AndyMWK/OpticalSensingSystem/cppcheck_report.txt

Firmware/mock/nucleof030r8/ir_sensor_mock/Core/Src/modules/fsm.c:120:23: style: Variable 'ctx.state' is reassigned a value before the old one has been used. [redundantAssignment]
            ctx.state = STATE_STREAMING;
                      ^
Firmware/mock/nucleof030r8/ir_sensor_mock/Core/Src/modules/fsm.c:114:27: note: ctx.state is assigned
                ctx.state = STATE_STREAMING;
                          ^
Firmware/mock/nucleof030r8/ir_sensor_mock/Core/Src/modules/fsm.c:120:23: note: ctx.state is overwritten
            ctx.state = STATE_STREAMING;
                      ^
Firmware/mock/nucleof030r8/ir_sensor_mock/Core/Src/modules/fsm.c:120:23: style: Variable 'ctx.state' is reassigned a value before the old one has been used. [redundantAssignment]
            ctx.state = STATE_STREAMING;
                      ^
Firmware/mock/nucleof030r8/ir_sensor_mock/Core/Src/modules/fsm.c:116:27: note: ctx.state is assigned
                ctx.state = STATE_IDLE;
                          ^
Firmware/mock/nucleof030r8/ir_sensor_mock/Core/Src/modules/fsm.c:120:23: note: ctx.state is overwritten
            ctx.state = STATE_STREAMING;
                      ^
Firmware/mock/nucleof030r8/ir_sensor_mock/Core/Src/system_stm32f0xx.c:191:0: information: Skipping configuration 'HSE_VALUE' since the value of 'HSE_VALUE' is unknown. Use -D if you want to check it. You can use -U to skip it explicitly. [ConfigurationNotChecked]
      SystemCoreClock = HSE_VALUE;
^
Firmware/mock/nucleof030r8/ir_sensor_mock/Core/Src/system_stm32f0xx.c:203:0: information: Skipping configuration 'HSE_VALUE' since the value of 'HSE_VALUE' is unknown. Use -D if you want to check it. You can use -U to skip it explicitly. [ConfigurationNotChecked]
        SystemCoreClock = (HSE_VALUE/predivfactor) * pllmull;
^
Firmware/mock/nucleof030r8/ir_sensor_mock/Core/Src/system_stm32f0xx.c:188:0: information: Skipping configuration 'HSI_VALUE' since the value of 'HSI_VALUE' is unknown. Use -D if you want to check it. You can use -U to skip it explicitly. [ConfigurationNotChecked]
      SystemCoreClock = HSI_VALUE;
^
Firmware/mock/nucleof030r8/ir_sensor_mock/Core/Src/system_stm32f0xx.c:221:0: information: Skipping configuration 'HSI_VALUE' since the value of 'HSI_VALUE' is unknown. Use -D if you want to check it. You can use -U to skip it explicitly. [ConfigurationNotChecked]
        SystemCoreClock = (HSI_VALUE >> 1) * pllmull;
^
Firmware/mock/nucleof030r8/ir_sensor_mock/Core/Src/system_stm32f0xx.c:228:0: information: Skipping configuration 'HSI_VALUE' since the value of 'HSI_VALUE' is unknown. Use -D if you want to check it. You can use -U to skip it explicitly. [ConfigurationNotChecked]
      SystemCoreClock = HSI_VALUE;
^
Firmware/mock/nucleof030r8/ir_sensor_mock/Drivers/CMSIS/Core_A/Source/irq_ctrl_gic.c:132:12: style: The scope of the variable 'val' can be reduced. [variableScope]
  uint32_t val;
           ^
Firmware/mock/nucleof030r8/ir_sensor_mock/Drivers/CMSIS/Core_A/Source/irq_ctrl_gic.c:133:11: style: The scope of the variable 'cfg' can be reduced. [variableScope]
  uint8_t cfg;
          ^
Firmware/mock/nucleof030r8/ir_sensor_mock/Drivers/CMSIS/Core_A/Source/irq_ctrl_gic.c:134:11: style: The scope of the variable 'secure' can be reduced. [variableScope]
  uint8_t secure;
          ^
Firmware/mock/nucleof030r8/ir_sensor_mock/Drivers/CMSIS/Core_A/Source/irq_ctrl_gic.c:135:11: style: The scope of the variable 'cpu' can be reduced. [variableScope]
  uint8_t cpu;
          ^
Firmware/mock/nucleof030r8/ir_sensor_mock/Drivers/CMSIS/Core_A/Source/irq_ctrl_gic.c:203:12: style: The scope of the variable 'val' can be reduced. [variableScope]
  uint32_t val;
           ^
Firmware/mock/nucleof030r8/ir_sensor_mock/Drivers/CMSIS/Core_A/Source/irq_ctrl_gic.c:233:12: style: The scope of the variable 'prio' can be reduced. [variableScope]
  uint32_t prio;
           ^
Firmware/mock/nucleof030r8/ir_sensor_mock/Drivers/CMSIS/DSP/DSP_Lib_TestSuite/Common/JTest/src/jtest_cycle.c:0:0: information: Too many #ifdef configurations - cppcheck only checks 12 of 18 configurations. Use --force to check all configurations. [toomanyconfigs]

^
Firmware/mock/nucleof030r8/ir_sensor_mock/Drivers/CMSIS/DSP/DSP_Lib_TestSuite/Common/JTest/src/jtest_dump_str_segments.c:12:26: style: Variable 'memmove_idx' is assigned a value that is never used. [unreadVariable]
    uint32_t memmove_idx = 0;
                         ^
Firmware/mock/nucleof030r8/ir_sensor_mock/Drivers/CMSIS/DSP/DSP_Lib_TestSuite/Common/JTest/src/jtest_fw.c:0:0: information: Too many #ifdef configurations - cppcheck only checks 12 of 18 configurations. Use --force to check all configurations. [toomanyconfigs]

^
Firmware/mock/nucleof030r8/ir_sensor_mock/Drivers/CMSIS/DSP/DSP_Lib_TestSuite/Common/platform/ARMCC/Retarget.c:24:21: style: struct member '__FILE::handle' is never used. [unusedStructMember]
struct __FILE { int handle; /* Add whatever you need here */ };
                    ^
Firmware/mock/nucleof030r8/ir_sensor_mock/Drivers/CMSIS/DSP/DSP_Lib_TestSuite/Common/platform/GCC/Retarget.c:70:11: style: Condition 'c==0x0D' is always false [knownConditionTrueFalse]
    if (c == 0x0D) break;
          ^
Firmware/mock/nucleof030r8/ir_sensor_mock/Drivers/CMSIS/DSP/DSP_Lib_TestSuite/Common/platform/GCC/Retarget.c:69:20: note: Assignment 'c=SER_GetChar()', assigned value is -1
    c = SER_GetChar();
                   ^
Firmware/mock/nucleof030r8/ir_sensor_mock/Drivers/CMSIS/DSP/DSP_Lib_TestSuite/Common/platform/GCC/Retarget.c:70:11: note: Condition 'c==0x0D' is always false
    if (c == 0x0D) break;
          ^
Firmware/mock/nucleof030r8/ir_sensor_mock/Drivers/CMSIS/DSP/DSP_Lib_TestSuite/Common/platform/GCC/Retarget.c:64:8: style: The scope of the variable 'c' can be reduced. [variableScope]
  char c;
       ^
Firmware/mock/nucleof030r8/ir_sensor_mock/Drivers/CMSIS/DSP/DSP_Lib_TestSuite/Common/platform/GCC/Retarget.c:97:21: error: Comparing pointers that point to different objects [comparePointers]
  if ((heap + incr) > (char *)&__HeapLimit)
                    ^
Firmware/mock/nucleof030r8/ir_sensor_mock/Drivers/CMSIS/DSP/DSP_Lib_TestSuite/Common/platform/GCC/Retarget.c:32:13: note: Variable declared here.
extern int  __HeapBase;
            ^
Firmware/mock/nucleof030r8/ir_sensor_mock/Drivers/CMSIS/DSP/DSP_Lib_TestSuite/Common/platform/GCC/Retarget.c:92:20: note: Address of variable taken here.
    heap = (char *)&__HeapBase;
                   ^
Firmware/mock/nucleof030r8/ir_sensor_mock/Drivers/CMSIS/DSP/DSP_Lib_TestSuite/Common/platform/GCC/Retarget.c:33:13: note: Variable declared here.
extern int  __HeapLimit;
            ^
Firmware/mock/nucleof030r8/ir_sensor_mock/Drivers/CMSIS/DSP/DSP_Lib_TestSuite/Common/platform/GCC/Retarget.c:97:31: note: Address of variable taken here.
  if ((heap + incr) > (char *)&__HeapLimit)
                              ^
Firmware/mock/nucleof030r8/ir_sensor_mock/Drivers/CMSIS/DSP/DSP_Lib_TestSuite/Common/platform/GCC/Retarget.c:97:21: note: Comparing pointers that point to different objects
  if ((heap + incr) > (char *)&__HeapLimit)
                    ^
Firmware/mock/nucleof030r8/ir_sensor_mock/Drivers/CMSIS/DSP/DSP_Lib_TestSuite/Common/platform/system_generic.c:0:0: information: Too many #ifdef configurations - cppcheck only checks 12 of 23 configurations. Use --force to check all configurations. [toomanyconfigs]

^
Firmware/mock/nucleof030r8/ir_sensor_mock/Drivers/CMSIS/DSP/DSP_Lib_TestSuite/Common/src/controller_tests/pid_tests.c:63:1: error: There is an unknown macro here somewhere. Configuration is required. If JTEST_COUNT_CYCLES is a macro then please configure it. [unknownMacro]
ARM_PID_TEST(f32,float32_t);
^
Firmware/mock/nucleof030r8/ir_sensor_mock/Drivers/CMSIS/DSP/DSP_Lib_TestSuite/Common/src/controller_tests/sin_cos_tests.c:88:10: error: There is an unknown macro here somewhere. Configuration is required. If ; is a macro then please configure it. [unknownMacro]
        );
         ^
Firmware/mock/nucleof030r8/ir_sensor_mock/Drivers/CMSIS/DSP/DSP_Lib_TestSuite/Common/src/filtering_tests/biquad_tests.c:135:59: error: There is an unknown macro here somewhere. Configuration is required. If ; is a macro then please configure it. [unknownMacro]
                     (void *) filtering_pState, postShift);
                                                          ^
Firmware/mock/nucleof030r8/ir_sensor_mock/Drivers/CMSIS/DSP/DSP_Lib_TestSuite/Common/src/filtering_tests/conv_tests.c:418:1: error: There is an unknown macro here somewhere. Configuration is required. If ; is a macro then please configure it. [unknownMacro]
CONV_DEFINE_TEST(conv          , f32, float32_t, CONV_TEST_TEMPLATE);
^
Firmware/mock/nucleof030r8/ir_sensor_mock/Drivers/CMSIS/DSP/DSP_Lib_TestSuite/Common/src/filtering_tests/correlate_tests.c:270:1: error: There is an unknown macro here somewhere. Configuration is required. If ; is a macro then please configure it. [unknownMacro]
CORRELATE_DEFINE_TEST(correlate          , f32, float32_t, CORRELATE_TEST_TEMPLATE);
^
Firmware/mock/nucleof030r8/ir_sensor_mock/Drivers/CMSIS/DSP/DSP_Lib_TestSuite/Common/src/filtering_tests/fir_tests.c:342:1: error: There is an unknown macro here somewhere. Configuration is required. If ; is a macro then please configure it. [unknownMacro]
FIR_DEFINE_TEST(f32,,float32_t);
^
Firmware/mock/nucleof030r8/ir_sensor_mock/Drivers/CMSIS/DSP/DSP_Lib_TestSuite/Common/src/filtering_tests/iir_tests.c:60:1: error: There is an unknown macro here somewhere. Configuration is required. If ; is a macro then please configure it. [unknownMacro]
IIR_DEFINE_TEST(f32, float32_t);
^
Firmware/mock/nucleof030r8/ir_sensor_mock/Drivers/CMSIS/DSP/DSP_Lib_TestSuite/Common/src/filtering_tests/lms_tests.c:195:1: error: There is an unknown macro here somewhere. Configuration is required. If ; is a macro then please configure it. [unknownMacro]
LMS_DEFINE_TEST(f32,,float32_t, mu_f32);
^
Firmware/mock/nucleof030r8/ir_sensor_mock/Drivers/CMSIS/DSP/DSP_Lib_TestSuite/Common/src/math_helper.c:62:16: portability: Casting from float * to signed int * is not portable due to different binary data representations on different platforms. [invalidPointerCast]
      test =   (int *)(&pRef[i]);
               ^
Firmware/mock/nucleof030r8/ir_sensor_mock/Drivers/CMSIS/DSP/DSP_Lib_TestSuite/Common/src/math_helper.c:71:16: portability: Casting from float * to signed int * is not portable due to different binary data representations on different platforms. [invalidPointerCast]
      test =   (int *)(&pTest[i]);
               ^
Firmware/mock/nucleof030r8/ir_sensor_mock/Drivers/CMSIS/DSP/DSP_Lib_TestSuite/Common/src/math_helper.c:83:14: portability: Casting from float * to signed int * is not portable due to different binary data representations on different platforms. [invalidPointerCast]
    test =   (int *)(&EnergyError);
             ^
Firmware/mock/nucleof030r8/ir_sensor_mock/Drivers/CMSIS/DSP/DSP_Lib_TestSuite/Common/src/math_helper.c:111:16: portability: Casting from double * to signed int * is not portable due to different binary data representations on different platforms. [invalidPointerCast]
      test =   (int *)(&pRef[i]);
               ^
Firmware/mock/nucleof030r8/ir_sensor_mock/Drivers/CMSIS/DSP/DSP_Lib_TestSuite/Common/src/math_helper.c:120:16: portability: Casting from double * to signed int * is not portable due to different binary data representations on different platforms. [invalidPointerCast]
      test =   (int *)(&pTest[i]);
               ^
Firmware/mock/nucleof030r8/ir_sensor_mock/Drivers/CMSIS/DSP/DSP_Lib_TestSuite/Common/src/math_helper.c:132:14: portability: Casting from double * to signed int * is not portable due to different binary data representations on different platforms. [invalidPointerCast]
    test =   (int *)(&EnergyError);
             ^
Firmware/mock/nucleof030r8/ir_sensor_mock/Drivers/CMSIS/DSP/DSP_Lib_TestSuite/Common/src/math_helper.c:204:11: style: The scope of the variable 'diff' can be reduced. [variableScope]
  int32_t diff, diffCrnt = 0;
          ^
Firmware/mock/nucleof030r8/ir_sensor_mock/Drivers/CMSIS/DSP/DSP_Lib_TestSuite/Common/src/math_helper.c:204:17: style: The scope of the variable 'diffCrnt' can be reduced. [variableScope]
  int32_t diff, diffCrnt = 0;
                ^
Firmware/mock/nucleof030r8/ir_sensor_mock/Drivers/CMSIS/DSP/DSP_Lib_TestSuite/Common/src/math_helper.c:232:11: style: The scope of the variable 'diff' can be reduced. [variableScope]
  int32_t diff, diffCrnt = 0;
          ^
Firmware/mock/nucleof030r8/ir_sensor_mock/Drivers/CMSIS/DSP/DSP_Lib_TestSuite/Common/src/math_helper.c:232:17: style: The scope of the variable 'diffCrnt' can be reduced. [variableScope]
  int32_t diff, diffCrnt = 0;
                ^
Firmware/mock/nucleof030r8/ir_sensor_mock/Drivers/CMSIS/DSP/DSP_Lib_TestSuite/Common/src/math_helper.c:204:26: style: Variable 'diffCrnt' is assigned a value that is never used. [unreadVariable]
  int32_t diff, diffCrnt = 0;
                         ^
Firmware/mock/nucleof030r8/ir_sensor_mock/Drivers/CMSIS/DSP/DSP_Lib_TestSuite/Common/src/math_helper.c:232:26: style: Variable 'diffCrnt' is assigned a value that is never used. [unreadVariable]
  int32_t diff, diffCrnt = 0;
                         ^
Firmware/mock/nucleof030r8/ir_sensor_mock/Drivers/CMSIS/DSP/DSP_Lib_TestSuite/Common/src/matrix_tests/mat_inverse_tests.c:17:40: error: There is an unknown macro here somewhere. Configuration is required. If ; is a macro then please configure it. [unknownMacro]
                 (int)mat_ptr->numCols);
                                       ^
Firmware/mock/nucleof030r8/ir_sensor_mock/Drivers/CMSIS/DSP/DSP_Lib_TestSuite/Common/src/matrix_tests/mat_scale_tests.c:57:79: error: There is an unknown macro here somewhere. Configuration is required. If ; is a macro then please configure it. [unknownMacro]
        MATRIX_TEST_CONFIG_SAMESIZE_OUTPUT(arm_matrix_instance_f32 *, mat_ptr);
                                                                              ^
Firmware/mock/nucleof030r8/ir_sensor_mock/Drivers/CMSIS/DSP/DSP_Lib_TestSuite/Common/src/transform_tests/cfft_family_tests.c:154:1: error: There is an unknown macro here somewhere. Configuration is required. If ; is a macro then please configure it. [unknownMacro]
CFFT_FAMILY_DEFINE_ALL_TESTS(forward, 0U);
^
Firmware/mock/nucleof030r8/ir_sensor_mock/Drivers/CMSIS/DSP/DSP_Lib_TestSuite/Common/src/transform_tests/cfft_tests.c:102:5: error: There is an unknown macro here somewhere. Configuration is required. If ; is a macro then please configure it. [unknownMacro]
    CFFT_TEST_BODY((uint8_t) 0, f32, float32_t);
    ^
Firmware/mock/nucleof030r8/ir_sensor_mock/Drivers/CMSIS/DSP/DSP_Lib_TestSuite/Common/src/transform_tests/dct4_tests.c:184:1: error: There is an unknown macro here somewhere. Configuration is required. If ; is a macro then please configure it. [unknownMacro]
DCT4_DEFINE_TEST(f32, float32_t);
^
Firmware/mock/nucleof030r8/ir_sensor_mock/Drivers/CMSIS/DSP/DSP_Lib_TestSuite/Common/src/transform_tests/rfft_fast_tests.c:64:1: error: There is an unknown macro here somewhere. Configuration is required. If ; is a macro then please configure it. [unknownMacro]
RFFT_FAST_DEFINE_TEST(forward, 0U);
^
Firmware/mock/nucleof030r8/ir_sensor_mock/Drivers/CMSIS/DSP/DSP_Lib_TestSuite/Common/src/transform_tests/rfft_tests.c:77:1: error: There is an unknown macro here somewhere. Configuration is required. If ; is a macro then please configure it. [unknownMacro]
RFFT_DEFINE_TEST(q31, forward, 0U, TYPE_FROM_ABBREV(q31), TYPE_FROM_ABBREV(q31));
^
Firmware/mock/nucleof030r8/ir_sensor_mock/Drivers/CMSIS/DSP/DSP_Lib_TestSuite/RefLibs/src/FilteringFunctions/biquad.c:17:13: style: The scope of the variable 'sample' can be reduced. [variableScope]
   uint32_t sample, stage = S->numStages;         /*  loop counters             */
            ^
Firmware/mock/nucleof030r8/ir_sensor_mock/Drivers/CMSIS/DSP/DSP_Lib_TestSuite/RefLibs/src/FilteringFunctions/biquad.c:87:14: style: The scope of the variable 'sample' can be reduced. [variableScope]
    uint32_t sample, stage = S->numStages;         /*  loop counters             */
             ^
Firmware/mock/nucleof030r8/ir_sensor_mock/Drivers/CMSIS/DSP/DSP_Lib_TestSuite/RefLibs/src/FilteringFunctions/biquad.c:166:13: style: The scope of the variable 'sample' can be reduced. [variableScope]
   uint32_t sample, stage = S->numStages;         /*  loop counters             */
            ^
Firmware/mock/nucleof030r8/ir_sensor_mock/Drivers/CMSIS/DSP/DSP_Lib_TestSuite/RefLibs/src/FilteringFunctions/biquad.c:235:12: style: The scope of the variable 'sample' can be reduced. [variableScope]
  uint32_t sample, stage = S->numStages;         /*  loop counters             */
           ^
Firmware/mock/nucleof030r8/ir_sensor_mock/Drivers/CMSIS/DSP/DSP_Lib_TestSuite/RefLibs/src/FilteringFunctions/biquad.c:319:12: style: The scope of the variable 'sample' can be reduced. [variableScope]
  uint32_t sample, stage = S->numStages;         /*  loop counters                      */
           ^
Firmware/mock/nucleof030r8/ir_sensor_mock/Drivers/CMSIS/DSP/DSP_Lib_TestSuite/RefLibs/src/FilteringFunctions/biquad.c:408:12: style: The scope of the variable 'sample' can be reduced. [variableScope]
  uint32_t sample, stage = S->numStages;         /*  loop counters                 */
           ^
Firmware/mock/nucleof030r8/ir_sensor_mock/Drivers/CMSIS/DSP/DSP_Lib_TestSuite/RefLibs/src/FilteringFunctions/biquad.c:502:12: style: The scope of the variable 'sample' can be reduced. [variableScope]
  uint32_t sample, stage = S->numStages;         /*  loop counters                     */
           ^
Firmware/mock/nucleof030r8/ir_sensor_mock/Drivers/CMSIS/DSP/DSP_Lib_TestSuite/RefLibs/src/FilteringFunctions/biquad.c:580:12: style: The scope of the variable 'sample' can be reduced. [variableScope]
  uint32_t sample, stage = (uint32_t) S->numStages;   /*  Stage loop counter                          */
           ^
Firmware/mock/nucleof030r8/ir_sensor_mock/Drivers/CMSIS/DSP/DSP_Lib_TestSuite/RefLibs/src/FilteringFunctions/biquad.c:655:12: style: The scope of the variable 'sample' can be reduced. [variableScope]
  uint32_t sample, stage = (uint32_t) S->numStages;   /*  Stage loop counter                          */
           ^
Firmware/mock/nucleof030r8/ir_sensor_mock/Drivers/CMSIS/DSP/DSP_Lib_TestSuite/RefLibs/src/FilteringFunctions/fir_interpolate.c:14:12: style: The scope of the variable 'i' can be reduced. [variableScope]
  uint32_t i, blkCnt;                            /* Loop counters */
           ^
Firmware/mock/nucleof030r8/ir_sensor_mock/Drivers/CMSIS/DSP/DSP_Lib_TestSuite/RefLibs/src/FilteringFunctions/fir_interpolate.c:109:12: style: The scope of the variable 'i' can be reduced. [variableScope]
  uint32_t i, blkCnt;                            /* Loop counters */
           ^
Firmware/mock/nucleof030r8/ir_sensor_mock/Drivers/CMSIS/DSP/DSP_Lib_TestSuite/RefLibs/src/FilteringFunctions/fir_lattice.c:11:14: style: The scope of the variable 'px' can be reduced. [variableScope]
  float32_t *px;                                 /* temporary state pointer */
             ^
Firmware/mock/nucleof030r8/ir_sensor_mock/Drivers/CMSIS/DSP/DSP_Lib_TestSuite/RefLibs/src/FilteringFunctions/fir_lattice.c:12:14: style: The scope of the variable 'pk' can be reduced. [variableScope]
  float32_t *pk;                                 /* temporary coefficient pointer */
             ^
Firmware/mock/nucleof030r8/ir_sensor_mock/Drivers/CMSIS/DSP/DSP_Lib_TestSuite/RefLibs/src/FilteringFunctions/fir_lattice.c:15:20: style: The scope of the variable 'stageCnt' can be reduced. [variableScope]
  uint32_t blkCnt, stageCnt;                     /* temporary variables for counts */
                   ^
Firmware/mock/nucleof030r8/ir_sensor_mock/Drivers/CMSIS/DSP/DSP_Lib_TestSuite/RefLibs/src/FilteringFunctions/fir_lattice.c:87:10: style: The scope of the variable 'px' can be reduced. [variableScope]
  q31_t *px;                                     /* temporary state pointer */
         ^
Firmware/mock/nucleof030r8/ir_sensor_mock/Drivers/CMSIS/DSP/DSP_Lib_TestSuite/RefLibs/src/FilteringFunctions/fir_lattice.c:88:10: style: The scope of the variable 'pk' can be reduced. [variableScope]
  q31_t *pk;                                     /* temporary coefficient pointer */
         ^
Firmware/mock/nucleof030r8/ir_sensor_mock/Drivers/CMSIS/DSP/DSP_Lib_TestSuite/RefLibs/src/FilteringFunctions/fir_lattice.c:91:20: style: The scope of the variable 'stageCnt' can be reduced. [variableScope]
  uint32_t blkCnt, stageCnt;                     /* temporary variables for counts */
                   ^
Firmware/mock/nucleof030r8/ir_sensor_mock/Drivers/CMSIS/DSP/DSP_Lib_TestSuite/RefLibs/src/FilteringFunctions/fir_lattice.c:164:10: style: The scope of the variable 'px' can be reduced. [variableScope]
  q15_t *px;                                     /* temporary state pointer */
         ^
Firmware/mock/nucleof030r8/ir_sensor_mock/Drivers/CMSIS/DSP/DSP_Lib_TestSuite/RefLibs/src/FilteringFunctions/fir_lattice.c:165:10: style: The scope of the variable 'pk' can be reduced. [variableScope]
  q15_t *pk;                                     /* temporary coefficient pointer */
         ^
Firmware/mock/nucleof030r8/ir_sensor_mock/Drivers/CMSIS/DSP/DSP_Lib_TestSuite/RefLibs/src/FilteringFunctions/fir_lattice.c:168:20: style: The scope of the variable 'stageCnt' can be reduced. [variableScope]
  uint32_t blkCnt, stageCnt;                     /* temporary variables for counts */
                   ^
Firmware/mock/nucleof030r8/ir_sensor_mock/Drivers/CMSIS/DSP/DSP_Lib_TestSuite/RefLibs/src/FilteringFunctions/fir_sparse.c:303:10: style: Variable 'tapCnt' is reassigned a value before the old one has been used. [redundantAssignment]
  tapCnt = (uint32_t) numTaps - 1U;
         ^
Firmware/mock/nucleof030r8/ir_sensor_mock/Drivers/CMSIS/DSP/DSP_Lib_TestSuite/RefLibs/src/FilteringFunctions/fir_sparse.c:267:10: note: tapCnt is assigned
  tapCnt = numTaps;
         ^
Firmware/mock/nucleof030r8/ir_sensor_mock/Drivers/CMSIS/DSP/DSP_Lib_TestSuite/RefLibs/src/FilteringFunctions/fir_sparse.c:303:10: note: tapCnt is overwritten
  tapCnt = (uint32_t) numTaps - 1U;
         ^
Firmware/mock/nucleof030r8/ir_sensor_mock/Drivers/CMSIS/DSP/DSP_Lib_TestSuite/RefLibs/src/FilteringFunctions/fir_sparse.c:426:10: style: Variable 'tapCnt' is reassigned a value before the old one has been used. [redundantAssignment]
  tapCnt = (uint32_t) numTaps - 1U;
         ^
Firmware/mock/nucleof030r8/ir_sensor_mock/Drivers/CMSIS/DSP/DSP_Lib_TestSuite/RefLibs/src/FilteringFunctions/fir_sparse.c:389:10: note: tapCnt is assigned
  tapCnt = numTaps;
         ^
Firmware/mock/nucleof030r8/ir_sensor_mock/Drivers/CMSIS/DSP/DSP_Lib_TestSuite/RefLibs/src/FilteringFunctions/fir_sparse.c:426:10: note: tapCnt is overwritten
  tapCnt = (uint32_t) numTaps - 1U;
         ^
Firmware/mock/nucleof030r8/ir_sensor_mock/Drivers/CMSIS/DSP/DSP_Lib_TestSuite/RefLibs/src/FilteringFunctions/iir_lattice.c:12:14: style: The scope of the variable 'px1' can be reduced. [variableScope]
  float32_t *px1, *px2, *pk, *pv;                /* temporary pointers for state and coef */
             ^
Firmware/mock/nucleof030r8/ir_sensor_mock/Drivers/CMSIS/DSP/DSP_Lib_TestSuite/RefLibs/src/FilteringFunctions/iir_lattice.c:12:20: style: The scope of the variable 'px2' can be reduced. [variableScope]
  float32_t *px1, *px2, *pk, *pv;                /* temporary pointers for state and coef */
                   ^
Firmware/mock/nucleof030r8/ir_sensor_mock/Drivers/CMSIS/DSP/DSP_Lib_TestSuite/RefLibs/src/FilteringFunctions/iir_lattice.c:12:26: style: The scope of the variable 'pk' can be reduced. [variableScope]
  float32_t *px1, *px2, *pk, *pv;                /* temporary pointers for state and coef */
                         ^
Firmware/mock/nucleof030r8/ir_sensor_mock/Drivers/CMSIS/DSP/DSP_Lib_TestSuite/RefLibs/src/FilteringFunctions/iir_lattice.c:12:31: style: The scope of the variable 'pv' can be reduced. [variableScope]
  float32_t *px1, *px2, *pk, *pv;                /* temporary pointers for state and coef */
                              ^
Firmware/mock/nucleof030r8/ir_sensor_mock/Drivers/CMSIS/DSP/DSP_Lib_TestSuite/RefLibs/src/FilteringFunctions/iir_lattice.c:98:10: style: The scope of the variable 'px1' can be reduced. [variableScope]
  q31_t *px1, *px2, *pk, *pv;                    /* Temporary pointers for state and coef */
         ^
Firmware/mock/nucleof030r8/ir_sensor_mock/Drivers/CMSIS/DSP/DSP_Lib_TestSuite/RefLibs/src/FilteringFunctions/iir_lattice.c:98:16: style: The scope of the variable 'px2' can be reduced. [variableScope]
  q31_t *px1, *px2, *pk, *pv;                    /* Temporary pointers for state and coef */
               ^
Firmware/mock/nucleof030r8/ir_sensor_mock/Drivers/CMSIS/DSP/DSP_Lib_TestSuite/RefLibs/src/FilteringFunctions/iir_lattice.c:98:22: style: The scope of the variable 'pk' can be reduced. [variableScope]
  q31_t *px1, *px2, *pk, *pv;                    /* Temporary pointers for state and coef */
                     ^
Firmware/mock/nucleof030r8/ir_sensor_mock/Drivers/CMSIS/DSP/DSP_Lib_TestSuite/RefLibs/src/FilteringFunctions/iir_lattice.c:98:27: style: The scope of the variable 'pv' can be reduced. [variableScope]
  q31_t *px1, *px2, *pk, *pv;                    /* Temporary pointers for state and coef */
                          ^
Firmware/mock/nucleof030r8/ir_sensor_mock/Drivers/CMSIS/DSP/DSP_Lib_TestSuite/RefLibs/src/FilteringFunctions/iir_lattice.c:190:20: style: The scope of the variable 'tapCnt' can be reduced. [variableScope]
  uint32_t blkCnt, tapCnt;                       /* Temporary variables for counts */
                   ^
Firmware/mock/nucleof030r8/ir_sensor_mock/Drivers/CMSIS/DSP/DSP_Lib_TestSuite/RefLibs/src/FilteringFunctions/iir_lattice.c:191:10: style: The scope of the variable 'px1' can be reduced. [variableScope]
  q15_t *px1, *px2, *pk, *pv;                    /* temporary pointers for state and coef */
         ^
Firmware/mock/nucleof030r8/ir_sensor_mock/Drivers/CMSIS/DSP/DSP_Lib_TestSuite/RefLibs/src/FilteringFunctions/iir_lattice.c:191:16: style: The scope of the variable 'px2' can be reduced. [variableScope]
  q15_t *px1, *px2, *pk, *pv;                    /* temporary pointers for state and coef */
               ^
Firmware/mock/nucleof030r8/ir_sensor_mock/Drivers/CMSIS/DSP/DSP_Lib_TestSuite/RefLibs/src/FilteringFunctions/iir_lattice.c:191:22: style: The scope of the variable 'pk' can be reduced. [variableScope]
  q15_t *px1, *px2, *pk, *pv;                    /* temporary pointers for state and coef */
                     ^
Firmware/mock/nucleof030r8/ir_sensor_mock/Drivers/CMSIS/DSP/DSP_Lib_TestSuite/RefLibs/src/FilteringFunctions/iir_lattice.c:191:27: style: The scope of the variable 'pv' can be reduced. [variableScope]
  q15_t *px1, *px2, *pk, *pv;                    /* temporary pointers for state and coef */
                          ^
Firmware/mock/nucleof030r8/ir_sensor_mock/Drivers/CMSIS/DSP/DSP_Lib_TestSuite/RefLibs/src/FilteringFunctions/iir_lattice.c:95:33: style: Variable 'gcurr' is assigned a value that is never used. [unreadVariable]
  q31_t fcurr, fnext = 0, gcurr = 0, gnext;      /* Temporary variables for lattice stages */
                                ^
Firmware/mock/nucleof030r8/ir_sensor_mock/Drivers/CMSIS/DSP/DSP_Lib_TestSuite/RefLibs/src/FilteringFunctions/iir_lattice.c:187:33: style: Variable 'gcurr' is assigned a value that is never used. [unreadVariable]
  q31_t fcurr, fnext = 0, gcurr = 0, gnext;      /* Temporary variables for lattice stages */
                                ^
Firmware/mock/nucleof030r8/ir_sensor_mock/Drivers/CMSIS/DSP/DSP_Lib_TestSuite/RefLibs/src/FilteringFunctions/lms.c:173:10: style: The scope of the variable 'px' can be reduced. [variableScope]
  q31_t *px;                                     /* Temporary pointer for state */
         ^
Firmware/mock/nucleof030r8/ir_sensor_mock/Drivers/CMSIS/DSP/DSP_Lib_TestSuite/RefLibs/src/FilteringFunctions/lms.c:174:10: style: The scope of the variable 'pb' can be reduced. [variableScope]
  q31_t *pb;                                     /* Temporary pointer for coefficient buffer */
         ^
Firmware/mock/nucleof030r8/ir_sensor_mock/Drivers/CMSIS/DSP/DSP_Lib_TestSuite/RefLibs/src/FilteringFunctions/lms.c:287:10: style: The scope of the variable 'px' can be reduced. [variableScope]
  q31_t *px, *pb;                                /* Temporary pointers for state and coefficient buffers */
         ^
Firmware/mock/nucleof030r8/ir_sensor_mock/Drivers/CMSIS/DSP/DSP_Lib_TestSuite/RefLibs/src/FilteringFunctions/lms.c:287:15: style: The scope of the variable 'pb' can be reduced. [variableScope]
  q31_t *px, *pb;                                /* Temporary pointers for state and coefficient buffers */
              ^
Firmware/mock/nucleof030r8/ir_sensor_mock/Drivers/CMSIS/DSP/DSP_Lib_TestSuite/RefLibs/src/FilteringFunctions/lms.c:433:10: style: The scope of the variable 'px' can be reduced. [variableScope]
  q15_t *px;                                     /* Temporary pointer for state */
         ^
Firmware/mock/nucleof030r8/ir_sensor_mock/Drivers/CMSIS/DSP/DSP_Lib_TestSuite/RefLibs/src/FilteringFunctions/lms.c:434:10: style: The scope of the variable 'pb' can be reduced. [variableScope]
  q15_t *pb;                                     /* Temporary pointer for coefficient buffer */
         ^
Firmware/mock/nucleof030r8/ir_sensor_mock/Drivers/CMSIS/DSP/DSP_Lib_TestSuite/RefLibs/src/FilteringFunctions/lms.c:18:15: style: Variable 'w' is assigned a value that is never used. [unreadVariable]
  float32_t w = 0.0f;                            /* weight factor */
              ^
Firmware/mock/nucleof030r8/ir_sensor_mock/Drivers/CMSIS/DSP/DSP_Lib_TestSuite/RefLibs/src/FilteringFunctions/lms.c:20:5: style: Variable 'e' is assigned a value that is never used. [unreadVariable]
  e = 0.0f;
    ^
Firmware/mock/nucleof030r8/ir_sensor_mock/Drivers/CMSIS/DSP/DSP_Lib_TestSuite/RefLibs/src/FilteringFunctions/lms.c:21:5: style: Variable 'd' is assigned a value that is never used. [unreadVariable]
  d = 0.0f;
    ^
Firmware/mock/nucleof030r8/ir_sensor_mock/Drivers/CMSIS/DSP/DSP_Lib_TestSuite/RefLibs/src/FilteringFunctions/lms.c:93:5: style: Variable 'e' is assigned a value that is never used. [unreadVariable]
  e = 0.0f;
    ^
Firmware/mock/nucleof030r8/ir_sensor_mock/Drivers/CMSIS/DSP/DSP_Lib_TestSuite/RefLibs/src/FilteringFunctions/lms.c:94:5: style: Variable 'd' is assigned a value that is never used. [unreadVariable]
  d = 0.0f;
    ^
Firmware/mock/nucleof030r8/ir_sensor_mock/Drivers/CMSIS/DSP/DSP_Lib_TestSuite/RefLibs/src/FilteringFunctions/lms.c:95:5: style: Variable 'w' is assigned a value that is never used. [unreadVariable]
  w = 0.0f;
    ^
Firmware/mock/nucleof030r8/ir_sensor_mock/Drivers/CMSIS/DSP/DSP_Lib_TestSuite/RefLibs/src/FilteringFunctions/lms.c:177:11: style: Variable 'e' is assigned a value that is never used. [unreadVariable]
  q31_t e = 0;                                   /* error of data sample */
          ^
Firmware/mock/nucleof030r8/ir_sensor_mock/Drivers/CMSIS/DSP/DSP_Lib_TestSuite/RefLibs/src/FilteringFunctions/lms.c:293:11: style: Variable 'e' is assigned a value that is never used. [unreadVariable]
  q31_t e = 0, d = 0;                            /* error, reference data sample */
          ^
Firmware/mock/nucleof030r8/ir_sensor_mock/Drivers/CMSIS/DSP/DSP_Lib_TestSuite/RefLibs/src/FilteringFunctions/lms.c:293:18: style: Variable 'd' is assigned a value that is never used. [unreadVariable]
  q31_t e = 0, d = 0;                            /* error, reference data sample */
                 ^
Firmware/mock/nucleof030r8/ir_sensor_mock/Drivers/CMSIS/DSP/DSP_Lib_TestSuite/RefLibs/src/FilteringFunctions/lms.c:294:11: style: Variable 'w' is assigned a value that is never used. [unreadVariable]
  q31_t w = 0, in;                               /* weight factor and state */
          ^
Firmware/mock/nucleof030r8/ir_sensor_mock/Drivers/CMSIS/DSP/DSP_Lib_TestSuite/RefLibs/src/FilteringFunctions/lms.c:437:11: style: Variable 'e' is assigned a value that is never used. [unreadVariable]
  q15_t e = 0;                                   /* error of data sample */
          ^
Firmware/mock/nucleof030r8/ir_sensor_mock/Drivers/CMSIS/DSP/DSP_Lib_TestSuite/RefLibs/src/FilteringFunctions/lms.c:555:11: style: Variable 'e' is assigned a value that is never used. [unreadVariable]
  q15_t e = 0, d = 0;                            /* error, reference data sample */
          ^
Firmware/mock/nucleof030r8/ir_sensor_mock/Drivers/CMSIS/DSP/DSP_Lib_TestSuite/RefLibs/src/FilteringFunctions/lms.c:555:18: style: Variable 'd' is assigned a value that is never used. [unreadVariable]
  q15_t e = 0, d = 0;                            /* error, reference data sample */
                 ^
Firmware/mock/nucleof030r8/ir_sensor_mock/Drivers/CMSIS/DSP/DSP_Lib_TestSuite/RefLibs/src/FilteringFunctions/lms.c:556:11: style: Variable 'w' is assigned a value that is never used. [unreadVariable]
  q15_t w = 0, in;                               /* weight factor and state */
          ^
Firmware/mock/nucleof030r8/ir_sensor_mock/Drivers/CMSIS/DSP/DSP_Lib_TestSuite/RefLibs/src/HelperFunctions/mat_helper.c:6:8: style: The scope of the variable 'i' can be reduced. [variableScope]
   int i, j, m, n, c;
       ^
Firmware/mock/nucleof030r8/ir_sensor_mock/Drivers/CMSIS/DSP/DSP_Lib_TestSuite/RefLibs/src/HelperFunctions/mat_helper.c:6:11: style: The scope of the variable 'j' can be reduced. [variableScope]
   int i, j, m, n, c;
          ^
Firmware/mock/nucleof030r8/ir_sensor_mock/Drivers/CMSIS/DSP/DSP_Lib_TestSuite/RefLibs/src/HelperFunctions/mat_helper.c:6:14: style: The scope of the variable 'm' can be reduced. [variableScope]
   int i, j, m, n, c;
             ^
Firmware/mock/nucleof030r8/ir_sensor_mock/Drivers/CMSIS/DSP/DSP_Lib_TestSuite/RefLibs/src/HelperFunctions/mat_helper.c:6:17: style: The scope of the variable 'n' can be reduced. [variableScope]
   int i, j, m, n, c;
                ^
Firmware/mock/nucleof030r8/ir_sensor_mock/Drivers/CMSIS/DSP/DSP_Lib_TestSuite/RefLibs/src/HelperFunctions/mat_helper.c:6:20: style: The scope of the variable 'c' can be reduced. [variableScope]
   int i, j, m, n, c;
                   ^
Firmware/mock/nucleof030r8/ir_sensor_mock/Drivers/CMSIS/DSP/DSP_Lib_TestSuite/RefLibs/src/HelperFunctions/mat_helper.c:103:8: style: The scope of the variable 'i' can be reduced. [variableScope]
   int i, j, m, n, c;
       ^
Firmware/mock/nucleof030r8/ir_sensor_mock/Drivers/CMSIS/DSP/DSP_Lib_TestSuite/RefLibs/src/HelperFunctions/mat_helper.c:103:11: style: The scope of the variable 'j' can be reduced. [variableScope]
   int i, j, m, n, c;
          ^
Firmware/mock/nucleof030r8/ir_sensor_mock/Drivers/CMSIS/DSP/DSP_Lib_TestSuite/RefLibs/src/HelperFunctions/mat_helper.c:103:14: style: The scope of the variable 'm' can be reduced. [variableScope]
   int i, j, m, n, c;
             ^
Firmware/mock/nucleof030r8/ir_sensor_mock/Drivers/CMSIS/DSP/DSP_Lib_TestSuite/RefLibs/src/HelperFunctions/mat_helper.c:103:17: style: The scope of the variable 'n' can be reduced. [variableScope]
   int i, j, m, n, c;
                ^
Firmware/mock/nucleof030r8/ir_sensor_mock/Drivers/CMSIS/DSP/DSP_Lib_TestSuite/RefLibs/src/HelperFunctions/mat_helper.c:103:20: style: The scope of the variable 'c' can be reduced. [variableScope]
   int i, j, m, n, c;
                   ^
Firmware/mock/nucleof030r8/ir_sensor_mock/Drivers/CMSIS/DSP/DSP_Lib_TestSuite/RefLibs/src/HelperFunctions/ref_helper.c:9:18: style: The scope of the variable 'negMin' can be reduced. [variableScope]
 int32_t posMax, negMin;
                 ^
Firmware/mock/nucleof030r8/ir_sensor_mock/Drivers/CMSIS/DSP/DSP_Lib_TestSuite/RefLibs/src/StatisticsFunctions/rms.c:40:11: portability: Casting from float * to signed int * is not portable due to different binary data representations on different platforms. [invalidPointerCast]
  if (((*((int *)(&help_float))) & 0x7FC00000) == 0x7FC00000) {
          ^
Firmware/mock/nucleof030r8/ir_sensor_mock/Drivers/CMSIS/DSP/DSP_Lib_TestSuite/RefLibs/src/TransformFunctions/bitreversal.c:13:11: style: The scope of the variable 'a' can be reduced. [variableScope]
 uint32_t a,b,i,tmp;
          ^
Firmware/mock/nucleof030r8/ir_sensor_mock/Drivers/CMSIS/DSP/DSP_Lib_TestSuite/RefLibs/src/TransformFunctions/bitreversal.c:13:13: style: The scope of the variable 'b' can be reduced. [variableScope]
 uint32_t a,b,i,tmp;
            ^
Firmware/mock/nucleof030r8/ir_sensor_mock/Drivers/CMSIS/DSP/DSP_Lib_TestSuite/RefLibs/src/TransformFunctions/bitreversal.c:13:17: style: The scope of the variable 'tmp' can be reduced. [variableScope]
 uint32_t a,b,i,tmp;
                ^
Firmware/mock/nucleof030r8/ir_sensor_mock/Drivers/CMSIS/DSP/DSP_Lib_TestSuite/RefLibs/src/TransformFunctions/cfft.c:10:21: style: The scope of the variable 'istep' can be reduced. [variableScope]
 int n, mmax, m, j, istep, i;
                    ^
Firmware/mock/nucleof030r8/ir_sensor_mock/Drivers/CMSIS/DSP/DSP_Lib_TestSuite/RefLibs/src/TransformFunctions/rfft.c:61:13: style: The scope of the variable 'j' can be reduced. [variableScope]
 uint32_t i,j;
            ^
Firmware/mock/nucleof030r8/ir_sensor_mock/Drivers/CMSIS/DSP/Examples/ARM/arm_convolution_example/arm_convolution_example_f32.c:223:10: style: Variable 'status' is reassigned a value before the old one has been used. [redundantAssignment]
  status = arm_cfft_radix4_init_f32(cfft_instance_ptr, 64, 1, 1);
         ^
Firmware/mock/nucleof030r8/ir_sensor_mock/Drivers/CMSIS/DSP/Examples/ARM/arm_convolution_example/arm_convolution_example_f32.c:212:10: note: status is assigned
  status = arm_cfft_radix4_init_f32(cfft_instance_ptr, 64, 0, 1);
         ^
Firmware/mock/nucleof030r8/ir_sensor_mock/Drivers/CMSIS/DSP/Examples/ARM/arm_convolution_example/arm_convolution_example_f32.c:223:10: note: status is overwritten
  status = arm_cfft_radix4_init_f32(cfft_instance_ptr, 64, 1, 1);
         ^
Firmware/mock/nucleof030r8/ir_sensor_mock/Drivers/CMSIS/DSP/Examples/ARM/arm_convolution_example/math_helper.c:73:13: portability: Casting from float * to signed int * is not portable due to different binary data representations on different platforms. [invalidPointerCast]
   test =   (int *)(&pRef[i]);
            ^
Firmware/mock/nucleof030r8/ir_sensor_mock/Drivers/CMSIS/DSP/Examples/ARM/arm_convolution_example/math_helper.c:82:13: portability: Casting from float * to signed int * is not portable due to different binary data representations on different platforms. [invalidPointerCast]
   test =   (int *)(&pTest[i]);
            ^
Firmware/mock/nucleof030r8/ir_sensor_mock/Drivers/CMSIS/DSP/Examples/ARM/arm_convolution_example/math_helper.c:94:11: portability: Casting from float * to signed int * is not portable due to different binary data representations on different platforms. [invalidPointerCast]
 test =   (int *)(&EnergyError);
          ^
Firmware/mock/nucleof030r8/ir_sensor_mock/Drivers/CMSIS/DSP/Examples/ARM/arm_convolution_example/math_helper.c:169:11: style: The scope of the variable 'diff' can be reduced. [variableScope]
  int32_t diff, diffCrnt = 0;
          ^
Firmware/mock/nucleof030r8/ir_sensor_mock/Drivers/CMSIS/DSP/Examples/ARM/arm_convolution_example/math_helper.c:169:17: style: The scope of the variable 'diffCrnt' can be reduced. [variableScope]
  int32_t diff, diffCrnt = 0;
                ^
Firmware/mock/nucleof030r8/ir_sensor_mock/Drivers/CMSIS/DSP/Examples/ARM/arm_convolution_example/math_helper.c:197:11: style: The scope of the variable 'diff' can be reduced. [variableScope]
  int32_t diff, diffCrnt = 0;
          ^
Firmware/mock/nucleof030r8/ir_sensor_mock/Drivers/CMSIS/DSP/Examples/ARM/arm_convolution_example/math_helper.c:197:17: style: The scope of the variable 'diffCrnt' can be reduced. [variableScope]
  int32_t diff, diffCrnt = 0;
                ^
Firmware/mock/nucleof030r8/ir_sensor_mock/Drivers/CMSIS/DSP/Examples/ARM/arm_convolution_example/math_helper.c:311:33: style:inconclusive: Function 'arm_calc_2pow' argument 1 names different: declaration 'guard_bits' definition 'numShifts'. [funcArgNamesDifferent]
uint32_t arm_calc_2pow(uint32_t numShifts)
                                ^
Firmware/mock/nucleof030r8/ir_sensor_mock/Drivers/CMSIS/DSP/Examples/ARM/arm_convolution_example/math_helper.h:61:33: note: Function 'arm_calc_2pow' argument 1 names different: declaration 'guard_bits' definition 'numShifts'.
uint32_t arm_calc_2pow(uint32_t guard_bits);
                                ^
Firmware/mock/nucleof030r8/ir_sensor_mock/Drivers/CMSIS/DSP/Examples/ARM/arm_convolution_example/math_helper.c:311:33: note: Function 'arm_calc_2pow' argument 1 names different: declaration 'guard_bits' definition 'numShifts'.
uint32_t arm_calc_2pow(uint32_t numShifts)
                                ^
Firmware/mock/nucleof030r8/ir_sensor_mock/Drivers/CMSIS/DSP/Examples/ARM/arm_convolution_example/math_helper.c:169:26: style: Variable 'diffCrnt' is assigned a value that is never used. [unreadVariable]
  int32_t diff, diffCrnt = 0;
                         ^
Firmware/mock/nucleof030r8/ir_sensor_mock/Drivers/CMSIS/DSP/Examples/ARM/arm_convolution_example/math_helper.c:197:26: style: Variable 'diffCrnt' is assigned a value that is never used. [unreadVariable]
  int32_t diff, diffCrnt = 0;
                         ^
Firmware/mock/nucleof030r8/ir_sensor_mock/Drivers/CMSIS/DSP/Examples/ARM/arm_fir_example/math_helper.c:73:13: portability: Casting from float * to signed int * is not portable due to different binary data representations on different platforms. [invalidPointerCast]
   test =   (int *)(&pRef[i]);
            ^
Firmware/mock/nucleof030r8/ir_sensor_mock/Drivers/CMSIS/DSP/Examples/ARM/arm_fir_example/math_helper.c:82:13: portability: Casting from float * to signed int * is not portable due to different binary data representations on different platforms. [invalidPointerCast]
   test =   (int *)(&pTest[i]);
            ^
Firmware/mock/nucleof030r8/ir_sensor_mock/Drivers/CMSIS/DSP/Examples/ARM/arm_fir_example/math_helper.c:94:11: portability: Casting from float * to signed int * is not portable due to different binary data representations on different platforms. [invalidPointerCast]
 test =   (int *)(&EnergyError);
          ^
Firmware/mock/nucleof030r8/ir_sensor_mock/Drivers/CMSIS/DSP/Examples/ARM/arm_fir_example/math_helper.c:169:11: style: The scope of the variable 'diff' can be reduced. [variableScope]
  int32_t diff, diffCrnt = 0;
          ^
Firmware/mock/nucleof030r8/ir_sensor_mock/Drivers/CMSIS/DSP/Examples/ARM/arm_fir_example/math_helper.c:169:17: style: The scope of the variable 'diffCrnt' can be reduced. [variableScope]
  int32_t diff, diffCrnt = 0;
                ^
Firmware/mock/nucleof030r8/ir_sensor_mock/Drivers/CMSIS/DSP/Examples/ARM/arm_fir_example/math_helper.c:197:11: style: The scope of the variable 'diff' can be reduced. [variableScope]
  int32_t diff, diffCrnt = 0;
          ^
Firmware/mock/nucleof030r8/ir_sensor_mock/Drivers/CMSIS/DSP/Examples/ARM/arm_fir_example/math_helper.c:197:17: style: The scope of the variable 'diffCrnt' can be reduced. [variableScope]
  int32_t diff, diffCrnt = 0;
                ^
Firmware/mock/nucleof030r8/ir_sensor_mock/Drivers/CMSIS/DSP/Examples/ARM/arm_fir_example/math_helper.c:311:33: style:inconclusive: Function 'arm_calc_2pow' argument 1 names different: declaration 'guard_bits' definition 'numShifts'. [funcArgNamesDifferent]
uint32_t arm_calc_2pow(uint32_t numShifts)
                                ^
Firmware/mock/nucleof030r8/ir_sensor_mock/Drivers/CMSIS/DSP/Examples/ARM/arm_fir_example/math_helper.h:61:33: note: Function 'arm_calc_2pow' argument 1 names different: declaration 'guard_bits' definition 'numShifts'.
uint32_t arm_calc_2pow(uint32_t guard_bits);
                                ^
Firmware/mock/nucleof030r8/ir_sensor_mock/Drivers/CMSIS/DSP/Examples/ARM/arm_fir_example/math_helper.c:311:33: note: Function 'arm_calc_2pow' argument 1 names different: declaration 'guard_bits' definition 'numShifts'.
uint32_t arm_calc_2pow(uint32_t numShifts)
                                ^
Firmware/mock/nucleof030r8/ir_sensor_mock/Drivers/CMSIS/DSP/Examples/ARM/arm_fir_example/math_helper.c:169:26: style: Variable 'diffCrnt' is assigned a value that is never used. [unreadVariable]
  int32_t diff, diffCrnt = 0;
                         ^
Firmware/mock/nucleof030r8/ir_sensor_mock/Drivers/CMSIS/DSP/Examples/ARM/arm_fir_example/math_helper.c:197:26: style: Variable 'diffCrnt' is assigned a value that is never used. [unreadVariable]
  int32_t diff, diffCrnt = 0;
                         ^
Firmware/mock/nucleof030r8/ir_sensor_mock/Drivers/CMSIS/DSP/Examples/ARM/arm_graphic_equalizer_example/math_helper.c:73:13: portability: Casting from float * to signed int * is not portable due to different binary data representations on different platforms. [invalidPointerCast]
   test =   (int *)(&pRef[i]);
            ^
Firmware/mock/nucleof030r8/ir_sensor_mock/Drivers/CMSIS/DSP/Examples/ARM/arm_graphic_equalizer_example/math_helper.c:82:13: portability: Casting from float * to signed int * is not portable due to different binary data representations on different platforms. [invalidPointerCast]
   test =   (int *)(&pTest[i]);
            ^
Firmware/mock/nucleof030r8/ir_sensor_mock/Drivers/CMSIS/DSP/Examples/ARM/arm_graphic_equalizer_example/math_helper.c:94:11: portability: Casting from float * to signed int * is not portable due to different binary data representations on different platforms. [invalidPointerCast]
 test =   (int *)(&EnergyError);
          ^
Firmware/mock/nucleof030r8/ir_sensor_mock/Drivers/CMSIS/DSP/Examples/ARM/arm_graphic_equalizer_example/math_helper.c:169:11: style: The scope of the variable 'diff' can be reduced. [variableScope]
  int32_t diff, diffCrnt = 0;
          ^
Firmware/mock/nucleof030r8/ir_sensor_mock/Drivers/CMSIS/DSP/Examples/ARM/arm_graphic_equalizer_example/math_helper.c:169:17: style: The scope of the variable 'diffCrnt' can be reduced. [variableScope]
  int32_t diff, diffCrnt = 0;
                ^
Firmware/mock/nucleof030r8/ir_sensor_mock/Drivers/CMSIS/DSP/Examples/ARM/arm_graphic_equalizer_example/math_helper.c:197:11: style: The scope of the variable 'diff' can be reduced. [variableScope]
  int32_t diff, diffCrnt = 0;
          ^
Firmware/mock/nucleof030r8/ir_sensor_mock/Drivers/CMSIS/DSP/Examples/ARM/arm_graphic_equalizer_example/math_helper.c:197:17: style: The scope of the variable 'diffCrnt' can be reduced. [variableScope]
  int32_t diff, diffCrnt = 0;
                ^
Firmware/mock/nucleof030r8/ir_sensor_mock/Drivers/CMSIS/DSP/Examples/ARM/arm_graphic_equalizer_example/math_helper.c:311:33: style:inconclusive: Function 'arm_calc_2pow' argument 1 names different: declaration 'guard_bits' definition 'numShifts'. [funcArgNamesDifferent]
uint32_t arm_calc_2pow(uint32_t numShifts)
                                ^
Firmware/mock/nucleof030r8/ir_sensor_mock/Drivers/CMSIS/DSP/Examples/ARM/arm_graphic_equalizer_example/math_helper.h:61:33: note: Function 'arm_calc_2pow' argument 1 names different: declaration 'guard_bits' definition 'numShifts'.
uint32_t arm_calc_2pow(uint32_t guard_bits);
                                ^
Firmware/mock/nucleof030r8/ir_sensor_mock/Drivers/CMSIS/DSP/Examples/ARM/arm_graphic_equalizer_example/math_helper.c:311:33: note: Function 'arm_calc_2pow' argument 1 names different: declaration 'guard_bits' definition 'numShifts'.
uint32_t arm_calc_2pow(uint32_t numShifts)
                                ^
Firmware/mock/nucleof030r8/ir_sensor_mock/Drivers/CMSIS/DSP/Examples/ARM/arm_graphic_equalizer_example/math_helper.c:169:26: style: Variable 'diffCrnt' is assigned a value that is never used. [unreadVariable]
  int32_t diff, diffCrnt = 0;
                         ^
Firmware/mock/nucleof030r8/ir_sensor_mock/Drivers/CMSIS/DSP/Examples/ARM/arm_graphic_equalizer_example/math_helper.c:197:26: style: Variable 'diffCrnt' is assigned a value that is never used. [unreadVariable]
  int32_t diff, diffCrnt = 0;
                         ^
Firmware/mock/nucleof030r8/ir_sensor_mock/Drivers/CMSIS/DSP/Examples/ARM/arm_linear_interp_example/math_helper.c:73:13: portability: Casting from float * to signed int * is not portable due to different binary data representations on different platforms. [invalidPointerCast]
   test =   (int *)(&pRef[i]);
            ^
Firmware/mock/nucleof030r8/ir_sensor_mock/Drivers/CMSIS/DSP/Examples/ARM/arm_linear_interp_example/math_helper.c:82:13: portability: Casting from float * to signed int * is not portable due to different binary data representations on different platforms. [invalidPointerCast]
   test =   (int *)(&pTest[i]);
            ^
Firmware/mock/nucleof030r8/ir_sensor_mock/Drivers/CMSIS/DSP/Examples/ARM/arm_linear_interp_example/math_helper.c:94:11: portability: Casting from float * to signed int * is not portable due to different binary data representations on different platforms. [invalidPointerCast]
 test =   (int *)(&EnergyError);
          ^
Firmware/mock/nucleof030r8/ir_sensor_mock/Drivers/CMSIS/DSP/Examples/ARM/arm_linear_interp_example/math_helper.c:169:11: style: The scope of the variable 'diff' can be reduced. [variableScope]
  int32_t diff, diffCrnt = 0;
          ^
Firmware/mock/nucleof030r8/ir_sensor_mock/Drivers/CMSIS/DSP/Examples/ARM/arm_linear_interp_example/math_helper.c:169:17: style: The scope of the variable 'diffCrnt' can be reduced. [variableScope]
  int32_t diff, diffCrnt = 0;
                ^
Firmware/mock/nucleof030r8/ir_sensor_mock/Drivers/CMSIS/DSP/Examples/ARM/arm_linear_interp_example/math_helper.c:197:11: style: The scope of the variable 'diff' can be reduced. [variableScope]
  int32_t diff, diffCrnt = 0;
          ^
Firmware/mock/nucleof030r8/ir_sensor_mock/Drivers/CMSIS/DSP/Examples/ARM/arm_linear_interp_example/math_helper.c:197:17: style: The scope of the variable 'diffCrnt' can be reduced. [variableScope]
  int32_t diff, diffCrnt = 0;
                ^
Firmware/mock/nucleof030r8/ir_sensor_mock/Drivers/CMSIS/DSP/Examples/ARM/arm_linear_interp_example/math_helper.c:311:33: style:inconclusive: Function 'arm_calc_2pow' argument 1 names different: declaration 'guard_bits' definition 'numShifts'. [funcArgNamesDifferent]
uint32_t arm_calc_2pow(uint32_t numShifts)
                                ^
Firmware/mock/nucleof030r8/ir_sensor_mock/Drivers/CMSIS/DSP/Examples/ARM/arm_linear_interp_example/math_helper.h:61:33: note: Function 'arm_calc_2pow' argument 1 names different: declaration 'guard_bits' definition 'numShifts'.
uint32_t arm_calc_2pow(uint32_t guard_bits);
                                ^
Firmware/mock/nucleof030r8/ir_sensor_mock/Drivers/CMSIS/DSP/Examples/ARM/arm_linear_interp_example/math_helper.c:311:33: note: Function 'arm_calc_2pow' argument 1 names different: declaration 'guard_bits' definition 'numShifts'.
uint32_t arm_calc_2pow(uint32_t numShifts)
                                ^
Firmware/mock/nucleof030r8/ir_sensor_mock/Drivers/CMSIS/DSP/Examples/ARM/arm_linear_interp_example/math_helper.c:169:26: style: Variable 'diffCrnt' is assigned a value that is never used. [unreadVariable]
  int32_t diff, diffCrnt = 0;
                         ^
Firmware/mock/nucleof030r8/ir_sensor_mock/Drivers/CMSIS/DSP/Examples/ARM/arm_linear_interp_example/math_helper.c:197:26: style: Variable 'diffCrnt' is assigned a value that is never used. [unreadVariable]
  int32_t diff, diffCrnt = 0;
                         ^
Firmware/mock/nucleof030r8/ir_sensor_mock/Drivers/CMSIS/DSP/Examples/ARM/arm_matrix_example/arm_matrix_example_f32.c:179:10: style: Variable 'status' is reassigned a value before the old one has been used. [redundantAssignment]
  status = arm_mat_mult_f32(&AT, &A, &ATMA);
         ^
Firmware/mock/nucleof030r8/ir_sensor_mock/Drivers/CMSIS/DSP/Examples/ARM/arm_matrix_example/arm_matrix_example_f32.c:170:10: note: status is assigned
  status = arm_mat_trans_f32(&A, &AT);
         ^
Firmware/mock/nucleof030r8/ir_sensor_mock/Drivers/CMSIS/DSP/Examples/ARM/arm_matrix_example/arm_matrix_example_f32.c:179:10: note: status is overwritten
  status = arm_mat_mult_f32(&AT, &A, &ATMA);
         ^
Firmware/mock/nucleof030r8/ir_sensor_mock/Drivers/CMSIS/DSP/Examples/ARM/arm_matrix_example/arm_matrix_example_f32.c:187:10: style: Variable 'status' is reassigned a value before the old one has been used. [redundantAssignment]
  status = arm_mat_inverse_f32(&ATMA, &ATMAI);
         ^
Firmware/mock/nucleof030r8/ir_sensor_mock/Drivers/CMSIS/DSP/Examples/ARM/arm_matrix_example/arm_matrix_example_f32.c:179:10: note: status is assigned
  status = arm_mat_mult_f32(&AT, &A, &ATMA);
         ^
Firmware/mock/nucleof030r8/ir_sensor_mock/Drivers/CMSIS/DSP/Examples/ARM/arm_matrix_example/arm_matrix_example_f32.c:187:10: note: status is overwritten
  status = arm_mat_inverse_f32(&ATMA, &ATMAI);
         ^
Firmware/mock/nucleof030r8/ir_sensor_mock/Drivers/CMSIS/DSP/Examples/ARM/arm_matrix_example/arm_matrix_example_f32.c:190:10: style: Variable 'status' is reassigned a value before the old one has been used. [redundantAssignment]
  status = arm_mat_mult_f32(&ATMAI, &AT, &ATMA);
         ^
Firmware/mock/nucleof030r8/ir_sensor_mock/Drivers/CMSIS/DSP/Examples/ARM/arm_matrix_example/arm_matrix_example_f32.c:187:10: note: status is assigned
  status = arm_mat_inverse_f32(&ATMA, &ATMAI);
         ^
Firmware/mock/nucleof030r8/ir_sensor_mock/Drivers/CMSIS/DSP/Examples/ARM/arm_matrix_example/arm_matrix_example_f32.c:190:10: note: status is overwritten
  status = arm_mat_mult_f32(&ATMAI, &AT, &ATMA);
         ^
Firmware/mock/nucleof030r8/ir_sensor_mock/Drivers/CMSIS/DSP/Examples/ARM/arm_matrix_example/arm_matrix_example_f32.c:203:10: style: Variable 'status' is reassigned a value before the old one has been used. [redundantAssignment]
  status = arm_mat_mult_f32(&ATMA, &B, &X);
         ^
Firmware/mock/nucleof030r8/ir_sensor_mock/Drivers/CMSIS/DSP/Examples/ARM/arm_matrix_example/arm_matrix_example_f32.c:190:10: note: status is assigned
  status = arm_mat_mult_f32(&ATMAI, &AT, &ATMA);
         ^
Firmware/mock/nucleof030r8/ir_sensor_mock/Drivers/CMSIS/DSP/Examples/ARM/arm_matrix_example/arm_matrix_example_f32.c:203:10: note: status is overwritten
  status = arm_mat_mult_f32(&ATMA, &B, &X);
         ^
Firmware/mock/nucleof030r8/ir_sensor_mock/Drivers/CMSIS/DSP/Examples/ARM/arm_matrix_example/arm_matrix_example_f32.c:213:12: style: Variable 'status' is reassigned a value before the old one has been used. [redundantAssignment]
    status = ARM_MATH_SUCCESS;
           ^
Firmware/mock/nucleof030r8/ir_sensor_mock/Drivers/CMSIS/DSP/Examples/ARM/arm_matrix_example/arm_matrix_example_f32.c:203:10: note: status is assigned
  status = arm_mat_mult_f32(&ATMA, &B, &X);
         ^
Firmware/mock/nucleof030r8/ir_sensor_mock/Drivers/CMSIS/DSP/Examples/ARM/arm_matrix_example/arm_matrix_example_f32.c:213:12: note: status is overwritten
    status = ARM_MATH_SUCCESS;
           ^
Firmware/mock/nucleof030r8/ir_sensor_mock/Drivers/CMSIS/DSP/Examples/ARM/arm_matrix_example/math_helper.c:73:13: portability: Casting from float * to signed int * is not portable due to different binary data representations on different platforms. [invalidPointerCast]
   test =   (int *)(&pRef[i]);
            ^
Firmware/mock/nucleof030r8/ir_sensor_mock/Drivers/CMSIS/DSP/Examples/ARM/arm_matrix_example/math_helper.c:82:13: portability: Casting from float * to signed int * is not portable due to different binary data representations on different platforms. [invalidPointerCast]
   test =   (int *)(&pTest[i]);
            ^
Firmware/mock/nucleof030r8/ir_sensor_mock/Drivers/CMSIS/DSP/Examples/ARM/arm_matrix_example/math_helper.c:94:11: portability: Casting from float * to signed int * is not portable due to different binary data representations on different platforms. [invalidPointerCast]
 test =   (int *)(&EnergyError);
          ^
Firmware/mock/nucleof030r8/ir_sensor_mock/Drivers/CMSIS/DSP/Examples/ARM/arm_matrix_example/math_helper.c:169:11: style: The scope of the variable 'diff' can be reduced. [variableScope]
  int32_t diff, diffCrnt = 0;
          ^
Firmware/mock/nucleof030r8/ir_sensor_mock/Drivers/CMSIS/DSP/Examples/ARM/arm_matrix_example/math_helper.c:169:17: style: The scope of the variable 'diffCrnt' can be reduced. [variableScope]
  int32_t diff, diffCrnt = 0;
                ^
Firmware/mock/nucleof030r8/ir_sensor_mock/Drivers/CMSIS/DSP/Examples/ARM/arm_matrix_example/math_helper.c:197:11: style: The scope of the variable 'diff' can be reduced. [variableScope]
  int32_t diff, diffCrnt = 0;
          ^
Firmware/mock/nucleof030r8/ir_sensor_mock/Drivers/CMSIS/DSP/Examples/ARM/arm_matrix_example/math_helper.c:197:17: style: The scope of the variable 'diffCrnt' can be reduced. [variableScope]
  int32_t diff, diffCrnt = 0;
                ^
Firmware/mock/nucleof030r8/ir_sensor_mock/Drivers/CMSIS/DSP/Examples/ARM/arm_matrix_example/math_helper.c:311:33: style:inconclusive: Function 'arm_calc_2pow' argument 1 names different: declaration 'guard_bits' definition 'numShifts'. [funcArgNamesDifferent]
uint32_t arm_calc_2pow(uint32_t numShifts)
                                ^
Firmware/mock/nucleof030r8/ir_sensor_mock/Drivers/CMSIS/DSP/Examples/ARM/arm_matrix_example/math_helper.h:61:33: note: Function 'arm_calc_2pow' argument 1 names different: declaration 'guard_bits' definition 'numShifts'.
uint32_t arm_calc_2pow(uint32_t guard_bits);
                                ^
Firmware/mock/nucleof030r8/ir_sensor_mock/Drivers/CMSIS/DSP/Examples/ARM/arm_matrix_example/math_helper.c:311:33: note: Function 'arm_calc_2pow' argument 1 names different: declaration 'guard_bits' definition 'numShifts'.
uint32_t arm_calc_2pow(uint32_t numShifts)
                                ^
Firmware/mock/nucleof030r8/ir_sensor_mock/Drivers/CMSIS/DSP/Examples/ARM/arm_matrix_example/math_helper.c:169:26: style: Variable 'diffCrnt' is assigned a value that is never used. [unreadVariable]
  int32_t diff, diffCrnt = 0;
                         ^
Firmware/mock/nucleof030r8/ir_sensor_mock/Drivers/CMSIS/DSP/Examples/ARM/arm_matrix_example/math_helper.c:197:26: style: Variable 'diffCrnt' is assigned a value that is never used. [unreadVariable]
  int32_t diff, diffCrnt = 0;
                         ^
Firmware/mock/nucleof030r8/ir_sensor_mock/Drivers/CMSIS/DSP/Examples/ARM/arm_signal_converge_example/math_helper.c:73:13: portability: Casting from float * to signed int * is not portable due to different binary data representations on different platforms. [invalidPointerCast]
   test =   (int *)(&pRef[i]);
            ^
Firmware/mock/nucleof030r8/ir_sensor_mock/Drivers/CMSIS/DSP/Examples/ARM/arm_signal_converge_example/math_helper.c:82:13: portability: Casting from float * to signed int * is not portable due to different binary data representations on different platforms. [invalidPointerCast]
   test =   (int *)(&pTest[i]);
            ^
Firmware/mock/nucleof030r8/ir_sensor_mock/Drivers/CMSIS/DSP/Examples/ARM/arm_signal_converge_example/math_helper.c:94:11: portability: Casting from float * to signed int * is not portable due to different binary data representations on different platforms. [invalidPointerCast]
 test =   (int *)(&EnergyError);
          ^
Firmware/mock/nucleof030r8/ir_sensor_mock/Drivers/CMSIS/DSP/Examples/ARM/arm_signal_converge_example/math_helper.c:169:11: style: The scope of the variable 'diff' can be reduced. [variableScope]
  int32_t diff, diffCrnt = 0;
          ^
Firmware/mock/nucleof030r8/ir_sensor_mock/Drivers/CMSIS/DSP/Examples/ARM/arm_signal_converge_example/math_helper.c:169:17: style: The scope of the variable 'diffCrnt' can be reduced. [variableScope]
  int32_t diff, diffCrnt = 0;
                ^
Firmware/mock/nucleof030r8/ir_sensor_mock/Drivers/CMSIS/DSP/Examples/ARM/arm_signal_converge_example/math_helper.c:197:11: style: The scope of the variable 'diff' can be reduced. [variableScope]
  int32_t diff, diffCrnt = 0;
          ^
Firmware/mock/nucleof030r8/ir_sensor_mock/Drivers/CMSIS/DSP/Examples/ARM/arm_signal_converge_example/math_helper.c:197:17: style: The scope of the variable 'diffCrnt' can be reduced. [variableScope]
  int32_t diff, diffCrnt = 0;
                ^
Firmware/mock/nucleof030r8/ir_sensor_mock/Drivers/CMSIS/DSP/Examples/ARM/arm_signal_converge_example/math_helper.c:311:33: style:inconclusive: Function 'arm_calc_2pow' argument 1 names different: declaration 'guard_bits' definition 'numShifts'. [funcArgNamesDifferent]
uint32_t arm_calc_2pow(uint32_t numShifts)
                                ^
Firmware/mock/nucleof030r8/ir_sensor_mock/Drivers/CMSIS/DSP/Examples/ARM/arm_signal_converge_example/math_helper.h:61:33: note: Function 'arm_calc_2pow' argument 1 names different: declaration 'guard_bits' definition 'numShifts'.
uint32_t arm_calc_2pow(uint32_t guard_bits);
                                ^
Firmware/mock/nucleof030r8/ir_sensor_mock/Drivers/CMSIS/DSP/Examples/ARM/arm_signal_converge_example/math_helper.c:311:33: note: Function 'arm_calc_2pow' argument 1 names different: declaration 'guard_bits' definition 'numShifts'.
uint32_t arm_calc_2pow(uint32_t numShifts)
                                ^
Firmware/mock/nucleof030r8/ir_sensor_mock/Drivers/CMSIS/DSP/Examples/ARM/arm_signal_converge_example/math_helper.c:169:26: style: Variable 'diffCrnt' is assigned a value that is never used. [unreadVariable]
  int32_t diff, diffCrnt = 0;
                         ^
Firmware/mock/nucleof030r8/ir_sensor_mock/Drivers/CMSIS/DSP/Examples/ARM/arm_signal_converge_example/math_helper.c:197:26: style: Variable 'diffCrnt' is assigned a value that is never used. [unreadVariable]
  int32_t diff, diffCrnt = 0;
                         ^
Firmware/mock/nucleof030r8/ir_sensor_mock/Drivers/CMSIS/DSP/Source/ControllerFunctions/arm_sin_cos_f32.c:114:10: style: Variable 'temp' is reassigned a value before the old one has been used. [redundantAssignment]
    temp = Dn *(d1 + d2) - 2 * Df;
         ^
Firmware/mock/nucleof030r8/ir_sensor_mock/Drivers/CMSIS/DSP/Source/ControllerFunctions/arm_sin_cos_f32.c:109:10: note: temp is assigned
    temp = (1.0f - fract) * f1 + fract * f2;
         ^
Firmware/mock/nucleof030r8/ir_sensor_mock/Drivers/CMSIS/DSP/Source/ControllerFunctions/arm_sin_cos_f32.c:114:10: note: temp is overwritten
    temp = Dn *(d1 + d2) - 2 * Df;
         ^
Firmware/mock/nucleof030r8/ir_sensor_mock/Drivers/CMSIS/DSP/Source/ControllerFunctions/arm_sin_cos_f32.c:130:10: style: Variable 'temp' is reassigned a value before the old one has been used. [redundantAssignment]
    temp = Dn*(d1 + d2) - 2*Df;
         ^
Firmware/mock/nucleof030r8/ir_sensor_mock/Drivers/CMSIS/DSP/Source/ControllerFunctions/arm_sin_cos_f32.c:127:10: note: temp is assigned
    temp = (1.0f - fract) * f1 + fract * f2;
         ^
Firmware/mock/nucleof030r8/ir_sensor_mock/Drivers/CMSIS/DSP/Source/ControllerFunctions/arm_sin_cos_f32.c:130:10: note: temp is overwritten
    temp = Dn*(d1 + d2) - 2*Df;
         ^
Firmware/mock/nucleof030r8/ir_sensor_mock/Drivers/CMSIS/DSP/Source/FilteringFunctions/arm_biquad_cascade_df1_fast_q31.c:79:12: style: The scope of the variable 'sample' can be reduced. [variableScope]
  uint32_t sample, stage = S->numStages;         /*  loop counters                     */
           ^
Firmware/mock/nucleof030r8/ir_sensor_mock/Drivers/CMSIS/DSP/Source/FilteringFunctions/arm_biquad_cascade_df1_q15.c:313:12: style: The scope of the variable 'sample' can be reduced. [variableScope]
  uint32_t sample, stage = (uint32_t) S->numStages;     /*  Stage loop counter                           */
           ^
Firmware/mock/nucleof030r8/ir_sensor_mock/Drivers/CMSIS/DSP/Source/FilteringFunctions/arm_conv_f32.c:133:12: style: The scope of the variable 'j' can be reduced. [variableScope]
  uint32_t j, k, count, blkCnt, blockSize1, blockSize2, blockSize3;     /* loop counters */
           ^
Firmware/mock/nucleof030r8/ir_sensor_mock/Drivers/CMSIS/DSP/Source/FilteringFunctions/arm_conv_fast_opt_q15.c:162:9: style: Redundant initialization for 'pScr1'. The initialized value is overwritten before it is read. [redundantInitialization]
  pScr1 = pScratch1;
        ^
Firmware/mock/nucleof030r8/ir_sensor_mock/Drivers/CMSIS/DSP/Source/FilteringFunctions/arm_conv_fast_opt_q15.c:84:16: note: pScr1 is initialized
  q15_t *pScr1 = pScratch1;                      /* Temporary pointer for scratch1 */
               ^
Firmware/mock/nucleof030r8/ir_sensor_mock/Drivers/CMSIS/DSP/Source/FilteringFunctions/arm_conv_fast_opt_q15.c:162:9: note: pScr1 is overwritten
  pScr1 = pScratch1;
        ^
Firmware/mock/nucleof030r8/ir_sensor_mock/Drivers/CMSIS/DSP/Source/FilteringFunctions/arm_conv_fast_opt_q15.c:124:9: style: Redundant initialization for 'pScr2'. The initialized value is overwritten before it is read. [redundantInitialization]
  pScr2 = pScratch2 + srcBLen - 1;
        ^
Firmware/mock/nucleof030r8/ir_sensor_mock/Drivers/CMSIS/DSP/Source/FilteringFunctions/arm_conv_fast_opt_q15.c:85:16: note: pScr2 is initialized
  q15_t *pScr2 = pScratch2;                      /* Temporary pointer for scratch1 */
               ^
Firmware/mock/nucleof030r8/ir_sensor_mock/Drivers/CMSIS/DSP/Source/FilteringFunctions/arm_conv_fast_opt_q15.c:124:9: note: pScr2 is overwritten
  pScr2 = pScratch2 + srcBLen - 1;
        ^
Firmware/mock/nucleof030r8/ir_sensor_mock/Drivers/CMSIS/DSP/Source/FilteringFunctions/arm_conv_fast_q15.c:455:10: style: Variable 'px' is reassigned a value before the old one has been used. [redundantAssignment]
      px = pIn1 + count;
         ^
Firmware/mock/nucleof030r8/ir_sensor_mock/Drivers/CMSIS/DSP/Source/FilteringFunctions/arm_conv_fast_q15.c:429:6: note: px is assigned
  px += 3U;
     ^
Firmware/mock/nucleof030r8/ir_sensor_mock/Drivers/CMSIS/DSP/Source/FilteringFunctions/arm_conv_fast_q15.c:455:10: note: px is overwritten
      px = pIn1 + count;
         ^
Firmware/mock/nucleof030r8/ir_sensor_mock/Drivers/CMSIS/DSP/Source/FilteringFunctions/arm_conv_fast_q15.c:1178:10: style: Variable 'px' is reassigned a value before the old one has been used. [redundantAssignment]
      px = pIn1 + count;
         ^
Firmware/mock/nucleof030r8/ir_sensor_mock/Drivers/CMSIS/DSP/Source/FilteringFunctions/arm_conv_fast_q15.c:1159:6: note: px is assigned
  px += 3U;
     ^
Firmware/mock/nucleof030r8/ir_sensor_mock/Drivers/CMSIS/DSP/Source/FilteringFunctions/arm_conv_fast_q15.c:1178:10: note: px is overwritten
      px = pIn1 + count;
         ^
Firmware/mock/nucleof030r8/ir_sensor_mock/Drivers/CMSIS/DSP/Source/FilteringFunctions/arm_conv_fast_q31.c:82:12: style: The scope of the variable 'j' can be reduced. [variableScope]
  uint32_t j, k, count, blkCnt, blockSize1, blockSize2, blockSize3;     /* loop counter */
           ^
Firmware/mock/nucleof030r8/ir_sensor_mock/Drivers/CMSIS/DSP/Source/FilteringFunctions/arm_conv_opt_q15.c:164:9: style: Redundant initialization for 'pScr1'. The initialized value is overwritten before it is read. [redundantInitialization]
  pScr1 = pScratch1;
        ^
Firmware/mock/nucleof030r8/ir_sensor_mock/Drivers/CMSIS/DSP/Source/FilteringFunctions/arm_conv_opt_q15.c:86:16: note: pScr1 is initialized
  q15_t *pScr1 = pScratch1;                      /* Temporary pointer for scratch1 */
               ^
Firmware/mock/nucleof030r8/ir_sensor_mock/Drivers/CMSIS/DSP/Source/FilteringFunctions/arm_conv_opt_q15.c:164:9: note: pScr1 is overwritten
  pScr1 = pScratch1;
        ^
Firmware/mock/nucleof030r8/ir_sensor_mock/Drivers/CMSIS/DSP/Source/FilteringFunctions/arm_conv_opt_q15.c:127:9: style: Redundant initialization for 'pScr2'. The initialized value is overwritten before it is read. [redundantInitialization]
  pScr2 = pScratch2 + srcBLen - 1;
        ^
Firmware/mock/nucleof030r8/ir_sensor_mock/Drivers/CMSIS/DSP/Source/FilteringFunctions/arm_conv_opt_q15.c:87:16: note: pScr2 is initialized
  q15_t *pScr2 = pScratch2;                      /* Temporary pointer for scratch1 */
               ^
Firmware/mock/nucleof030r8/ir_sensor_mock/Drivers/CMSIS/DSP/Source/FilteringFunctions/arm_conv_opt_q15.c:127:9: note: pScr2 is overwritten
  pScr2 = pScratch2 + srcBLen - 1;
        ^
Firmware/mock/nucleof030r8/ir_sensor_mock/Drivers/CMSIS/DSP/Source/FilteringFunctions/arm_conv_opt_q7.c:245:8: style: Variable 'pIn2' is assigned a value that is never used. [unreadVariable]
  pIn2 = (q7_t *) py;
       ^
Firmware/mock/nucleof030r8/ir_sensor_mock/Drivers/CMSIS/DSP/Source/FilteringFunctions/arm_conv_partial_f32.c:637:12: style: The scope of the variable 'i' can be reduced. [variableScope]
  uint32_t i, j;                                 /* loop counters */
           ^
Firmware/mock/nucleof030r8/ir_sensor_mock/Drivers/CMSIS/DSP/Source/FilteringFunctions/arm_conv_partial_f32.c:637:15: style: The scope of the variable 'j' can be reduced. [variableScope]
  uint32_t i, j;                                 /* loop counters */
              ^
Firmware/mock/nucleof030r8/ir_sensor_mock/Drivers/CMSIS/DSP/Source/FilteringFunctions/arm_conv_partial_f32.c:101:14: style: The scope of the variable 'px' can be reduced. [variableScope]
  float32_t *px;                                 /* Intermediate inputA pointer */
             ^
Firmware/mock/nucleof030r8/ir_sensor_mock/Drivers/CMSIS/DSP/Source/FilteringFunctions/arm_conv_partial_f32.c:102:14: style: The scope of the variable 'py' can be reduced. [variableScope]
  float32_t *py;                                 /* Intermediate inputB pointer */
             ^
Firmware/mock/nucleof030r8/ir_sensor_mock/Drivers/CMSIS/DSP/Source/FilteringFunctions/arm_conv_partial_f32.c:106:12: style: The scope of the variable 'j' can be reduced. [variableScope]
  uint32_t j, k, count = 0U, blkCnt, check;
           ^
Firmware/mock/nucleof030r8/ir_sensor_mock/Drivers/CMSIS/DSP/Source/FilteringFunctions/arm_conv_partial_f32.c:106:15: style: The scope of the variable 'k' can be reduced. [variableScope]
  uint32_t j, k, count = 0U, blkCnt, check;
              ^
Firmware/mock/nucleof030r8/ir_sensor_mock/Drivers/CMSIS/DSP/Source/FilteringFunctions/arm_conv_partial_f32.c:106:18: style: The scope of the variable 'count' can be reduced. [variableScope]
  uint32_t j, k, count = 0U, blkCnt, check;
                 ^
Firmware/mock/nucleof030r8/ir_sensor_mock/Drivers/CMSIS/DSP/Source/FilteringFunctions/arm_conv_partial_f32.c:106:30: style: The scope of the variable 'blkCnt' can be reduced. [variableScope]
  uint32_t j, k, count = 0U, blkCnt, check;
                             ^
Firmware/mock/nucleof030r8/ir_sensor_mock/Drivers/CMSIS/DSP/Source/FilteringFunctions/arm_conv_partial_f32.c:106:38: style: The scope of the variable 'check' can be reduced. [variableScope]
  uint32_t j, k, count = 0U, blkCnt, check;
                                     ^
Firmware/mock/nucleof030r8/ir_sensor_mock/Drivers/CMSIS/DSP/Source/FilteringFunctions/arm_conv_partial_f32.c:107:11: style: The scope of the variable 'blockSize1' can be reduced. [variableScope]
  int32_t blockSize1, blockSize2, blockSize3;    /* loop counters */
          ^
Firmware/mock/nucleof030r8/ir_sensor_mock/Drivers/CMSIS/DSP/Source/FilteringFunctions/arm_conv_partial_f32.c:107:23: style: The scope of the variable 'blockSize2' can be reduced. [variableScope]
  int32_t blockSize1, blockSize2, blockSize3;    /* loop counters */
                      ^
Firmware/mock/nucleof030r8/ir_sensor_mock/Drivers/CMSIS/DSP/Source/FilteringFunctions/arm_conv_partial_f32.c:107:35: style: The scope of the variable 'blockSize3' can be reduced. [variableScope]
  int32_t blockSize1, blockSize2, blockSize3;    /* loop counters */
                                  ^
Firmware/mock/nucleof030r8/ir_sensor_mock/Drivers/CMSIS/DSP/Source/FilteringFunctions/arm_conv_partial_f32.c:98:19: style: Variable 'pIn1' is assigned a value that is never used. [unreadVariable]
  float32_t *pIn1 = pSrcA;                       /* inputA pointer */
                  ^
Firmware/mock/nucleof030r8/ir_sensor_mock/Drivers/CMSIS/DSP/Source/FilteringFunctions/arm_conv_partial_f32.c:99:19: style: Variable 'pIn2' is assigned a value that is never used. [unreadVariable]
  float32_t *pIn2 = pSrcB;                       /* inputB pointer */
                  ^
Firmware/mock/nucleof030r8/ir_sensor_mock/Drivers/CMSIS/DSP/Source/FilteringFunctions/arm_conv_partial_f32.c:100:19: style: Variable 'pOut' is assigned a value that is never used. [unreadVariable]
  float32_t *pOut = pDst;                        /* output pointer */
                  ^
Firmware/mock/nucleof030r8/ir_sensor_mock/Drivers/CMSIS/DSP/Source/FilteringFunctions/arm_conv_partial_f32.c:106:24: style: Variable 'count' is assigned a value that is never used. [unreadVariable]
  uint32_t j, k, count = 0U, blkCnt, check;
                       ^
Firmware/mock/nucleof030r8/ir_sensor_mock/Drivers/CMSIS/DSP/Source/FilteringFunctions/arm_conv_partial_fast_opt_q15.c:75:15: style: Variable 'pOut' is assigned a value that is never used. [unreadVariable]
  q15_t *pOut = pDst;                            /* output pointer */
              ^
Firmware/mock/nucleof030r8/ir_sensor_mock/Drivers/CMSIS/DSP/Source/FilteringFunctions/arm_conv_partial_fast_opt_q15.c:76:16: style: Variable 'pScr1' is assigned a value that is never used. [unreadVariable]
  q15_t *pScr1 = pScratch1;                      /* Temporary pointer for scratch1 */
               ^
Firmware/mock/nucleof030r8/ir_sensor_mock/Drivers/CMSIS/DSP/Source/FilteringFunctions/arm_conv_partial_fast_opt_q15.c:77:16: style: Variable 'pScr2' is assigned a value that is never used. [unreadVariable]
  q15_t *pScr2 = pScratch2;                      /* Temporary pointer for scratch1 */
               ^
Firmware/mock/nucleof030r8/ir_sensor_mock/Drivers/CMSIS/DSP/Source/FilteringFunctions/arm_conv_partial_fast_opt_q15.c:407:10: style: The scope of the variable 'pIn1' can be reduced. [variableScope]
  q15_t *pIn1;                                   /* inputA pointer */
         ^
Firmware/mock/nucleof030r8/ir_sensor_mock/Drivers/CMSIS/DSP/Source/FilteringFunctions/arm_conv_partial_fast_opt_q15.c:409:10: style: The scope of the variable 'px' can be reduced. [variableScope]
  q15_t *px;                                     /* Intermediate inputA pointer  */
         ^
Firmware/mock/nucleof030r8/ir_sensor_mock/Drivers/CMSIS/DSP/Source/FilteringFunctions/arm_conv_partial_fast_opt_q15.c:411:12: style: The scope of the variable 'j' can be reduced. [variableScope]
  uint32_t j, k, blkCnt;                         /* loop counter */
           ^
Firmware/mock/nucleof030r8/ir_sensor_mock/Drivers/CMSIS/DSP/Source/FilteringFunctions/arm_conv_partial_fast_opt_q15.c:411:15: style: The scope of the variable 'k' can be reduced. [variableScope]
  uint32_t j, k, blkCnt;                         /* loop counter */
              ^
Firmware/mock/nucleof030r8/ir_sensor_mock/Drivers/CMSIS/DSP/Source/FilteringFunctions/arm_conv_partial_fast_opt_q15.c:411:18: style: The scope of the variable 'blkCnt' can be reduced. [variableScope]
  uint32_t j, k, blkCnt;                         /* loop counter */
                 ^
Firmware/mock/nucleof030r8/ir_sensor_mock/Drivers/CMSIS/DSP/Source/FilteringFunctions/arm_conv_partial_fast_opt_q15.c:413:12: style: The scope of the variable 'tapCnt' can be reduced. [variableScope]
  uint32_t tapCnt;                               /* loop count */
           ^
Firmware/mock/nucleof030r8/ir_sensor_mock/Drivers/CMSIS/DSP/Source/FilteringFunctions/arm_conv_partial_fast_opt_q15.c:403:15: style: Variable 'pOut' is assigned a value that is never used. [unreadVariable]
  q15_t *pOut = pDst;                            /* output pointer */
              ^
Firmware/mock/nucleof030r8/ir_sensor_mock/Drivers/CMSIS/DSP/Source/FilteringFunctions/arm_conv_partial_fast_opt_q15.c:404:16: style: Variable 'pScr1' is assigned a value that is never used. [unreadVariable]
  q15_t *pScr1 = pScratch1;                      /* Temporary pointer for scratch1 */
               ^
Firmware/mock/nucleof030r8/ir_sensor_mock/Drivers/CMSIS/DSP/Source/FilteringFunctions/arm_conv_partial_fast_opt_q15.c:405:16: style: Variable 'pScr2' is assigned a value that is never used. [unreadVariable]
  q15_t *pScr2 = pScratch2;                      /* Temporary pointer for scratch1 */
               ^
Firmware/mock/nucleof030r8/ir_sensor_mock/Drivers/CMSIS/DSP/Source/FilteringFunctions/arm_conv_partial_fast_q15.c:476:12: style: Variable 'px' is reassigned a value before the old one has been used. [redundantAssignment]
        px = pIn1 + count;
           ^
Firmware/mock/nucleof030r8/ir_sensor_mock/Drivers/CMSIS/DSP/Source/FilteringFunctions/arm_conv_partial_fast_q15.c:450:6: note: px is assigned
  px += 3U;
     ^
Firmware/mock/nucleof030r8/ir_sensor_mock/Drivers/CMSIS/DSP/Source/FilteringFunctions/arm_conv_partial_fast_q15.c:476:12: note: px is overwritten
        px = pIn1 + count;
           ^
Firmware/mock/nucleof030r8/ir_sensor_mock/Drivers/CMSIS/DSP/Source/FilteringFunctions/arm_conv_partial_fast_q15.c:68:15: style: Variable 'pOut' is assigned a value that is never used. [unreadVariable]
  q15_t *pOut = pDst;                            /* output pointer               */
              ^
Firmware/mock/nucleof030r8/ir_sensor_mock/Drivers/CMSIS/DSP/Source/FilteringFunctions/arm_conv_partial_fast_q15.c:1258:12: style: Variable 'px' is reassigned a value before the old one has been used. [redundantAssignment]
        px = pIn1 + count;
           ^
Firmware/mock/nucleof030r8/ir_sensor_mock/Drivers/CMSIS/DSP/Source/FilteringFunctions/arm_conv_partial_fast_q15.c:1239:6: note: px is assigned
  px += 3U;
     ^
Firmware/mock/nucleof030r8/ir_sensor_mock/Drivers/CMSIS/DSP/Source/FilteringFunctions/arm_conv_partial_fast_q15.c:1258:12: note: px is overwritten
        px = pIn1 + count;
           ^
Firmware/mock/nucleof030r8/ir_sensor_mock/Drivers/CMSIS/DSP/Source/FilteringFunctions/arm_conv_partial_fast_q15.c:728:15: style: Variable 'pOut' is assigned a value that is never used. [unreadVariable]
  q15_t *pOut = pDst;                            /* output pointer               */
              ^
Firmware/mock/nucleof030r8/ir_sensor_mock/Drivers/CMSIS/DSP/Source/FilteringFunctions/arm_conv_partial_fast_q31.c:67:10: style: The scope of the variable 'px' can be reduced. [variableScope]
  q31_t *px;                                     /* Intermediate inputA pointer  */
         ^
Firmware/mock/nucleof030r8/ir_sensor_mock/Drivers/CMSIS/DSP/Source/FilteringFunctions/arm_conv_partial_fast_q31.c:68:10: style: The scope of the variable 'py' can be reduced. [variableScope]
  q31_t *py;                                     /* Intermediate inputB pointer  */
         ^
Firmware/mock/nucleof030r8/ir_sensor_mock/Drivers/CMSIS/DSP/Source/FilteringFunctions/arm_conv_partial_fast_q31.c:72:12: style: The scope of the variable 'j' can be reduced. [variableScope]
  uint32_t j, k, count, check, blkCnt;
           ^
Firmware/mock/nucleof030r8/ir_sensor_mock/Drivers/CMSIS/DSP/Source/FilteringFunctions/arm_conv_partial_fast_q31.c:72:15: style: The scope of the variable 'k' can be reduced. [variableScope]
  uint32_t j, k, count, check, blkCnt;
              ^
Firmware/mock/nucleof030r8/ir_sensor_mock/Drivers/CMSIS/DSP/Source/FilteringFunctions/arm_conv_partial_fast_q31.c:72:18: style: The scope of the variable 'count' can be reduced. [variableScope]
  uint32_t j, k, count, check, blkCnt;
                 ^
Firmware/mock/nucleof030r8/ir_sensor_mock/Drivers/CMSIS/DSP/Source/FilteringFunctions/arm_conv_partial_fast_q31.c:72:25: style: The scope of the variable 'check' can be reduced. [variableScope]
  uint32_t j, k, count, check, blkCnt;
                        ^
Firmware/mock/nucleof030r8/ir_sensor_mock/Drivers/CMSIS/DSP/Source/FilteringFunctions/arm_conv_partial_fast_q31.c:72:32: style: The scope of the variable 'blkCnt' can be reduced. [variableScope]
  uint32_t j, k, count, check, blkCnt;
                               ^
Firmware/mock/nucleof030r8/ir_sensor_mock/Drivers/CMSIS/DSP/Source/FilteringFunctions/arm_conv_partial_fast_q31.c:73:11: style: The scope of the variable 'blockSize1' can be reduced. [variableScope]
  int32_t blockSize1, blockSize2, blockSize3;    /* loop counters                 */
          ^
Firmware/mock/nucleof030r8/ir_sensor_mock/Drivers/CMSIS/DSP/Source/FilteringFunctions/arm_conv_partial_fast_q31.c:73:23: style: The scope of the variable 'blockSize2' can be reduced. [variableScope]
  int32_t blockSize1, blockSize2, blockSize3;    /* loop counters                 */
                      ^
Firmware/mock/nucleof030r8/ir_sensor_mock/Drivers/CMSIS/DSP/Source/FilteringFunctions/arm_conv_partial_fast_q31.c:73:35: style: The scope of the variable 'blockSize3' can be reduced. [variableScope]
  int32_t blockSize1, blockSize2, blockSize3;    /* loop counters                 */
                                  ^
Firmware/mock/nucleof030r8/ir_sensor_mock/Drivers/CMSIS/DSP/Source/FilteringFunctions/arm_conv_partial_fast_q31.c:66:15: style: Variable 'pOut' is assigned a value that is never used. [unreadVariable]
  q31_t *pOut = pDst;                            /* output pointer               */
              ^
Firmware/mock/nucleof030r8/ir_sensor_mock/Drivers/CMSIS/DSP/Source/FilteringFunctions/arm_conv_partial_opt_q15.c:76:15: style: Variable 'pOut' is assigned a value that is never used. [unreadVariable]
  q15_t *pOut = pDst;                            /* output pointer */
              ^
Firmware/mock/nucleof030r8/ir_sensor_mock/Drivers/CMSIS/DSP/Source/FilteringFunctions/arm_conv_partial_opt_q15.c:77:16: style: Variable 'pScr1' is assigned a value that is never used. [unreadVariable]
  q15_t *pScr1 = pScratch1;                      /* Temporary pointer for scratch1 */
               ^
Firmware/mock/nucleof030r8/ir_sensor_mock/Drivers/CMSIS/DSP/Source/FilteringFunctions/arm_conv_partial_opt_q15.c:78:16: style: Variable 'pScr2' is assigned a value that is never used. [unreadVariable]
  q15_t *pScr2 = pScratch2;                      /* Temporary pointer for scratch1 */
               ^
Firmware/mock/nucleof030r8/ir_sensor_mock/Drivers/CMSIS/DSP/Source/FilteringFunctions/arm_conv_partial_opt_q15.c:401:10: style: The scope of the variable 'pIn1' can be reduced. [variableScope]
  q15_t *pIn1;                                   /* inputA pointer */
         ^
Firmware/mock/nucleof030r8/ir_sensor_mock/Drivers/CMSIS/DSP/Source/FilteringFunctions/arm_conv_partial_opt_q15.c:403:10: style: The scope of the variable 'px' can be reduced. [variableScope]
  q15_t *px;                                     /* Intermediate inputA pointer  */
         ^
Firmware/mock/nucleof030r8/ir_sensor_mock/Drivers/CMSIS/DSP/Source/FilteringFunctions/arm_conv_partial_opt_q15.c:405:12: style: The scope of the variable 'j' can be reduced. [variableScope]
  uint32_t j, k, blkCnt;                         /* loop counter */
           ^
Firmware/mock/nucleof030r8/ir_sensor_mock/Drivers/CMSIS/DSP/Source/FilteringFunctions/arm_conv_partial_opt_q15.c:405:15: style: The scope of the variable 'k' can be reduced. [variableScope]
  uint32_t j, k, blkCnt;                         /* loop counter */
              ^
Firmware/mock/nucleof030r8/ir_sensor_mock/Drivers/CMSIS/DSP/Source/FilteringFunctions/arm_conv_partial_opt_q15.c:405:18: style: The scope of the variable 'blkCnt' can be reduced. [variableScope]
  uint32_t j, k, blkCnt;                         /* loop counter */
                 ^
Firmware/mock/nucleof030r8/ir_sensor_mock/Drivers/CMSIS/DSP/Source/FilteringFunctions/arm_conv_partial_opt_q15.c:407:12: style: The scope of the variable 'tapCnt' can be reduced. [variableScope]
  uint32_t tapCnt;                               /* loop count */
           ^
Firmware/mock/nucleof030r8/ir_sensor_mock/Drivers/CMSIS/DSP/Source/FilteringFunctions/arm_conv_partial_opt_q15.c:397:15: style: Variable 'pOut' is assigned a value that is never used. [unreadVariable]
  q15_t *pOut = pDst;                            /* output pointer */
              ^
Firmware/mock/nucleof030r8/ir_sensor_mock/Drivers/CMSIS/DSP/Source/FilteringFunctions/arm_conv_partial_opt_q15.c:398:16: style: Variable 'pScr1' is assigned a value that is never used. [unreadVariable]
  q15_t *pScr1 = pScratch1;                      /* Temporary pointer for scratch1 */
               ^
Firmware/mock/nucleof030r8/ir_sensor_mock/Drivers/CMSIS/DSP/Source/FilteringFunctions/arm_conv_partial_opt_q15.c:399:16: style: Variable 'pScr2' is assigned a value that is never used. [unreadVariable]
  q15_t *pScr2 = pScratch2;                      /* Temporary pointer for scratch1 */
               ^
Firmware/mock/nucleof030r8/ir_sensor_mock/Drivers/CMSIS/DSP/Source/FilteringFunctions/arm_conv_partial_opt_q7.c:85:14: style: Variable 'pOut' is assigned a value that is never used. [unreadVariable]
  q7_t *pOut = pDst;                             /* output pointer */
             ^
Firmware/mock/nucleof030r8/ir_sensor_mock/Drivers/CMSIS/DSP/Source/FilteringFunctions/arm_conv_partial_opt_q7.c:219:10: style: Variable 'pIn2' is assigned a value that is never used. [unreadVariable]
    pIn2 = (q7_t *) py;
         ^
Firmware/mock/nucleof030r8/ir_sensor_mock/Drivers/CMSIS/DSP/Source/FilteringFunctions/arm_conv_partial_opt_q7.c:426:10: style: The scope of the variable 'pScr2' can be reduced. [variableScope]
  q15_t *pScr2, *pScr1;                          /* Intermediate pointers for scratch pointers */
         ^
Firmware/mock/nucleof030r8/ir_sensor_mock/Drivers/CMSIS/DSP/Source/FilteringFunctions/arm_conv_partial_opt_q7.c:426:18: style: The scope of the variable 'pScr1' can be reduced. [variableScope]
  q15_t *pScr2, *pScr1;                          /* Intermediate pointers for scratch pointers */
                 ^
Firmware/mock/nucleof030r8/ir_sensor_mock/Drivers/CMSIS/DSP/Source/FilteringFunctions/arm_conv_partial_opt_q7.c:428:9: style: The scope of the variable 'pIn1' can be reduced. [variableScope]
  q7_t *pIn1, *pIn2;                             /* inputA and inputB pointer */
        ^
Firmware/mock/nucleof030r8/ir_sensor_mock/Drivers/CMSIS/DSP/Source/FilteringFunctions/arm_conv_partial_opt_q7.c:429:12: style: The scope of the variable 'j' can be reduced. [variableScope]
  uint32_t j, k, blkCnt, tapCnt;                 /* loop counter */
           ^
Firmware/mock/nucleof030r8/ir_sensor_mock/Drivers/CMSIS/DSP/Source/FilteringFunctions/arm_conv_partial_opt_q7.c:429:15: style: The scope of the variable 'k' can be reduced. [variableScope]
  uint32_t j, k, blkCnt, tapCnt;                 /* loop counter */
              ^
Firmware/mock/nucleof030r8/ir_sensor_mock/Drivers/CMSIS/DSP/Source/FilteringFunctions/arm_conv_partial_opt_q7.c:429:18: style: The scope of the variable 'blkCnt' can be reduced. [variableScope]
  uint32_t j, k, blkCnt, tapCnt;                 /* loop counter */
                 ^
Firmware/mock/nucleof030r8/ir_sensor_mock/Drivers/CMSIS/DSP/Source/FilteringFunctions/arm_conv_partial_opt_q7.c:429:26: style: The scope of the variable 'tapCnt' can be reduced. [variableScope]
  uint32_t j, k, blkCnt, tapCnt;                 /* loop counter */
                         ^
Firmware/mock/nucleof030r8/ir_sensor_mock/Drivers/CMSIS/DSP/Source/FilteringFunctions/arm_conv_partial_opt_q7.c:430:9: style: The scope of the variable 'px' can be reduced. [variableScope]
  q7_t *px;                                      /* Temporary input1 pointer */
        ^
Firmware/mock/nucleof030r8/ir_sensor_mock/Drivers/CMSIS/DSP/Source/FilteringFunctions/arm_conv_partial_opt_q7.c:434:14: style: Variable 'pOut' is assigned a value that is never used. [unreadVariable]
  q7_t *pOut = pDst;                             /* output pointer */
             ^
Firmware/mock/nucleof030r8/ir_sensor_mock/Drivers/CMSIS/DSP/Source/FilteringFunctions/arm_conv_partial_opt_q7.c:593:10: style: Variable 'pIn2' is assigned a value that is never used. [unreadVariable]
    pIn2 = (q7_t *) py;
         ^
Firmware/mock/nucleof030r8/ir_sensor_mock/Drivers/CMSIS/DSP/Source/FilteringFunctions/arm_conv_partial_q15.c:753:12: style: The scope of the variable 'i' can be reduced. [variableScope]
  uint32_t i, j;                                 /* loop counters */
           ^
Firmware/mock/nucleof030r8/ir_sensor_mock/Drivers/CMSIS/DSP/Source/FilteringFunctions/arm_conv_partial_q15.c:753:15: style: The scope of the variable 'j' can be reduced. [variableScope]
  uint32_t i, j;                                 /* loop counters */
              ^
Firmware/mock/nucleof030r8/ir_sensor_mock/Drivers/CMSIS/DSP/Source/FilteringFunctions/arm_conv_partial_q31.c:574:12: style: The scope of the variable 'i' can be reduced. [variableScope]
  uint32_t i, j;                                 /* loop counters */
           ^
Firmware/mock/nucleof030r8/ir_sensor_mock/Drivers/CMSIS/DSP/Source/FilteringFunctions/arm_conv_partial_q31.c:574:15: style: The scope of the variable 'j' can be reduced. [variableScope]
  uint32_t i, j;                                 /* loop counters */
              ^
Firmware/mock/nucleof030r8/ir_sensor_mock/Drivers/CMSIS/DSP/Source/FilteringFunctions/arm_conv_partial_q31.c:72:10: style: The scope of the variable 'px' can be reduced. [variableScope]
  q31_t *px;                                     /* Intermediate inputA pointer  */
         ^
Firmware/mock/nucleof030r8/ir_sensor_mock/Drivers/CMSIS/DSP/Source/FilteringFunctions/arm_conv_partial_q31.c:73:10: style: The scope of the variable 'py' can be reduced. [variableScope]
  q31_t *py;                                     /* Intermediate inputB pointer  */
         ^
Firmware/mock/nucleof030r8/ir_sensor_mock/Drivers/CMSIS/DSP/Source/FilteringFunctions/arm_conv_partial_q31.c:77:12: style: The scope of the variable 'j' can be reduced. [variableScope]
  uint32_t j, k, count, check, blkCnt;
           ^
Firmware/mock/nucleof030r8/ir_sensor_mock/Drivers/CMSIS/DSP/Source/FilteringFunctions/arm_conv_partial_q31.c:77:15: style: The scope of the variable 'k' can be reduced. [variableScope]
  uint32_t j, k, count, check, blkCnt;
              ^
Firmware/mock/nucleof030r8/ir_sensor_mock/Drivers/CMSIS/DSP/Source/FilteringFunctions/arm_conv_partial_q31.c:77:18: style: The scope of the variable 'count' can be reduced. [variableScope]
  uint32_t j, k, count, check, blkCnt;
                 ^
Firmware/mock/nucleof030r8/ir_sensor_mock/Drivers/CMSIS/DSP/Source/FilteringFunctions/arm_conv_partial_q31.c:77:25: style: The scope of the variable 'check' can be reduced. [variableScope]
  uint32_t j, k, count, check, blkCnt;
                        ^
Firmware/mock/nucleof030r8/ir_sensor_mock/Drivers/CMSIS/DSP/Source/FilteringFunctions/arm_conv_partial_q31.c:77:32: style: The scope of the variable 'blkCnt' can be reduced. [variableScope]
  uint32_t j, k, count, check, blkCnt;
                               ^
Firmware/mock/nucleof030r8/ir_sensor_mock/Drivers/CMSIS/DSP/Source/FilteringFunctions/arm_conv_partial_q31.c:78:11: style: The scope of the variable 'blockSize1' can be reduced. [variableScope]
  int32_t blockSize1, blockSize2, blockSize3;    /* loop counter                 */
          ^
Firmware/mock/nucleof030r8/ir_sensor_mock/Drivers/CMSIS/DSP/Source/FilteringFunctions/arm_conv_partial_q31.c:78:23: style: The scope of the variable 'blockSize2' can be reduced. [variableScope]
  int32_t blockSize1, blockSize2, blockSize3;    /* loop counter                 */
                      ^
Firmware/mock/nucleof030r8/ir_sensor_mock/Drivers/CMSIS/DSP/Source/FilteringFunctions/arm_conv_partial_q31.c:78:35: style: The scope of the variable 'blockSize3' can be reduced. [variableScope]
  int32_t blockSize1, blockSize2, blockSize3;    /* loop counter                 */
                                  ^
Firmware/mock/nucleof030r8/ir_sensor_mock/Drivers/CMSIS/DSP/Source/FilteringFunctions/arm_conv_partial_q31.c:71:15: style: Variable 'pOut' is assigned a value that is never used. [unreadVariable]
  q31_t *pOut = pDst;                            /* output pointer               */
              ^
Firmware/mock/nucleof030r8/ir_sensor_mock/Drivers/CMSIS/DSP/Source/FilteringFunctions/arm_conv_partial_q7.c:708:12: style: The scope of the variable 'i' can be reduced. [variableScope]
  uint32_t i, j;                                 /* loop counters */
           ^
Firmware/mock/nucleof030r8/ir_sensor_mock/Drivers/CMSIS/DSP/Source/FilteringFunctions/arm_conv_partial_q7.c:708:15: style: The scope of the variable 'j' can be reduced. [variableScope]
  uint32_t i, j;                                 /* loop counters */
              ^
Firmware/mock/nucleof030r8/ir_sensor_mock/Drivers/CMSIS/DSP/Source/FilteringFunctions/arm_conv_partial_q7.c:74:9: style: The scope of the variable 'px' can be reduced. [variableScope]
  q7_t *px;                                      /* Intermediate inputA pointer */
        ^
Firmware/mock/nucleof030r8/ir_sensor_mock/Drivers/CMSIS/DSP/Source/FilteringFunctions/arm_conv_partial_q7.c:75:9: style: The scope of the variable 'py' can be reduced. [variableScope]
  q7_t *py;                                      /* Intermediate inputB pointer */
        ^
Firmware/mock/nucleof030r8/ir_sensor_mock/Drivers/CMSIS/DSP/Source/FilteringFunctions/arm_conv_partial_q7.c:81:12: style: The scope of the variable 'j' can be reduced. [variableScope]
  uint32_t j, k, count, check, blkCnt;
           ^
Firmware/mock/nucleof030r8/ir_sensor_mock/Drivers/CMSIS/DSP/Source/FilteringFunctions/arm_conv_partial_q7.c:81:15: style: The scope of the variable 'k' can be reduced. [variableScope]
  uint32_t j, k, count, check, blkCnt;
              ^
Firmware/mock/nucleof030r8/ir_sensor_mock/Drivers/CMSIS/DSP/Source/FilteringFunctions/arm_conv_partial_q7.c:81:18: style: The scope of the variable 'count' can be reduced. [variableScope]
  uint32_t j, k, count, check, blkCnt;
                 ^
Firmware/mock/nucleof030r8/ir_sensor_mock/Drivers/CMSIS/DSP/Source/FilteringFunctions/arm_conv_partial_q7.c:81:25: style: The scope of the variable 'check' can be reduced. [variableScope]
  uint32_t j, k, count, check, blkCnt;
                        ^
Firmware/mock/nucleof030r8/ir_sensor_mock/Drivers/CMSIS/DSP/Source/FilteringFunctions/arm_conv_partial_q7.c:81:32: style: The scope of the variable 'blkCnt' can be reduced. [variableScope]
  uint32_t j, k, count, check, blkCnt;
                               ^
Firmware/mock/nucleof030r8/ir_sensor_mock/Drivers/CMSIS/DSP/Source/FilteringFunctions/arm_conv_partial_q7.c:82:11: style: The scope of the variable 'blockSize1' can be reduced. [variableScope]
  int32_t blockSize1, blockSize2, blockSize3;    /* loop counter */
          ^
Firmware/mock/nucleof030r8/ir_sensor_mock/Drivers/CMSIS/DSP/Source/FilteringFunctions/arm_conv_partial_q7.c:82:23: style: The scope of the variable 'blockSize2' can be reduced. [variableScope]
  int32_t blockSize1, blockSize2, blockSize3;    /* loop counter */
                      ^
Firmware/mock/nucleof030r8/ir_sensor_mock/Drivers/CMSIS/DSP/Source/FilteringFunctions/arm_conv_partial_q7.c:82:35: style: The scope of the variable 'blockSize3' can be reduced. [variableScope]
  int32_t blockSize1, blockSize2, blockSize3;    /* loop counter */
                                  ^
Firmware/mock/nucleof030r8/ir_sensor_mock/Drivers/CMSIS/DSP/Source/FilteringFunctions/arm_conv_partial_q7.c:73:14: style: Variable 'pOut' is assigned a value that is never used. [unreadVariable]
  q7_t *pOut = pDst;                             /* output pointer */
             ^
Firmware/mock/nucleof030r8/ir_sensor_mock/Drivers/CMSIS/DSP/Source/FilteringFunctions/arm_conv_q31.c:88:12: style: The scope of the variable 'j' can be reduced. [variableScope]
  uint32_t j, k, count, blkCnt, blockSize1, blockSize2, blockSize3;     /* loop counter */
           ^
Firmware/mock/nucleof030r8/ir_sensor_mock/Drivers/CMSIS/DSP/Source/FilteringFunctions/arm_conv_q7.c:87:12: style: The scope of the variable 'j' can be reduced. [variableScope]
  uint32_t j, k, count, blkCnt, blockSize1, blockSize2, blockSize3;     /* loop counter */
           ^
Firmware/mock/nucleof030r8/ir_sensor_mock/Drivers/CMSIS/DSP/Source/FilteringFunctions/arm_correlate_f32.c:125:38: style: The scope of the variable 'outBlockSize' can be reduced. [variableScope]
  uint32_t j, k = 0U, count, blkCnt, outBlockSize, blockSize1, blockSize2, blockSize3;  /* loop counters */
                                     ^
Firmware/mock/nucleof030r8/ir_sensor_mock/Drivers/CMSIS/DSP/Source/FilteringFunctions/arm_correlate_f32.c:125:17: style: Variable 'k' is assigned a value that is never used. [unreadVariable]
  uint32_t j, k = 0U, count, blkCnt, outBlockSize, blockSize1, blockSize2, blockSize3;  /* loop counters */
                ^
Firmware/mock/nucleof030r8/ir_sensor_mock/Drivers/CMSIS/DSP/Source/FilteringFunctions/arm_correlate_fast_q15.c:437:10: style: Variable 'px' is reassigned a value before the old one has been used. [redundantAssignment]
      px = pIn1 + count;
         ^
Firmware/mock/nucleof030r8/ir_sensor_mock/Drivers/CMSIS/DSP/Source/FilteringFunctions/arm_correlate_fast_q15.c:410:6: note: px is assigned
  px += 3U;
     ^
Firmware/mock/nucleof030r8/ir_sensor_mock/Drivers/CMSIS/DSP/Source/FilteringFunctions/arm_correlate_fast_q15.c:437:10: note: px is overwritten
      px = pIn1 + count;
         ^
Firmware/mock/nucleof030r8/ir_sensor_mock/Drivers/CMSIS/DSP/Source/FilteringFunctions/arm_correlate_fast_q15.c:82:17: style: Variable 'k' is assigned a value that is never used. [unreadVariable]
  uint32_t j, k = 0U, count, blkCnt, outBlockSize, blockSize1, blockSize2, blockSize3;  /* loop counter                 */
                ^
Firmware/mock/nucleof030r8/ir_sensor_mock/Drivers/CMSIS/DSP/Source/FilteringFunctions/arm_correlate_fast_q15.c:1121:10: style: Variable 'px' is reassigned a value before the old one has been used. [redundantAssignment]
      px = pIn1 + count;
         ^
Firmware/mock/nucleof030r8/ir_sensor_mock/Drivers/CMSIS/DSP/Source/FilteringFunctions/arm_correlate_fast_q15.c:1094:6: note: px is assigned
  px += 3U;
     ^
Firmware/mock/nucleof030r8/ir_sensor_mock/Drivers/CMSIS/DSP/Source/FilteringFunctions/arm_correlate_fast_q15.c:1121:10: note: px is overwritten
      px = pIn1 + count;
         ^
Firmware/mock/nucleof030r8/ir_sensor_mock/Drivers/CMSIS/DSP/Source/FilteringFunctions/arm_correlate_fast_q15.c:627:17: style: Variable 'k' is assigned a value that is never used. [unreadVariable]
  uint32_t j, k = 0U, count, blkCnt, outBlockSize, blockSize1, blockSize2, blockSize3;  /* loop counter                 */
                ^
Firmware/mock/nucleof030r8/ir_sensor_mock/Drivers/CMSIS/DSP/Source/FilteringFunctions/arm_correlate_fast_q31.c:84:38: style: The scope of the variable 'outBlockSize' can be reduced. [variableScope]
  uint32_t j, k = 0U, count, blkCnt, outBlockSize, blockSize1, blockSize2, blockSize3;  /* loop counter                 */
                                     ^
Firmware/mock/nucleof030r8/ir_sensor_mock/Drivers/CMSIS/DSP/Source/FilteringFunctions/arm_correlate_fast_q31.c:84:17: style: Variable 'k' is assigned a value that is never used. [unreadVariable]
  uint32_t j, k = 0U, count, blkCnt, outBlockSize, blockSize1, blockSize2, blockSize3;  /* loop counter                 */
                ^
Firmware/mock/nucleof030r8/ir_sensor_mock/Drivers/CMSIS/DSP/Source/FilteringFunctions/arm_correlate_q31.c:86:38: style: The scope of the variable 'outBlockSize' can be reduced. [variableScope]
  uint32_t j, k = 0U, count, blkCnt, outBlockSize, blockSize1, blockSize2, blockSize3;  /* loop counter                 */
                                     ^
Firmware/mock/nucleof030r8/ir_sensor_mock/Drivers/CMSIS/DSP/Source/FilteringFunctions/arm_correlate_q31.c:86:17: style: Variable 'k' is assigned a value that is never used. [unreadVariable]
  uint32_t j, k = 0U, count, blkCnt, outBlockSize, blockSize1, blockSize2, blockSize3;  /* loop counter                 */
                ^
Firmware/mock/nucleof030r8/ir_sensor_mock/Drivers/CMSIS/DSP/Source/FilteringFunctions/arm_correlate_q7.c:87:38: style: The scope of the variable 'outBlockSize' can be reduced. [variableScope]
  uint32_t j, k = 0U, count, blkCnt, outBlockSize, blockSize1, blockSize2, blockSize3;  /* loop counter                 */
                                     ^
Firmware/mock/nucleof030r8/ir_sensor_mock/Drivers/CMSIS/DSP/Source/FilteringFunctions/arm_correlate_q7.c:87:17: style: Variable 'k' is assigned a value that is never used. [unreadVariable]
  uint32_t j, k = 0U, count, blkCnt, outBlockSize, blockSize1, blockSize2, blockSize3;  /* loop counter                 */
                ^
Firmware/mock/nucleof030r8/ir_sensor_mock/Drivers/CMSIS/DSP/Source/FilteringFunctions/arm_fir_decimate_f32.c:147:14: style: The scope of the variable 'px0' can be reduced. [variableScope]
  float32_t *px0, *px1, *px2, *px3;
             ^
Firmware/mock/nucleof030r8/ir_sensor_mock/Drivers/CMSIS/DSP/Source/FilteringFunctions/arm_fir_decimate_f32.c:147:20: style: The scope of the variable 'px1' can be reduced. [variableScope]
  float32_t *px0, *px1, *px2, *px3;
                   ^
Firmware/mock/nucleof030r8/ir_sensor_mock/Drivers/CMSIS/DSP/Source/FilteringFunctions/arm_fir_decimate_f32.c:147:26: style: The scope of the variable 'px2' can be reduced. [variableScope]
  float32_t *px0, *px1, *px2, *px3;
                         ^
Firmware/mock/nucleof030r8/ir_sensor_mock/Drivers/CMSIS/DSP/Source/FilteringFunctions/arm_fir_decimate_f32.c:147:32: style: The scope of the variable 'px3' can be reduced. [variableScope]
  float32_t *px0, *px1, *px2, *px3;
                               ^
Firmware/mock/nucleof030r8/ir_sensor_mock/Drivers/CMSIS/DSP/Source/FilteringFunctions/arm_fir_decimate_fast_q15.c:77:10: style: The scope of the variable 'px' can be reduced. [variableScope]
  q15_t *px;                                     /* Temporary pointer for state buffer */
         ^
Firmware/mock/nucleof030r8/ir_sensor_mock/Drivers/CMSIS/DSP/Source/FilteringFunctions/arm_fir_decimate_fast_q15.c:82:10: style: The scope of the variable 'px0' can be reduced. [variableScope]
  q15_t *px0, *px1;
         ^
Firmware/mock/nucleof030r8/ir_sensor_mock/Drivers/CMSIS/DSP/Source/FilteringFunctions/arm_fir_decimate_fast_q15.c:82:16: style: The scope of the variable 'px1' can be reduced. [variableScope]
  q15_t *px0, *px1;
               ^
Firmware/mock/nucleof030r8/ir_sensor_mock/Drivers/CMSIS/DSP/Source/FilteringFunctions/arm_fir_decimate_fast_q15.c:317:10: style: The scope of the variable 'px' can be reduced. [variableScope]
  q15_t *px;                                     /* Temporary pointer for state buffer */
         ^
Firmware/mock/nucleof030r8/ir_sensor_mock/Drivers/CMSIS/DSP/Source/FilteringFunctions/arm_fir_decimate_fast_q15.c:322:10: style: The scope of the variable 'px0' can be reduced. [variableScope]
  q15_t *px0, *px1;
         ^
Firmware/mock/nucleof030r8/ir_sensor_mock/Drivers/CMSIS/DSP/Source/FilteringFunctions/arm_fir_decimate_fast_q15.c:322:16: style: The scope of the variable 'px1' can be reduced. [variableScope]
  q15_t *px0, *px1;
               ^
Firmware/mock/nucleof030r8/ir_sensor_mock/Drivers/CMSIS/DSP/Source/FilteringFunctions/arm_fir_decimate_fast_q31.c:74:10: style: The scope of the variable 'px' can be reduced. [variableScope]
  q31_t *px;                                     /* Temporary pointers for state buffer */
         ^
Firmware/mock/nucleof030r8/ir_sensor_mock/Drivers/CMSIS/DSP/Source/FilteringFunctions/arm_fir_decimate_fast_q31.c:82:10: style: The scope of the variable 'px0' can be reduced. [variableScope]
  q31_t *px0, *px1;
         ^
Firmware/mock/nucleof030r8/ir_sensor_mock/Drivers/CMSIS/DSP/Source/FilteringFunctions/arm_fir_decimate_fast_q31.c:82:16: style: The scope of the variable 'px1' can be reduced. [variableScope]
  q31_t *px0, *px1;
               ^
Firmware/mock/nucleof030r8/ir_sensor_mock/Drivers/CMSIS/DSP/Source/FilteringFunctions/arm_fir_decimate_q15.c:592:10: style: The scope of the variable 'px' can be reduced. [variableScope]
  q15_t *px;                                     /* Temporary pointer for state buffer */
         ^
Firmware/mock/nucleof030r8/ir_sensor_mock/Drivers/CMSIS/DSP/Source/FilteringFunctions/arm_fir_decimate_q15.c:593:10: style: The scope of the variable 'pb' can be reduced. [variableScope]
  q15_t *pb;                                     /* Temporary pointer coefficient buffer */
         ^
Firmware/mock/nucleof030r8/ir_sensor_mock/Drivers/CMSIS/DSP/Source/FilteringFunctions/arm_fir_decimate_q15.c:597:23: style: The scope of the variable 'tapCnt' can be reduced. [variableScope]
  uint32_t i, blkCnt, tapCnt, outBlockSize = blockSize / S->M;  /* Loop counters */
                      ^
Firmware/mock/nucleof030r8/ir_sensor_mock/Drivers/CMSIS/DSP/Source/FilteringFunctions/arm_fir_decimate_q15.c:74:10: style: The scope of the variable 'px' can be reduced. [variableScope]
  q15_t *px;                                     /* Temporary pointer for state buffer */
         ^
Firmware/mock/nucleof030r8/ir_sensor_mock/Drivers/CMSIS/DSP/Source/FilteringFunctions/arm_fir_decimate_q15.c:79:10: style: The scope of the variable 'px0' can be reduced. [variableScope]
  q15_t *px0, *px1;
         ^
Firmware/mock/nucleof030r8/ir_sensor_mock/Drivers/CMSIS/DSP/Source/FilteringFunctions/arm_fir_decimate_q15.c:79:16: style: The scope of the variable 'px1' can be reduced. [variableScope]
  q15_t *px0, *px1;
               ^
Firmware/mock/nucleof030r8/ir_sensor_mock/Drivers/CMSIS/DSP/Source/FilteringFunctions/arm_fir_decimate_q15.c:314:10: style: The scope of the variable 'px' can be reduced. [variableScope]
  q15_t *px;                                     /* Temporary pointer for state buffer */
         ^
Firmware/mock/nucleof030r8/ir_sensor_mock/Drivers/CMSIS/DSP/Source/FilteringFunctions/arm_fir_decimate_q15.c:319:10: style: The scope of the variable 'px0' can be reduced. [variableScope]
  q15_t *px0, *px1;
         ^
Firmware/mock/nucleof030r8/ir_sensor_mock/Drivers/CMSIS/DSP/Source/FilteringFunctions/arm_fir_decimate_q15.c:319:16: style: The scope of the variable 'px1' can be reduced. [variableScope]
  q15_t *px0, *px1;
               ^
Firmware/mock/nucleof030r8/ir_sensor_mock/Drivers/CMSIS/DSP/Source/FilteringFunctions/arm_fir_f32.c:566:13: style: The scope of the variable 'i' can be reduced. [variableScope]
   uint32_t i, tapCnt, blkCnt;                    /* Loop counters */
            ^
Firmware/mock/nucleof030r8/ir_sensor_mock/Drivers/CMSIS/DSP/Source/FilteringFunctions/arm_fir_f32.c:479:15: style: The scope of the variable 'px' can be reduced. [variableScope]
   float32_t *px, *pb;                            /* Temporary pointers for state and coefficient buffers */
              ^
Firmware/mock/nucleof030r8/ir_sensor_mock/Drivers/CMSIS/DSP/Source/FilteringFunctions/arm_fir_f32.c:479:20: style: The scope of the variable 'pb' can be reduced. [variableScope]
   float32_t *px, *pb;                            /* Temporary pointers for state and coefficient buffers */
                   ^
Firmware/mock/nucleof030r8/ir_sensor_mock/Drivers/CMSIS/DSP/Source/FilteringFunctions/arm_fir_f32.c:481:13: style: The scope of the variable 'i' can be reduced. [variableScope]
   uint32_t i, tapCnt, blkCnt;                    /* Loop counters */
            ^
Firmware/mock/nucleof030r8/ir_sensor_mock/Drivers/CMSIS/DSP/Source/FilteringFunctions/arm_fir_f32.c:137:13: style: The scope of the variable 'i' can be reduced. [variableScope]
   uint32_t i, tapCnt, blkCnt;                    /* Loop counters */
            ^
Firmware/mock/nucleof030r8/ir_sensor_mock/Drivers/CMSIS/DSP/Source/FilteringFunctions/arm_fir_interpolate_f32.c:483:12: style: The scope of the variable 'i' can be reduced. [variableScope]
  uint32_t i, blkCnt;                            /* Loop counters */
           ^
Firmware/mock/nucleof030r8/ir_sensor_mock/Drivers/CMSIS/DSP/Source/FilteringFunctions/arm_fir_interpolate_q31.c:402:12: style: The scope of the variable 'i' can be reduced. [variableScope]
  uint32_t i, blkCnt;                            /* Loop counters */
           ^
Firmware/mock/nucleof030r8/ir_sensor_mock/Drivers/CMSIS/DSP/Source/FilteringFunctions/arm_fir_lattice_f32.c:423:20: style: The scope of the variable 'stageCnt' can be reduced. [variableScope]
  uint32_t blkCnt, stageCnt;                     /* temporary variables for counts */
                   ^
Firmware/mock/nucleof030r8/ir_sensor_mock/Drivers/CMSIS/DSP/Source/FilteringFunctions/arm_fir_lattice_f32.c:142:10: style: Variable 'gcurr1' is assigned a value that is never used. [unreadVariable]
  gcurr1 = 0.0f;
         ^
Firmware/mock/nucleof030r8/ir_sensor_mock/Drivers/CMSIS/DSP/Source/FilteringFunctions/arm_fir_lattice_q15.c:444:20: style: The scope of the variable 'stageCnt' can be reduced. [variableScope]
  uint32_t blkCnt, stageCnt;                     /* temporary variables for counts */
                   ^
Firmware/mock/nucleof030r8/ir_sensor_mock/Drivers/CMSIS/DSP/Source/FilteringFunctions/arm_fir_lattice_q15.c:66:34: style: Variable 'gcurnt1' is assigned a value that is never used. [unreadVariable]
  q31_t fcurnt1, fnext1, gcurnt1 = 0, gnext1;    /* temporary variables for first sample in loop unrolling */
                                 ^
Firmware/mock/nucleof030r8/ir_sensor_mock/Drivers/CMSIS/DSP/Source/FilteringFunctions/arm_fir_lattice_q31.c:266:10: style: The scope of the variable 'px' can be reduced. [variableScope]
  q31_t *px;                                     /* temporary state pointer */
         ^
Firmware/mock/nucleof030r8/ir_sensor_mock/Drivers/CMSIS/DSP/Source/FilteringFunctions/arm_fir_lattice_q31.c:267:10: style: The scope of the variable 'pk' can be reduced. [variableScope]
  q31_t *pk;                                     /* temporary coefficient pointer */
         ^
Firmware/mock/nucleof030r8/ir_sensor_mock/Drivers/CMSIS/DSP/Source/FilteringFunctions/arm_fir_lattice_q31.c:270:20: style: The scope of the variable 'stageCnt' can be reduced. [variableScope]
  uint32_t blkCnt, stageCnt;                     /* temporary variables for counts */
                   ^
Firmware/mock/nucleof030r8/ir_sensor_mock/Drivers/CMSIS/DSP/Source/FilteringFunctions/arm_fir_lattice_q31.c:68:32: style: Variable 'gcurr1' is assigned a value that is never used. [unreadVariable]
  q31_t fcurr1, fnext1, gcurr1 = 0, gnext1;      /* temporary variables for first sample in loop unrolling */
                               ^
Firmware/mock/nucleof030r8/ir_sensor_mock/Drivers/CMSIS/DSP/Source/FilteringFunctions/arm_fir_q15.c:603:10: style: The scope of the variable 'px' can be reduced. [variableScope]
  q15_t *px;                                     /* Temporary pointer for state buffer */
         ^
Firmware/mock/nucleof030r8/ir_sensor_mock/Drivers/CMSIS/DSP/Source/FilteringFunctions/arm_fir_q15.c:604:10: style: The scope of the variable 'pb' can be reduced. [variableScope]
  q15_t *pb;                                     /* Temporary pointer for coefficient buffer */
         ^
Firmware/mock/nucleof030r8/ir_sensor_mock/Drivers/CMSIS/DSP/Source/FilteringFunctions/arm_fir_q31.c:279:10: style: The scope of the variable 'px' can be reduced. [variableScope]
  q31_t *px;                                     /* Temporary pointer for state */
         ^
Firmware/mock/nucleof030r8/ir_sensor_mock/Drivers/CMSIS/DSP/Source/FilteringFunctions/arm_fir_q31.c:280:10: style: The scope of the variable 'pb' can be reduced. [variableScope]
  q31_t *pb;                                     /* Temporary pointer for coefficient buffer */
         ^
Firmware/mock/nucleof030r8/ir_sensor_mock/Drivers/CMSIS/DSP/Source/FilteringFunctions/arm_fir_q31.c:283:12: style: The scope of the variable 'i' can be reduced. [variableScope]
  uint32_t i, tapCnt, blkCnt;                    /* Loop counters */
           ^
Firmware/mock/nucleof030r8/ir_sensor_mock/Drivers/CMSIS/DSP/Source/FilteringFunctions/arm_fir_q7.c:313:9: style: The scope of the variable 'px' can be reduced. [variableScope]
  q7_t *px, *pb;                                 /* Temporary pointers to state and coeff */
        ^
Firmware/mock/nucleof030r8/ir_sensor_mock/Drivers/CMSIS/DSP/Source/FilteringFunctions/arm_fir_q7.c:313:14: style: The scope of the variable 'pb' can be reduced. [variableScope]
  q7_t *px, *pb;                                 /* Temporary pointers to state and coeff */
             ^
Firmware/mock/nucleof030r8/ir_sensor_mock/Drivers/CMSIS/DSP/Source/FilteringFunctions/arm_fir_q7.c:314:13: style: Variable 'acc' is assigned a value that is never used. [unreadVariable]
  q31_t acc = 0;                                 /* Accumlator */
            ^
Firmware/mock/nucleof030r8/ir_sensor_mock/Drivers/CMSIS/DSP/Source/FilteringFunctions/arm_fir_sparse_q15.c:382:10: style: Variable 'tapCnt' is reassigned a value before the old one has been used. [redundantAssignment]
  tapCnt = (uint32_t) numTaps - 2U;
         ^
Firmware/mock/nucleof030r8/ir_sensor_mock/Drivers/CMSIS/DSP/Source/FilteringFunctions/arm_fir_sparse_q15.c:333:10: note: tapCnt is assigned
  tapCnt = numTaps;
         ^
Firmware/mock/nucleof030r8/ir_sensor_mock/Drivers/CMSIS/DSP/Source/FilteringFunctions/arm_fir_sparse_q15.c:382:10: note: tapCnt is overwritten
  tapCnt = (uint32_t) numTaps - 2U;
         ^
Firmware/mock/nucleof030r8/ir_sensor_mock/Drivers/CMSIS/DSP/Source/FilteringFunctions/arm_fir_sparse_q15.c:161:10: style: Variable 'tapCnt' is reassigned a value before the old one has been used. [redundantAssignment]
  tapCnt = (uint32_t) numTaps - 2U;
         ^
Firmware/mock/nucleof030r8/ir_sensor_mock/Drivers/CMSIS/DSP/Source/FilteringFunctions/arm_fir_sparse_q15.c:94:10: note: tapCnt is assigned
  tapCnt = numTaps;
         ^
Firmware/mock/nucleof030r8/ir_sensor_mock/Drivers/CMSIS/DSP/Source/FilteringFunctions/arm_fir_sparse_q15.c:161:10: note: tapCnt is overwritten
  tapCnt = (uint32_t) numTaps - 2U;
         ^
Firmware/mock/nucleof030r8/ir_sensor_mock/Drivers/CMSIS/DSP/Source/FilteringFunctions/arm_fir_sparse_q7.c:374:10: style: Variable 'tapCnt' is reassigned a value before the old one has been used. [redundantAssignment]
  tapCnt = (uint32_t) numTaps - 2U;
         ^
Firmware/mock/nucleof030r8/ir_sensor_mock/Drivers/CMSIS/DSP/Source/FilteringFunctions/arm_fir_sparse_q7.c:324:10: note: tapCnt is assigned
  tapCnt = numTaps;
         ^
Firmware/mock/nucleof030r8/ir_sensor_mock/Drivers/CMSIS/DSP/Source/FilteringFunctions/arm_fir_sparse_q7.c:374:10: note: tapCnt is overwritten
  tapCnt = (uint32_t) numTaps - 2U;
         ^
Firmware/mock/nucleof030r8/ir_sensor_mock/Drivers/CMSIS/DSP/Source/FilteringFunctions/arm_fir_sparse_q7.c:166:10: style: Variable 'tapCnt' is reassigned a value before the old one has been used. [redundantAssignment]
  tapCnt = (uint32_t) numTaps - 2U;
         ^
Firmware/mock/nucleof030r8/ir_sensor_mock/Drivers/CMSIS/DSP/Source/FilteringFunctions/arm_fir_sparse_q7.c:99:10: note: tapCnt is assigned
  tapCnt = numTaps;
         ^
Firmware/mock/nucleof030r8/ir_sensor_mock/Drivers/CMSIS/DSP/Source/FilteringFunctions/arm_fir_sparse_q7.c:166:10: note: tapCnt is overwritten
  tapCnt = (uint32_t) numTaps - 2U;
         ^
Firmware/mock/nucleof030r8/ir_sensor_mock/Drivers/CMSIS/DSP/Source/FilteringFunctions/arm_iir_lattice_f32.c:345:14: style: The scope of the variable 'px1' can be reduced. [variableScope]
  float32_t *px1, *px2, *pk, *pv;                /* temporary pointers for state and coef */
             ^
Firmware/mock/nucleof030r8/ir_sensor_mock/Drivers/CMSIS/DSP/Source/FilteringFunctions/arm_iir_lattice_f32.c:345:20: style: The scope of the variable 'px2' can be reduced. [variableScope]
  float32_t *px1, *px2, *pk, *pv;                /* temporary pointers for state and coef */
                   ^
Firmware/mock/nucleof030r8/ir_sensor_mock/Drivers/CMSIS/DSP/Source/FilteringFunctions/arm_iir_lattice_f32.c:345:26: style: The scope of the variable 'pk' can be reduced. [variableScope]
  float32_t *px1, *px2, *pk, *pv;                /* temporary pointers for state and coef */
                         ^
Firmware/mock/nucleof030r8/ir_sensor_mock/Drivers/CMSIS/DSP/Source/FilteringFunctions/arm_iir_lattice_f32.c:345:31: style: The scope of the variable 'pv' can be reduced. [variableScope]
  float32_t *px1, *px2, *pk, *pv;                /* temporary pointers for state and coef */
                              ^
Firmware/mock/nucleof030r8/ir_sensor_mock/Drivers/CMSIS/DSP/Source/FilteringFunctions/arm_iir_lattice_f32.c:131:14: style: The scope of the variable 'px1' can be reduced. [variableScope]
  float32_t *px1, *px2, *pk, *pv;                /* temporary pointers for state and coef */
             ^
Firmware/mock/nucleof030r8/ir_sensor_mock/Drivers/CMSIS/DSP/Source/FilteringFunctions/arm_iir_lattice_f32.c:131:20: style: The scope of the variable 'px2' can be reduced. [variableScope]
  float32_t *px1, *px2, *pk, *pv;                /* temporary pointers for state and coef */
                   ^
Firmware/mock/nucleof030r8/ir_sensor_mock/Drivers/CMSIS/DSP/Source/FilteringFunctions/arm_iir_lattice_f32.c:131:26: style: The scope of the variable 'pk' can be reduced. [variableScope]
  float32_t *px1, *px2, *pk, *pv;                /* temporary pointers for state and coef */
                         ^
Firmware/mock/nucleof030r8/ir_sensor_mock/Drivers/CMSIS/DSP/Source/FilteringFunctions/arm_iir_lattice_f32.c:131:31: style: The scope of the variable 'pv' can be reduced. [variableScope]
  float32_t *px1, *px2, *pk, *pv;                /* temporary pointers for state and coef */
                              ^
Firmware/mock/nucleof030r8/ir_sensor_mock/Drivers/CMSIS/DSP/Source/FilteringFunctions/arm_iir_lattice_q15.c:358:20: style: The scope of the variable 'tapCnt' can be reduced. [variableScope]
  uint32_t blkCnt, tapCnt;                       /* Temporary variables for counts */
                   ^
Firmware/mock/nucleof030r8/ir_sensor_mock/Drivers/CMSIS/DSP/Source/FilteringFunctions/arm_iir_lattice_q15.c:359:10: style: The scope of the variable 'px1' can be reduced. [variableScope]
  q15_t *px1, *px2, *pk, *pv;                    /* temporary pointers for state and coef */
         ^
Firmware/mock/nucleof030r8/ir_sensor_mock/Drivers/CMSIS/DSP/Source/FilteringFunctions/arm_iir_lattice_q15.c:359:16: style: The scope of the variable 'px2' can be reduced. [variableScope]
  q15_t *px1, *px2, *pk, *pv;                    /* temporary pointers for state and coef */
               ^
Firmware/mock/nucleof030r8/ir_sensor_mock/Drivers/CMSIS/DSP/Source/FilteringFunctions/arm_iir_lattice_q15.c:359:22: style: The scope of the variable 'pk' can be reduced. [variableScope]
  q15_t *px1, *px2, *pk, *pv;                    /* temporary pointers for state and coef */
                     ^
Firmware/mock/nucleof030r8/ir_sensor_mock/Drivers/CMSIS/DSP/Source/FilteringFunctions/arm_iir_lattice_q15.c:359:27: style: The scope of the variable 'pv' can be reduced. [variableScope]
  q15_t *px1, *px2, *pk, *pv;                    /* temporary pointers for state and coef */
                          ^
Firmware/mock/nucleof030r8/ir_sensor_mock/Drivers/CMSIS/DSP/Source/FilteringFunctions/arm_iir_lattice_q15.c:355:33: style: Variable 'gcurr' is assigned a value that is never used. [unreadVariable]
  q31_t fcurr, fnext = 0, gcurr = 0, gnext;      /* Temporary variables for lattice stages */
                                ^
Firmware/mock/nucleof030r8/ir_sensor_mock/Drivers/CMSIS/DSP/Source/FilteringFunctions/arm_iir_lattice_q15.c:71:29: style: Variable 'gcurr' is assigned a value that is never used. [unreadVariable]
  q31_t fcurr, fnext, gcurr = 0, gnext;          /* Temporary variables for lattice stages */
                            ^
Firmware/mock/nucleof030r8/ir_sensor_mock/Drivers/CMSIS/DSP/Source/FilteringFunctions/arm_iir_lattice_q31.c:64:33: style: Variable 'gcurr' is assigned a value that is never used. [unreadVariable]
  q31_t fcurr, fnext = 0, gcurr = 0, gnext;      /* Temporary variables for lattice stages */
                                ^
Firmware/mock/nucleof030r8/ir_sensor_mock/Drivers/CMSIS/DSP/Source/FilteringFunctions/arm_iir_lattice_q31.c:64:22: style: Variable 'fnext' is assigned a value that is never used. [unreadVariable]
  q31_t fcurr, fnext = 0, gcurr = 0, gnext;      /* Temporary variables for lattice stages */
                     ^
Firmware/mock/nucleof030r8/ir_sensor_mock/Drivers/CMSIS/DSP/Source/FilteringFunctions/arm_lms_f32.c:185:15: style: Variable 'w' is assigned a value that is never used. [unreadVariable]
  float32_t w = 0.0f;                            /* weight factor */
              ^
Firmware/mock/nucleof030r8/ir_sensor_mock/Drivers/CMSIS/DSP/Source/FilteringFunctions/arm_lms_f32.c:187:5: style: Variable 'e' is assigned a value that is never used. [unreadVariable]
  e = 0.0f;
    ^
Firmware/mock/nucleof030r8/ir_sensor_mock/Drivers/CMSIS/DSP/Source/FilteringFunctions/arm_lms_f32.c:188:5: style: Variable 'd' is assigned a value that is never used. [unreadVariable]
  d = 0.0f;
    ^
Firmware/mock/nucleof030r8/ir_sensor_mock/Drivers/CMSIS/DSP/Source/FilteringFunctions/arm_lms_norm_f32.c:181:5: style: Variable 'e' is assigned a value that is never used. [unreadVariable]
  e = 0.0f;
    ^
Firmware/mock/nucleof030r8/ir_sensor_mock/Drivers/CMSIS/DSP/Source/FilteringFunctions/arm_lms_norm_f32.c:182:5: style: Variable 'd' is assigned a value that is never used. [unreadVariable]
  d = 0.0f;
    ^
Firmware/mock/nucleof030r8/ir_sensor_mock/Drivers/CMSIS/DSP/Source/FilteringFunctions/arm_lms_norm_f32.c:183:5: style: Variable 'w' is assigned a value that is never used. [unreadVariable]
  w = 0.0f;
    ^
Firmware/mock/nucleof030r8/ir_sensor_mock/Drivers/CMSIS/DSP/Source/FilteringFunctions/arm_lms_norm_q15.c:84:11: style: Variable 'e' is assigned a value that is never used. [unreadVariable]
  q15_t e = 0, d = 0;                            /* error, reference data sample */
          ^
Firmware/mock/nucleof030r8/ir_sensor_mock/Drivers/CMSIS/DSP/Source/FilteringFunctions/arm_lms_norm_q15.c:84:18: style: Variable 'd' is assigned a value that is never used. [unreadVariable]
  q15_t e = 0, d = 0;                            /* error, reference data sample */
                 ^
Firmware/mock/nucleof030r8/ir_sensor_mock/Drivers/CMSIS/DSP/Source/FilteringFunctions/arm_lms_norm_q15.c:85:11: style: Variable 'w' is assigned a value that is never used. [unreadVariable]
  q15_t w = 0, in;                               /* weight factor and state */
          ^
Firmware/mock/nucleof030r8/ir_sensor_mock/Drivers/CMSIS/DSP/Source/FilteringFunctions/arm_lms_norm_q31.c:85:11: style: Variable 'e' is assigned a value that is never used. [unreadVariable]
  q31_t e = 0, d = 0;                            /* error, reference data sample */
          ^
Firmware/mock/nucleof030r8/ir_sensor_mock/Drivers/CMSIS/DSP/Source/FilteringFunctions/arm_lms_norm_q31.c:85:18: style: Variable 'd' is assigned a value that is never used. [unreadVariable]
  q31_t e = 0, d = 0;                            /* error, reference data sample */
                 ^
Firmware/mock/nucleof030r8/ir_sensor_mock/Drivers/CMSIS/DSP/Source/FilteringFunctions/arm_lms_norm_q31.c:86:11: style: Variable 'w' is assigned a value that is never used. [unreadVariable]
  q31_t w = 0, in;                               /* weight factor and state */
          ^
Firmware/mock/nucleof030r8/ir_sensor_mock/Drivers/CMSIS/DSP/Source/FilteringFunctions/arm_lms_q15.c:79:11: style: Variable 'e' is assigned a value that is never used. [unreadVariable]
  q15_t e = 0;                                   /* error of data sample */
          ^
Firmware/mock/nucleof030r8/ir_sensor_mock/Drivers/CMSIS/DSP/Source/FilteringFunctions/arm_lms_q31.c:82:11: style: Variable 'e' is assigned a value that is never used. [unreadVariable]
  q31_t e = 0;                                   /* error of data sample */
          ^
Firmware/mock/nucleof030r8/ir_sensor_mock/Drivers/CMSIS/DSP/Source/MatrixFunctions/arm_mat_cmplx_mult_f32.c:67:19: style: Variable 'pIn1' is assigned a value that is never used. [unreadVariable]
  float32_t *pIn1 = pSrcA->pData;                /* input data matrix pointer A */
                  ^
Firmware/mock/nucleof030r8/ir_sensor_mock/Drivers/CMSIS/DSP/Source/MatrixFunctions/arm_mat_cmplx_mult_f32.c:68:19: style: Variable 'pIn2' is assigned a value that is never used. [unreadVariable]
  float32_t *pIn2 = pSrcB->pData;                /* input data matrix pointer B */
                  ^
Firmware/mock/nucleof030r8/ir_sensor_mock/Drivers/CMSIS/DSP/Source/MatrixFunctions/arm_mat_cmplx_mult_q15.c:85:15: style: Variable 'pInA' is assigned a value that is never used. [unreadVariable]
  q15_t *pInA = pSrcA->pData;                    /* input data matrix pointer A of Q15 type */
              ^
Firmware/mock/nucleof030r8/ir_sensor_mock/Drivers/CMSIS/DSP/Source/MatrixFunctions/arm_mat_cmplx_mult_q31.c:69:15: style: Variable 'pIn1' is assigned a value that is never used. [unreadVariable]
  q31_t *pIn1 = pSrcA->pData;                    /* input data matrix pointer A */
              ^
Firmware/mock/nucleof030r8/ir_sensor_mock/Drivers/CMSIS/DSP/Source/MatrixFunctions/arm_mat_cmplx_mult_q31.c:70:15: style: Variable 'pIn2' is assigned a value that is never used. [unreadVariable]
  q31_t *pIn2 = pSrcB->pData;                    /* input data matrix pointer B */
              ^
Firmware/mock/nucleof030r8/ir_sensor_mock/Drivers/CMSIS/DSP/Source/MatrixFunctions/arm_mat_mult_f32.c:71:19: style: Variable 'pIn1' is assigned a value that is never used. [unreadVariable]
  float32_t *pIn1 = pSrcA->pData;                /* input data matrix pointer A */
                  ^
Firmware/mock/nucleof030r8/ir_sensor_mock/Drivers/CMSIS/DSP/Source/MatrixFunctions/arm_mat_mult_f32.c:72:19: style: Variable 'pIn2' is assigned a value that is never used. [unreadVariable]
  float32_t *pIn2 = pSrcB->pData;                /* input data matrix pointer B */
                  ^
Firmware/mock/nucleof030r8/ir_sensor_mock/Drivers/CMSIS/DSP/Source/MatrixFunctions/arm_mat_mult_fast_q15.c:81:15: style: Variable 'pInA' is assigned a value that is never used. [unreadVariable]
  q15_t *pInA = pSrcA->pData;                    /* input data matrix pointer A of Q15 type */
              ^
Firmware/mock/nucleof030r8/ir_sensor_mock/Drivers/CMSIS/DSP/Source/MatrixFunctions/arm_mat_mult_fast_q15.c:97:14: style: Variable 'j' is assigned a value that is never used. [unreadVariable]
  uint32_t j = 0;
             ^
Firmware/mock/nucleof030r8/ir_sensor_mock/Drivers/CMSIS/DSP/Source/MatrixFunctions/arm_mat_mult_fast_q15.c:469:9: style: Variable 'i' is assigned a value that is never used. [unreadVariable]
      i = 0U;
        ^
Firmware/mock/nucleof030r8/ir_sensor_mock/Drivers/CMSIS/DSP/Source/MatrixFunctions/arm_mat_mult_fast_q31.c:76:15: style: Variable 'pInA' is assigned a value that is never used. [unreadVariable]
  q31_t *pInA = pSrcA->pData;                    /* input data matrix pointer A */
              ^
Firmware/mock/nucleof030r8/ir_sensor_mock/Drivers/CMSIS/DSP/Source/MatrixFunctions/arm_mat_mult_fast_q31.c:77:15: style: Variable 'pInB' is assigned a value that is never used. [unreadVariable]
  q31_t *pInB = pSrcB->pData;                    /* input data matrix pointer B */
              ^
Firmware/mock/nucleof030r8/ir_sensor_mock/Drivers/CMSIS/DSP/Source/MatrixFunctions/arm_mat_mult_fast_q31.c:127:12: style: Variable 'pInB' is assigned a value that is never used. [unreadVariable]
      pInB = pSrcB->pData;
           ^
Firmware/mock/nucleof030r8/ir_sensor_mock/Drivers/CMSIS/DSP/Source/MatrixFunctions/arm_mat_mult_q15.c:362:15: style: Variable 'pIn1' is assigned a value that is never used. [unreadVariable]
  q15_t *pIn1 = pSrcA->pData;                    /* input data matrix pointer A */
              ^
Firmware/mock/nucleof030r8/ir_sensor_mock/Drivers/CMSIS/DSP/Source/MatrixFunctions/arm_mat_mult_q15.c:363:15: style: Variable 'pIn2' is assigned a value that is never used. [unreadVariable]
  q15_t *pIn2 = pSrcB->pData;                    /* input data matrix pointer B */
              ^
Firmware/mock/nucleof030r8/ir_sensor_mock/Drivers/CMSIS/DSP/Source/MatrixFunctions/arm_mat_mult_q15.c:80:15: style: Variable 'pInA' is assigned a value that is never used. [unreadVariable]
  q15_t *pInA = pSrcA->pData;                    /* input data matrix pointer A of Q15 type */
              ^
Firmware/mock/nucleof030r8/ir_sensor_mock/Drivers/CMSIS/DSP/Source/MatrixFunctions/arm_mat_mult_q31.c:71:15: style: Variable 'pIn1' is assigned a value that is never used. [unreadVariable]
  q31_t *pIn1 = pSrcA->pData;                    /* input data matrix pointer A */
              ^
Firmware/mock/nucleof030r8/ir_sensor_mock/Drivers/CMSIS/DSP/Source/MatrixFunctions/arm_mat_mult_q31.c:72:15: style: Variable 'pIn2' is assigned a value that is never used. [unreadVariable]
  q31_t *pIn2 = pSrcB->pData;                    /* input data matrix pointer B */
              ^
Firmware/mock/nucleof030r8/ir_sensor_mock/Drivers/CMSIS/DSP/Source/MatrixFunctions/arm_mat_scale_q15.c:115:12: style: Variable 'inA1' is assigned a value that is never used. [unreadVariable]
      inA1 = _SIMD32_OFFSET(pIn + 4);
           ^
Firmware/mock/nucleof030r8/ir_sensor_mock/Drivers/CMSIS/DSP/Source/MatrixFunctions/arm_mat_scale_q15.c:117:12: style: Variable 'inA2' is assigned a value that is never used. [unreadVariable]
      inA2 = _SIMD32_OFFSET(pIn + 6);
           ^
Firmware/mock/nucleof030r8/ir_sensor_mock/Drivers/CMSIS/DSP/Source/MatrixFunctions/arm_mat_trans_q15.c:53:15: style: Variable 'pOut' is assigned a value that is never used. [unreadVariable]
  q15_t *pOut = pDst->pData;                     /* output data matrix pointer */
              ^
Firmware/mock/nucleof030r8/ir_sensor_mock/Drivers/CMSIS/DSP/Source/TransformFunctions/arm_cfft_q31.c:139:17: style: The scope of the variable 'l' can be reduced. [variableScope]
    uint32_t i, l;
                ^
Firmware/mock/nucleof030r8/ir_sensor_mock/Drivers/CMSIS/DSP/Source/TransformFunctions/arm_cfft_q31.c:199:17: style: The scope of the variable 'l' can be reduced. [variableScope]
    uint32_t i, l;
                ^
Firmware/mock/nucleof030r8/ir_sensor_mock/Drivers/CMSIS/DSP/Source/TransformFunctions/arm_cfft_radix2_q15.c:412:3: style: Assignment of function parameter has no effect outside the function. [uselessAssignmentArg]
  twidCoefModifier = twidCoefModifier << 1U;
  ^
Firmware/mock/nucleof030r8/ir_sensor_mock/Drivers/CMSIS/DSP/Source/TransformFunctions/arm_cfft_radix2_q15.c:389:12: style: Variable 'cosVal' is assigned a value that is never used. [unreadVariable]
    cosVal = pCoef[ia * 2];
           ^
Firmware/mock/nucleof030r8/ir_sensor_mock/Drivers/CMSIS/DSP/Source/TransformFunctions/arm_cfft_radix2_q15.c:390:12: style: Variable 'sinVal' is assigned a value that is never used. [unreadVariable]
    sinVal = pCoef[(ia * 2) + 1];
           ^
Firmware/mock/nucleof030r8/ir_sensor_mock/Drivers/CMSIS/DSP/Source/TransformFunctions/arm_cfft_radix2_q15.c:412:20: style: Variable 'twidCoefModifier' is assigned a value that is never used. [unreadVariable]
  twidCoefModifier = twidCoefModifier << 1U;
                   ^
Firmware/mock/nucleof030r8/ir_sensor_mock/Drivers/CMSIS/DSP/Source/TransformFunctions/arm_cfft_radix2_q15.c:705:10: style: Variable 'cosVal' is assigned a value that is never used. [unreadVariable]
  cosVal = pCoef[ia * 2];
         ^
Firmware/mock/nucleof030r8/ir_sensor_mock/Drivers/CMSIS/DSP/Source/TransformFunctions/arm_cfft_radix2_q15.c:706:10: style: Variable 'sinVal' is assigned a value that is never used. [unreadVariable]
  sinVal = pCoef[(ia * 2) + 1];
         ^
Firmware/mock/nucleof030r8/ir_sensor_mock/Drivers/CMSIS/DSP/Source/TransformFunctions/arm_cfft_radix2_q15.c:708:6: style: Variable 'ia' is assigned a value that is never used. [unreadVariable]
  ia = ia + twidCoefModifier;
     ^
Firmware/mock/nucleof030r8/ir_sensor_mock/Drivers/CMSIS/DSP/Source/TransformFunctions/arm_cfft_radix2_q15.c:618:3: style: Assignment of function parameter has no effect outside the function. [uselessAssignmentArg]
  twidCoefModifier = twidCoefModifier << 1U;
  ^
Firmware/mock/nucleof030r8/ir_sensor_mock/Drivers/CMSIS/DSP/Source/TransformFunctions/arm_cfft_radix2_q15.c:262:6: style: Variable 'n1' is reassigned a value before the old one has been used. [redundantAssignment]
  n1 = n2;
     ^
Firmware/mock/nucleof030r8/ir_sensor_mock/Drivers/CMSIS/DSP/Source/TransformFunctions/arm_cfft_radix2_q15.c:107:6: note: n1 is assigned
  n1 = n2;
     ^
Firmware/mock/nucleof030r8/ir_sensor_mock/Drivers/CMSIS/DSP/Source/TransformFunctions/arm_cfft_radix2_q15.c:262:6: note: n1 is overwritten
  n1 = n2;
     ^
Firmware/mock/nucleof030r8/ir_sensor_mock/Drivers/CMSIS/DSP/Source/TransformFunctions/arm_cfft_radix2_q15.c:588:6: style: Variable 'n1' is reassigned a value before the old one has been used. [redundantAssignment]
  n1 = n2;
     ^
Firmware/mock/nucleof030r8/ir_sensor_mock/Drivers/CMSIS/DSP/Source/TransformFunctions/arm_cfft_radix2_q15.c:436:6: note: n1 is assigned
  n1 = n2;
     ^
Firmware/mock/nucleof030r8/ir_sensor_mock/Drivers/CMSIS/DSP/Source/TransformFunctions/arm_cfft_radix2_q15.c:588:6: note: n1 is overwritten
  n1 = n2;
     ^
Firmware/mock/nucleof030r8/ir_sensor_mock/Drivers/CMSIS/DSP/Source/TransformFunctions/arm_cfft_radix2_q15.c:268:6: style: Variable 'ia' is assigned a value that is never used. [unreadVariable]
  ia = ia + twidCoefModifier;
     ^
Firmware/mock/nucleof030r8/ir_sensor_mock/Drivers/CMSIS/DSP/Source/TransformFunctions/arm_cfft_radix2_q15.c:618:20: style: Variable 'twidCoefModifier' is assigned a value that is never used. [unreadVariable]
  twidCoefModifier = twidCoefModifier << 1U;
                   ^
Firmware/mock/nucleof030r8/ir_sensor_mock/Drivers/CMSIS/DSP/Source/TransformFunctions/arm_cfft_radix2_q31.c:178:7: style: Variable 'n1' is reassigned a value before the old one has been used. [redundantAssignment]
   n1 = n2;
      ^
Firmware/mock/nucleof030r8/ir_sensor_mock/Drivers/CMSIS/DSP/Source/TransformFunctions/arm_cfft_radix2_q31.c:105:7: note: n1 is assigned
   n1 = n2;
      ^
Firmware/mock/nucleof030r8/ir_sensor_mock/Drivers/CMSIS/DSP/Source/TransformFunctions/arm_cfft_radix2_q31.c:178:7: note: n1 is overwritten
   n1 = n2;
      ^
Firmware/mock/nucleof030r8/ir_sensor_mock/Drivers/CMSIS/DSP/Source/TransformFunctions/arm_cfft_radix2_q31.c:301:7: style: Variable 'n1' is reassigned a value before the old one has been used. [redundantAssignment]
   n1 = n2;
      ^
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
  n1 = n2;
     ^
Firmware/mock/nucleof030r8/ir_sensor_mock/Drivers/CMSIS/DSP/Source/TransformFunctions/arm_cfft_radix8_f32.c:51:13: style: The scope of the variable 'ia1' can be reduced. [variableScope]
   uint32_t ia1, ia2, ia3, ia4, ia5, ia6, ia7;
            ^
Firmware/mock/nucleof030r8/ir_sensor_mock/Drivers/CMSIS/DSP/Source/TransformFunctions/arm_cfft_radix8_f32.c:52:13: style: The scope of the variable 'i1' can be reduced. [variableScope]
   uint32_t i1, i2, i3, i4, i5, i6, i7, i8;
            ^
Firmware/mock/nucleof030r8/ir_sensor_mock/Drivers/CMSIS/DSP/Source/TransformFunctions/arm_cfft_radix8_f32.c:54:13: style: The scope of the variable 'n1' can be reduced. [variableScope]
   uint32_t n1, n2, j;
            ^
Firmware/mock/nucleof030r8/ir_sensor_mock/Drivers/CMSIS/DSP/Source/TransformFunctions/arm_cfft_radix8_f32.c:54:21: style: The scope of the variable 'j' can be reduced. [variableScope]
   uint32_t n1, n2, j;
                    ^
Firmware/mock/nucleof030r8/ir_sensor_mock/Drivers/CMSIS/DSP/Source/TransformFunctions/arm_rfft_fast_f32.c:139:8: style: Redundant initialization for 'pB'. The initialized value is overwritten before it is read. [redundantInitialization]
   pB  =  p + 2*k ;
       ^
Firmware/mock/nucleof030r8/ir_sensor_mock/Drivers/CMSIS/DSP/Source/TransformFunctions/arm_rfft_fast_f32.c:125:18: note: pB is initialized
   float32_t *pB = p;      /* decreasing pointer               */
                 ^
Firmware/mock/nucleof030r8/ir_sensor_mock/Drivers/CMSIS/DSP/Source/TransformFunctions/arm_rfft_fast_f32.c:139:8: note: pB is overwritten
   pB  =  p + 2*k ;
       ^
Firmware/mock/nucleof030r8/ir_sensor_mock/Drivers/CMSIS/DSP/Source/TransformFunctions/arm_rfft_fast_f32.c:54:8: style: Variable 'twR' is assigned a value that is never used. [unreadVariable]
   twR = *pCoeff++ ;
       ^
Firmware/mock/nucleof030r8/ir_sensor_mock/Drivers/CMSIS/DSP/Source/TransformFunctions/arm_rfft_fast_f32.c:55:8: style: Variable 'twI' is assigned a value that is never used. [unreadVariable]
   twI = *pCoeff++ ;
       ^
Firmware/mock/nucleof030r8/ir_sensor_mock/Drivers/CMSIS/DSP/Source/TransformFunctions/arm_rfft_q15.c:80:14: style: The scope of the variable 'i' can be reduced. [variableScope]
    uint32_t i;
             ^
Firmware/mock/nucleof030r8/ir_sensor_mock/Drivers/CMSIS/DSP/Source/TransformFunctions/arm_rfft_q15.c:159:11: style: Variable 'i' is reassigned a value before the old one has been used. [redundantAssignment]
    for(i = fftLen - 1; i > 0; i--)
          ^
Firmware/mock/nucleof030r8/ir_sensor_mock/Drivers/CMSIS/DSP/Source/TransformFunctions/arm_rfft_q15.c:155:7: note: i is assigned
    i = 1U;
      ^
Firmware/mock/nucleof030r8/ir_sensor_mock/Drivers/CMSIS/DSP/Source/TransformFunctions/arm_rfft_q15.c:159:11: note: i is overwritten
    for(i = fftLen - 1; i > 0; i--)
          ^
Firmware/mock/nucleof030r8/ir_sensor_mock/Drivers/CMSIS/DSP/Source/TransformFunctions/arm_rfft_q31.c:80:14: style: The scope of the variable 'i' can be reduced. [variableScope]
    uint32_t i;
             ^
Firmware/mock/nucleof030r8/ir_sensor_mock/Drivers/CMSIS/Device/ST/STM32F0xx/Source/Templates/system_stm32f0xx.c:191:0: information: Skipping configuration 'HSE_VALUE' since the value of 'HSE_VALUE' is unknown. Use -D if you want to check it. You can use -U to skip it explicitly. [ConfigurationNotChecked]
      SystemCoreClock = HSE_VALUE;
^
Firmware/mock/nucleof030r8/ir_sensor_mock/Drivers/CMSIS/Device/ST/STM32F0xx/Source/Templates/system_stm32f0xx.c:203:0: information: Skipping configuration 'HSE_VALUE' since the value of 'HSE_VALUE' is unknown. Use -D if you want to check it. You can use -U to skip it explicitly. [ConfigurationNotChecked]
        SystemCoreClock = (HSE_VALUE/predivfactor) * pllmull;
^
Firmware/mock/nucleof030r8/ir_sensor_mock/Drivers/CMSIS/Device/ST/STM32F0xx/Source/Templates/system_stm32f0xx.c:188:0: information: Skipping configuration 'HSI_VALUE' since the value of 'HSI_VALUE' is unknown. Use -D if you want to check it. You can use -U to skip it explicitly. [ConfigurationNotChecked]
      SystemCoreClock = HSI_VALUE;
^
Firmware/mock/nucleof030r8/ir_sensor_mock/Drivers/CMSIS/Device/ST/STM32F0xx/Source/Templates/system_stm32f0xx.c:221:0: information: Skipping configuration 'HSI_VALUE' since the value of 'HSI_VALUE' is unknown. Use -D if you want to check it. You can use -U to skip it explicitly. [ConfigurationNotChecked]
        SystemCoreClock = (HSI_VALUE >> 1) * pllmull;
^
Firmware/mock/nucleof030r8/ir_sensor_mock/Drivers/CMSIS/Device/ST/STM32F0xx/Source/Templates/system_stm32f0xx.c:228:0: information: Skipping configuration 'HSI_VALUE' since the value of 'HSI_VALUE' is unknown. Use -D if you want to check it. You can use -U to skip it explicitly. [ConfigurationNotChecked]
      SystemCoreClock = HSI_VALUE;
^
Firmware/mock/nucleof030r8/ir_sensor_mock/Drivers/CMSIS/NN/Source/ConvolutionFunctions/arm_convolve_1x1_HWC_q7_fast_nonsquare.c:107:15: style: The scope of the variable 'i_ch_out' can be reduced. [variableScope]
    int16_t   i_ch_out;
              ^
Firmware/mock/nucleof030r8/ir_sensor_mock/Drivers/CMSIS/NN/Source/ConvolutionFunctions/arm_depthwise_separable_conv_HWC_q7.c:106:23: style: Variable 'pBias' is assigned a value that is never used. [unreadVariable]
    const q7_t *pBias = bias;
                      ^
Firmware/mock/nucleof030r8/ir_sensor_mock/Drivers/CMSIS/NN/Source/ConvolutionFunctions/arm_depthwise_separable_conv_HWC_q7_nonsquare.c:112:23: style: Variable 'pBias' is assigned a value that is never used. [unreadVariable]
    const q7_t *pBias = bias;
                      ^
Firmware/mock/nucleof030r8/ir_sensor_mock/Drivers/CMSIS/NN/Source/FullyConnectedFunctions/arm_fully_connected_mat_q7_vec_q15.c:84:17: style: The scope of the variable 'pB2' can be reduced. [variableScope]
    const q7_t *pB2;
                ^
Firmware/mock/nucleof030r8/ir_sensor_mock/Drivers/CMSIS/NN/Source/FullyConnectedFunctions/arm_fully_connected_mat_q7_vec_q15.c:87:21: style: Variable 'pA' is assigned a value that is never used. [unreadVariable]
    const q15_t *pA = pV;
                    ^
Firmware/mock/nucleof030r8/ir_sensor_mock/Drivers/CMSIS/NN/Source/FullyConnectedFunctions/arm_fully_connected_mat_q7_vec_q15_opt.c:131:21: style: Variable 'pA' is assigned a value that is never used. [unreadVariable]
    const q15_t *pA = pV;
                    ^
Firmware/mock/nucleof030r8/ir_sensor_mock/Drivers/CMSIS/NN/Source/FullyConnectedFunctions/arm_fully_connected_q15.c:81:22: style: Variable 'pB2' is assigned a value that is never used. [unreadVariable]
    const q15_t *pB2 = pB + dim_vec;
                     ^
Firmware/mock/nucleof030r8/ir_sensor_mock/Drivers/CMSIS/NN/Source/FullyConnectedFunctions/arm_fully_connected_q15_opt.c:114:21: style: Variable 'pA' is assigned a value that is never used. [unreadVariable]
    const q15_t *pA = pV;
                    ^
Firmware/mock/nucleof030r8/ir_sensor_mock/Drivers/CMSIS/NN/Source/FullyConnectedFunctions/arm_fully_connected_q7.c:80:17: style: The scope of the variable 'pB2' can be reduced. [variableScope]
    const q7_t *pB2;
                ^
Firmware/mock/nucleof030r8/ir_sensor_mock/Drivers/CMSIS/NN/Source/PoolingFunctions/arm_pool_q7_HWC.c:66:18: style: Variable 'com.word' is assigned a value that is never used. [unreadVariable]
        com.word = *__SIMD32(pCom)++;
                 ^
Firmware/mock/nucleof030r8/ir_sensor_mock/Drivers/CMSIS/NN/Source/PoolingFunctions/arm_pool_q7_HWC.c:330:21: style: Variable 'count' is assigned a value that is never used. [unreadVariable]
    int16_t   count = 0;
                    ^
Firmware/mock/nucleof030r8/ir_sensor_mock/Drivers/CMSIS/RTOS2/Source/os_systick.c:70:0: information: Skipping configuration 'SysTick;__ARM_ARCH_6M__' since the value of 'SysTick' is unknown. Use -D if you want to check it. You can use -U to skip it explicitly. [ConfigurationNotChecked]
  SysTick->CTRL =  SysTick_CTRL_CLKSOURCE_Msk | SysTick_CTRL_TICKINT_Msk;
^
Firmware/mock/nucleof030r8/ir_sensor_mock/Drivers/CMSIS/RTOS2/Source/os_systick.c:71:0: information: Skipping configuration 'SysTick;__ARM_ARCH_6M__' since the value of 'SysTick' is unknown. Use -D if you want to check it. You can use -U to skip it explicitly. [ConfigurationNotChecked]
  SysTick->LOAD =  load;
^
Firmware/mock/nucleof030r8/ir_sensor_mock/Drivers/CMSIS/RTOS2/Source/os_systick.c:72:0: information: Skipping configuration 'SysTick;__ARM_ARCH_6M__' since the value of 'SysTick' is unknown. Use -D if you want to check it. You can use -U to skip it explicitly. [ConfigurationNotChecked]
  SysTick->VAL  =  0U;
^
Firmware/mock/nucleof030r8/ir_sensor_mock/Drivers/CMSIS/RTOS2/Source/os_systick.c:87:0: information: Skipping configuration 'SysTick;__ARM_ARCH_6M__' since the value of 'SysTick' is unknown. Use -D if you want to check it. You can use -U to skip it explicitly. [ConfigurationNotChecked]
  SysTick->CTRL |=  SysTick_CTRL_ENABLE_Msk;
^
Firmware/mock/nucleof030r8/ir_sensor_mock/Drivers/CMSIS/RTOS2/Source/os_systick.c:93:0: information: Skipping configuration 'SysTick;__ARM_ARCH_6M__' since the value of 'SysTick' is unknown. Use -D if you want to check it. You can use -U to skip it explicitly. [ConfigurationNotChecked]
  SysTick->CTRL &= ~SysTick_CTRL_ENABLE_Msk;
^
Firmware/mock/nucleof030r8/ir_sensor_mock/Drivers/CMSIS/RTOS2/Source/os_systick.c:103:0: information: Skipping configuration 'SysTick;__ARM_ARCH_6M__' since the value of 'SysTick' is unknown. Use -D if you want to check it. You can use -U to skip it explicitly. [ConfigurationNotChecked]
  (void)SysTick->CTRL;
^
Firmware/mock/nucleof030r8/ir_sensor_mock/Drivers/CMSIS/RTOS2/Source/os_systick.c:118:0: information: Skipping configuration 'SysTick;__ARM_ARCH_6M__' since the value of 'SysTick' is unknown. Use -D if you want to check it. You can use -U to skip it explicitly. [ConfigurationNotChecked]
  return (SysTick->LOAD + 1U);
^
Firmware/mock/nucleof030r8/ir_sensor_mock/Drivers/CMSIS/RTOS2/Source/os_systick.c:123:0: information: Skipping configuration 'SysTick;__ARM_ARCH_6M__' since the value of 'SysTick' is unknown. Use -D if you want to check it. You can use -U to skip it explicitly. [ConfigurationNotChecked]
  uint32_t load = SysTick->LOAD;
^
Firmware/mock/nucleof030r8/ir_sensor_mock/Drivers/CMSIS/RTOS2/Source/os_systick.c:124:0: information: Skipping configuration 'SysTick;__ARM_ARCH_6M__' since the value of 'SysTick' is unknown. Use -D if you want to check it. You can use -U to skip it explicitly. [ConfigurationNotChecked]
  return  (load - SysTick->VAL);
^
Firmware/mock/nucleof030r8/ir_sensor_mock/Drivers/CMSIS/RTOS2/Source/os_systick.c:129:0: information: Skipping configuration 'SysTick;__ARM_ARCH_6M__' since the value of 'SysTick' is unknown. Use -D if you want to check it. You can use -U to skip it explicitly. [ConfigurationNotChecked]
  return ((SysTick->CTRL >> 16) & 1U);
^
Firmware/mock/nucleof030r8/ir_sensor_mock/Drivers/CMSIS/RTOS2/Source/os_systick.c:70:0: information: Skipping configuration 'SysTick;__ARM_ARCH_7EM__;__ARM_ARCH_7M__' since the value of 'SysTick' is unknown. Use -D if you want to check it. You can use -U to skip it explicitly. [ConfigurationNotChecked]
  SysTick->CTRL =  SysTick_CTRL_CLKSOURCE_Msk | SysTick_CTRL_TICKINT_Msk;
^
Firmware/mock/nucleof030r8/ir_sensor_mock/Drivers/CMSIS/RTOS2/Source/os_systick.c:71:0: information: Skipping configuration 'SysTick;__ARM_ARCH_7EM__;__ARM_ARCH_7M__' since the value of 'SysTick' is unknown. Use -D if you want to check it. You can use -U to skip it explicitly. [ConfigurationNotChecked]
  SysTick->LOAD =  load;
^
Firmware/mock/nucleof030r8/ir_sensor_mock/Drivers/CMSIS/RTOS2/Source/os_systick.c:72:0: information: Skipping configuration 'SysTick;__ARM_ARCH_7EM__;__ARM_ARCH_7M__' since the value of 'SysTick' is unknown. Use -D if you want to check it. You can use -U to skip it explicitly. [ConfigurationNotChecked]
  SysTick->VAL  =  0U;
^
Firmware/mock/nucleof030r8/ir_sensor_mock/Drivers/CMSIS/RTOS2/Source/os_systick.c:87:0: information: Skipping configuration 'SysTick;__ARM_ARCH_7EM__;__ARM_ARCH_7M__' since the value of 'SysTick' is unknown. Use -D if you want to check it. You can use -U to skip it explicitly. [ConfigurationNotChecked]
  SysTick->CTRL |=  SysTick_CTRL_ENABLE_Msk;
^
Firmware/mock/nucleof030r8/ir_sensor_mock/Drivers/CMSIS/RTOS2/Source/os_systick.c:93:0: information: Skipping configuration 'SysTick;__ARM_ARCH_7EM__;__ARM_ARCH_7M__' since the value of 'SysTick' is unknown. Use -D if you want to check it. You can use -U to skip it explicitly. [ConfigurationNotChecked]
  SysTick->CTRL &= ~SysTick_CTRL_ENABLE_Msk;
^
Firmware/mock/nucleof030r8/ir_sensor_mock/Drivers/CMSIS/RTOS2/Source/os_systick.c:103:0: information: Skipping configuration 'SysTick;__ARM_ARCH_7EM__;__ARM_ARCH_7M__' since the value of 'SysTick' is unknown. Use -D if you want to check it. You can use -U to skip it explicitly. [ConfigurationNotChecked]
  (void)SysTick->CTRL;
^
Firmware/mock/nucleof030r8/ir_sensor_mock/Drivers/CMSIS/RTOS2/Source/os_systick.c:118:0: information: Skipping configuration 'SysTick;__ARM_ARCH_7EM__;__ARM_ARCH_7M__' since the value of 'SysTick' is unknown. Use -D if you want to check it. You can use -U to skip it explicitly. [ConfigurationNotChecked]
  return (SysTick->LOAD + 1U);
^
Firmware/mock/nucleof030r8/ir_sensor_mock/Drivers/CMSIS/RTOS2/Source/os_systick.c:123:0: information: Skipping configuration 'SysTick;__ARM_ARCH_7EM__;__ARM_ARCH_7M__' since the value of 'SysTick' is unknown. Use -D if you want to check it. You can use -U to skip it explicitly. [ConfigurationNotChecked]
  uint32_t load = SysTick->LOAD;
^
Firmware/mock/nucleof030r8/ir_sensor_mock/Drivers/CMSIS/RTOS2/Source/os_systick.c:124:0: information: Skipping configuration 'SysTick;__ARM_ARCH_7EM__;__ARM_ARCH_7M__' since the value of 'SysTick' is unknown. Use -D if you want to check it. You can use -U to skip it explicitly. [ConfigurationNotChecked]
  return  (load - SysTick->VAL);
^
Firmware/mock/nucleof030r8/ir_sensor_mock/Drivers/CMSIS/RTOS2/Source/os_systick.c:129:0: information: Skipping configuration 'SysTick;__ARM_ARCH_7EM__;__ARM_ARCH_7M__' since the value of 'SysTick' is unknown. Use -D if you want to check it. You can use -U to skip it explicitly. [ConfigurationNotChecked]
  return ((SysTick->CTRL >> 16) & 1U);
^
Firmware/mock/nucleof030r8/ir_sensor_mock/Drivers/CMSIS/RTOS2/Source/os_systick.c:70:0: information: Skipping configuration 'SysTick;__ARM_ARCH_8M_BASE__' since the value of 'SysTick' is unknown. Use -D if you want to check it. You can use -U to skip it explicitly. [ConfigurationNotChecked]
  SysTick->CTRL =  SysTick_CTRL_CLKSOURCE_Msk | SysTick_CTRL_TICKINT_Msk;
^
Firmware/mock/nucleof030r8/ir_sensor_mock/Drivers/CMSIS/RTOS2/Source/os_systick.c:71:0: information: Skipping configuration 'SysTick;__ARM_ARCH_8M_BASE__' since the value of 'SysTick' is unknown. Use -D if you want to check it. You can use -U to skip it explicitly. [ConfigurationNotChecked]
  SysTick->LOAD =  load;
^
Firmware/mock/nucleof030r8/ir_sensor_mock/Drivers/CMSIS/RTOS2/Source/os_systick.c:72:0: information: Skipping configuration 'SysTick;__ARM_ARCH_8M_BASE__' since the value of 'SysTick' is unknown. Use -D if you want to check it. You can use -U to skip it explicitly. [ConfigurationNotChecked]
  SysTick->VAL  =  0U;
^
Firmware/mock/nucleof030r8/ir_sensor_mock/Drivers/CMSIS/RTOS2/Source/os_systick.c:87:0: information: Skipping configuration 'SysTick;__ARM_ARCH_8M_BASE__' since the value of 'SysTick' is unknown. Use -D if you want to check it. You can use -U to skip it explicitly. [ConfigurationNotChecked]
  SysTick->CTRL |=  SysTick_CTRL_ENABLE_Msk;
^
Firmware/mock/nucleof030r8/ir_sensor_mock/Drivers/CMSIS/RTOS2/Source/os_systick.c:93:0: information: Skipping configuration 'SysTick;__ARM_ARCH_8M_BASE__' since the value of 'SysTick' is unknown. Use -D if you want to check it. You can use -U to skip it explicitly. [ConfigurationNotChecked]
  SysTick->CTRL &= ~SysTick_CTRL_ENABLE_Msk;
^
Firmware/mock/nucleof030r8/ir_sensor_mock/Drivers/CMSIS/RTOS2/Source/os_systick.c:103:0: information: Skipping configuration 'SysTick;__ARM_ARCH_8M_BASE__' since the value of 'SysTick' is unknown. Use -D if you want to check it. You can use -U to skip it explicitly. [ConfigurationNotChecked]
  (void)SysTick->CTRL;
^
Firmware/mock/nucleof030r8/ir_sensor_mock/Drivers/CMSIS/RTOS2/Source/os_systick.c:118:0: information: Skipping configuration 'SysTick;__ARM_ARCH_8M_BASE__' since the value of 'SysTick' is unknown. Use -D if you want to check it. You can use -U to skip it explicitly. [ConfigurationNotChecked]
  return (SysTick->LOAD + 1U);
^
Firmware/mock/nucleof030r8/ir_sensor_mock/Drivers/CMSIS/RTOS2/Source/os_systick.c:123:0: information: Skipping configuration 'SysTick;__ARM_ARCH_8M_BASE__' since the value of 'SysTick' is unknown. Use -D if you want to check it. You can use -U to skip it explicitly. [ConfigurationNotChecked]
  uint32_t load = SysTick->LOAD;
^
Firmware/mock/nucleof030r8/ir_sensor_mock/Drivers/CMSIS/RTOS2/Source/os_systick.c:124:0: information: Skipping configuration 'SysTick;__ARM_ARCH_8M_BASE__' since the value of 'SysTick' is unknown. Use -D if you want to check it. You can use -U to skip it explicitly. [ConfigurationNotChecked]
  return  (load - SysTick->VAL);
^
Firmware/mock/nucleof030r8/ir_sensor_mock/Drivers/CMSIS/RTOS2/Source/os_systick.c:129:0: information: Skipping configuration 'SysTick;__ARM_ARCH_8M_BASE__' since the value of 'SysTick' is unknown. Use -D if you want to check it. You can use -U to skip it explicitly. [ConfigurationNotChecked]
  return ((SysTick->CTRL >> 16) & 1U);
^
Firmware/mock/nucleof030r8/ir_sensor_mock/Drivers/CMSIS/RTOS2/Source/os_systick.c:70:0: information: Skipping configuration 'SysTick;__ARM_ARCH_8M_MAIN__;__CORTEX_M' since the value of 'SysTick' is unknown. Use -D if you want to check it. You can use -U to skip it explicitly. [ConfigurationNotChecked]
  SysTick->CTRL =  SysTick_CTRL_CLKSOURCE_Msk | SysTick_CTRL_TICKINT_Msk;
^
Firmware/mock/nucleof030r8/ir_sensor_mock/Drivers/CMSIS/RTOS2/Source/os_systick.c:71:0: information: Skipping configuration 'SysTick;__ARM_ARCH_8M_MAIN__;__CORTEX_M' since the value of 'SysTick' is unknown. Use -D if you want to check it. You can use -U to skip it explicitly. [ConfigurationNotChecked]
  SysTick->LOAD =  load;
^
Firmware/mock/nucleof030r8/ir_sensor_mock/Drivers/CMSIS/RTOS2/Source/os_systick.c:72:0: information: Skipping configuration 'SysTick;__ARM_ARCH_8M_MAIN__;__CORTEX_M' since the value of 'SysTick' is unknown. Use -D if you want to check it. You can use -U to skip it explicitly. [ConfigurationNotChecked]
  SysTick->VAL  =  0U;
^
Firmware/mock/nucleof030r8/ir_sensor_mock/Drivers/CMSIS/RTOS2/Source/os_systick.c:87:0: information: Skipping configuration 'SysTick;__ARM_ARCH_8M_MAIN__;__CORTEX_M' since the value of 'SysTick' is unknown. Use -D if you want to check it. You can use -U to skip it explicitly. [ConfigurationNotChecked]
  SysTick->CTRL |=  SysTick_CTRL_ENABLE_Msk;
^
Firmware/mock/nucleof030r8/ir_sensor_mock/Drivers/CMSIS/RTOS2/Source/os_systick.c:93:0: information: Skipping configuration 'SysTick;__ARM_ARCH_8M_MAIN__;__CORTEX_M' since the value of 'SysTick' is unknown. Use -D if you want to check it. You can use -U to skip it explicitly. [ConfigurationNotChecked]
  SysTick->CTRL &= ~SysTick_CTRL_ENABLE_Msk;
^
Firmware/mock/nucleof030r8/ir_sensor_mock/Drivers/CMSIS/RTOS2/Source/os_systick.c:103:0: information: Skipping configuration 'SysTick;__ARM_ARCH_8M_MAIN__;__CORTEX_M' since the value of 'SysTick' is unknown. Use -D if you want to check it. You can use -U to skip it explicitly. [ConfigurationNotChecked]
  (void)SysTick->CTRL;
^
Firmware/mock/nucleof030r8/ir_sensor_mock/Drivers/CMSIS/RTOS2/Source/os_systick.c:118:0: information: Skipping configuration 'SysTick;__ARM_ARCH_8M_MAIN__;__CORTEX_M' since the value of 'SysTick' is unknown. Use -D if you want to check it. You can use -U to skip it explicitly. [ConfigurationNotChecked]
  return (SysTick->LOAD + 1U);
^
Firmware/mock/nucleof030r8/ir_sensor_mock/Drivers/CMSIS/RTOS2/Source/os_systick.c:123:0: information: Skipping configuration 'SysTick;__ARM_ARCH_8M_MAIN__;__CORTEX_M' since the value of 'SysTick' is unknown. Use -D if you want to check it. You can use -U to skip it explicitly. [ConfigurationNotChecked]
  uint32_t load = SysTick->LOAD;
^
Firmware/mock/nucleof030r8/ir_sensor_mock/Drivers/CMSIS/RTOS2/Source/os_systick.c:124:0: information: Skipping configuration 'SysTick;__ARM_ARCH_8M_MAIN__;__CORTEX_M' since the value of 'SysTick' is unknown. Use -D if you want to check it. You can use -U to skip it explicitly. [ConfigurationNotChecked]
  return  (load - SysTick->VAL);
^
Firmware/mock/nucleof030r8/ir_sensor_mock/Drivers/CMSIS/RTOS2/Source/os_systick.c:129:0: information: Skipping configuration 'SysTick;__ARM_ARCH_8M_MAIN__;__CORTEX_M' since the value of 'SysTick' is unknown. Use -D if you want to check it. You can use -U to skip it explicitly. [ConfigurationNotChecked]
  return ((SysTick->CTRL >> 16) & 1U);
^
Firmware/mock/nucleof030r8/ir_sensor_mock/Drivers/CMSIS/RTOS2/Source/os_tick_gtim.c:185:14: style: Variable 'cntp_ctl.w' is assigned a value that is never used. [unreadVariable]
  cntp_ctl.w = PL1_GetControl();
             ^
Firmware/mock/nucleof030r8/ir_sensor_mock/Drivers/CMSIS/RTOS2/Source/os_tick_gtim.c:60:0: information: Skipping configuration 'SCTR_BASE' since the value of 'SCTR_BASE' is unknown. Use -D if you want to check it. You can use -U to skip it explicitly. [ConfigurationNotChecked]
  GTIM_Clock = *(uint32_t*)(SCTR_BASE+0x20);
^
Firmware/mock/nucleof030r8/ir_sensor_mock/Drivers/CMSIS/RTOS2/Source/os_tick_gtim.c:113:0: information: Skipping configuration 'SCTR_BASE' since the value of 'SCTR_BASE' is unknown. Use -D if you want to check it. You can use -U to skip it explicitly. [ConfigurationNotChecked]
  *(uint32_t*)SCTR_BASE |= 3U;
^
Firmware/mock/nucleof030r8/ir_sensor_mock/Drivers/CMSIS/RTOS2/Source/os_tick_ptim.c:162:0: information: Skipping configuration 'PTIM' since the value of 'PTIM' is unknown. Use -D if you want to check it. You can use -U to skip it explicitly. [ConfigurationNotChecked]
  return (PTIM->ISR & 1);
^
Firmware/mock/nucleof030r8/ir_sensor_mock/Drivers/STM32F0xx_HAL_Driver/Src/stm32f0xx_hal_adc.c:2031:12: style: The scope of the variable 'tmpAWDHighThresholdShifted' can be reduced. [variableScope]
  uint32_t tmpAWDHighThresholdShifted;
           ^
Firmware/mock/nucleof030r8/ir_sensor_mock/Drivers/STM32F0xx_HAL_Driver/Src/stm32f0xx_hal_adc.c:2032:12: style: The scope of the variable 'tmpAWDLowThresholdShifted' can be reduced. [variableScope]
  uint32_t tmpAWDLowThresholdShifted;
           ^
Firmware/mock/nucleof030r8/ir_sensor_mock/Drivers/STM32F0xx_HAL_Driver/Src/stm32f0xx_hal_adc.c:2195:12: style: The scope of the variable 'tickstart' can be reduced. [variableScope]
  uint32_t tickstart = 0U;
           ^
Firmware/mock/nucleof030r8/ir_sensor_mock/Drivers/STM32F0xx_HAL_Driver/Src/stm32f0xx_hal_adc.c:2263:12: style: The scope of the variable 'tickstart' can be reduced. [variableScope]
  uint32_t tickstart = 0U;
           ^
Firmware/mock/nucleof030r8/ir_sensor_mock/Drivers/STM32F0xx_HAL_Driver/Src/stm32f0xx_hal_adc.c:2324:12: style: The scope of the variable 'tickstart' can be reduced. [variableScope]
  uint32_t tickstart = 0U;
           ^
Firmware/mock/nucleof030r8/ir_sensor_mock/Drivers/STM32F0xx_HAL_Driver/Src/stm32f0xx_hal_adc.c:2195:22: style: Variable 'tickstart' is assigned a value that is never used. [unreadVariable]
  uint32_t tickstart = 0U;
                     ^
Firmware/mock/nucleof030r8/ir_sensor_mock/Drivers/STM32F0xx_HAL_Driver/Src/stm32f0xx_hal_adc.c:2263:22: style: Variable 'tickstart' is assigned a value that is never used. [unreadVariable]
  uint32_t tickstart = 0U;
                     ^
Firmware/mock/nucleof030r8/ir_sensor_mock/Drivers/STM32F0xx_HAL_Driver/Src/stm32f0xx_hal_adc.c:2324:22: style: Variable 'tickstart' is assigned a value that is never used. [unreadVariable]
  uint32_t tickstart = 0U;
                     ^
Firmware/mock/nucleof030r8/ir_sensor_mock/Drivers/STM32F0xx_HAL_Driver/Src/stm32f0xx_hal_adc_ex.c:98:12: style: The scope of the variable 'tickstart' can be reduced. [variableScope]
  uint32_t tickstart = 0U;
           ^
Firmware/mock/nucleof030r8/ir_sensor_mock/Drivers/STM32F0xx_HAL_Driver/Src/stm32f0xx_hal_adc_ex.c:99:12: style: The scope of the variable 'backup_setting_adc_dma_transfer' can be reduced. [variableScope]
  uint32_t backup_setting_adc_dma_transfer = 0; /* Note: Variable not declared as volatile because register read is already declared as volatile */
           ^
Firmware/mock/nucleof030r8/ir_sensor_mock/Drivers/STM32F0xx_HAL_Driver/Src/stm32f0xx_hal_adc_ex.c:98:22: style: Variable 'tickstart' is assigned a value that is never used. [unreadVariable]
  uint32_t tickstart = 0U;
                     ^
Firmware/mock/nucleof030r8/ir_sensor_mock/Drivers/STM32F0xx_HAL_Driver/Src/stm32f0xx_hal_adc_ex.c:99:44: style: Variable 'backup_setting_adc_dma_transfer' is assigned a value that is never used. [unreadVariable]
  uint32_t backup_setting_adc_dma_transfer = 0; /* Note: Variable not declared as volatile because register read is already declared as volatile */
                                           ^
Firmware/mock/nucleof030r8/ir_sensor_mock/Drivers/STM32F0xx_HAL_Driver/Src/stm32f0xx_hal_can.c:842:12: style: The scope of the variable 'filternbrbitpos' can be reduced. [variableScope]
  uint32_t filternbrbitpos;
           ^
Firmware/mock/nucleof030r8/ir_sensor_mock/Drivers/STM32F0xx_HAL_Driver/Src/stm32f0xx_hal_can.c:992:12: style: The scope of the variable 'tickstart' can be reduced. [variableScope]
  uint32_t tickstart;
           ^
Firmware/mock/nucleof030r8/ir_sensor_mock/Drivers/STM32F0xx_HAL_Driver/Src/stm32f0xx_hal_can.c:1044:12: style: The scope of the variable 'tickstart' can be reduced. [variableScope]
  uint32_t tickstart;
           ^
Firmware/mock/nucleof030r8/ir_sensor_mock/Drivers/STM32F0xx_HAL_Driver/Src/stm32f0xx_hal_can.c:1209:12: style: The scope of the variable 'transmitmailbox' can be reduced. [variableScope]
  uint32_t transmitmailbox;
           ^
Firmware/mock/nucleof030r8/ir_sensor_mock/Drivers/STM32F0xx_HAL_Driver/Src/stm32f0xx_hal_can.c:1433:12: style: The scope of the variable 'transmitmailbox' can be reduced. [variableScope]
  uint32_t transmitmailbox;
           ^
Firmware/mock/nucleof030r8/ir_sensor_mock/Drivers/STM32F0xx_HAL_Driver/Src/stm32f0xx_hal_comp.c:339:0: information: Skipping configuration 'COMP1;COMP2;HAL_COMP_MODULE_ENABLED' since the value of 'COMP2' is unknown. Use -D if you want to check it. You can use -U to skip it explicitly. [ConfigurationNotChecked]
    if(hcomp->Instance == COMP2)
^
Firmware/mock/nucleof030r8/ir_sensor_mock/Drivers/STM32F0xx_HAL_Driver/Src/stm32f0xx_hal_comp.c:389:0: information: Skipping configuration 'COMP1;COMP2;HAL_COMP_MODULE_ENABLED' since the value of 'COMP2' is unknown. Use -D if you want to check it. You can use -U to skip it explicitly. [ConfigurationNotChecked]
    if(hcomp->Instance == COMP2)
^
Firmware/mock/nucleof030r8/ir_sensor_mock/Drivers/STM32F0xx_HAL_Driver/Src/stm32f0xx_hal_comp.c:652:0: information: Skipping configuration 'COMP1;COMP2;HAL_COMP_MODULE_ENABLED' since the value of 'COMP2' is unknown. Use -D if you want to check it. You can use -U to skip it explicitly. [ConfigurationNotChecked]
      if(hcomp->Instance == COMP2)
^
Firmware/mock/nucleof030r8/ir_sensor_mock/Drivers/STM32F0xx_HAL_Driver/Src/stm32f0xx_hal_comp.c:700:0: information: Skipping configuration 'COMP1;COMP2;HAL_COMP_MODULE_ENABLED' since the value of 'COMP2' is unknown. Use -D if you want to check it. You can use -U to skip it explicitly. [ConfigurationNotChecked]
      if(hcomp->Instance == COMP2)
^
Firmware/mock/nucleof030r8/ir_sensor_mock/Drivers/STM32F0xx_HAL_Driver/Src/stm32f0xx_hal_comp.c:848:0: information: Skipping configuration 'COMP1;COMP2;HAL_COMP_MODULE_ENABLED' since the value of 'COMP2' is unknown. Use -D if you want to check it. You can use -U to skip it explicitly. [ConfigurationNotChecked]
    if(hcomp->Instance == COMP2)
^
Firmware/mock/nucleof030r8/ir_sensor_mock/Drivers/STM32F0xx_HAL_Driver/Src/stm32f0xx_hal_comp.c:883:0: information: Skipping configuration 'COMP1;COMP2;HAL_COMP_MODULE_ENABLED' since the value of 'COMP2' is unknown. Use -D if you want to check it. You can use -U to skip it explicitly. [ConfigurationNotChecked]
  if(hcomp->Instance == COMP2)
^
Firmware/mock/nucleof030r8/ir_sensor_mock/Drivers/STM32F0xx_HAL_Driver/Src/stm32f0xx_hal_crc.c:437:12: style: The scope of the variable 'data' can be reduced. [variableScope]
  uint16_t data;
           ^
Firmware/mock/nucleof030r8/ir_sensor_mock/Drivers/STM32F0xx_HAL_Driver/Src/stm32f0xx_hal_crc_ex.c:93:12: style: The scope of the variable 'msb' can be reduced. [variableScope]
  uint32_t msb = 31U; /* polynomial degree is 32 at most, so msb is initialized to max value */
           ^
Firmware/mock/nucleof030r8/ir_sensor_mock/Drivers/STM32F0xx_HAL_Driver/Src/stm32f0xx_hal_dac.c:348:15: style: Variable 'hdac->State' is reassigned a value before the old one has been used. [redundantAssignment]
  hdac->State = HAL_DAC_STATE_READY;
              ^
Firmware/mock/nucleof030r8/ir_sensor_mock/Drivers/STM32F0xx_HAL_Driver/Src/stm32f0xx_hal_dac.c:342:15: note: hdac->State is assigned
  hdac->State = HAL_DAC_STATE_BUSY;
              ^
Firmware/mock/nucleof030r8/ir_sensor_mock/Drivers/STM32F0xx_HAL_Driver/Src/stm32f0xx_hal_dac.c:348:15: note: hdac->State is overwritten
  hdac->State = HAL_DAC_STATE_READY;
              ^
Firmware/mock/nucleof030r8/ir_sensor_mock/Drivers/STM32F0xx_HAL_Driver/Src/stm32f0xx_hal_dac_ex.c:194:15: style: Variable 'hdac->State' is reassigned a value before the old one has been used. [redundantAssignment]
  hdac->State = HAL_DAC_STATE_READY;
              ^
Firmware/mock/nucleof030r8/ir_sensor_mock/Drivers/STM32F0xx_HAL_Driver/Src/stm32f0xx_hal_dac_ex.c:178:15: note: hdac->State is assigned
  hdac->State = HAL_DAC_STATE_BUSY;
              ^
Firmware/mock/nucleof030r8/ir_sensor_mock/Drivers/STM32F0xx_HAL_Driver/Src/stm32f0xx_hal_dac_ex.c:194:15: note: hdac->State is overwritten
  hdac->State = HAL_DAC_STATE_READY;
              ^
Firmware/mock/nucleof030r8/ir_sensor_mock/Drivers/STM32F0xx_HAL_Driver/Src/stm32f0xx_hal_dac_ex.c:140:15: style: Variable 'hdac->State' is reassigned a value before the old one has been used. [redundantAssignment]
  hdac->State = HAL_DAC_STATE_READY;
              ^
Firmware/mock/nucleof030r8/ir_sensor_mock/Drivers/STM32F0xx_HAL_Driver/Src/stm32f0xx_hal_dac_ex.c:124:15: note: hdac->State is assigned
  hdac->State = HAL_DAC_STATE_BUSY;
              ^
Firmware/mock/nucleof030r8/ir_sensor_mock/Drivers/STM32F0xx_HAL_Driver/Src/stm32f0xx_hal_dac_ex.c:140:15: note: hdac->State is overwritten
  hdac->State = HAL_DAC_STATE_READY;
              ^
Firmware/mock/nucleof030r8/ir_sensor_mock/Drivers/STM32F0xx_HAL_Driver/Src/stm32f0xx_hal_dma.c:873:0: information: Skipping configuration 'DMA2;HAL_DMA_MODULE_ENABLED' since the value of 'DMA2' is unknown. Use -D if you want to check it. You can use -U to skip it explicitly. [ConfigurationNotChecked]
    hdma->DmaBaseAddress = DMA2;
^
Firmware/mock/nucleof030r8/ir_sensor_mock/Drivers/STM32F0xx_HAL_Driver/Src/stm32f0xx_hal_dma.c:214:24: style: Variable 'hdma->Instance->CCR' is reassigned a value before the old one has been used. [redundantAssignment]
  hdma->Instance->CCR  = 0U;
                       ^
Firmware/mock/nucleof030r8/ir_sensor_mock/Drivers/STM32F0xx_HAL_Driver/Src/stm32f0xx_hal_dma.c:211:23: note: hdma->Instance->CCR is assigned
  hdma->Instance->CCR &= ~DMA_CCR_EN;
                      ^
Firmware/mock/nucleof030r8/ir_sensor_mock/Drivers/STM32F0xx_HAL_Driver/Src/stm32f0xx_hal_dma.c:214:24: note: hdma->Instance->CCR is overwritten
  hdma->Instance->CCR  = 0U;
                       ^
Firmware/mock/nucleof030r8/ir_sensor_mock/Drivers/STM32F0xx_HAL_Driver/Src/stm32f0xx_hal_exti.c:144:12: style: The scope of the variable 'regval' can be reduced. [variableScope]
  uint32_t regval;
           ^
Firmware/mock/nucleof030r8/ir_sensor_mock/Drivers/STM32F0xx_HAL_Driver/Src/stm32f0xx_hal_exti.c:239:12: style: The scope of the variable 'regval' can be reduced. [variableScope]
  uint32_t regval;
           ^
Firmware/mock/nucleof030r8/ir_sensor_mock/Drivers/STM32F0xx_HAL_Driver/Src/stm32f0xx_hal_exti.c:318:12: style: The scope of the variable 'regval' can be reduced. [variableScope]
  uint32_t regval;
           ^
Firmware/mock/nucleof030r8/ir_sensor_mock/Drivers/STM32F0xx_HAL_Driver/Src/stm32f0xx_hal_flash.c:168:11: style: The scope of the variable 'index' can be reduced. [variableScope]
  uint8_t index = 0U;
          ^
Firmware/mock/nucleof030r8/ir_sensor_mock/Drivers/STM32F0xx_HAL_Driver/Src/stm32f0xx_hal_flash.c:169:11: style: The scope of the variable 'nbiterations' can be reduced. [variableScope]
  uint8_t nbiterations = 0U;
          ^
Firmware/mock/nucleof030r8/ir_sensor_mock/Drivers/STM32F0xx_HAL_Driver/Src/stm32f0xx_hal_flash.c:168:17: style: Variable 'index' is assigned a value that is never used. [unreadVariable]
  uint8_t index = 0U;
                ^
Firmware/mock/nucleof030r8/ir_sensor_mock/Drivers/STM32F0xx_HAL_Driver/Src/stm32f0xx_hal_flash.c:169:24: style: Variable 'nbiterations' is assigned a value that is never used. [unreadVariable]
  uint8_t nbiterations = 0U;
                       ^
Firmware/mock/nucleof030r8/ir_sensor_mock/Drivers/STM32F0xx_HAL_Driver/Src/stm32f0xx_hal_flash.c:285:23: style: Variable 'addresstmp' is assigned a value that is never used. [unreadVariable]
  uint32_t addresstmp = 0U;
                      ^
Firmware/mock/nucleof030r8/ir_sensor_mock/Drivers/STM32F0xx_HAL_Driver/Src/stm32f0xx_hal_flash_ex.c:0:0: information: Too many #ifdef configurations - cppcheck only checks 12 of 14 configurations. Use --force to check all configurations. [toomanyconfigs]

^
Firmware/mock/nucleof030r8/ir_sensor_mock/Drivers/STM32F0xx_HAL_Driver/Src/stm32f0xx_hal_flash_ex.c:537:3: style: Assignment of function parameter has no effect outside the function. [uselessAssignmentArg]
  WriteProtectPage = (uint32_t)(~((~FLASH_OB_GetWRP()) | WriteProtectPage));
  ^
Firmware/mock/nucleof030r8/ir_sensor_mock/Drivers/STM32F0xx_HAL_Driver/Src/stm32f0xx_hal_flash_ex.c:653:3: style: Assignment of function parameter has no effect outside the function. [uselessAssignmentArg]
  WriteProtectPage = (FLASH_OB_GetWRP() | WriteProtectPage);
  ^
Firmware/mock/nucleof030r8/ir_sensor_mock/Drivers/STM32F0xx_HAL_Driver/Src/stm32f0xx_hal_flash_ex.c:160:12: style: The scope of the variable 'address' can be reduced. [variableScope]
  uint32_t address = 0U;
           ^
Firmware/mock/nucleof030r8/ir_sensor_mock/Drivers/STM32F0xx_HAL_Driver/Src/stm32f0xx_hal_flash_ex.c:160:20: style: Variable 'address' is assigned a value that is never used. [unreadVariable]
  uint32_t address = 0U;
                   ^
Firmware/mock/nucleof030r8/ir_sensor_mock/Drivers/STM32F0xx_HAL_Driver/Src/stm32f0xx_hal_flash_ex.c:522:22: style: Variable 'WRP0_Data' is assigned a value that is never used. [unreadVariable]
  uint16_t WRP0_Data = 0xFFFFU;
                     ^
Firmware/mock/nucleof030r8/ir_sensor_mock/Drivers/STM32F0xx_HAL_Driver/Src/stm32f0xx_hal_flash_ex.c:638:22: style: Variable 'WRP0_Data' is assigned a value that is never used. [unreadVariable]
  uint16_t WRP0_Data = 0xFFFFU;
                     ^
Firmware/mock/nucleof030r8/ir_sensor_mock/Drivers/STM32F0xx_HAL_Driver/Src/stm32f0xx_hal_flash_ex.c:577:20: style: Condition 'WRP0_Data!=0xFFU' is always true [knownConditionTrueFalse]
      if(WRP0_Data != 0xFFU)
                   ^
Firmware/mock/nucleof030r8/ir_sensor_mock/Drivers/STM32F0xx_HAL_Driver/Src/stm32f0xx_hal_flash_ex.c:522:24: note: Assignment 'WRP0_Data=0xFFFFU', assigned value is 65535
  uint16_t WRP0_Data = 0xFFFFU;
                       ^
Firmware/mock/nucleof030r8/ir_sensor_mock/Drivers/STM32F0xx_HAL_Driver/Src/stm32f0xx_hal_flash_ex.c:577:20: note: Condition 'WRP0_Data!=0xFFU' is always true
      if(WRP0_Data != 0xFFU)
                   ^
Firmware/mock/nucleof030r8/ir_sensor_mock/Drivers/STM32F0xx_HAL_Driver/Src/stm32f0xx_hal_flash_ex.c:693:20: style: Condition 'WRP0_Data!=0xFFU' is always true [knownConditionTrueFalse]
      if(WRP0_Data != 0xFFU)
                   ^
Firmware/mock/nucleof030r8/ir_sensor_mock/Drivers/STM32F0xx_HAL_Driver/Src/stm32f0xx_hal_flash_ex.c:638:24: note: Assignment 'WRP0_Data=0xFFFFU', assigned value is 65535
  uint16_t WRP0_Data = 0xFFFFU;
                       ^
Firmware/mock/nucleof030r8/ir_sensor_mock/Drivers/STM32F0xx_HAL_Driver/Src/stm32f0xx_hal_flash_ex.c:693:20: note: Condition 'WRP0_Data!=0xFFU' is always true
      if(WRP0_Data != 0xFFU)
                   ^
Firmware/mock/nucleof030r8/ir_sensor_mock/Drivers/STM32F0xx_HAL_Driver/Src/stm32f0xx_hal_flash_ex.c:587:43: style: Condition 'WRP1_Data!=0xFFU' is always true [knownConditionTrueFalse]
      if((status == HAL_OK) && (WRP1_Data != 0xFFU))
                                          ^
Firmware/mock/nucleof030r8/ir_sensor_mock/Drivers/STM32F0xx_HAL_Driver/Src/stm32f0xx_hal_flash_ex.c:524:24: note: Assignment 'WRP1_Data=0xFFFFU', assigned value is 65535
  uint16_t WRP1_Data = 0xFFFFU;
                       ^
Firmware/mock/nucleof030r8/ir_sensor_mock/Drivers/STM32F0xx_HAL_Driver/Src/stm32f0xx_hal_flash_ex.c:587:43: note: Condition 'WRP1_Data!=0xFFU' is always true
      if((status == HAL_OK) && (WRP1_Data != 0xFFU))
                                          ^
Firmware/mock/nucleof030r8/ir_sensor_mock/Drivers/STM32F0xx_HAL_Driver/Src/stm32f0xx_hal_flash_ex.c:703:43: style: Condition 'WRP1_Data!=0xFFU' is always true [knownConditionTrueFalse]
      if((status == HAL_OK) && (WRP1_Data != 0xFFU))
                                          ^
Firmware/mock/nucleof030r8/ir_sensor_mock/Drivers/STM32F0xx_HAL_Driver/Src/stm32f0xx_hal_flash_ex.c:640:24: note: Assignment 'WRP1_Data=0xFFFFU', assigned value is 65535
  uint16_t WRP1_Data = 0xFFFFU;
                       ^
Firmware/mock/nucleof030r8/ir_sensor_mock/Drivers/STM32F0xx_HAL_Driver/Src/stm32f0xx_hal_flash_ex.c:703:43: note: Condition 'WRP1_Data!=0xFFU' is always true
      if((status == HAL_OK) && (WRP1_Data != 0xFFU))
                                          ^
Firmware/mock/nucleof030r8/ir_sensor_mock/Drivers/STM32F0xx_HAL_Driver/Src/stm32f0xx_hal_flash_ex.c:597:43: style: Condition 'WRP2_Data!=0xFFU' is always true [knownConditionTrueFalse]
      if((status == HAL_OK) && (WRP2_Data != 0xFFU))
                                          ^
Firmware/mock/nucleof030r8/ir_sensor_mock/Drivers/STM32F0xx_HAL_Driver/Src/stm32f0xx_hal_flash_ex.c:527:24: note: Assignment 'WRP2_Data=0xFFFFU', assigned value is 65535
  uint16_t WRP2_Data = 0xFFFFU;
                       ^
Firmware/mock/nucleof030r8/ir_sensor_mock/Drivers/STM32F0xx_HAL_Driver/Src/stm32f0xx_hal_flash_ex.c:597:43: note: Condition 'WRP2_Data!=0xFFU' is always true
      if((status == HAL_OK) && (WRP2_Data != 0xFFU))
                                          ^
Firmware/mock/nucleof030r8/ir_sensor_mock/Drivers/STM32F0xx_HAL_Driver/Src/stm32f0xx_hal_flash_ex.c:713:43: style: Condition 'WRP2_Data!=0xFFU' is always true [knownConditionTrueFalse]
      if((status == HAL_OK) && (WRP2_Data != 0xFFU))
                                          ^
Firmware/mock/nucleof030r8/ir_sensor_mock/Drivers/STM32F0xx_HAL_Driver/Src/stm32f0xx_hal_flash_ex.c:643:24: note: Assignment 'WRP2_Data=0xFFFFU', assigned value is 65535
  uint16_t WRP2_Data = 0xFFFFU;
                       ^
Firmware/mock/nucleof030r8/ir_sensor_mock/Drivers/STM32F0xx_HAL_Driver/Src/stm32f0xx_hal_flash_ex.c:713:43: note: Condition 'WRP2_Data!=0xFFU' is always true
      if((status == HAL_OK) && (WRP2_Data != 0xFFU))
                                          ^
Firmware/mock/nucleof030r8/ir_sensor_mock/Drivers/STM32F0xx_HAL_Driver/Src/stm32f0xx_hal_flash_ex.c:607:43: style: Condition 'WRP3_Data!=0xFFU' is always true [knownConditionTrueFalse]
      if((status == HAL_OK) && (WRP3_Data != 0xFFU))
                                          ^
Firmware/mock/nucleof030r8/ir_sensor_mock/Drivers/STM32F0xx_HAL_Driver/Src/stm32f0xx_hal_flash_ex.c:530:24: note: Assignment 'WRP3_Data=0xFFFFU', assigned value is 65535
  uint16_t WRP3_Data = 0xFFFFU;
                       ^
Firmware/mock/nucleof030r8/ir_sensor_mock/Drivers/STM32F0xx_HAL_Driver/Src/stm32f0xx_hal_flash_ex.c:607:43: note: Condition 'WRP3_Data!=0xFFU' is always true
      if((status == HAL_OK) && (WRP3_Data != 0xFFU))
                                          ^
Firmware/mock/nucleof030r8/ir_sensor_mock/Drivers/STM32F0xx_HAL_Driver/Src/stm32f0xx_hal_flash_ex.c:723:43: style: Condition 'WRP3_Data!=0xFFU' is always true [knownConditionTrueFalse]
      if((status == HAL_OK) && (WRP3_Data != 0xFFU))
                                          ^
Firmware/mock/nucleof030r8/ir_sensor_mock/Drivers/STM32F0xx_HAL_Driver/Src/stm32f0xx_hal_flash_ex.c:646:24: note: Assignment 'WRP3_Data=0xFFFFU', assigned value is 65535
  uint16_t WRP3_Data = 0xFFFFU;
                       ^
Firmware/mock/nucleof030r8/ir_sensor_mock/Drivers/STM32F0xx_HAL_Driver/Src/stm32f0xx_hal_flash_ex.c:723:43: note: Condition 'WRP3_Data!=0xFFU' is always true
      if((status == HAL_OK) && (WRP3_Data != 0xFFU))
                                          ^
Firmware/mock/nucleof030r8/ir_sensor_mock/Drivers/STM32F0xx_HAL_Driver/Src/stm32f0xx_hal_flash_ex.c:540:0: information: Skipping configuration 'HAL_FLASH_MODULE_ENABLED;OB_WRP_PAGES0TO15MASK' since the value of 'OB_WRP_PAGES0TO15MASK' is unknown. Use -D if you want to check it. You can use -U to skip it explicitly. [ConfigurationNotChecked]
  WRP0_Data = (uint16_t)(WriteProtectPage & OB_WRP_PAGES0TO15MASK);
^
Firmware/mock/nucleof030r8/ir_sensor_mock/Drivers/STM32F0xx_HAL_Driver/Src/stm32f0xx_hal_flash_ex.c:656:0: information: Skipping configuration 'HAL_FLASH_MODULE_ENABLED;OB_WRP_PAGES0TO15MASK' since the value of 'OB_WRP_PAGES0TO15MASK' is unknown. Use -D if you want to check it. You can use -U to skip it explicitly. [ConfigurationNotChecked]
  WRP0_Data = (uint16_t)(WriteProtectPage & OB_WRP_PAGES0TO15MASK);
^
Firmware/mock/nucleof030r8/ir_sensor_mock/Drivers/STM32F0xx_HAL_Driver/Src/stm32f0xx_hal_flash_ex.c:542:0: information: Skipping configuration 'HAL_FLASH_MODULE_ENABLED;OB_WRP_PAGES0TO31MASK' since the value of 'OB_WRP_PAGES0TO31MASK' is unknown. Use -D if you want to check it. You can use -U to skip it explicitly. [ConfigurationNotChecked]
  WRP0_Data = (uint16_t)(WriteProtectPage & OB_WRP_PAGES0TO31MASK);
^
Firmware/mock/nucleof030r8/ir_sensor_mock/Drivers/STM32F0xx_HAL_Driver/Src/stm32f0xx_hal_flash_ex.c:658:0: information: Skipping configuration 'HAL_FLASH_MODULE_ENABLED;OB_WRP_PAGES0TO31MASK' since the value of 'OB_WRP_PAGES0TO31MASK' is unknown. Use -D if you want to check it. You can use -U to skip it explicitly. [ConfigurationNotChecked]
  WRP0_Data = (uint16_t)(WriteProtectPage & OB_WRP_PAGES0TO31MASK);
^
Firmware/mock/nucleof030r8/ir_sensor_mock/Drivers/STM32F0xx_HAL_Driver/Src/stm32f0xx_hal_flash_ex.c:546:0: information: Skipping configuration 'HAL_FLASH_MODULE_ENABLED;OB_WRP_PAGES16TO31MASK' since the value of 'OB_WRP_PAGES16TO31MASK' is unknown. Use -D if you want to check it. You can use -U to skip it explicitly. [ConfigurationNotChecked]
  WRP1_Data = (uint16_t)((WriteProtectPage & OB_WRP_PAGES16TO31MASK) >> 8U);
^
Firmware/mock/nucleof030r8/ir_sensor_mock/Drivers/STM32F0xx_HAL_Driver/Src/stm32f0xx_hal_flash_ex.c:662:0: information: Skipping configuration 'HAL_FLASH_MODULE_ENABLED;OB_WRP_PAGES16TO31MASK' since the value of 'OB_WRP_PAGES16TO31MASK' is unknown. Use -D if you want to check it. You can use -U to skip it explicitly. [ConfigurationNotChecked]
  WRP1_Data = (uint16_t)((WriteProtectPage & OB_WRP_PAGES16TO31MASK) >> 8U);
^
Firmware/mock/nucleof030r8/ir_sensor_mock/Drivers/STM32F0xx_HAL_Driver/Src/stm32f0xx_hal_flash_ex.c:552:0: information: Skipping configuration 'HAL_FLASH_MODULE_ENABLED;OB_WRP_PAGES32TO47MASK' since the value of 'OB_WRP_PAGES32TO47MASK' is unknown. Use -D if you want to check it. You can use -U to skip it explicitly. [ConfigurationNotChecked]
  WRP2_Data = (uint16_t)((WriteProtectPage & OB_WRP_PAGES32TO47MASK) >> 16U);
^
Firmware/mock/nucleof030r8/ir_sensor_mock/Drivers/STM32F0xx_HAL_Driver/Src/stm32f0xx_hal_flash_ex.c:668:0: information: Skipping configuration 'HAL_FLASH_MODULE_ENABLED;OB_WRP_PAGES32TO47MASK' since the value of 'OB_WRP_PAGES32TO47MASK' is unknown. Use -D if you want to check it. You can use -U to skip it explicitly. [ConfigurationNotChecked]
  WRP2_Data = (uint16_t)((WriteProtectPage & OB_WRP_PAGES32TO47MASK) >> 16U);
^
Firmware/mock/nucleof030r8/ir_sensor_mock/Drivers/STM32F0xx_HAL_Driver/Src/stm32f0xx_hal_flash_ex.c:548:0: information: Skipping configuration 'HAL_FLASH_MODULE_ENABLED;OB_WRP_PAGES32TO63MASK' since the value of 'OB_WRP_PAGES32TO63MASK' is unknown. Use -D if you want to check it. You can use -U to skip it explicitly. [ConfigurationNotChecked]
  WRP1_Data = (uint16_t)((WriteProtectPage & OB_WRP_PAGES32TO63MASK) >> 8U);
^
Firmware/mock/nucleof030r8/ir_sensor_mock/Drivers/STM32F0xx_HAL_Driver/Src/stm32f0xx_hal_flash_ex.c:664:0: information: Skipping configuration 'HAL_FLASH_MODULE_ENABLED;OB_WRP_PAGES32TO63MASK' since the value of 'OB_WRP_PAGES32TO63MASK' is unknown. Use -D if you want to check it. You can use -U to skip it explicitly. [ConfigurationNotChecked]
  WRP1_Data = (uint16_t)((WriteProtectPage & OB_WRP_PAGES32TO63MASK) >> 8U);
^
Firmware/mock/nucleof030r8/ir_sensor_mock/Drivers/STM32F0xx_HAL_Driver/Src/stm32f0xx_hal_gpio.c:475:15: style: Variable 'GPIOx->LCKR' is reassigned a value before the old one has been used. [redundantAssignment]
  GPIOx->LCKR = GPIO_Pin;
              ^
Firmware/mock/nucleof030r8/ir_sensor_mock/Drivers/STM32F0xx_HAL_Driver/Src/stm32f0xx_hal_gpio.c:473:15: note: GPIOx->LCKR is assigned
  GPIOx->LCKR = tmp;
              ^
Firmware/mock/nucleof030r8/ir_sensor_mock/Drivers/STM32F0xx_HAL_Driver/Src/stm32f0xx_hal_gpio.c:475:15: note: GPIOx->LCKR is overwritten
  GPIOx->LCKR = GPIO_Pin;
              ^
Firmware/mock/nucleof030r8/ir_sensor_mock/Drivers/STM32F0xx_HAL_Driver/Src/stm32f0xx_hal_gpio.c:477:15: style: Variable 'GPIOx->LCKR' is reassigned a value before the old one has been used. [redundantAssignment]
  GPIOx->LCKR = tmp;
              ^
Firmware/mock/nucleof030r8/ir_sensor_mock/Drivers/STM32F0xx_HAL_Driver/Src/stm32f0xx_hal_gpio.c:475:15: note: GPIOx->LCKR is assigned
  GPIOx->LCKR = GPIO_Pin;
              ^
Firmware/mock/nucleof030r8/ir_sensor_mock/Drivers/STM32F0xx_HAL_Driver/Src/stm32f0xx_hal_gpio.c:477:15: note: GPIOx->LCKR is overwritten
  GPIOx->LCKR = tmp;
              ^
Firmware/mock/nucleof030r8/ir_sensor_mock/Drivers/STM32F0xx_HAL_Driver/Src/stm32f0xx_hal_gpio.c:172:12: style: The scope of the variable 'iocurrent' can be reduced. [variableScope]
  uint32_t iocurrent;
           ^
Firmware/mock/nucleof030r8/ir_sensor_mock/Drivers/STM32F0xx_HAL_Driver/Src/stm32f0xx_hal_gpio.c:302:12: style: The scope of the variable 'iocurrent' can be reduced. [variableScope]
  uint32_t iocurrent;
           ^
Firmware/mock/nucleof030r8/ir_sensor_mock/Drivers/STM32F0xx_HAL_Driver/Src/stm32f0xx_hal_i2c.c:600:26: style: Variable 'hi2c->Instance->OAR1' is reassigned a value before the old one has been used. [redundantAssignment]
    hi2c->Instance->OAR1 = (I2C_OAR1_OA1EN | hi2c->Init.OwnAddress1);
                         ^
Firmware/mock/nucleof030r8/ir_sensor_mock/Drivers/STM32F0xx_HAL_Driver/Src/stm32f0xx_hal_i2c.c:595:24: note: hi2c->Instance->OAR1 is assigned
  hi2c->Instance->OAR1 &= ~I2C_OAR1_OA1EN;
                       ^
Firmware/mock/nucleof030r8/ir_sensor_mock/Drivers/STM32F0xx_HAL_Driver/Src/stm32f0xx_hal_i2c.c:600:26: note: hi2c->Instance->OAR1 is overwritten
    hi2c->Instance->OAR1 = (I2C_OAR1_OA1EN | hi2c->Init.OwnAddress1);
                         ^
Firmware/mock/nucleof030r8/ir_sensor_mock/Drivers/STM32F0xx_HAL_Driver/Src/stm32f0xx_hal_i2c.c:626:24: style: Variable 'hi2c->Instance->OAR2' is reassigned a value before the old one has been used. [redundantAssignment]
  hi2c->Instance->OAR2 = (hi2c->Init.DualAddressMode | hi2c->Init.OwnAddress2 | \
                       ^
Firmware/mock/nucleof030r8/ir_sensor_mock/Drivers/STM32F0xx_HAL_Driver/Src/stm32f0xx_hal_i2c.c:623:24: note: hi2c->Instance->OAR2 is assigned
  hi2c->Instance->OAR2 &= ~I2C_DUALADDRESS_ENABLE;
                       ^
Firmware/mock/nucleof030r8/ir_sensor_mock/Drivers/STM32F0xx_HAL_Driver/Src/stm32f0xx_hal_i2c.c:626:24: note: hi2c->Instance->OAR2 is overwritten
  hi2c->Instance->OAR2 = (hi2c->Init.DualAddressMode | hi2c->Init.OwnAddress2 | \
                       ^
Firmware/mock/nucleof030r8/ir_sensor_mock/Drivers/STM32F0xx_HAL_Driver/Src/stm32f0xx_hal_i2c.c:1122:12: style: The scope of the variable 'tickstart' can be reduced. [variableScope]
  uint32_t tickstart;
           ^
Firmware/mock/nucleof030r8/ir_sensor_mock/Drivers/STM32F0xx_HAL_Driver/Src/stm32f0xx_hal_i2c.c:1123:12: style: The scope of the variable 'xfermode' can be reduced. [variableScope]
  uint32_t xfermode;
           ^
Firmware/mock/nucleof030r8/ir_sensor_mock/Drivers/STM32F0xx_HAL_Driver/Src/stm32f0xx_hal_i2c.c:1263:12: style: The scope of the variable 'tickstart' can be reduced. [variableScope]
  uint32_t tickstart;
           ^
Firmware/mock/nucleof030r8/ir_sensor_mock/Drivers/STM32F0xx_HAL_Driver/Src/stm32f0xx_hal_i2c.c:1381:12: style: The scope of the variable 'tickstart' can be reduced. [variableScope]
  uint32_t tickstart;
           ^
Firmware/mock/nucleof030r8/ir_sensor_mock/Drivers/STM32F0xx_HAL_Driver/Src/stm32f0xx_hal_i2c.c:1382:12: style: The scope of the variable 'tmpXferCount' can be reduced. [variableScope]
  uint16_t tmpXferCount;
           ^
Firmware/mock/nucleof030r8/ir_sensor_mock/Drivers/STM32F0xx_HAL_Driver/Src/stm32f0xx_hal_i2c.c:1568:12: style: The scope of the variable 'tickstart' can be reduced. [variableScope]
  uint32_t tickstart;
           ^
Firmware/mock/nucleof030r8/ir_sensor_mock/Drivers/STM32F0xx_HAL_Driver/Src/stm32f0xx_hal_i2c.c:1698:12: style: The scope of the variable 'xfermode' can be reduced. [variableScope]
  uint32_t xfermode;
           ^
Firmware/mock/nucleof030r8/ir_sensor_mock/Drivers/STM32F0xx_HAL_Driver/Src/stm32f0xx_hal_i2c.c:1788:12: style: The scope of the variable 'xfermode' can be reduced. [variableScope]
  uint32_t xfermode;
           ^
Firmware/mock/nucleof030r8/ir_sensor_mock/Drivers/STM32F0xx_HAL_Driver/Src/stm32f0xx_hal_i2c.c:1973:12: style: The scope of the variable 'xfermode' can be reduced. [variableScope]
  uint32_t xfermode;
           ^
Firmware/mock/nucleof030r8/ir_sensor_mock/Drivers/STM32F0xx_HAL_Driver/Src/stm32f0xx_hal_i2c.c:1975:12: style: The scope of the variable 'sizetoxfer' can be reduced. [variableScope]
  uint32_t sizetoxfer = 0U;
           ^
Firmware/mock/nucleof030r8/ir_sensor_mock/Drivers/STM32F0xx_HAL_Driver/Src/stm32f0xx_hal_i2c.c:2136:12: style: The scope of the variable 'xfermode' can be reduced. [variableScope]
  uint32_t xfermode;
           ^
Firmware/mock/nucleof030r8/ir_sensor_mock/Drivers/STM32F0xx_HAL_Driver/Src/stm32f0xx_hal_i2c.c:2526:12: style: The scope of the variable 'tickstart' can be reduced. [variableScope]
  uint32_t tickstart;
           ^
Firmware/mock/nucleof030r8/ir_sensor_mock/Drivers/STM32F0xx_HAL_Driver/Src/stm32f0xx_hal_i2c.c:2663:12: style: The scope of the variable 'tickstart' can be reduced. [variableScope]
  uint32_t tickstart;
           ^
Firmware/mock/nucleof030r8/ir_sensor_mock/Drivers/STM32F0xx_HAL_Driver/Src/stm32f0xx_hal_i2c.c:3266:12: style: The scope of the variable 'tickstart' can be reduced. [variableScope]
  uint32_t tickstart;
           ^
Firmware/mock/nucleof030r8/ir_sensor_mock/Drivers/STM32F0xx_HAL_Driver/Src/stm32f0xx_hal_i2c.c:3392:12: style: The scope of the variable 'xfermode' can be reduced. [variableScope]
  uint32_t xfermode;
           ^
Firmware/mock/nucleof030r8/ir_sensor_mock/Drivers/STM32F0xx_HAL_Driver/Src/stm32f0xx_hal_i2c.c:3394:12: style: The scope of the variable 'sizetoxfer' can be reduced. [variableScope]
  uint32_t sizetoxfer = 0U;
           ^
Firmware/mock/nucleof030r8/ir_sensor_mock/Drivers/STM32F0xx_HAL_Driver/Src/stm32f0xx_hal_i2c.c:3506:12: style: The scope of the variable 'xfermode' can be reduced. [variableScope]
  uint32_t xfermode;
           ^
Firmware/mock/nucleof030r8/ir_sensor_mock/Drivers/STM32F0xx_HAL_Driver/Src/stm32f0xx_hal_i2c.c:3509:12: style: The scope of the variable 'sizetoxfer' can be reduced. [variableScope]
  uint32_t sizetoxfer = 0U;
           ^
Firmware/mock/nucleof030r8/ir_sensor_mock/Drivers/STM32F0xx_HAL_Driver/Src/stm32f0xx_hal_i2c.c:3703:12: style: The scope of the variable 'xfermode' can be reduced. [variableScope]
  uint32_t xfermode;
           ^
Firmware/mock/nucleof030r8/ir_sensor_mock/Drivers/STM32F0xx_HAL_Driver/Src/stm32f0xx_hal_i2c.c:3790:12: style: The scope of the variable 'xfermode' can be reduced. [variableScope]
  uint32_t xfermode;
           ^
Firmware/mock/nucleof030r8/ir_sensor_mock/Drivers/STM32F0xx_HAL_Driver/Src/stm32f0xx_hal_i2c.c:4544:12: style: The scope of the variable 'tmp' can be reduced. [variableScope]
  uint32_t tmp;
           ^
Firmware/mock/nucleof030r8/ir_sensor_mock/Drivers/STM32F0xx_HAL_Driver/Src/stm32f0xx_hal_i2c.c:7198:12: style: The scope of the variable 'tmp1' can be reduced. [variableScope]
  uint32_t tmp1;
           ^
Firmware/mock/nucleof030r8/ir_sensor_mock/Drivers/STM32F0xx_HAL_Driver/Src/stm32f0xx_hal_i2c_ex.c:142:12: style: The scope of the variable 'tmpreg' can be reduced. [variableScope]
  uint32_t tmpreg;
           ^
Firmware/mock/nucleof030r8/ir_sensor_mock/Drivers/STM32F0xx_HAL_Driver/Src/stm32f0xx_hal_i2c_ex.c:225:0: information: Skipping configuration 'HAL_I2C_MODULE_ENABLED;I2C_CR1_WUPEN' since the value of 'I2C_CR1_WUPEN' is unknown. Use -D if you want to check it. You can use -U to skip it explicitly. [ConfigurationNotChecked]
    hi2c->Instance->CR1 |= I2C_CR1_WUPEN;
^
Firmware/mock/nucleof030r8/ir_sensor_mock/Drivers/STM32F0xx_HAL_Driver/Src/stm32f0xx_hal_i2c_ex.c:264:0: information: Skipping configuration 'HAL_I2C_MODULE_ENABLED;I2C_CR1_WUPEN' since the value of 'I2C_CR1_WUPEN' is unknown. Use -D if you want to check it. You can use -U to skip it explicitly. [ConfigurationNotChecked]
    hi2c->Instance->CR1 &= ~(I2C_CR1_WUPEN);
^
Firmware/mock/nucleof030r8/ir_sensor_mock/Drivers/STM32F0xx_HAL_Driver/Src/stm32f0xx_hal_i2s.c:410:0: information: Skipping configuration 'HAL_I2S_MODULE_ENABLED;SPI_I2SCFGR_ASTRTEN;SPI_I2S_SUPPORT' since the value of 'SPI_I2SCFGR_ASTRTEN' is unknown. Use -D if you want to check it. You can use -U to skip it explicitly. [ConfigurationNotChecked]
    SET_BIT(hi2s->Instance->I2SCFGR, SPI_I2SCFGR_ASTRTEN);
^
Firmware/mock/nucleof030r8/ir_sensor_mock/Drivers/STM32F0xx_HAL_Driver/Src/stm32f0xx_hal_i2s.c:1434:15: style: Variable 'hi2s->State' is reassigned a value before the old one has been used. [redundantAssignment]
  hi2s->State = HAL_I2S_STATE_READY;
              ^
Firmware/mock/nucleof030r8/ir_sensor_mock/Drivers/STM32F0xx_HAL_Driver/Src/stm32f0xx_hal_i2s.c:1424:19: note: hi2s->State is assigned
      hi2s->State = HAL_I2S_STATE_READY;
                  ^
Firmware/mock/nucleof030r8/ir_sensor_mock/Drivers/STM32F0xx_HAL_Driver/Src/stm32f0xx_hal_i2s.c:1434:15: note: hi2s->State is overwritten
  hi2s->State = HAL_I2S_STATE_READY;
              ^
Firmware/mock/nucleof030r8/ir_sensor_mock/Drivers/STM32F0xx_HAL_Driver/Src/stm32f0xx_hal_irda.c:815:19: style: The scope of the variable 'pdata8bits' can be reduced. [variableScope]
  const uint8_t  *pdata8bits;
                  ^
Firmware/mock/nucleof030r8/ir_sensor_mock/Drivers/STM32F0xx_HAL_Driver/Src/stm32f0xx_hal_irda.c:816:19: style: The scope of the variable 'pdata16bits' can be reduced. [variableScope]
  const uint16_t *pdata16bits;
                  ^
Firmware/mock/nucleof030r8/ir_sensor_mock/Drivers/STM32F0xx_HAL_Driver/Src/stm32f0xx_hal_irda.c:817:12: style: The scope of the variable 'tickstart' can be reduced. [variableScope]
  uint32_t tickstart;
           ^
Firmware/mock/nucleof030r8/ir_sensor_mock/Drivers/STM32F0xx_HAL_Driver/Src/stm32f0xx_hal_irda.c:922:13: style: The scope of the variable 'pdata8bits' can be reduced. [variableScope]
  uint8_t  *pdata8bits;
            ^
Firmware/mock/nucleof030r8/ir_sensor_mock/Drivers/STM32F0xx_HAL_Driver/Src/stm32f0xx_hal_irda.c:923:13: style: The scope of the variable 'pdata16bits' can be reduced. [variableScope]
  uint16_t *pdata16bits;
            ^
Firmware/mock/nucleof030r8/ir_sensor_mock/Drivers/STM32F0xx_HAL_Driver/Src/stm32f0xx_hal_irda.c:925:12: style: The scope of the variable 'tickstart' can be reduced. [variableScope]
  uint32_t tickstart;
           ^
Firmware/mock/nucleof030r8/ir_sensor_mock/Drivers/STM32F0xx_HAL_Driver/Src/stm32f0xx_hal_irda.c:2885:19: style: The scope of the variable 'tmp' can be reduced. [variableScope]
  const uint16_t *tmp;
                  ^
Firmware/mock/nucleof030r8/ir_sensor_mock/Drivers/STM32F0xx_HAL_Driver/Src/stm32f0xx_hal_rcc_ex.c:0:0: information: Too many #ifdef configurations - cppcheck only checks 12 of 13 configurations. Use --force to check all configurations. [toomanyconfigs]

^
Firmware/mock/nucleof030r8/ir_sensor_mock/Drivers/STM32F0xx_HAL_Driver/Src/stm32f0xx_hal_rcc_ex.c:104:22: style: Variable 'tickstart' is assigned a value that is never used. [unreadVariable]
  uint32_t tickstart = 0U;
                     ^
Firmware/mock/nucleof030r8/ir_sensor_mock/Drivers/STM32F0xx_HAL_Driver/Src/stm32f0xx_hal_rcc_ex.c:105:21: style: Variable 'temp_reg' is assigned a value that is never used. [unreadVariable]
  uint32_t temp_reg = 0U;
                    ^
Firmware/mock/nucleof030r8/ir_sensor_mock/Drivers/STM32F0xx_HAL_Driver/Src/stm32f0xx_hal_rcc_ex.c:683:0: information: Skipping configuration 'CRS;HAL_RCC_MODULE_ENABLED' since the value of 'CRS' is unknown. Use -D if you want to check it. You can use -U to skip it explicitly. [ConfigurationNotChecked]
  WRITE_REG(CRS->CFGR, value);
^
Firmware/mock/nucleof030r8/ir_sensor_mock/Drivers/STM32F0xx_HAL_Driver/Src/stm32f0xx_hal_rcc_ex.c:687:0: information: Skipping configuration 'CRS;HAL_RCC_MODULE_ENABLED' since the value of 'CRS' is unknown. Use -D if you want to check it. You can use -U to skip it explicitly. [ConfigurationNotChecked]
  MODIFY_REG(CRS->CR, CRS_CR_TRIM, (pInit->HSI48CalibrationValue << CRS_CR_TRIM_BITNUMBER));
^
Firmware/mock/nucleof030r8/ir_sensor_mock/Drivers/STM32F0xx_HAL_Driver/Src/stm32f0xx_hal_rcc_ex.c:692:0: information: Skipping configuration 'CRS;HAL_RCC_MODULE_ENABLED' since the value of 'CRS' is unknown. Use -D if you want to check it. You can use -U to skip it explicitly. [ConfigurationNotChecked]
  SET_BIT(CRS->CR, CRS_CR_AUTOTRIMEN | CRS_CR_CEN);
^
Firmware/mock/nucleof030r8/ir_sensor_mock/Drivers/STM32F0xx_HAL_Driver/Src/stm32f0xx_hal_rcc_ex.c:701:0: information: Skipping configuration 'CRS;HAL_RCC_MODULE_ENABLED' since the value of 'CRS' is unknown. Use -D if you want to check it. You can use -U to skip it explicitly. [ConfigurationNotChecked]
  SET_BIT(CRS->CR, CRS_CR_SWSYNC);
^
Firmware/mock/nucleof030r8/ir_sensor_mock/Drivers/STM32F0xx_HAL_Driver/Src/stm32f0xx_hal_rcc_ex.c:715:0: information: Skipping configuration 'CRS;HAL_RCC_MODULE_ENABLED' since the value of 'CRS' is unknown. Use -D if you want to check it. You can use -U to skip it explicitly. [ConfigurationNotChecked]
  pSynchroInfo->ReloadValue = (uint32_t)(READ_BIT(CRS->CFGR, CRS_CFGR_RELOAD));
^
Firmware/mock/nucleof030r8/ir_sensor_mock/Drivers/STM32F0xx_HAL_Driver/Src/stm32f0xx_hal_rcc_ex.c:718:0: information: Skipping configuration 'CRS;HAL_RCC_MODULE_ENABLED' since the value of 'CRS' is unknown. Use -D if you want to check it. You can use -U to skip it explicitly. [ConfigurationNotChecked]
  pSynchroInfo->HSI48CalibrationValue = (uint32_t)(READ_BIT(CRS->CR, CRS_CR_TRIM) >> CRS_CR_TRIM_BITNUMBER);
^
Firmware/mock/nucleof030r8/ir_sensor_mock/Drivers/STM32F0xx_HAL_Driver/Src/stm32f0xx_hal_rcc_ex.c:721:0: information: Skipping configuration 'CRS;HAL_RCC_MODULE_ENABLED' since the value of 'CRS' is unknown. Use -D if you want to check it. You can use -U to skip it explicitly. [ConfigurationNotChecked]
  pSynchroInfo->FreqErrorCapture = (uint32_t)(READ_BIT(CRS->ISR, CRS_ISR_FECAP) >> CRS_ISR_FECAP_BITNUMBER);
^
Firmware/mock/nucleof030r8/ir_sensor_mock/Drivers/STM32F0xx_HAL_Driver/Src/stm32f0xx_hal_rcc_ex.c:724:0: information: Skipping configuration 'CRS;HAL_RCC_MODULE_ENABLED' since the value of 'CRS' is unknown. Use -D if you want to check it. You can use -U to skip it explicitly. [ConfigurationNotChecked]
  pSynchroInfo->FreqErrorDirection = (uint32_t)(READ_BIT(CRS->ISR, CRS_ISR_FEDIR));
^
Firmware/mock/nucleof030r8/ir_sensor_mock/Drivers/STM32F0xx_HAL_Driver/Src/stm32f0xx_hal_rcc_ex.c:829:0: information: Skipping configuration 'CRS;HAL_RCC_MODULE_ENABLED' since the value of 'CRS' is unknown. Use -D if you want to check it. You can use -U to skip it explicitly. [ConfigurationNotChecked]
  uint32_t itflags = READ_REG(CRS->ISR);
^
Firmware/mock/nucleof030r8/ir_sensor_mock/Drivers/STM32F0xx_HAL_Driver/Src/stm32f0xx_hal_rcc_ex.c:830:0: information: Skipping configuration 'CRS;HAL_RCC_MODULE_ENABLED' since the value of 'CRS' is unknown. Use -D if you want to check it. You can use -U to skip it explicitly. [ConfigurationNotChecked]
  uint32_t itsources = READ_REG(CRS->CR);
^
Firmware/mock/nucleof030r8/ir_sensor_mock/Drivers/STM32F0xx_HAL_Driver/Src/stm32f0xx_hal_rcc_ex.c:836:0: information: Skipping configuration 'CRS;HAL_RCC_MODULE_ENABLED' since the value of 'CRS' is unknown. Use -D if you want to check it. You can use -U to skip it explicitly. [ConfigurationNotChecked]
    WRITE_REG(CRS->ICR, CRS_ICR_SYNCOKC);
^
Firmware/mock/nucleof030r8/ir_sensor_mock/Drivers/STM32F0xx_HAL_Driver/Src/stm32f0xx_hal_rcc_ex.c:845:0: information: Skipping configuration 'CRS;HAL_RCC_MODULE_ENABLED' since the value of 'CRS' is unknown. Use -D if you want to check it. You can use -U to skip it explicitly. [ConfigurationNotChecked]
    WRITE_REG(CRS->ICR, CRS_ICR_SYNCWARNC);
^
Firmware/mock/nucleof030r8/ir_sensor_mock/Drivers/STM32F0xx_HAL_Driver/Src/stm32f0xx_hal_rcc_ex.c:854:0: information: Skipping configuration 'CRS;HAL_RCC_MODULE_ENABLED' since the value of 'CRS' is unknown. Use -D if you want to check it. You can use -U to skip it explicitly. [ConfigurationNotChecked]
    WRITE_REG(CRS->ICR, CRS_ICR_ESYNCC);
^
Firmware/mock/nucleof030r8/ir_sensor_mock/Drivers/STM32F0xx_HAL_Driver/Src/stm32f0xx_hal_rcc_ex.c:878:0: information: Skipping configuration 'CRS;HAL_RCC_MODULE_ENABLED' since the value of 'CRS' is unknown. Use -D if you want to check it. You can use -U to skip it explicitly. [ConfigurationNotChecked]
      WRITE_REG(CRS->ICR, CRS_ICR_ERRC);
^
Firmware/mock/nucleof030r8/ir_sensor_mock/Drivers/STM32F0xx_HAL_Driver/Src/stm32f0xx_hal_rtc.c:1684:12: style: The scope of the variable 'tickstart' can be reduced. [variableScope]
  uint32_t tickstart = 0U;
           ^
Firmware/mock/nucleof030r8/ir_sensor_mock/Drivers/STM32F0xx_HAL_Driver/Src/stm32f0xx_hal_rtc.c:1684:22: style: Variable 'tickstart' is assigned a value that is never used. [unreadVariable]
  uint32_t tickstart = 0U;
                     ^
Firmware/mock/nucleof030r8/ir_sensor_mock/Drivers/STM32F0xx_HAL_Driver/Src/stm32f0xx_hal_rtc_ex.c:448:15: style: Variable 'hrtc->State' is reassigned a value before the old one has been used. [redundantAssignment]
  hrtc->State = HAL_RTC_STATE_READY;
              ^
Firmware/mock/nucleof030r8/ir_sensor_mock/Drivers/STM32F0xx_HAL_Driver/Src/stm32f0xx_hal_rtc_ex.c:407:15: note: hrtc->State is assigned
  hrtc->State = HAL_RTC_STATE_BUSY;
              ^
Firmware/mock/nucleof030r8/ir_sensor_mock/Drivers/STM32F0xx_HAL_Driver/Src/stm32f0xx_hal_rtc_ex.c:448:15: note: hrtc->State is overwritten
  hrtc->State = HAL_RTC_STATE_READY;
              ^
Firmware/mock/nucleof030r8/ir_sensor_mock/Drivers/STM32F0xx_HAL_Driver/Src/stm32f0xx_hal_rtc_ex.c:560:15: style: Variable 'hrtc->State' is reassigned a value before the old one has been used. [redundantAssignment]
  hrtc->State = HAL_RTC_STATE_READY;
              ^
Firmware/mock/nucleof030r8/ir_sensor_mock/Drivers/STM32F0xx_HAL_Driver/Src/stm32f0xx_hal_rtc_ex.c:555:15: note: hrtc->State is assigned
  hrtc->State = HAL_RTC_STATE_BUSY;
              ^
Firmware/mock/nucleof030r8/ir_sensor_mock/Drivers/STM32F0xx_HAL_Driver/Src/stm32f0xx_hal_rtc_ex.c:560:15: note: hrtc->State is overwritten
  hrtc->State = HAL_RTC_STATE_READY;
              ^
Firmware/mock/nucleof030r8/ir_sensor_mock/Drivers/STM32F0xx_HAL_Driver/Src/stm32f0xx_hal_rtc_ex.c:1343:12: style: The scope of the variable 'tickstart' can be reduced. [variableScope]
  uint32_t tickstart = 0U;
           ^
Firmware/mock/nucleof030r8/ir_sensor_mock/Drivers/STM32F0xx_HAL_Driver/Src/stm32f0xx_hal_rtc_ex.c:1343:22: style: Variable 'tickstart' is assigned a value that is never used. [unreadVariable]
  uint32_t tickstart = 0U;
                     ^
Firmware/mock/nucleof030r8/ir_sensor_mock/Drivers/STM32F0xx_HAL_Driver/Src/stm32f0xx_hal_smbus.c:350:30: style: Variable 'hsmbus->Instance->TIMEOUTR' is reassigned a value before the old one has been used. [redundantAssignment]
  hsmbus->Instance->TIMEOUTR = hsmbus->Init.SMBusTimeout;
                             ^
Firmware/mock/nucleof030r8/ir_sensor_mock/Drivers/STM32F0xx_HAL_Driver/Src/stm32f0xx_hal_smbus.c:349:30: note: hsmbus->Instance->TIMEOUTR is assigned
  hsmbus->Instance->TIMEOUTR &= ~I2C_TIMEOUTR_TEXTEN;
                             ^
Firmware/mock/nucleof030r8/ir_sensor_mock/Drivers/STM32F0xx_HAL_Driver/Src/stm32f0xx_hal_smbus.c:350:30: note: hsmbus->Instance->TIMEOUTR is overwritten
  hsmbus->Instance->TIMEOUTR = hsmbus->Init.SMBusTimeout;
                             ^
Firmware/mock/nucleof030r8/ir_sensor_mock/Drivers/STM32F0xx_HAL_Driver/Src/stm32f0xx_hal_smbus.c:540:12: style: The scope of the variable 'tmpreg' can be reduced. [variableScope]
  uint32_t tmpreg;
           ^
Firmware/mock/nucleof030r8/ir_sensor_mock/Drivers/STM32F0xx_HAL_Driver/Src/stm32f0xx_hal_smbus.c:928:12: style: The scope of the variable 'tmp' can be reduced. [variableScope]
  uint32_t tmp;
           ^
Firmware/mock/nucleof030r8/ir_sensor_mock/Drivers/STM32F0xx_HAL_Driver/Src/stm32f0xx_hal_smbus.c:929:12: style: The scope of the variable 'sizetoxfer' can be reduced. [variableScope]
  uint32_t sizetoxfer;
           ^
Firmware/mock/nucleof030r8/ir_sensor_mock/Drivers/STM32F0xx_HAL_Driver/Src/stm32f0xx_hal_smbus.c:1066:12: style: The scope of the variable 'tmp' can be reduced. [variableScope]
  uint32_t tmp;
           ^
Firmware/mock/nucleof030r8/ir_sensor_mock/Drivers/STM32F0xx_HAL_Driver/Src/stm32f0xx_hal_smbus.c:1486:12: style: The scope of the variable 'tickstart' can be reduced. [variableScope]
  uint32_t tickstart;
           ^
Firmware/mock/nucleof030r8/ir_sensor_mock/Drivers/STM32F0xx_HAL_Driver/Src/stm32f0xx_hal_spi.c:474:0: information: Skipping configuration 'HAL_SPI_MODULE_ENABLED;SPI_I2SCFGR_I2SMOD' since the value of 'SPI_I2SCFGR_I2SMOD' is unknown. Use -D if you want to check it. You can use -U to skip it explicitly. [ConfigurationNotChecked]
  CLEAR_BIT(hspi->Instance->I2SCFGR, SPI_I2SCFGR_I2SMOD);
^
Firmware/mock/nucleof030r8/ir_sensor_mock/Drivers/STM32F0xx_HAL_Driver/Src/stm32f0xx_hal_tim.c:5153:15: style: Variable 'htim->State' is reassigned a value before the old one has been used. [redundantAssignment]
  htim->State = HAL_TIM_STATE_READY;
              ^
Firmware/mock/nucleof030r8/ir_sensor_mock/Drivers/STM32F0xx_HAL_Driver/Src/stm32f0xx_hal_tim.c:5147:15: note: htim->State is assigned
  htim->State = HAL_TIM_STATE_BUSY;
              ^
Firmware/mock/nucleof030r8/ir_sensor_mock/Drivers/STM32F0xx_HAL_Driver/Src/stm32f0xx_hal_tim.c:5153:15: note: htim->State is overwritten
  htim->State = HAL_TIM_STATE_READY;
              ^
Firmware/mock/nucleof030r8/ir_sensor_mock/Drivers/STM32F0xx_HAL_Driver/Src/stm32f0xx_hal_tim.c:7193:28: style: Variable 'htim->Instance->CCER' is reassigned a value before the old one has been used. [redundantAssignment]
      htim->Instance->CCER = tmpccer;
                           ^
Firmware/mock/nucleof030r8/ir_sensor_mock/Drivers/STM32F0xx_HAL_Driver/Src/stm32f0xx_hal_tim.c:7184:28: note: htim->Instance->CCER is assigned
      htim->Instance->CCER &= ~TIM_CCER_CC1E;
                           ^
Firmware/mock/nucleof030r8/ir_sensor_mock/Drivers/STM32F0xx_HAL_Driver/Src/stm32f0xx_hal_tim.c:7193:28: note: htim->Instance->CCER is overwritten
      htim->Instance->CCER = tmpccer;
                           ^
Firmware/mock/nucleof030r8/ir_sensor_mock/Drivers/STM32F0xx_HAL_Driver/Src/stm32f0xx_hal_tim.c:7330:14: style: Variable 'TIMx->CCER' is reassigned a value before the old one has been used. [redundantAssignment]
  TIMx->CCER = tmpccer;
             ^
Firmware/mock/nucleof030r8/ir_sensor_mock/Drivers/STM32F0xx_HAL_Driver/Src/stm32f0xx_hal_tim.c:7317:14: note: TIMx->CCER is assigned
  TIMx->CCER &= ~TIM_CCER_CC1E;
             ^
Firmware/mock/nucleof030r8/ir_sensor_mock/Drivers/STM32F0xx_HAL_Driver/Src/stm32f0xx_hal_tim.c:7330:14: note: TIMx->CCER is overwritten
  TIMx->CCER = tmpccer;
             ^
Firmware/mock/nucleof030r8/ir_sensor_mock/Drivers/STM32F0xx_HAL_Driver/Src/stm32f0xx_hal_tim.c:7378:14: style: Variable 'TIMx->CCER' is reassigned a value before the old one has been used. [redundantAssignment]
  TIMx->CCER = tmpccer;
             ^
Firmware/mock/nucleof030r8/ir_sensor_mock/Drivers/STM32F0xx_HAL_Driver/Src/stm32f0xx_hal_tim.c:7361:14: note: TIMx->CCER is assigned
  TIMx->CCER &= ~TIM_CCER_CC2E;
             ^
Firmware/mock/nucleof030r8/ir_sensor_mock/Drivers/STM32F0xx_HAL_Driver/Src/stm32f0xx_hal_tim.c:7378:14: note: TIMx->CCER is overwritten
  TIMx->CCER = tmpccer;
             ^
Firmware/mock/nucleof030r8/ir_sensor_mock/Drivers/STM32F0xx_HAL_Driver/Src/stm32f0xx_hal_tim.c:7413:14: style: Variable 'TIMx->CCER' is reassigned a value before the old one has been used. [redundantAssignment]
  TIMx->CCER = tmpccer;
             ^
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
  const uint8_t  *pdata8bits;
                  ^
Firmware/mock/nucleof030r8/ir_sensor_mock/Drivers/STM32F0xx_HAL_Driver/Src/stm32f0xx_hal_uart.c:1152:19: style: The scope of the variable 'pdata16bits' can be reduced. [variableScope]
  const uint16_t *pdata16bits;
                  ^
Firmware/mock/nucleof030r8/ir_sensor_mock/Drivers/STM32F0xx_HAL_Driver/Src/stm32f0xx_hal_uart.c:1153:12: style: The scope of the variable 'tickstart' can be reduced. [variableScope]
  uint32_t tickstart;
           ^
Firmware/mock/nucleof030r8/ir_sensor_mock/Drivers/STM32F0xx_HAL_Driver/Src/stm32f0xx_hal_uart.c:1253:13: style: The scope of the variable 'pdata8bits' can be reduced. [variableScope]
  uint8_t  *pdata8bits;
            ^
Firmware/mock/nucleof030r8/ir_sensor_mock/Drivers/STM32F0xx_HAL_Driver/Src/stm32f0xx_hal_uart.c:1254:13: style: The scope of the variable 'pdata16bits' can be reduced. [variableScope]
  uint16_t *pdata16bits;
            ^
Firmware/mock/nucleof030r8/ir_sensor_mock/Drivers/STM32F0xx_HAL_Driver/Src/stm32f0xx_hal_uart.c:1256:12: style: The scope of the variable 'tickstart' can be reduced. [variableScope]
  uint32_t tickstart;
           ^
Firmware/mock/nucleof030r8/ir_sensor_mock/Drivers/STM32F0xx_HAL_Driver/Src/stm32f0xx_hal_uart.c:3040:12: style: The scope of the variable 'brrtemp' can be reduced. [variableScope]
  uint16_t brrtemp;
           ^
Firmware/mock/nucleof030r8/ir_sensor_mock/Drivers/STM32F0xx_HAL_Driver/Src/stm32f0xx_hal_uart.c:3941:19: style: The scope of the variable 'tmp' can be reduced. [variableScope]
  const uint16_t *tmp;
                  ^
Firmware/mock/nucleof030r8/ir_sensor_mock/Drivers/STM32F0xx_HAL_Driver/Src/stm32f0xx_hal_uart.c:2541:0: information: Skipping configuration 'HAL_UART_MODULE_ENABLED;USART_CR1_UESM;USART_CR3_WUFIE' since the value of 'USART_CR3_WUFIE' is unknown. Use -D if you want to check it. You can use -U to skip it explicitly. [ConfigurationNotChecked]
  if (((isrflags & USART_ISR_WUF) != 0U) && ((cr3its & USART_CR3_WUFIE) != 0U))
^
Firmware/mock/nucleof030r8/ir_sensor_mock/Drivers/STM32F0xx_HAL_Driver/Src/stm32f0xx_hal_uart.c:350:0: information: Skipping configuration 'HAL_UART_MODULE_ENABLED;USART_CR2_LINEN' since the value of 'USART_CR2_LINEN' is unknown. Use -D if you want to check it. You can use -U to skip it explicitly. [ConfigurationNotChecked]
  CLEAR_BIT(huart->Instance->CR2, (USART_CR2_LINEN | USART_CR2_CLKEN));
^
Firmware/mock/nucleof030r8/ir_sensor_mock/Drivers/STM32F0xx_HAL_Driver/Src/stm32f0xx_hal_uart.c:433:0: information: Skipping configuration 'HAL_UART_MODULE_ENABLED;USART_CR2_LINEN' since the value of 'USART_CR2_LINEN' is unknown. Use -D if you want to check it. You can use -U to skip it explicitly. [ConfigurationNotChecked]
  CLEAR_BIT(huart->Instance->CR2, (USART_CR2_LINEN | USART_CR2_CLKEN));
^
Firmware/mock/nucleof030r8/ir_sensor_mock/Drivers/STM32F0xx_HAL_Driver/Src/stm32f0xx_hal_uart.c:535:0: information: Skipping configuration 'HAL_UART_MODULE_ENABLED;USART_CR2_LINEN' since the value of 'USART_CR2_LINEN' is unknown. Use -D if you want to check it. You can use -U to skip it explicitly. [ConfigurationNotChecked]
  CLEAR_BIT(huart->Instance->CR2, (USART_CR2_LINEN | USART_CR2_CLKEN));
^
Firmware/mock/nucleof030r8/ir_sensor_mock/Drivers/STM32F0xx_HAL_Driver/Src/stm32f0xx_hal_uart.c:551:0: information: Skipping configuration 'HAL_UART_MODULE_ENABLED;USART_CR2_LINEN' since the value of 'USART_CR2_LINEN' is unknown. Use -D if you want to check it. You can use -U to skip it explicitly. [ConfigurationNotChecked]
  SET_BIT(huart->Instance->CR2, USART_CR2_LINEN);
^
Firmware/mock/nucleof030r8/ir_sensor_mock/Drivers/STM32F0xx_HAL_Driver/Src/stm32f0xx_hal_uart.c:635:0: information: Skipping configuration 'HAL_UART_MODULE_ENABLED;USART_CR2_LINEN' since the value of 'USART_CR2_LINEN' is unknown. Use -D if you want to check it. You can use -U to skip it explicitly. [ConfigurationNotChecked]
  CLEAR_BIT(huart->Instance->CR2, (USART_CR2_LINEN | USART_CR2_CLKEN));
^
Firmware/mock/nucleof030r8/ir_sensor_mock/Drivers/STM32F0xx_HAL_Driver/Src/stm32f0xx_hal_uart.c:350:0: information: Skipping configuration 'HAL_UART_MODULE_ENABLED;USART_CR2_LINEN;USART_CR3_IREN' since the value of 'USART_CR2_LINEN' is unknown. Use -D if you want to check it. You can use -U to skip it explicitly. [ConfigurationNotChecked]
  CLEAR_BIT(huart->Instance->CR2, (USART_CR2_LINEN | USART_CR2_CLKEN));
^
Firmware/mock/nucleof030r8/ir_sensor_mock/Drivers/STM32F0xx_HAL_Driver/Src/stm32f0xx_hal_uart.c:433:0: information: Skipping configuration 'HAL_UART_MODULE_ENABLED;USART_CR2_LINEN;USART_CR3_IREN' since the value of 'USART_CR2_LINEN' is unknown. Use -D if you want to check it. You can use -U to skip it explicitly. [ConfigurationNotChecked]
  CLEAR_BIT(huart->Instance->CR2, (USART_CR2_LINEN | USART_CR2_CLKEN));
^
Firmware/mock/nucleof030r8/ir_sensor_mock/Drivers/STM32F0xx_HAL_Driver/Src/stm32f0xx_hal_uart.c:535:0: information: Skipping configuration 'HAL_UART_MODULE_ENABLED;USART_CR2_LINEN;USART_CR3_IREN' since the value of 'USART_CR2_LINEN' is unknown. Use -D if you want to check it. You can use -U to skip it explicitly. [ConfigurationNotChecked]
  CLEAR_BIT(huart->Instance->CR2, (USART_CR2_LINEN | USART_CR2_CLKEN));
^
Firmware/mock/nucleof030r8/ir_sensor_mock/Drivers/STM32F0xx_HAL_Driver/Src/stm32f0xx_hal_uart.c:551:0: information: Skipping configuration 'HAL_UART_MODULE_ENABLED;USART_CR2_LINEN;USART_CR3_IREN' since the value of 'USART_CR2_LINEN' is unknown. Use -D if you want to check it. You can use -U to skip it explicitly. [ConfigurationNotChecked]
  SET_BIT(huart->Instance->CR2, USART_CR2_LINEN);
^
Firmware/mock/nucleof030r8/ir_sensor_mock/Drivers/STM32F0xx_HAL_Driver/Src/stm32f0xx_hal_uart.c:635:0: information: Skipping configuration 'HAL_UART_MODULE_ENABLED;USART_CR2_LINEN;USART_CR3_IREN' since the value of 'USART_CR2_LINEN' is unknown. Use -D if you want to check it. You can use -U to skip it explicitly. [ConfigurationNotChecked]
  CLEAR_BIT(huart->Instance->CR2, (USART_CR2_LINEN | USART_CR2_CLKEN));
^
Firmware/mock/nucleof030r8/ir_sensor_mock/Drivers/STM32F0xx_HAL_Driver/Src/stm32f0xx_hal_uart.c:362:0: information: Skipping configuration 'HAL_UART_MODULE_ENABLED;USART_CR2_LINEN;USART_CR3_IREN' since the value of 'USART_CR3_IREN' is unknown. Use -D if you want to check it. You can use -U to skip it explicitly. [ConfigurationNotChecked]
  CLEAR_BIT(huart->Instance->CR3, (USART_CR3_HDSEL | USART_CR3_IREN));
^
Firmware/mock/nucleof030r8/ir_sensor_mock/Drivers/STM32F0xx_HAL_Driver/Src/stm32f0xx_hal_uart.c:445:0: information: Skipping configuration 'HAL_UART_MODULE_ENABLED;USART_CR2_LINEN;USART_CR3_IREN' since the value of 'USART_CR3_IREN' is unknown. Use -D if you want to check it. You can use -U to skip it explicitly. [ConfigurationNotChecked]
  CLEAR_BIT(huart->Instance->CR3, USART_CR3_IREN);
^
Firmware/mock/nucleof030r8/ir_sensor_mock/Drivers/STM32F0xx_HAL_Driver/Src/stm32f0xx_hal_uart.c:544:0: information: Skipping configuration 'HAL_UART_MODULE_ENABLED;USART_CR2_LINEN;USART_CR3_IREN' since the value of 'USART_CR3_IREN' is unknown. Use -D if you want to check it. You can use -U to skip it explicitly. [ConfigurationNotChecked]
  CLEAR_BIT(huart->Instance->CR3, (USART_CR3_HDSEL | USART_CR3_IREN));
^
Firmware/mock/nucleof030r8/ir_sensor_mock/Drivers/STM32F0xx_HAL_Driver/Src/stm32f0xx_hal_uart.c:647:0: information: Skipping configuration 'HAL_UART_MODULE_ENABLED;USART_CR2_LINEN;USART_CR3_IREN' since the value of 'USART_CR3_IREN' is unknown. Use -D if you want to check it. You can use -U to skip it explicitly. [ConfigurationNotChecked]
  CLEAR_BIT(huart->Instance->CR3, (USART_CR3_HDSEL | USART_CR3_IREN));
^
Firmware/mock/nucleof030r8/ir_sensor_mock/Drivers/STM32F0xx_HAL_Driver/Src/stm32f0xx_hal_uart.c:350:0: information: Skipping configuration 'HAL_UART_MODULE_ENABLED;USART_CR2_LINEN;USART_CR3_IREN;USART_CR3_SCEN' since the value of 'USART_CR2_LINEN' is unknown. Use -D if you want to check it. You can use -U to skip it explicitly. [ConfigurationNotChecked]
  CLEAR_BIT(huart->Instance->CR2, (USART_CR2_LINEN | USART_CR2_CLKEN));
^
Firmware/mock/nucleof030r8/ir_sensor_mock/Drivers/STM32F0xx_HAL_Driver/Src/stm32f0xx_hal_uart.c:433:0: information: Skipping configuration 'HAL_UART_MODULE_ENABLED;USART_CR2_LINEN;USART_CR3_IREN;USART_CR3_SCEN' since the value of 'USART_CR2_LINEN' is unknown. Use -D if you want to check it. You can use -U to skip it explicitly. [ConfigurationNotChecked]
  CLEAR_BIT(huart->Instance->CR2, (USART_CR2_LINEN | USART_CR2_CLKEN));
^
Firmware/mock/nucleof030r8/ir_sensor_mock/Drivers/STM32F0xx_HAL_Driver/Src/stm32f0xx_hal_uart.c:535:0: information: Skipping configuration 'HAL_UART_MODULE_ENABLED;USART_CR2_LINEN;USART_CR3_IREN;USART_CR3_SCEN' since the value of 'USART_CR2_LINEN' is unknown. Use -D if you want to check it. You can use -U to skip it explicitly. [ConfigurationNotChecked]
  CLEAR_BIT(huart->Instance->CR2, (USART_CR2_LINEN | USART_CR2_CLKEN));
^
Firmware/mock/nucleof030r8/ir_sensor_mock/Drivers/STM32F0xx_HAL_Driver/Src/stm32f0xx_hal_uart.c:551:0: information: Skipping configuration 'HAL_UART_MODULE_ENABLED;USART_CR2_LINEN;USART_CR3_IREN;USART_CR3_SCEN' since the value of 'USART_CR2_LINEN' is unknown. Use -D if you want to check it. You can use -U to skip it explicitly. [ConfigurationNotChecked]
  SET_BIT(huart->Instance->CR2, USART_CR2_LINEN);
^
Firmware/mock/nucleof030r8/ir_sensor_mock/Drivers/STM32F0xx_HAL_Driver/Src/stm32f0xx_hal_uart.c:635:0: information: Skipping configuration 'HAL_UART_MODULE_ENABLED;USART_CR2_LINEN;USART_CR3_IREN;USART_CR3_SCEN' since the value of 'USART_CR2_LINEN' is unknown. Use -D if you want to check it. You can use -U to skip it explicitly. [ConfigurationNotChecked]
  CLEAR_BIT(huart->Instance->CR2, (USART_CR2_LINEN | USART_CR2_CLKEN));
^
Firmware/mock/nucleof030r8/ir_sensor_mock/Drivers/STM32F0xx_HAL_Driver/Src/stm32f0xx_hal_uart.c:356:0: information: Skipping configuration 'HAL_UART_MODULE_ENABLED;USART_CR2_LINEN;USART_CR3_IREN;USART_CR3_SCEN' since the value of 'USART_CR3_IREN' is unknown. Use -D if you want to check it. You can use -U to skip it explicitly. [ConfigurationNotChecked]
  CLEAR_BIT(huart->Instance->CR3, (USART_CR3_SCEN | USART_CR3_HDSEL | USART_CR3_IREN));
^
Firmware/mock/nucleof030r8/ir_sensor_mock/Drivers/STM32F0xx_HAL_Driver/Src/stm32f0xx_hal_uart.c:439:0: information: Skipping configuration 'HAL_UART_MODULE_ENABLED;USART_CR2_LINEN;USART_CR3_IREN;USART_CR3_SCEN' since the value of 'USART_CR3_IREN' is unknown. Use -D if you want to check it. You can use -U to skip it explicitly. [ConfigurationNotChecked]
  CLEAR_BIT(huart->Instance->CR3, (USART_CR3_IREN | USART_CR3_SCEN));
^
Firmware/mock/nucleof030r8/ir_sensor_mock/Drivers/STM32F0xx_HAL_Driver/Src/stm32f0xx_hal_uart.c:538:0: information: Skipping configuration 'HAL_UART_MODULE_ENABLED;USART_CR2_LINEN;USART_CR3_IREN;USART_CR3_SCEN' since the value of 'USART_CR3_IREN' is unknown. Use -D if you want to check it. You can use -U to skip it explicitly. [ConfigurationNotChecked]
  CLEAR_BIT(huart->Instance->CR3, (USART_CR3_SCEN | USART_CR3_HDSEL | USART_CR3_IREN));
^
Firmware/mock/nucleof030r8/ir_sensor_mock/Drivers/STM32F0xx_HAL_Driver/Src/stm32f0xx_hal_uart.c:641:0: information: Skipping configuration 'HAL_UART_MODULE_ENABLED;USART_CR2_LINEN;USART_CR3_IREN;USART_CR3_SCEN' since the value of 'USART_CR3_IREN' is unknown. Use -D if you want to check it. You can use -U to skip it explicitly. [ConfigurationNotChecked]
  CLEAR_BIT(huart->Instance->CR3, (USART_CR3_SCEN | USART_CR3_HDSEL | USART_CR3_IREN));
^
Firmware/mock/nucleof030r8/ir_sensor_mock/Drivers/STM32F0xx_HAL_Driver/Src/stm32f0xx_hal_uart.c:356:0: information: Skipping configuration 'HAL_UART_MODULE_ENABLED;USART_CR2_LINEN;USART_CR3_IREN;USART_CR3_SCEN' since the value of 'USART_CR3_SCEN' is unknown. Use -D if you want to check it. You can use -U to skip it explicitly. [ConfigurationNotChecked]
  CLEAR_BIT(huart->Instance->CR3, (USART_CR3_SCEN | USART_CR3_HDSEL | USART_CR3_IREN));
^
Firmware/mock/nucleof030r8/ir_sensor_mock/Drivers/STM32F0xx_HAL_Driver/Src/stm32f0xx_hal_uart.c:439:0: information: Skipping configuration 'HAL_UART_MODULE_ENABLED;USART_CR2_LINEN;USART_CR3_IREN;USART_CR3_SCEN' since the value of 'USART_CR3_SCEN' is unknown. Use -D if you want to check it. You can use -U to skip it explicitly. [ConfigurationNotChecked]
  CLEAR_BIT(huart->Instance->CR3, (USART_CR3_IREN | USART_CR3_SCEN));
^
Firmware/mock/nucleof030r8/ir_sensor_mock/Drivers/STM32F0xx_HAL_Driver/Src/stm32f0xx_hal_uart.c:538:0: information: Skipping configuration 'HAL_UART_MODULE_ENABLED;USART_CR2_LINEN;USART_CR3_IREN;USART_CR3_SCEN' since the value of 'USART_CR3_SCEN' is unknown. Use -D if you want to check it. You can use -U to skip it explicitly. [ConfigurationNotChecked]
  CLEAR_BIT(huart->Instance->CR3, (USART_CR3_SCEN | USART_CR3_HDSEL | USART_CR3_IREN));
^
Firmware/mock/nucleof030r8/ir_sensor_mock/Drivers/STM32F0xx_HAL_Driver/Src/stm32f0xx_hal_uart.c:641:0: information: Skipping configuration 'HAL_UART_MODULE_ENABLED;USART_CR2_LINEN;USART_CR3_IREN;USART_CR3_SCEN' since the value of 'USART_CR3_SCEN' is unknown. Use -D if you want to check it. You can use -U to skip it explicitly. [ConfigurationNotChecked]
  CLEAR_BIT(huart->Instance->CR3, (USART_CR3_SCEN | USART_CR3_HDSEL | USART_CR3_IREN));
^
Firmware/mock/nucleof030r8/ir_sensor_mock/Drivers/STM32F0xx_HAL_Driver/Src/stm32f0xx_hal_uart.c:350:0: information: Skipping configuration 'HAL_UART_MODULE_ENABLED;USART_CR2_LINEN;USART_CR3_SCEN' since the value of 'USART_CR2_LINEN' is unknown. Use -D if you want to check it. You can use -U to skip it explicitly. [ConfigurationNotChecked]
  CLEAR_BIT(huart->Instance->CR2, (USART_CR2_LINEN | USART_CR2_CLKEN));
^
Firmware/mock/nucleof030r8/ir_sensor_mock/Drivers/STM32F0xx_HAL_Driver/Src/stm32f0xx_hal_uart.c:433:0: information: Skipping configuration 'HAL_UART_MODULE_ENABLED;USART_CR2_LINEN;USART_CR3_SCEN' since the value of 'USART_CR2_LINEN' is unknown. Use -D if you want to check it. You can use -U to skip it explicitly. [ConfigurationNotChecked]
  CLEAR_BIT(huart->Instance->CR2, (USART_CR2_LINEN | USART_CR2_CLKEN));
^
Firmware/mock/nucleof030r8/ir_sensor_mock/Drivers/STM32F0xx_HAL_Driver/Src/stm32f0xx_hal_uart.c:535:0: information: Skipping configuration 'HAL_UART_MODULE_ENABLED;USART_CR2_LINEN;USART_CR3_SCEN' since the value of 'USART_CR2_LINEN' is unknown. Use -D if you want to check it. You can use -U to skip it explicitly. [ConfigurationNotChecked]
  CLEAR_BIT(huart->Instance->CR2, (USART_CR2_LINEN | USART_CR2_CLKEN));
^
Firmware/mock/nucleof030r8/ir_sensor_mock/Drivers/STM32F0xx_HAL_Driver/Src/stm32f0xx_hal_uart.c:551:0: information: Skipping configuration 'HAL_UART_MODULE_ENABLED;USART_CR2_LINEN;USART_CR3_SCEN' since the value of 'USART_CR2_LINEN' is unknown. Use -D if you want to check it. You can use -U to skip it explicitly. [ConfigurationNotChecked]
  SET_BIT(huart->Instance->CR2, USART_CR2_LINEN);
^
Firmware/mock/nucleof030r8/ir_sensor_mock/Drivers/STM32F0xx_HAL_Driver/Src/stm32f0xx_hal_uart.c:635:0: information: Skipping configuration 'HAL_UART_MODULE_ENABLED;USART_CR2_LINEN;USART_CR3_SCEN' since the value of 'USART_CR2_LINEN' is unknown. Use -D if you want to check it. You can use -U to skip it explicitly. [ConfigurationNotChecked]
  CLEAR_BIT(huart->Instance->CR2, (USART_CR2_LINEN | USART_CR2_CLKEN));
^
Firmware/mock/nucleof030r8/ir_sensor_mock/Drivers/STM32F0xx_HAL_Driver/Src/stm32f0xx_hal_uart.c:358:0: information: Skipping configuration 'HAL_UART_MODULE_ENABLED;USART_CR2_LINEN;USART_CR3_SCEN' since the value of 'USART_CR3_SCEN' is unknown. Use -D if you want to check it. You can use -U to skip it explicitly. [ConfigurationNotChecked]
  CLEAR_BIT(huart->Instance->CR3, (USART_CR3_SCEN | USART_CR3_HDSEL));
^
Firmware/mock/nucleof030r8/ir_sensor_mock/Drivers/STM32F0xx_HAL_Driver/Src/stm32f0xx_hal_uart.c:441:0: information: Skipping configuration 'HAL_UART_MODULE_ENABLED;USART_CR2_LINEN;USART_CR3_SCEN' since the value of 'USART_CR3_SCEN' is unknown. Use -D if you want to check it. You can use -U to skip it explicitly. [ConfigurationNotChecked]
  CLEAR_BIT(huart->Instance->CR3, USART_CR3_SCEN);
^
Firmware/mock/nucleof030r8/ir_sensor_mock/Drivers/STM32F0xx_HAL_Driver/Src/stm32f0xx_hal_uart.c:540:0: information: Skipping configuration 'HAL_UART_MODULE_ENABLED;USART_CR2_LINEN;USART_CR3_SCEN' since the value of 'USART_CR3_SCEN' is unknown. Use -D if you want to check it. You can use -U to skip it explicitly. [ConfigurationNotChecked]
  CLEAR_BIT(huart->Instance->CR3, (USART_CR3_SCEN | USART_CR3_HDSEL));
^
Firmware/mock/nucleof030r8/ir_sensor_mock/Drivers/STM32F0xx_HAL_Driver/Src/stm32f0xx_hal_uart.c:643:0: information: Skipping configuration 'HAL_UART_MODULE_ENABLED;USART_CR2_LINEN;USART_CR3_SCEN' since the value of 'USART_CR3_SCEN' is unknown. Use -D if you want to check it. You can use -U to skip it explicitly. [ConfigurationNotChecked]
  CLEAR_BIT(huart->Instance->CR3, (USART_CR3_SCEN | USART_CR3_HDSEL));
^
Firmware/mock/nucleof030r8/ir_sensor_mock/Drivers/STM32F0xx_HAL_Driver/Src/stm32f0xx_hal_uart.c:362:0: information: Skipping configuration 'HAL_UART_MODULE_ENABLED;USART_CR3_IREN' since the value of 'USART_CR3_IREN' is unknown. Use -D if you want to check it. You can use -U to skip it explicitly. [ConfigurationNotChecked]
  CLEAR_BIT(huart->Instance->CR3, (USART_CR3_HDSEL | USART_CR3_IREN));
^
Firmware/mock/nucleof030r8/ir_sensor_mock/Drivers/STM32F0xx_HAL_Driver/Src/stm32f0xx_hal_uart.c:445:0: information: Skipping configuration 'HAL_UART_MODULE_ENABLED;USART_CR3_IREN' since the value of 'USART_CR3_IREN' is unknown. Use -D if you want to check it. You can use -U to skip it explicitly. [ConfigurationNotChecked]
  CLEAR_BIT(huart->Instance->CR3, USART_CR3_IREN);
^
Firmware/mock/nucleof030r8/ir_sensor_mock/Drivers/STM32F0xx_HAL_Driver/Src/stm32f0xx_hal_uart.c:647:0: information: Skipping configuration 'HAL_UART_MODULE_ENABLED;USART_CR3_IREN' since the value of 'USART_CR3_IREN' is unknown. Use -D if you want to check it. You can use -U to skip it explicitly. [ConfigurationNotChecked]
  CLEAR_BIT(huart->Instance->CR3, (USART_CR3_HDSEL | USART_CR3_IREN));
^
Firmware/mock/nucleof030r8/ir_sensor_mock/Drivers/STM32F0xx_HAL_Driver/Src/stm32f0xx_hal_uart.c:356:0: information: Skipping configuration 'HAL_UART_MODULE_ENABLED;USART_CR3_IREN;USART_CR3_SCEN' since the value of 'USART_CR3_IREN' is unknown. Use -D if you want to check it. You can use -U to skip it explicitly. [ConfigurationNotChecked]
  CLEAR_BIT(huart->Instance->CR3, (USART_CR3_SCEN | USART_CR3_HDSEL | USART_CR3_IREN));
^
Firmware/mock/nucleof030r8/ir_sensor_mock/Drivers/STM32F0xx_HAL_Driver/Src/stm32f0xx_hal_uart.c:439:0: information: Skipping configuration 'HAL_UART_MODULE_ENABLED;USART_CR3_IREN;USART_CR3_SCEN' since the value of 'USART_CR3_IREN' is unknown. Use -D if you want to check it. You can use -U to skip it explicitly. [ConfigurationNotChecked]
  CLEAR_BIT(huart->Instance->CR3, (USART_CR3_IREN | USART_CR3_SCEN));
^
Firmware/mock/nucleof030r8/ir_sensor_mock/Drivers/STM32F0xx_HAL_Driver/Src/stm32f0xx_hal_uart.c:641:0: information: Skipping configuration 'HAL_UART_MODULE_ENABLED;USART_CR3_IREN;USART_CR3_SCEN' since the value of 'USART_CR3_IREN' is unknown. Use -D if you want to check it. You can use -U to skip it explicitly. [ConfigurationNotChecked]
  CLEAR_BIT(huart->Instance->CR3, (USART_CR3_SCEN | USART_CR3_HDSEL | USART_CR3_IREN));
^
Firmware/mock/nucleof030r8/ir_sensor_mock/Drivers/STM32F0xx_HAL_Driver/Src/stm32f0xx_hal_uart.c:356:0: information: Skipping configuration 'HAL_UART_MODULE_ENABLED;USART_CR3_IREN;USART_CR3_SCEN' since the value of 'USART_CR3_SCEN' is unknown. Use -D if you want to check it. You can use -U to skip it explicitly. [ConfigurationNotChecked]
  CLEAR_BIT(huart->Instance->CR3, (USART_CR3_SCEN | USART_CR3_HDSEL | USART_CR3_IREN));
^
Firmware/mock/nucleof030r8/ir_sensor_mock/Drivers/STM32F0xx_HAL_Driver/Src/stm32f0xx_hal_uart.c:439:0: information: Skipping configuration 'HAL_UART_MODULE_ENABLED;USART_CR3_IREN;USART_CR3_SCEN' since the value of 'USART_CR3_SCEN' is unknown. Use -D if you want to check it. You can use -U to skip it explicitly. [ConfigurationNotChecked]
  CLEAR_BIT(huart->Instance->CR3, (USART_CR3_IREN | USART_CR3_SCEN));
^
Firmware/mock/nucleof030r8/ir_sensor_mock/Drivers/STM32F0xx_HAL_Driver/Src/stm32f0xx_hal_uart.c:641:0: information: Skipping configuration 'HAL_UART_MODULE_ENABLED;USART_CR3_IREN;USART_CR3_SCEN' since the value of 'USART_CR3_SCEN' is unknown. Use -D if you want to check it. You can use -U to skip it explicitly. [ConfigurationNotChecked]
  CLEAR_BIT(huart->Instance->CR3, (USART_CR3_SCEN | USART_CR3_HDSEL | USART_CR3_IREN));
^
Firmware/mock/nucleof030r8/ir_sensor_mock/Drivers/STM32F0xx_HAL_Driver/Src/stm32f0xx_hal_uart.c:358:0: information: Skipping configuration 'HAL_UART_MODULE_ENABLED;USART_CR3_SCEN' since the value of 'USART_CR3_SCEN' is unknown. Use -D if you want to check it. You can use -U to skip it explicitly. [ConfigurationNotChecked]
  CLEAR_BIT(huart->Instance->CR3, (USART_CR3_SCEN | USART_CR3_HDSEL));
^
Firmware/mock/nucleof030r8/ir_sensor_mock/Drivers/STM32F0xx_HAL_Driver/Src/stm32f0xx_hal_uart.c:441:0: information: Skipping configuration 'HAL_UART_MODULE_ENABLED;USART_CR3_SCEN' since the value of 'USART_CR3_SCEN' is unknown. Use -D if you want to check it. You can use -U to skip it explicitly. [ConfigurationNotChecked]
  CLEAR_BIT(huart->Instance->CR3, USART_CR3_SCEN);
^
Firmware/mock/nucleof030r8/ir_sensor_mock/Drivers/STM32F0xx_HAL_Driver/Src/stm32f0xx_hal_uart.c:643:0: information: Skipping configuration 'HAL_UART_MODULE_ENABLED;USART_CR3_SCEN' since the value of 'USART_CR3_SCEN' is unknown. Use -D if you want to check it. You can use -U to skip it explicitly. [ConfigurationNotChecked]
  CLEAR_BIT(huart->Instance->CR3, (USART_CR3_SCEN | USART_CR3_HDSEL));
^
Firmware/mock/nucleof030r8/ir_sensor_mock/Drivers/STM32F0xx_HAL_Driver/Src/stm32f0xx_hal_uart_ex.c:501:13: style: The scope of the variable 'pdata8bits' can be reduced. [variableScope]
  uint8_t  *pdata8bits;
            ^
Firmware/mock/nucleof030r8/ir_sensor_mock/Drivers/STM32F0xx_HAL_Driver/Src/stm32f0xx_hal_uart_ex.c:502:13: style: The scope of the variable 'pdata16bits' can be reduced. [variableScope]
  uint16_t *pdata16bits;
            ^
Firmware/mock/nucleof030r8/ir_sensor_mock/Drivers/STM32F0xx_HAL_Driver/Src/stm32f0xx_hal_uart_ex.c:504:12: style: The scope of the variable 'tickstart' can be reduced. [variableScope]
  uint32_t tickstart;
           ^
Firmware/mock/nucleof030r8/ir_sensor_mock/Drivers/STM32F0xx_HAL_Driver/Src/stm32f0xx_hal_uart_ex.c:448:0: information: Skipping configuration 'HAL_UART_MODULE_ENABLED;USART_CR1_UESM' since the value of 'USART_CR1_UESM' is unknown. Use -D if you want to check it. You can use -U to skip it explicitly. [ConfigurationNotChecked]
  ATOMIC_SET_BIT(huart->Instance->CR1, USART_CR1_UESM);
^
Firmware/mock/nucleof030r8/ir_sensor_mock/Drivers/STM32F0xx_HAL_Driver/Src/stm32f0xx_hal_uart_ex.c:467:0: information: Skipping configuration 'HAL_UART_MODULE_ENABLED;USART_CR1_UESM' since the value of 'USART_CR1_UESM' is unknown. Use -D if you want to check it. You can use -U to skip it explicitly. [ConfigurationNotChecked]
  ATOMIC_CLEAR_BIT(huart->Instance->CR1, USART_CR1_UESM);
^
Firmware/mock/nucleof030r8/ir_sensor_mock/Drivers/STM32F0xx_HAL_Driver/Src/stm32f0xx_hal_uart_ex.c:448:0: information: Skipping configuration 'HAL_UART_MODULE_ENABLED;USART_CR1_UESM;USART_CR3_WUFIE' since the value of 'USART_CR1_UESM' is unknown. Use -D if you want to check it. You can use -U to skip it explicitly. [ConfigurationNotChecked]
  ATOMIC_SET_BIT(huart->Instance->CR1, USART_CR1_UESM);
^
Firmware/mock/nucleof030r8/ir_sensor_mock/Drivers/STM32F0xx_HAL_Driver/Src/stm32f0xx_hal_uart_ex.c:467:0: information: Skipping configuration 'HAL_UART_MODULE_ENABLED;USART_CR1_UESM;USART_CR3_WUFIE' since the value of 'USART_CR1_UESM' is unknown. Use -D if you want to check it. You can use -U to skip it explicitly. [ConfigurationNotChecked]
  ATOMIC_CLEAR_BIT(huart->Instance->CR1, USART_CR1_UESM);
^
Firmware/mock/nucleof030r8/ir_sensor_mock/Drivers/STM32F0xx_HAL_Driver/Src/stm32f0xx_hal_uart_ex.c:448:0: information: Skipping configuration 'HAL_UART_MODULE_ENABLED;USART_CR1_UESM;USART_CR3_WUS' since the value of 'USART_CR1_UESM' is unknown. Use -D if you want to check it. You can use -U to skip it explicitly. [ConfigurationNotChecked]
  ATOMIC_SET_BIT(huart->Instance->CR1, USART_CR1_UESM);
^
Firmware/mock/nucleof030r8/ir_sensor_mock/Drivers/STM32F0xx_HAL_Driver/Src/stm32f0xx_hal_uart_ex.c:467:0: information: Skipping configuration 'HAL_UART_MODULE_ENABLED;USART_CR1_UESM;USART_CR3_WUS' since the value of 'USART_CR1_UESM' is unknown. Use -D if you want to check it. You can use -U to skip it explicitly. [ConfigurationNotChecked]
  ATOMIC_CLEAR_BIT(huart->Instance->CR1, USART_CR1_UESM);
^
Firmware/mock/nucleof030r8/ir_sensor_mock/Drivers/STM32F0xx_HAL_Driver/Src/stm32f0xx_hal_uart_ex.c:405:0: information: Skipping configuration 'HAL_UART_MODULE_ENABLED;USART_CR1_UESM;USART_CR3_WUS' since the value of 'USART_CR3_WUS' is unknown. Use -D if you want to check it. You can use -U to skip it explicitly. [ConfigurationNotChecked]
  MODIFY_REG(huart->Instance->CR3, USART_CR3_WUS, WakeUpSelection.WakeUpEvent);
^
Firmware/mock/nucleof030r8/ir_sensor_mock/Drivers/STM32F0xx_HAL_Driver/Src/stm32f0xx_hal_usart.c:2246:59: style: Same expression on both sides of '|'. [duplicateExpression]
          CLEAR_BIT(husart->Instance->CR3, USART_CR3_DMAR | USART_CR3_DMAR);
                                                          ^
Firmware/mock/nucleof030r8/ir_sensor_mock/Drivers/STM32F0xx_HAL_Driver/Src/stm32f0xx_hal_usart.c:861:13: style: The scope of the variable 'prxdata8bits' can be reduced. [variableScope]
  uint8_t  *prxdata8bits;
            ^
Firmware/mock/nucleof030r8/ir_sensor_mock/Drivers/STM32F0xx_HAL_Driver/Src/stm32f0xx_hal_usart.c:862:13: style: The scope of the variable 'prxdata16bits' can be reduced. [variableScope]
  uint16_t *prxdata16bits;
            ^
Firmware/mock/nucleof030r8/ir_sensor_mock/Drivers/STM32F0xx_HAL_Driver/Src/stm32f0xx_hal_usart.c:864:12: style: The scope of the variable 'tickstart' can be reduced. [variableScope]
  uint32_t tickstart;
           ^
Firmware/mock/nucleof030r8/ir_sensor_mock/Drivers/STM32F0xx_HAL_Driver/Src/stm32f0xx_hal_usart.c:983:13: style: The scope of the variable 'prxdata8bits' can be reduced. [variableScope]
  uint8_t  *prxdata8bits;
            ^
Firmware/mock/nucleof030r8/ir_sensor_mock/Drivers/STM32F0xx_HAL_Driver/Src/stm32f0xx_hal_usart.c:984:13: style: The scope of the variable 'prxdata16bits' can be reduced. [variableScope]
  uint16_t *prxdata16bits;
            ^
Firmware/mock/nucleof030r8/ir_sensor_mock/Drivers/STM32F0xx_HAL_Driver/Src/stm32f0xx_hal_usart.c:985:19: style: The scope of the variable 'ptxdata8bits' can be reduced. [variableScope]
  const uint8_t  *ptxdata8bits;
                  ^
Firmware/mock/nucleof030r8/ir_sensor_mock/Drivers/STM32F0xx_HAL_Driver/Src/stm32f0xx_hal_usart.c:986:19: style: The scope of the variable 'ptxdata16bits' can be reduced. [variableScope]
  const uint16_t *ptxdata16bits;
                  ^
Firmware/mock/nucleof030r8/ir_sensor_mock/Drivers/STM32F0xx_HAL_Driver/Src/stm32f0xx_hal_usart.c:988:12: style: The scope of the variable 'rxdatacount' can be reduced. [variableScope]
  uint16_t rxdatacount;
           ^
Firmware/mock/nucleof030r8/ir_sensor_mock/Drivers/STM32F0xx_HAL_Driver/Src/stm32f0xx_hal_usart.c:989:12: style: The scope of the variable 'tickstart' can be reduced. [variableScope]
  uint32_t tickstart;
           ^
Firmware/mock/nucleof030r8/ir_sensor_mock/Drivers/STM32F0xx_HAL_Driver/Src/stm32f0xx_hal_usart.c:1412:19: style: The scope of the variable 'tmp' can be reduced. [variableScope]
  const uint32_t *tmp;
                  ^
Firmware/mock/nucleof030r8/ir_sensor_mock/Drivers/STM32F0xx_HAL_Driver/Src/stm32f0xx_hal_usart.c:1648:19: style: The scope of the variable 'tmp' can be reduced. [variableScope]
  const uint32_t *tmp;
                  ^
Firmware/mock/nucleof030r8/ir_sensor_mock/Drivers/STM32F0xx_HAL_Driver/Src/stm32f0xx_hal_usart.c:2865:12: style: The scope of the variable 'brrtemp' can be reduced. [variableScope]
  uint16_t brrtemp;
           ^
Firmware/mock/nucleof030r8/ir_sensor_mock/Drivers/STM32F0xx_HAL_Driver/Src/stm32f0xx_hal_usart.c:3038:19: style: The scope of the variable 'tmp' can be reduced. [variableScope]
  const uint16_t *tmp;
                  ^
Firmware/mock/nucleof030r8/ir_sensor_mock/Drivers/STM32F0xx_HAL_Driver/Src/stm32f0xx_hal_usart.c:322:0: information: Skipping configuration 'HAL_USART_MODULE_ENABLED;USART_CR2_LINEN' since the value of 'USART_CR2_LINEN' is unknown. Use -D if you want to check it. You can use -U to skip it explicitly. [ConfigurationNotChecked]
  husart->Instance->CR2 &= ~USART_CR2_LINEN;
^
Firmware/mock/nucleof030r8/ir_sensor_mock/Drivers/STM32F0xx_HAL_Driver/Src/stm32f0xx_hal_usart.c:332:0: information: Skipping configuration 'HAL_USART_MODULE_ENABLED;USART_CR3_IREN' since the value of 'USART_CR3_IREN' is unknown. Use -D if you want to check it. You can use -U to skip it explicitly. [ConfigurationNotChecked]
  husart->Instance->CR3 &= ~(USART_CR3_HDSEL | USART_CR3_IREN);
^
Firmware/mock/nucleof030r8/ir_sensor_mock/Drivers/STM32F0xx_HAL_Driver/Src/stm32f0xx_hal_usart.c:326:0: information: Skipping configuration 'HAL_USART_MODULE_ENABLED;USART_CR3_IREN;USART_CR3_SCEN' since the value of 'USART_CR3_IREN' is unknown. Use -D if you want to check it. You can use -U to skip it explicitly. [ConfigurationNotChecked]
  husart->Instance->CR3 &= ~(USART_CR3_SCEN | USART_CR3_HDSEL | USART_CR3_IREN);
^
Firmware/mock/nucleof030r8/ir_sensor_mock/Drivers/STM32F0xx_HAL_Driver/Src/stm32f0xx_hal_usart.c:326:0: information: Skipping configuration 'HAL_USART_MODULE_ENABLED;USART_CR3_IREN;USART_CR3_SCEN' since the value of 'USART_CR3_SCEN' is unknown. Use -D if you want to check it. You can use -U to skip it explicitly. [ConfigurationNotChecked]
  husart->Instance->CR3 &= ~(USART_CR3_SCEN | USART_CR3_HDSEL | USART_CR3_IREN);
^
Firmware/mock/nucleof030r8/ir_sensor_mock/Drivers/STM32F0xx_HAL_Driver/Src/stm32f0xx_hal_usart.c:328:0: information: Skipping configuration 'HAL_USART_MODULE_ENABLED;USART_CR3_SCEN' since the value of 'USART_CR3_SCEN' is unknown. Use -D if you want to check it. You can use -U to skip it explicitly. [ConfigurationNotChecked]
  husart->Instance->CR3 &= ~(USART_CR3_SCEN | USART_CR3_HDSEL);
^
Firmware/mock/nucleof030r8/ir_sensor_mock/Drivers/STM32F0xx_HAL_Driver/Src/stm32f0xx_ll_comp.c:151:0: information: Skipping configuration 'COMP1;COMP2;USE_FULL_LL_DRIVER' since the value of 'COMP1' is unknown. Use -D if you want to check it. You can use -U to skip it explicitly. [ConfigurationNotChecked]
    if(COMPx == COMP1)
^
Firmware/mock/nucleof030r8/ir_sensor_mock/Drivers/STM32F0xx_HAL_Driver/Src/stm32f0xx_ll_comp.c:228:0: information: Skipping configuration 'COMP1;COMP2;USE_FULL_LL_DRIVER' since the value of 'COMP1' is unknown. Use -D if you want to check it. You can use -U to skip it explicitly. [ConfigurationNotChecked]
    if(COMPx == COMP1)
^
Firmware/mock/nucleof030r8/ir_sensor_mock/Drivers/STM32F0xx_HAL_Driver/Src/stm32f0xx_ll_crc.c:69:0: information: Skipping configuration 'CRC;CRC_POL_POL;USE_FULL_LL_DRIVER' since the value of 'CRC' is unknown. Use -D if you want to check it. You can use -U to skip it explicitly. [ConfigurationNotChecked]
  if (CRCx == CRC)
^
Firmware/mock/nucleof030r8/ir_sensor_mock/Drivers/STM32F0xx_HAL_Driver/Src/stm32f0xx_ll_crc.c:69:0: information: Skipping configuration 'CRC;USE_FULL_LL_DRIVER' since the value of 'CRC' is unknown. Use -D if you want to check it. You can use -U to skip it explicitly. [ConfigurationNotChecked]
  if (CRCx == CRC)
^
Firmware/mock/nucleof030r8/ir_sensor_mock/Drivers/STM32F0xx_HAL_Driver/Src/stm32f0xx_ll_dac.c:200:0: information: Skipping configuration 'DAC1;DAC_CR_WAVE1;USE_FULL_LL_DRIVER' since the value of 'DAC_CR_WAVE1' is unknown. Use -D if you want to check it. You can use -U to skip it explicitly. [ConfigurationNotChecked]
                  | DAC_CR_WAVE1
^
Firmware/mock/nucleof030r8/ir_sensor_mock/Drivers/STM32F0xx_HAL_Driver/Src/stm32f0xx_ll_dac.c:216:0: information: Skipping configuration 'DAC1;DAC_CR_WAVE1;USE_FULL_LL_DRIVER' since the value of 'DAC_CR_WAVE1' is unknown. Use -D if you want to check it. You can use -U to skip it explicitly. [ConfigurationNotChecked]
                  | DAC_CR_WAVE1
^
Firmware/mock/nucleof030r8/ir_sensor_mock/Drivers/STM32F0xx_HAL_Driver/Src/stm32f0xx_ll_gpio.c:119:0: information: Skipping configuration 'GPIOA;GPIOB;GPIOC;GPIOD;GPIOE;GPIOF;GPIOD;USE_FULL_LL_DRIVER' since the value of 'GPIOA' is unknown. Use -D if you want to check it. You can use -U to skip it explicitly. [ConfigurationNotChecked]
  if (GPIOx == GPIOA)
^
Firmware/mock/nucleof030r8/ir_sensor_mock/Drivers/STM32F0xx_HAL_Driver/Src/stm32f0xx_ll_gpio.c:124:0: information: Skipping configuration 'GPIOA;GPIOB;GPIOC;GPIOD;GPIOE;GPIOF;GPIOD;USE_FULL_LL_DRIVER' since the value of 'GPIOB' is unknown. Use -D if you want to check it. You can use -U to skip it explicitly. [ConfigurationNotChecked]
  else if (GPIOx == GPIOB)
^
Firmware/mock/nucleof030r8/ir_sensor_mock/Drivers/STM32F0xx_HAL_Driver/Src/stm32f0xx_ll_gpio.c:129:0: information: Skipping configuration 'GPIOA;GPIOB;GPIOC;GPIOD;GPIOE;GPIOF;GPIOD;USE_FULL_LL_DRIVER' since the value of 'GPIOC' is unknown. Use -D if you want to check it. You can use -U to skip it explicitly. [ConfigurationNotChecked]
  else if (GPIOx == GPIOC)
^
Firmware/mock/nucleof030r8/ir_sensor_mock/Drivers/STM32F0xx_HAL_Driver/Src/stm32f0xx_ll_gpio.c:135:0: information: Skipping configuration 'GPIOA;GPIOB;GPIOC;GPIOD;GPIOE;GPIOF;GPIOD;USE_FULL_LL_DRIVER' since the value of 'GPIOD' is unknown. Use -D if you want to check it. You can use -U to skip it explicitly. [ConfigurationNotChecked]
  else if (GPIOx == GPIOD)
^
Firmware/mock/nucleof030r8/ir_sensor_mock/Drivers/STM32F0xx_HAL_Driver/Src/stm32f0xx_ll_gpio.c:142:0: information: Skipping configuration 'GPIOA;GPIOB;GPIOC;GPIOD;GPIOE;GPIOF;GPIOD;USE_FULL_LL_DRIVER' since the value of 'GPIOE' is unknown. Use -D if you want to check it. You can use -U to skip it explicitly. [ConfigurationNotChecked]
  else if (GPIOx == GPIOE)
^
Firmware/mock/nucleof030r8/ir_sensor_mock/Drivers/STM32F0xx_HAL_Driver/Src/stm32f0xx_ll_gpio.c:149:0: information: Skipping configuration 'GPIOA;GPIOB;GPIOC;GPIOD;GPIOE;GPIOF;GPIOD;USE_FULL_LL_DRIVER' since the value of 'GPIOF' is unknown. Use -D if you want to check it. You can use -U to skip it explicitly. [ConfigurationNotChecked]
  else if (GPIOx == GPIOF)
^
Firmware/mock/nucleof030r8/ir_sensor_mock/Drivers/STM32F0xx_HAL_Driver/Src/stm32f0xx_ll_gpio.c:119:0: information: Skipping configuration 'GPIOA;GPIOB;GPIOC;GPIOD;GPIOE;GPIOF;GPIOE;USE_FULL_LL_DRIVER' since the value of 'GPIOA' is unknown. Use -D if you want to check it. You can use -U to skip it explicitly. [ConfigurationNotChecked]
  if (GPIOx == GPIOA)
^
Firmware/mock/nucleof030r8/ir_sensor_mock/Drivers/STM32F0xx_HAL_Driver/Src/stm32f0xx_ll_gpio.c:124:0: information: Skipping configuration 'GPIOA;GPIOB;GPIOC;GPIOD;GPIOE;GPIOF;GPIOE;USE_FULL_LL_DRIVER' since the value of 'GPIOB' is unknown. Use -D if you want to check it. You can use -U to skip it explicitly. [ConfigurationNotChecked]
  else if (GPIOx == GPIOB)
^
Firmware/mock/nucleof030r8/ir_sensor_mock/Drivers/STM32F0xx_HAL_Driver/Src/stm32f0xx_ll_gpio.c:129:0: information: Skipping configuration 'GPIOA;GPIOB;GPIOC;GPIOD;GPIOE;GPIOF;GPIOE;USE_FULL_LL_DRIVER' since the value of 'GPIOC' is unknown. Use -D if you want to check it. You can use -U to skip it explicitly. [ConfigurationNotChecked]
  else if (GPIOx == GPIOC)
^
Firmware/mock/nucleof030r8/ir_sensor_mock/Drivers/STM32F0xx_HAL_Driver/Src/stm32f0xx_ll_gpio.c:135:0: information: Skipping configuration 'GPIOA;GPIOB;GPIOC;GPIOD;GPIOE;GPIOF;GPIOE;USE_FULL_LL_DRIVER' since the value of 'GPIOD' is unknown. Use -D if you want to check it. You can use -U to skip it explicitly. [ConfigurationNotChecked]
  else if (GPIOx == GPIOD)
^
Firmware/mock/nucleof030r8/ir_sensor_mock/Drivers/STM32F0xx_HAL_Driver/Src/stm32f0xx_ll_gpio.c:142:0: information: Skipping configuration 'GPIOA;GPIOB;GPIOC;GPIOD;GPIOE;GPIOF;GPIOE;USE_FULL_LL_DRIVER' since the value of 'GPIOE' is unknown. Use -D if you want to check it. You can use -U to skip it explicitly. [ConfigurationNotChecked]
  else if (GPIOx == GPIOE)
^
Firmware/mock/nucleof030r8/ir_sensor_mock/Drivers/STM32F0xx_HAL_Driver/Src/stm32f0xx_ll_gpio.c:149:0: information: Skipping configuration 'GPIOA;GPIOB;GPIOC;GPIOD;GPIOE;GPIOF;GPIOE;USE_FULL_LL_DRIVER' since the value of 'GPIOF' is unknown. Use -D if you want to check it. You can use -U to skip it explicitly. [ConfigurationNotChecked]
  else if (GPIOx == GPIOF)
^
Firmware/mock/nucleof030r8/ir_sensor_mock/Drivers/STM32F0xx_HAL_Driver/Src/stm32f0xx_ll_gpio.c:119:0: information: Skipping configuration 'GPIOA;GPIOB;GPIOC;GPIOD;GPIOE;GPIOF;GPIOF;USE_FULL_LL_DRIVER' since the value of 'GPIOA' is unknown. Use -D if you want to check it. You can use -U to skip it explicitly. [ConfigurationNotChecked]
  if (GPIOx == GPIOA)
^
Firmware/mock/nucleof030r8/ir_sensor_mock/Drivers/STM32F0xx_HAL_Driver/Src/stm32f0xx_ll_gpio.c:124:0: information: Skipping configuration 'GPIOA;GPIOB;GPIOC;GPIOD;GPIOE;GPIOF;GPIOF;USE_FULL_LL_DRIVER' since the value of 'GPIOB' is unknown. Use -D if you want to check it. You can use -U to skip it explicitly. [ConfigurationNotChecked]
  else if (GPIOx == GPIOB)
^
Firmware/mock/nucleof030r8/ir_sensor_mock/Drivers/STM32F0xx_HAL_Driver/Src/stm32f0xx_ll_gpio.c:129:0: information: Skipping configuration 'GPIOA;GPIOB;GPIOC;GPIOD;GPIOE;GPIOF;GPIOF;USE_FULL_LL_DRIVER' since the value of 'GPIOC' is unknown. Use -D if you want to check it. You can use -U to skip it explicitly. [ConfigurationNotChecked]
  else if (GPIOx == GPIOC)
^
Firmware/mock/nucleof030r8/ir_sensor_mock/Drivers/STM32F0xx_HAL_Driver/Src/stm32f0xx_ll_gpio.c:135:0: information: Skipping configuration 'GPIOA;GPIOB;GPIOC;GPIOD;GPIOE;GPIOF;GPIOF;USE_FULL_LL_DRIVER' since the value of 'GPIOD' is unknown. Use -D if you want to check it. You can use -U to skip it explicitly. [ConfigurationNotChecked]
  else if (GPIOx == GPIOD)
^
Firmware/mock/nucleof030r8/ir_sensor_mock/Drivers/STM32F0xx_HAL_Driver/Src/stm32f0xx_ll_gpio.c:142:0: information: Skipping configuration 'GPIOA;GPIOB;GPIOC;GPIOD;GPIOE;GPIOF;GPIOF;USE_FULL_LL_DRIVER' since the value of 'GPIOE' is unknown. Use -D if you want to check it. You can use -U to skip it explicitly. [ConfigurationNotChecked]
  else if (GPIOx == GPIOE)
^
Firmware/mock/nucleof030r8/ir_sensor_mock/Drivers/STM32F0xx_HAL_Driver/Src/stm32f0xx_ll_gpio.c:149:0: information: Skipping configuration 'GPIOA;GPIOB;GPIOC;GPIOD;GPIOE;GPIOF;GPIOF;USE_FULL_LL_DRIVER' since the value of 'GPIOF' is unknown. Use -D if you want to check it. You can use -U to skip it explicitly. [ConfigurationNotChecked]
  else if (GPIOx == GPIOF)
^
Firmware/mock/nucleof030r8/ir_sensor_mock/Drivers/STM32F0xx_HAL_Driver/Src/stm32f0xx_ll_gpio.c:119:0: information: Skipping configuration 'GPIOA;GPIOB;GPIOC;GPIOD;GPIOE;GPIOF;USE_FULL_LL_DRIVER' since the value of 'GPIOA' is unknown. Use -D if you want to check it. You can use -U to skip it explicitly. [ConfigurationNotChecked]
  if (GPIOx == GPIOA)
^
Firmware/mock/nucleof030r8/ir_sensor_mock/Drivers/STM32F0xx_HAL_Driver/Src/stm32f0xx_ll_gpio.c:124:0: information: Skipping configuration 'GPIOA;GPIOB;GPIOC;GPIOD;GPIOE;GPIOF;USE_FULL_LL_DRIVER' since the value of 'GPIOB' is unknown. Use -D if you want to check it. You can use -U to skip it explicitly. [ConfigurationNotChecked]
  else if (GPIOx == GPIOB)
^
Firmware/mock/nucleof030r8/ir_sensor_mock/Drivers/STM32F0xx_HAL_Driver/Src/stm32f0xx_ll_gpio.c:129:0: information: Skipping configuration 'GPIOA;GPIOB;GPIOC;GPIOD;GPIOE;GPIOF;USE_FULL_LL_DRIVER' since the value of 'GPIOC' is unknown. Use -D if you want to check it. You can use -U to skip it explicitly. [ConfigurationNotChecked]
  else if (GPIOx == GPIOC)
^
Firmware/mock/nucleof030r8/ir_sensor_mock/Drivers/STM32F0xx_HAL_Driver/Src/stm32f0xx_ll_gpio.c:135:0: information: Skipping configuration 'GPIOA;GPIOB;GPIOC;GPIOD;GPIOE;GPIOF;USE_FULL_LL_DRIVER' since the value of 'GPIOD' is unknown. Use -D if you want to check it. You can use -U to skip it explicitly. [ConfigurationNotChecked]
  else if (GPIOx == GPIOD)
^
Firmware/mock/nucleof030r8/ir_sensor_mock/Drivers/STM32F0xx_HAL_Driver/Src/stm32f0xx_ll_gpio.c:142:0: information: Skipping configuration 'GPIOA;GPIOB;GPIOC;GPIOD;GPIOE;GPIOF;USE_FULL_LL_DRIVER' since the value of 'GPIOE' is unknown. Use -D if you want to check it. You can use -U to skip it explicitly. [ConfigurationNotChecked]
  else if (GPIOx == GPIOE)
^
Firmware/mock/nucleof030r8/ir_sensor_mock/Drivers/STM32F0xx_HAL_Driver/Src/stm32f0xx_ll_gpio.c:149:0: information: Skipping configuration 'GPIOA;GPIOB;GPIOC;GPIOD;GPIOE;GPIOF;USE_FULL_LL_DRIVER' since the value of 'GPIOF' is unknown. Use -D if you want to check it. You can use -U to skip it explicitly. [ConfigurationNotChecked]
  else if (GPIOx == GPIOF)
^
Firmware/mock/nucleof030r8/ir_sensor_mock/Drivers/STM32F0xx_HAL_Driver/Src/stm32f0xx_ll_i2c.c:93:0: information: Skipping configuration 'I2C1;I2C2;I2C2;USE_FULL_LL_DRIVER' since the value of 'I2C1' is unknown. Use -D if you want to check it. You can use -U to skip it explicitly. [ConfigurationNotChecked]
  if (I2Cx == I2C1)
^
Firmware/mock/nucleof030r8/ir_sensor_mock/Drivers/STM32F0xx_HAL_Driver/Src/stm32f0xx_ll_i2c.c:102:0: information: Skipping configuration 'I2C1;I2C2;I2C2;USE_FULL_LL_DRIVER' since the value of 'I2C2' is unknown. Use -D if you want to check it. You can use -U to skip it explicitly. [ConfigurationNotChecked]
  else if (I2Cx == I2C2)
^
Firmware/mock/nucleof030r8/ir_sensor_mock/Drivers/STM32F0xx_HAL_Driver/Src/stm32f0xx_ll_i2c.c:93:0: information: Skipping configuration 'I2C1;I2C2;USE_FULL_LL_DRIVER' since the value of 'I2C1' is unknown. Use -D if you want to check it. You can use -U to skip it explicitly. [ConfigurationNotChecked]
  if (I2Cx == I2C1)
^
Firmware/mock/nucleof030r8/ir_sensor_mock/Drivers/STM32F0xx_HAL_Driver/Src/stm32f0xx_ll_i2c.c:102:0: information: Skipping configuration 'I2C1;I2C2;USE_FULL_LL_DRIVER' since the value of 'I2C2' is unknown. Use -D if you want to check it. You can use -U to skip it explicitly. [ConfigurationNotChecked]
  else if (I2Cx == I2C2)
^
Firmware/mock/nucleof030r8/ir_sensor_mock/Drivers/STM32F0xx_HAL_Driver/Src/stm32f0xx_ll_rcc.c:0:0: information: Too many #ifdef configurations - cppcheck only checks 12 of 13 configurations. Use --force to check all configurations. [toomanyconfigs]

^
Firmware/mock/nucleof030r8/ir_sensor_mock/Drivers/STM32F0xx_HAL_Driver/Src/stm32f0xx_ll_rtc.c:577:12: style: The scope of the variable 'tmp' can be reduced. [variableScope]
  uint32_t tmp = 0U;
           ^
Firmware/mock/nucleof030r8/ir_sensor_mock/Drivers/STM32F0xx_HAL_Driver/Src/stm32f0xx_ll_rtc.c:577:16: style: Variable 'tmp' is assigned a value that is never used. [unreadVariable]
  uint32_t tmp = 0U;
               ^
Firmware/mock/nucleof030r8/ir_sensor_mock/Drivers/STM32F0xx_HAL_Driver/Src/stm32f0xx_ll_spi.c:141:0: information: Skipping configuration 'SPI1;SPI1;SPI2;USE_FULL_LL_DRIVER' since the value of 'SPI1' is unknown. Use -D if you want to check it. You can use -U to skip it explicitly. [ConfigurationNotChecked]
  if (SPIx == SPI1)
^
Firmware/mock/nucleof030r8/ir_sensor_mock/Drivers/STM32F0xx_HAL_Driver/Src/stm32f0xx_ll_spi.c:153:0: information: Skipping configuration 'SPI1;SPI1;SPI2;USE_FULL_LL_DRIVER' since the value of 'SPI2' is unknown. Use -D if you want to check it. You can use -U to skip it explicitly. [ConfigurationNotChecked]
  if (SPIx == SPI2)
^
Firmware/mock/nucleof030r8/ir_sensor_mock/Drivers/STM32F0xx_HAL_Driver/Src/stm32f0xx_ll_spi.c:141:0: information: Skipping configuration 'SPI1;SPI2;SPI2;USE_FULL_LL_DRIVER' since the value of 'SPI1' is unknown. Use -D if you want to check it. You can use -U to skip it explicitly. [ConfigurationNotChecked]
  if (SPIx == SPI1)
^
Firmware/mock/nucleof030r8/ir_sensor_mock/Drivers/STM32F0xx_HAL_Driver/Src/stm32f0xx_ll_spi.c:153:0: information: Skipping configuration 'SPI1;SPI2;SPI2;USE_FULL_LL_DRIVER' since the value of 'SPI2' is unknown. Use -D if you want to check it. You can use -U to skip it explicitly. [ConfigurationNotChecked]
  if (SPIx == SPI2)
^
Firmware/mock/nucleof030r8/ir_sensor_mock/Drivers/STM32F0xx_HAL_Driver/Src/stm32f0xx_ll_spi.c:141:0: information: Skipping configuration 'SPI1;SPI2;SPI_I2S_SUPPORT;USE_FULL_LL_DRIVER' since the value of 'SPI1' is unknown. Use -D if you want to check it. You can use -U to skip it explicitly. [ConfigurationNotChecked]
  if (SPIx == SPI1)
^
Firmware/mock/nucleof030r8/ir_sensor_mock/Drivers/STM32F0xx_HAL_Driver/Src/stm32f0xx_ll_spi.c:153:0: information: Skipping configuration 'SPI1;SPI2;SPI_I2S_SUPPORT;USE_FULL_LL_DRIVER' since the value of 'SPI2' is unknown. Use -D if you want to check it. You can use -U to skip it explicitly. [ConfigurationNotChecked]
  if (SPIx == SPI2)
^
Firmware/mock/nucleof030r8/ir_sensor_mock/Drivers/STM32F0xx_HAL_Driver/Src/stm32f0xx_ll_spi.c:141:0: information: Skipping configuration 'SPI1;SPI2;USE_FULL_LL_DRIVER' since the value of 'SPI1' is unknown. Use -D if you want to check it. You can use -U to skip it explicitly. [ConfigurationNotChecked]
  if (SPIx == SPI1)
^
Firmware/mock/nucleof030r8/ir_sensor_mock/Drivers/STM32F0xx_HAL_Driver/Src/stm32f0xx_ll_spi.c:153:0: information: Skipping configuration 'SPI1;SPI2;USE_FULL_LL_DRIVER' since the value of 'SPI2' is unknown. Use -D if you want to check it. You can use -U to skip it explicitly. [ConfigurationNotChecked]
  if (SPIx == SPI2)
^
Firmware/mock/nucleof030r8/ir_sensor_mock/Drivers/STM32F0xx_HAL_Driver/Src/stm32f0xx_ll_tim.c:0:0: information: Too many #ifdef configurations - cppcheck only checks 12 of 14 configurations. Use --force to check all configurations. [toomanyconfigs]

^
Firmware/mock/nucleof030r8/ir_sensor_mock/Drivers/STM32F0xx_HAL_Driver/Src/stm32f0xx_ll_tim.c:223:0: information: Skipping configuration 'TIM14;TIM1;TIM14;TIM15;TIM16;TIM17;TIM2;TIM3;TIM6;TIM7;USE_FULL_LL_DRIVER' since the value of 'TIM14' is unknown. Use -D if you want to check it. You can use -U to skip it explicitly. [ConfigurationNotChecked]
  else if (TIMx == TIM14)
^
Firmware/mock/nucleof030r8/ir_sensor_mock/Drivers/STM32F0xx_HAL_Driver/Src/stm32f0xx_ll_tim.c:175:0: information: Skipping configuration 'TIM14;TIM1;TIM14;TIM15;TIM16;TIM17;TIM2;TIM3;TIM6;TIM7;USE_FULL_LL_DRIVER' since the value of 'TIM1' is unknown. Use -D if you want to check it. You can use -U to skip it explicitly. [ConfigurationNotChecked]
  if (TIMx == TIM1)
^
Firmware/mock/nucleof030r8/ir_sensor_mock/Drivers/STM32F0xx_HAL_Driver/Src/stm32f0xx_ll_tim.c:230:0: information: Skipping configuration 'TIM14;TIM1;TIM14;TIM15;TIM16;TIM17;TIM2;TIM3;TIM6;TIM7;USE_FULL_LL_DRIVER' since the value of 'TIM15' is unknown. Use -D if you want to check it. You can use -U to skip it explicitly. [ConfigurationNotChecked]
  else if (TIMx == TIM15)
^
Firmware/mock/nucleof030r8/ir_sensor_mock/Drivers/STM32F0xx_HAL_Driver/Src/stm32f0xx_ll_tim.c:237:0: information: Skipping configuration 'TIM14;TIM1;TIM14;TIM15;TIM16;TIM17;TIM2;TIM3;TIM6;TIM7;USE_FULL_LL_DRIVER' since the value of 'TIM16' is unknown. Use -D if you want to check it. You can use -U to skip it explicitly. [ConfigurationNotChecked]
  else if (TIMx == TIM16)
^
Firmware/mock/nucleof030r8/ir_sensor_mock/Drivers/STM32F0xx_HAL_Driver/Src/stm32f0xx_ll_tim.c:244:0: information: Skipping configuration 'TIM14;TIM1;TIM14;TIM15;TIM16;TIM17;TIM2;TIM3;TIM6;TIM7;USE_FULL_LL_DRIVER' since the value of 'TIM17' is unknown. Use -D if you want to check it. You can use -U to skip it explicitly. [ConfigurationNotChecked]
  else if (TIMx == TIM17)
^
Firmware/mock/nucleof030r8/ir_sensor_mock/Drivers/STM32F0xx_HAL_Driver/Src/stm32f0xx_ll_tim.c:181:0: information: Skipping configuration 'TIM14;TIM1;TIM14;TIM15;TIM16;TIM17;TIM2;TIM3;TIM6;TIM7;USE_FULL_LL_DRIVER' since the value of 'TIM2' is unknown. Use -D if you want to check it. You can use -U to skip it explicitly. [ConfigurationNotChecked]
  else if (TIMx == TIM2)
^
Firmware/mock/nucleof030r8/ir_sensor_mock/Drivers/STM32F0xx_HAL_Driver/Src/stm32f0xx_ll_tim.c:188:0: information: Skipping configuration 'TIM14;TIM1;TIM14;TIM15;TIM16;TIM17;TIM2;TIM3;TIM6;TIM7;USE_FULL_LL_DRIVER' since the value of 'TIM3' is unknown. Use -D if you want to check it. You can use -U to skip it explicitly. [ConfigurationNotChecked]
  else if (TIMx == TIM3)
^
Firmware/mock/nucleof030r8/ir_sensor_mock/Drivers/STM32F0xx_HAL_Driver/Src/stm32f0xx_ll_tim.c:202:0: information: Skipping configuration 'TIM14;TIM1;TIM14;TIM15;TIM16;TIM17;TIM2;TIM3;TIM6;TIM7;USE_FULL_LL_DRIVER' since the value of 'TIM6' is unknown. Use -D if you want to check it. You can use -U to skip it explicitly. [ConfigurationNotChecked]
  else if (TIMx == TIM6)
^
Firmware/mock/nucleof030r8/ir_sensor_mock/Drivers/STM32F0xx_HAL_Driver/Src/stm32f0xx_ll_tim.c:209:0: information: Skipping configuration 'TIM14;TIM1;TIM14;TIM15;TIM16;TIM17;TIM2;TIM3;TIM6;TIM7;USE_FULL_LL_DRIVER' since the value of 'TIM7' is unknown. Use -D if you want to check it. You can use -U to skip it explicitly. [ConfigurationNotChecked]
  else if (TIMx == TIM7)
^
Firmware/mock/nucleof030r8/ir_sensor_mock/Drivers/STM32F0xx_HAL_Driver/Src/stm32f0xx_ll_tim.c:230:0: information: Skipping configuration 'TIM15;TIM1;TIM14;TIM15;TIM16;TIM17;TIM2;TIM3;TIM6;TIM7;USE_FULL_LL_DRIVER' since the value of 'TIM15' is unknown. Use -D if you want to check it. You can use -U to skip it explicitly. [ConfigurationNotChecked]
  else if (TIMx == TIM15)
^
Firmware/mock/nucleof030r8/ir_sensor_mock/Drivers/STM32F0xx_HAL_Driver/Src/stm32f0xx_ll_tim.c:175:0: information: Skipping configuration 'TIM15;TIM1;TIM14;TIM15;TIM16;TIM17;TIM2;TIM3;TIM6;TIM7;USE_FULL_LL_DRIVER' since the value of 'TIM1' is unknown. Use -D if you want to check it. You can use -U to skip it explicitly. [ConfigurationNotChecked]
  if (TIMx == TIM1)
^
Firmware/mock/nucleof030r8/ir_sensor_mock/Drivers/STM32F0xx_HAL_Driver/Src/stm32f0xx_ll_tim.c:223:0: information: Skipping configuration 'TIM15;TIM1;TIM14;TIM15;TIM16;TIM17;TIM2;TIM3;TIM6;TIM7;USE_FULL_LL_DRIVER' since the value of 'TIM14' is unknown. Use -D if you want to check it. You can use -U to skip it explicitly. [ConfigurationNotChecked]
  else if (TIMx == TIM14)
^
Firmware/mock/nucleof030r8/ir_sensor_mock/Drivers/STM32F0xx_HAL_Driver/Src/stm32f0xx_ll_tim.c:237:0: information: Skipping configuration 'TIM15;TIM1;TIM14;TIM15;TIM16;TIM17;TIM2;TIM3;TIM6;TIM7;USE_FULL_LL_DRIVER' since the value of 'TIM16' is unknown. Use -D if you want to check it. You can use -U to skip it explicitly. [ConfigurationNotChecked]
  else if (TIMx == TIM16)
^
Firmware/mock/nucleof030r8/ir_sensor_mock/Drivers/STM32F0xx_HAL_Driver/Src/stm32f0xx_ll_tim.c:244:0: information: Skipping configuration 'TIM15;TIM1;TIM14;TIM15;TIM16;TIM17;TIM2;TIM3;TIM6;TIM7;USE_FULL_LL_DRIVER' since the value of 'TIM17' is unknown. Use -D if you want to check it. You can use -U to skip it explicitly. [ConfigurationNotChecked]
  else if (TIMx == TIM17)
^
Firmware/mock/nucleof030r8/ir_sensor_mock/Drivers/STM32F0xx_HAL_Driver/Src/stm32f0xx_ll_tim.c:181:0: information: Skipping configuration 'TIM15;TIM1;TIM14;TIM15;TIM16;TIM17;TIM2;TIM3;TIM6;TIM7;USE_FULL_LL_DRIVER' since the value of 'TIM2' is unknown. Use -D if you want to check it. You can use -U to skip it explicitly. [ConfigurationNotChecked]
  else if (TIMx == TIM2)
^
Firmware/mock/nucleof030r8/ir_sensor_mock/Drivers/STM32F0xx_HAL_Driver/Src/stm32f0xx_ll_tim.c:188:0: information: Skipping configuration 'TIM15;TIM1;TIM14;TIM15;TIM16;TIM17;TIM2;TIM3;TIM6;TIM7;USE_FULL_LL_DRIVER' since the value of 'TIM3' is unknown. Use -D if you want to check it. You can use -U to skip it explicitly. [ConfigurationNotChecked]
  else if (TIMx == TIM3)
^
Firmware/mock/nucleof030r8/ir_sensor_mock/Drivers/STM32F0xx_HAL_Driver/Src/stm32f0xx_ll_tim.c:202:0: information: Skipping configuration 'TIM15;TIM1;TIM14;TIM15;TIM16;TIM17;TIM2;TIM3;TIM6;TIM7;USE_FULL_LL_DRIVER' since the value of 'TIM6' is unknown. Use -D if you want to check it. You can use -U to skip it explicitly. [ConfigurationNotChecked]
  else if (TIMx == TIM6)
^
Firmware/mock/nucleof030r8/ir_sensor_mock/Drivers/STM32F0xx_HAL_Driver/Src/stm32f0xx_ll_tim.c:209:0: information: Skipping configuration 'TIM15;TIM1;TIM14;TIM15;TIM16;TIM17;TIM2;TIM3;TIM6;TIM7;USE_FULL_LL_DRIVER' since the value of 'TIM7' is unknown. Use -D if you want to check it. You can use -U to skip it explicitly. [ConfigurationNotChecked]
  else if (TIMx == TIM7)
^
Firmware/mock/nucleof030r8/ir_sensor_mock/Drivers/STM32F0xx_HAL_Driver/Src/stm32f0xx_ll_tim.c:237:0: information: Skipping configuration 'TIM16;TIM1;TIM14;TIM15;TIM16;TIM17;TIM2;TIM3;TIM6;TIM7;USE_FULL_LL_DRIVER' since the value of 'TIM16' is unknown. Use -D if you want to check it. You can use -U to skip it explicitly. [ConfigurationNotChecked]
  else if (TIMx == TIM16)
^
Firmware/mock/nucleof030r8/ir_sensor_mock/Drivers/STM32F0xx_HAL_Driver/Src/stm32f0xx_ll_tim.c:175:0: information: Skipping configuration 'TIM16;TIM1;TIM14;TIM15;TIM16;TIM17;TIM2;TIM3;TIM6;TIM7;USE_FULL_LL_DRIVER' since the value of 'TIM1' is unknown. Use -D if you want to check it. You can use -U to skip it explicitly. [ConfigurationNotChecked]
  if (TIMx == TIM1)
^
Firmware/mock/nucleof030r8/ir_sensor_mock/Drivers/STM32F0xx_HAL_Driver/Src/stm32f0xx_ll_tim.c:223:0: information: Skipping configuration 'TIM16;TIM1;TIM14;TIM15;TIM16;TIM17;TIM2;TIM3;TIM6;TIM7;USE_FULL_LL_DRIVER' since the value of 'TIM14' is unknown. Use -D if you want to check it. You can use -U to skip it explicitly. [ConfigurationNotChecked]
  else if (TIMx == TIM14)
^
Firmware/mock/nucleof030r8/ir_sensor_mock/Drivers/STM32F0xx_HAL_Driver/Src/stm32f0xx_ll_tim.c:230:0: information: Skipping configuration 'TIM16;TIM1;TIM14;TIM15;TIM16;TIM17;TIM2;TIM3;TIM6;TIM7;USE_FULL_LL_DRIVER' since the value of 'TIM15' is unknown. Use -D if you want to check it. You can use -U to skip it explicitly. [ConfigurationNotChecked]
  else if (TIMx == TIM15)
^
Firmware/mock/nucleof030r8/ir_sensor_mock/Drivers/STM32F0xx_HAL_Driver/Src/stm32f0xx_ll_tim.c:244:0: information: Skipping configuration 'TIM16;TIM1;TIM14;TIM15;TIM16;TIM17;TIM2;TIM3;TIM6;TIM7;USE_FULL_LL_DRIVER' since the value of 'TIM17' is unknown. Use -D if you want to check it. You can use -U to skip it explicitly. [ConfigurationNotChecked]
  else if (TIMx == TIM17)
^
Firmware/mock/nucleof030r8/ir_sensor_mock/Drivers/STM32F0xx_HAL_Driver/Src/stm32f0xx_ll_tim.c:181:0: information: Skipping configuration 'TIM16;TIM1;TIM14;TIM15;TIM16;TIM17;TIM2;TIM3;TIM6;TIM7;USE_FULL_LL_DRIVER' since the value of 'TIM2' is unknown. Use -D if you want to check it. You can use -U to skip it explicitly. [ConfigurationNotChecked]
  else if (TIMx == TIM2)
^
Firmware/mock/nucleof030r8/ir_sensor_mock/Drivers/STM32F0xx_HAL_Driver/Src/stm32f0xx_ll_tim.c:188:0: information: Skipping configuration 'TIM16;TIM1;TIM14;TIM15;TIM16;TIM17;TIM2;TIM3;TIM6;TIM7;USE_FULL_LL_DRIVER' since the value of 'TIM3' is unknown. Use -D if you want to check it. You can use -U to skip it explicitly. [ConfigurationNotChecked]
  else if (TIMx == TIM3)
^
Firmware/mock/nucleof030r8/ir_sensor_mock/Drivers/STM32F0xx_HAL_Driver/Src/stm32f0xx_ll_tim.c:202:0: information: Skipping configuration 'TIM16;TIM1;TIM14;TIM15;TIM16;TIM17;TIM2;TIM3;TIM6;TIM7;USE_FULL_LL_DRIVER' since the value of 'TIM6' is unknown. Use -D if you want to check it. You can use -U to skip it explicitly. [ConfigurationNotChecked]
  else if (TIMx == TIM6)
^
Firmware/mock/nucleof030r8/ir_sensor_mock/Drivers/STM32F0xx_HAL_Driver/Src/stm32f0xx_ll_tim.c:209:0: information: Skipping configuration 'TIM16;TIM1;TIM14;TIM15;TIM16;TIM17;TIM2;TIM3;TIM6;TIM7;USE_FULL_LL_DRIVER' since the value of 'TIM7' is unknown. Use -D if you want to check it. You can use -U to skip it explicitly. [ConfigurationNotChecked]
  else if (TIMx == TIM7)
^
Firmware/mock/nucleof030r8/ir_sensor_mock/Drivers/STM32F0xx_HAL_Driver/Src/stm32f0xx_ll_tim.c:244:0: information: Skipping configuration 'TIM17;TIM1;TIM14;TIM15;TIM16;TIM17;TIM2;TIM3;TIM6;TIM7;USE_FULL_LL_DRIVER' since the value of 'TIM17' is unknown. Use -D if you want to check it. You can use -U to skip it explicitly. [ConfigurationNotChecked]
  else if (TIMx == TIM17)
^
Firmware/mock/nucleof030r8/ir_sensor_mock/Drivers/STM32F0xx_HAL_Driver/Src/stm32f0xx_ll_tim.c:175:0: information: Skipping configuration 'TIM17;TIM1;TIM14;TIM15;TIM16;TIM17;TIM2;TIM3;TIM6;TIM7;USE_FULL_LL_DRIVER' since the value of 'TIM1' is unknown. Use -D if you want to check it. You can use -U to skip it explicitly. [ConfigurationNotChecked]
  if (TIMx == TIM1)
^
Firmware/mock/nucleof030r8/ir_sensor_mock/Drivers/STM32F0xx_HAL_Driver/Src/stm32f0xx_ll_tim.c:223:0: information: Skipping configuration 'TIM17;TIM1;TIM14;TIM15;TIM16;TIM17;TIM2;TIM3;TIM6;TIM7;USE_FULL_LL_DRIVER' since the value of 'TIM14' is unknown. Use -D if you want to check it. You can use -U to skip it explicitly. [ConfigurationNotChecked]
  else if (TIMx == TIM14)
^
Firmware/mock/nucleof030r8/ir_sensor_mock/Drivers/STM32F0xx_HAL_Driver/Src/stm32f0xx_ll_tim.c:230:0: information: Skipping configuration 'TIM17;TIM1;TIM14;TIM15;TIM16;TIM17;TIM2;TIM3;TIM6;TIM7;USE_FULL_LL_DRIVER' since the value of 'TIM15' is unknown. Use -D if you want to check it. You can use -U to skip it explicitly. [ConfigurationNotChecked]
  else if (TIMx == TIM15)
^
Firmware/mock/nucleof030r8/ir_sensor_mock/Drivers/STM32F0xx_HAL_Driver/Src/stm32f0xx_ll_tim.c:237:0: information: Skipping configuration 'TIM17;TIM1;TIM14;TIM15;TIM16;TIM17;TIM2;TIM3;TIM6;TIM7;USE_FULL_LL_DRIVER' since the value of 'TIM16' is unknown. Use -D if you want to check it. You can use -U to skip it explicitly. [ConfigurationNotChecked]
  else if (TIMx == TIM16)
^
Firmware/mock/nucleof030r8/ir_sensor_mock/Drivers/STM32F0xx_HAL_Driver/Src/stm32f0xx_ll_tim.c:181:0: information: Skipping configuration 'TIM17;TIM1;TIM14;TIM15;TIM16;TIM17;TIM2;TIM3;TIM6;TIM7;USE_FULL_LL_DRIVER' since the value of 'TIM2' is unknown. Use -D if you want to check it. You can use -U to skip it explicitly. [ConfigurationNotChecked]
  else if (TIMx == TIM2)
^
Firmware/mock/nucleof030r8/ir_sensor_mock/Drivers/STM32F0xx_HAL_Driver/Src/stm32f0xx_ll_tim.c:188:0: information: Skipping configuration 'TIM17;TIM1;TIM14;TIM15;TIM16;TIM17;TIM2;TIM3;TIM6;TIM7;USE_FULL_LL_DRIVER' since the value of 'TIM3' is unknown. Use -D if you want to check it. You can use -U to skip it explicitly. [ConfigurationNotChecked]
  else if (TIMx == TIM3)
^
Firmware/mock/nucleof030r8/ir_sensor_mock/Drivers/STM32F0xx_HAL_Driver/Src/stm32f0xx_ll_tim.c:202:0: information: Skipping configuration 'TIM17;TIM1;TIM14;TIM15;TIM16;TIM17;TIM2;TIM3;TIM6;TIM7;USE_FULL_LL_DRIVER' since the value of 'TIM6' is unknown. Use -D if you want to check it. You can use -U to skip it explicitly. [ConfigurationNotChecked]
  else if (TIMx == TIM6)
^
Firmware/mock/nucleof030r8/ir_sensor_mock/Drivers/STM32F0xx_HAL_Driver/Src/stm32f0xx_ll_tim.c:209:0: information: Skipping configuration 'TIM17;TIM1;TIM14;TIM15;TIM16;TIM17;TIM2;TIM3;TIM6;TIM7;USE_FULL_LL_DRIVER' since the value of 'TIM7' is unknown. Use -D if you want to check it. You can use -U to skip it explicitly. [ConfigurationNotChecked]
  else if (TIMx == TIM7)
^
Firmware/mock/nucleof030r8/ir_sensor_mock/Drivers/STM32F0xx_HAL_Driver/Src/stm32f0xx_ll_tim.c:175:0: information: Skipping configuration 'TIM1;TIM14;TIM15;TIM16;TIM17;TIM2;TIM3;TIM6;TIM7;TIM2;USE_FULL_LL_DRIVER' since the value of 'TIM1' is unknown. Use -D if you want to check it. You can use -U to skip it explicitly. [ConfigurationNotChecked]
  if (TIMx == TIM1)
^
Firmware/mock/nucleof030r8/ir_sensor_mock/Drivers/STM32F0xx_HAL_Driver/Src/stm32f0xx_ll_tim.c:223:0: information: Skipping configuration 'TIM1;TIM14;TIM15;TIM16;TIM17;TIM2;TIM3;TIM6;TIM7;TIM2;USE_FULL_LL_DRIVER' since the value of 'TIM14' is unknown. Use -D if you want to check it. You can use -U to skip it explicitly. [ConfigurationNotChecked]
  else if (TIMx == TIM14)
^
Firmware/mock/nucleof030r8/ir_sensor_mock/Drivers/STM32F0xx_HAL_Driver/Src/stm32f0xx_ll_tim.c:230:0: information: Skipping configuration 'TIM1;TIM14;TIM15;TIM16;TIM17;TIM2;TIM3;TIM6;TIM7;TIM2;USE_FULL_LL_DRIVER' since the value of 'TIM15' is unknown. Use -D if you want to check it. You can use -U to skip it explicitly. [ConfigurationNotChecked]
  else if (TIMx == TIM15)
^
Firmware/mock/nucleof030r8/ir_sensor_mock/Drivers/STM32F0xx_HAL_Driver/Src/stm32f0xx_ll_tim.c:237:0: information: Skipping configuration 'TIM1;TIM14;TIM15;TIM16;TIM17;TIM2;TIM3;TIM6;TIM7;TIM2;USE_FULL_LL_DRIVER' since the value of 'TIM16' is unknown. Use -D if you want to check it. You can use -U to skip it explicitly. [ConfigurationNotChecked]
  else if (TIMx == TIM16)
^
Firmware/mock/nucleof030r8/ir_sensor_mock/Drivers/STM32F0xx_HAL_Driver/Src/stm32f0xx_ll_tim.c:244:0: information: Skipping configuration 'TIM1;TIM14;TIM15;TIM16;TIM17;TIM2;TIM3;TIM6;TIM7;TIM2;USE_FULL_LL_DRIVER' since the value of 'TIM17' is unknown. Use -D if you want to check it. You can use -U to skip it explicitly. [ConfigurationNotChecked]
  else if (TIMx == TIM17)
^
Firmware/mock/nucleof030r8/ir_sensor_mock/Drivers/STM32F0xx_HAL_Driver/Src/stm32f0xx_ll_tim.c:181:0: information: Skipping configuration 'TIM1;TIM14;TIM15;TIM16;TIM17;TIM2;TIM3;TIM6;TIM7;TIM2;USE_FULL_LL_DRIVER' since the value of 'TIM2' is unknown. Use -D if you want to check it. You can use -U to skip it explicitly. [ConfigurationNotChecked]
  else if (TIMx == TIM2)
^
Firmware/mock/nucleof030r8/ir_sensor_mock/Drivers/STM32F0xx_HAL_Driver/Src/stm32f0xx_ll_tim.c:188:0: information: Skipping configuration 'TIM1;TIM14;TIM15;TIM16;TIM17;TIM2;TIM3;TIM6;TIM7;TIM2;USE_FULL_LL_DRIVER' since the value of 'TIM3' is unknown. Use -D if you want to check it. You can use -U to skip it explicitly. [ConfigurationNotChecked]
  else if (TIMx == TIM3)
^
Firmware/mock/nucleof030r8/ir_sensor_mock/Drivers/STM32F0xx_HAL_Driver/Src/stm32f0xx_ll_tim.c:202:0: information: Skipping configuration 'TIM1;TIM14;TIM15;TIM16;TIM17;TIM2;TIM3;TIM6;TIM7;TIM2;USE_FULL_LL_DRIVER' since the value of 'TIM6' is unknown. Use -D if you want to check it. You can use -U to skip it explicitly. [ConfigurationNotChecked]
  else if (TIMx == TIM6)
^
Firmware/mock/nucleof030r8/ir_sensor_mock/Drivers/STM32F0xx_HAL_Driver/Src/stm32f0xx_ll_tim.c:209:0: information: Skipping configuration 'TIM1;TIM14;TIM15;TIM16;TIM17;TIM2;TIM3;TIM6;TIM7;TIM2;USE_FULL_LL_DRIVER' since the value of 'TIM7' is unknown. Use -D if you want to check it. You can use -U to skip it explicitly. [ConfigurationNotChecked]
  else if (TIMx == TIM7)
^
Firmware/mock/nucleof030r8/ir_sensor_mock/Drivers/STM32F0xx_HAL_Driver/Src/stm32f0xx_ll_tim.c:175:0: information: Skipping configuration 'TIM1;TIM14;TIM15;TIM16;TIM17;TIM2;TIM3;TIM6;TIM7;TIM3;USE_FULL_LL_DRIVER' since the value of 'TIM1' is unknown. Use -D if you want to check it. You can use -U to skip it explicitly. [ConfigurationNotChecked]
  if (TIMx == TIM1)
^
Firmware/mock/nucleof030r8/ir_sensor_mock/Drivers/STM32F0xx_HAL_Driver/Src/stm32f0xx_ll_tim.c:223:0: information: Skipping configuration 'TIM1;TIM14;TIM15;TIM16;TIM17;TIM2;TIM3;TIM6;TIM7;TIM3;USE_FULL_LL_DRIVER' since the value of 'TIM14' is unknown. Use -D if you want to check it. You can use -U to skip it explicitly. [ConfigurationNotChecked]
  else if (TIMx == TIM14)
^
Firmware/mock/nucleof030r8/ir_sensor_mock/Drivers/STM32F0xx_HAL_Driver/Src/stm32f0xx_ll_tim.c:230:0: information: Skipping configuration 'TIM1;TIM14;TIM15;TIM16;TIM17;TIM2;TIM3;TIM6;TIM7;TIM3;USE_FULL_LL_DRIVER' since the value of 'TIM15' is unknown. Use -D if you want to check it. You can use -U to skip it explicitly. [ConfigurationNotChecked]
  else if (TIMx == TIM15)
^
Firmware/mock/nucleof030r8/ir_sensor_mock/Drivers/STM32F0xx_HAL_Driver/Src/stm32f0xx_ll_tim.c:237:0: information: Skipping configuration 'TIM1;TIM14;TIM15;TIM16;TIM17;TIM2;TIM3;TIM6;TIM7;TIM3;USE_FULL_LL_DRIVER' since the value of 'TIM16' is unknown. Use -D if you want to check it. You can use -U to skip it explicitly. [ConfigurationNotChecked]
  else if (TIMx == TIM16)
^
Firmware/mock/nucleof030r8/ir_sensor_mock/Drivers/STM32F0xx_HAL_Driver/Src/stm32f0xx_ll_tim.c:244:0: information: Skipping configuration 'TIM1;TIM14;TIM15;TIM16;TIM17;TIM2;TIM3;TIM6;TIM7;TIM3;USE_FULL_LL_DRIVER' since the value of 'TIM17' is unknown. Use -D if you want to check it. You can use -U to skip it explicitly. [ConfigurationNotChecked]
  else if (TIMx == TIM17)
^
Firmware/mock/nucleof030r8/ir_sensor_mock/Drivers/STM32F0xx_HAL_Driver/Src/stm32f0xx_ll_tim.c:181:0: information: Skipping configuration 'TIM1;TIM14;TIM15;TIM16;TIM17;TIM2;TIM3;TIM6;TIM7;TIM3;USE_FULL_LL_DRIVER' since the value of 'TIM2' is unknown. Use -D if you want to check it. You can use -U to skip it explicitly. [ConfigurationNotChecked]
  else if (TIMx == TIM2)
^
Firmware/mock/nucleof030r8/ir_sensor_mock/Drivers/STM32F0xx_HAL_Driver/Src/stm32f0xx_ll_tim.c:188:0: information: Skipping configuration 'TIM1;TIM14;TIM15;TIM16;TIM17;TIM2;TIM3;TIM6;TIM7;TIM3;USE_FULL_LL_DRIVER' since the value of 'TIM3' is unknown. Use -D if you want to check it. You can use -U to skip it explicitly. [ConfigurationNotChecked]
  else if (TIMx == TIM3)
^
Firmware/mock/nucleof030r8/ir_sensor_mock/Drivers/STM32F0xx_HAL_Driver/Src/stm32f0xx_ll_tim.c:202:0: information: Skipping configuration 'TIM1;TIM14;TIM15;TIM16;TIM17;TIM2;TIM3;TIM6;TIM7;TIM3;USE_FULL_LL_DRIVER' since the value of 'TIM6' is unknown. Use -D if you want to check it. You can use -U to skip it explicitly. [ConfigurationNotChecked]
  else if (TIMx == TIM6)
^
Firmware/mock/nucleof030r8/ir_sensor_mock/Drivers/STM32F0xx_HAL_Driver/Src/stm32f0xx_ll_tim.c:209:0: information: Skipping configuration 'TIM1;TIM14;TIM15;TIM16;TIM17;TIM2;TIM3;TIM6;TIM7;TIM3;USE_FULL_LL_DRIVER' since the value of 'TIM7' is unknown. Use -D if you want to check it. You can use -U to skip it explicitly. [ConfigurationNotChecked]
  else if (TIMx == TIM7)
^
Firmware/mock/nucleof030r8/ir_sensor_mock/Drivers/STM32F0xx_HAL_Driver/Src/stm32f0xx_ll_tim.c:175:0: information: Skipping configuration 'TIM1;TIM14;TIM15;TIM16;TIM17;TIM2;TIM3;TIM6;TIM7;TIM5;USE_FULL_LL_DRIVER' since the value of 'TIM1' is unknown. Use -D if you want to check it. You can use -U to skip it explicitly. [ConfigurationNotChecked]
  if (TIMx == TIM1)
^
Firmware/mock/nucleof030r8/ir_sensor_mock/Drivers/STM32F0xx_HAL_Driver/Src/stm32f0xx_ll_tim.c:223:0: information: Skipping configuration 'TIM1;TIM14;TIM15;TIM16;TIM17;TIM2;TIM3;TIM6;TIM7;TIM5;USE_FULL_LL_DRIVER' since the value of 'TIM14' is unknown. Use -D if you want to check it. You can use -U to skip it explicitly. [ConfigurationNotChecked]
  else if (TIMx == TIM14)
^
Firmware/mock/nucleof030r8/ir_sensor_mock/Drivers/STM32F0xx_HAL_Driver/Src/stm32f0xx_ll_tim.c:230:0: information: Skipping configuration 'TIM1;TIM14;TIM15;TIM16;TIM17;TIM2;TIM3;TIM6;TIM7;TIM5;USE_FULL_LL_DRIVER' since the value of 'TIM15' is unknown. Use -D if you want to check it. You can use -U to skip it explicitly. [ConfigurationNotChecked]
  else if (TIMx == TIM15)
^
Firmware/mock/nucleof030r8/ir_sensor_mock/Drivers/STM32F0xx_HAL_Driver/Src/stm32f0xx_ll_tim.c:237:0: information: Skipping configuration 'TIM1;TIM14;TIM15;TIM16;TIM17;TIM2;TIM3;TIM6;TIM7;TIM5;USE_FULL_LL_DRIVER' since the value of 'TIM16' is unknown. Use -D if you want to check it. You can use -U to skip it explicitly. [ConfigurationNotChecked]
  else if (TIMx == TIM16)
^
Firmware/mock/nucleof030r8/ir_sensor_mock/Drivers/STM32F0xx_HAL_Driver/Src/stm32f0xx_ll_tim.c:244:0: information: Skipping configuration 'TIM1;TIM14;TIM15;TIM16;TIM17;TIM2;TIM3;TIM6;TIM7;TIM5;USE_FULL_LL_DRIVER' since the value of 'TIM17' is unknown. Use -D if you want to check it. You can use -U to skip it explicitly. [ConfigurationNotChecked]
  else if (TIMx == TIM17)
^
Firmware/mock/nucleof030r8/ir_sensor_mock/Drivers/STM32F0xx_HAL_Driver/Src/stm32f0xx_ll_tim.c:181:0: information: Skipping configuration 'TIM1;TIM14;TIM15;TIM16;TIM17;TIM2;TIM3;TIM6;TIM7;TIM5;USE_FULL_LL_DRIVER' since the value of 'TIM2' is unknown. Use -D if you want to check it. You can use -U to skip it explicitly. [ConfigurationNotChecked]
  else if (TIMx == TIM2)
^
Firmware/mock/nucleof030r8/ir_sensor_mock/Drivers/STM32F0xx_HAL_Driver/Src/stm32f0xx_ll_tim.c:188:0: information: Skipping configuration 'TIM1;TIM14;TIM15;TIM16;TIM17;TIM2;TIM3;TIM6;TIM7;TIM5;USE_FULL_LL_DRIVER' since the value of 'TIM3' is unknown. Use -D if you want to check it. You can use -U to skip it explicitly. [ConfigurationNotChecked]
  else if (TIMx == TIM3)
^
Firmware/mock/nucleof030r8/ir_sensor_mock/Drivers/STM32F0xx_HAL_Driver/Src/stm32f0xx_ll_tim.c:202:0: information: Skipping configuration 'TIM1;TIM14;TIM15;TIM16;TIM17;TIM2;TIM3;TIM6;TIM7;TIM5;USE_FULL_LL_DRIVER' since the value of 'TIM6' is unknown. Use -D if you want to check it. You can use -U to skip it explicitly. [ConfigurationNotChecked]
  else if (TIMx == TIM6)
^
Firmware/mock/nucleof030r8/ir_sensor_mock/Drivers/STM32F0xx_HAL_Driver/Src/stm32f0xx_ll_tim.c:209:0: information: Skipping configuration 'TIM1;TIM14;TIM15;TIM16;TIM17;TIM2;TIM3;TIM6;TIM7;TIM5;USE_FULL_LL_DRIVER' since the value of 'TIM7' is unknown. Use -D if you want to check it. You can use -U to skip it explicitly. [ConfigurationNotChecked]
  else if (TIMx == TIM7)
^
Firmware/mock/nucleof030r8/ir_sensor_mock/Drivers/STM32F0xx_HAL_Driver/Src/stm32f0xx_ll_tim.c:195:0: information: Skipping configuration 'TIM1;TIM14;TIM15;TIM16;TIM17;TIM2;TIM3;TIM6;TIM7;TIM5;USE_FULL_LL_DRIVER' since the value of 'TIM5' is unknown. Use -D if you want to check it. You can use -U to skip it explicitly. [ConfigurationNotChecked]
  else if (TIMx == TIM5)
^
Firmware/mock/nucleof030r8/ir_sensor_mock/Drivers/STM32F0xx_HAL_Driver/Src/stm32f0xx_ll_tim.c:175:0: information: Skipping configuration 'TIM1;TIM14;TIM15;TIM16;TIM17;TIM2;TIM3;TIM6;TIM7;TIM6;USE_FULL_LL_DRIVER' since the value of 'TIM1' is unknown. Use -D if you want to check it. You can use -U to skip it explicitly. [ConfigurationNotChecked]
  if (TIMx == TIM1)
^
Firmware/mock/nucleof030r8/ir_sensor_mock/Drivers/STM32F0xx_HAL_Driver/Src/stm32f0xx_ll_tim.c:223:0: information: Skipping configuration 'TIM1;TIM14;TIM15;TIM16;TIM17;TIM2;TIM3;TIM6;TIM7;TIM6;USE_FULL_LL_DRIVER' since the value of 'TIM14' is unknown. Use -D if you want to check it. You can use -U to skip it explicitly. [ConfigurationNotChecked]
  else if (TIMx == TIM14)
^
Firmware/mock/nucleof030r8/ir_sensor_mock/Drivers/STM32F0xx_HAL_Driver/Src/stm32f0xx_ll_tim.c:230:0: information: Skipping configuration 'TIM1;TIM14;TIM15;TIM16;TIM17;TIM2;TIM3;TIM6;TIM7;TIM6;USE_FULL_LL_DRIVER' since the value of 'TIM15' is unknown. Use -D if you want to check it. You can use -U to skip it explicitly. [ConfigurationNotChecked]
  else if (TIMx == TIM15)
^
Firmware/mock/nucleof030r8/ir_sensor_mock/Drivers/STM32F0xx_HAL_Driver/Src/stm32f0xx_ll_tim.c:237:0: information: Skipping configuration 'TIM1;TIM14;TIM15;TIM16;TIM17;TIM2;TIM3;TIM6;TIM7;TIM6;USE_FULL_LL_DRIVER' since the value of 'TIM16' is unknown. Use -D if you want to check it. You can use -U to skip it explicitly. [ConfigurationNotChecked]
  else if (TIMx == TIM16)
^
Firmware/mock/nucleof030r8/ir_sensor_mock/Drivers/STM32F0xx_HAL_Driver/Src/stm32f0xx_ll_tim.c:244:0: information: Skipping configuration 'TIM1;TIM14;TIM15;TIM16;TIM17;TIM2;TIM3;TIM6;TIM7;TIM6;USE_FULL_LL_DRIVER' since the value of 'TIM17' is unknown. Use -D if you want to check it. You can use -U to skip it explicitly. [ConfigurationNotChecked]
  else if (TIMx == TIM17)
^
Firmware/mock/nucleof030r8/ir_sensor_mock/Drivers/STM32F0xx_HAL_Driver/Src/stm32f0xx_ll_tim.c:181:0: information: Skipping configuration 'TIM1;TIM14;TIM15;TIM16;TIM17;TIM2;TIM3;TIM6;TIM7;TIM6;USE_FULL_LL_DRIVER' since the value of 'TIM2' is unknown. Use -D if you want to check it. You can use -U to skip it explicitly. [ConfigurationNotChecked]
  else if (TIMx == TIM2)
^
Firmware/mock/nucleof030r8/ir_sensor_mock/Drivers/STM32F0xx_HAL_Driver/Src/stm32f0xx_ll_tim.c:188:0: information: Skipping configuration 'TIM1;TIM14;TIM15;TIM16;TIM17;TIM2;TIM3;TIM6;TIM7;TIM6;USE_FULL_LL_DRIVER' since the value of 'TIM3' is unknown. Use -D if you want to check it. You can use -U to skip it explicitly. [ConfigurationNotChecked]
  else if (TIMx == TIM3)
^
Firmware/mock/nucleof030r8/ir_sensor_mock/Drivers/STM32F0xx_HAL_Driver/Src/stm32f0xx_ll_tim.c:202:0: information: Skipping configuration 'TIM1;TIM14;TIM15;TIM16;TIM17;TIM2;TIM3;TIM6;TIM7;TIM6;USE_FULL_LL_DRIVER' since the value of 'TIM6' is unknown. Use -D if you want to check it. You can use -U to skip it explicitly. [ConfigurationNotChecked]
  else if (TIMx == TIM6)
^
Firmware/mock/nucleof030r8/ir_sensor_mock/Drivers/STM32F0xx_HAL_Driver/Src/stm32f0xx_ll_tim.c:209:0: information: Skipping configuration 'TIM1;TIM14;TIM15;TIM16;TIM17;TIM2;TIM3;TIM6;TIM7;TIM6;USE_FULL_LL_DRIVER' since the value of 'TIM7' is unknown. Use -D if you want to check it. You can use -U to skip it explicitly. [ConfigurationNotChecked]
  else if (TIMx == TIM7)
^
Firmware/mock/nucleof030r8/ir_sensor_mock/Drivers/STM32F0xx_HAL_Driver/Src/stm32f0xx_ll_tim.c:175:0: information: Skipping configuration 'TIM1;TIM14;TIM15;TIM16;TIM17;TIM2;TIM3;TIM6;TIM7;TIM7;USE_FULL_LL_DRIVER' since the value of 'TIM1' is unknown. Use -D if you want to check it. You can use -U to skip it explicitly. [ConfigurationNotChecked]
  if (TIMx == TIM1)
^
Firmware/mock/nucleof030r8/ir_sensor_mock/Drivers/STM32F0xx_HAL_Driver/Src/stm32f0xx_ll_tim.c:223:0: information: Skipping configuration 'TIM1;TIM14;TIM15;TIM16;TIM17;TIM2;TIM3;TIM6;TIM7;TIM7;USE_FULL_LL_DRIVER' since the value of 'TIM14' is unknown. Use -D if you want to check it. You can use -U to skip it explicitly. [ConfigurationNotChecked]
  else if (TIMx == TIM14)
^
Firmware/mock/nucleof030r8/ir_sensor_mock/Drivers/STM32F0xx_HAL_Driver/Src/stm32f0xx_ll_tim.c:230:0: information: Skipping configuration 'TIM1;TIM14;TIM15;TIM16;TIM17;TIM2;TIM3;TIM6;TIM7;TIM7;USE_FULL_LL_DRIVER' since the value of 'TIM15' is unknown. Use -D if you want to check it. You can use -U to skip it explicitly. [ConfigurationNotChecked]
  else if (TIMx == TIM15)
^
Firmware/mock/nucleof030r8/ir_sensor_mock/Drivers/STM32F0xx_HAL_Driver/Src/stm32f0xx_ll_tim.c:237:0: information: Skipping configuration 'TIM1;TIM14;TIM15;TIM16;TIM17;TIM2;TIM3;TIM6;TIM7;TIM7;USE_FULL_LL_DRIVER' since the value of 'TIM16' is unknown. Use -D if you want to check it. You can use -U to skip it explicitly. [ConfigurationNotChecked]
  else if (TIMx == TIM16)
^
Firmware/mock/nucleof030r8/ir_sensor_mock/Drivers/STM32F0xx_HAL_Driver/Src/stm32f0xx_ll_tim.c:244:0: information: Skipping configuration 'TIM1;TIM14;TIM15;TIM16;TIM17;TIM2;TIM3;TIM6;TIM7;TIM7;USE_FULL_LL_DRIVER' since the value of 'TIM17' is unknown. Use -D if you want to check it. You can use -U to skip it explicitly. [ConfigurationNotChecked]
  else if (TIMx == TIM17)
^
Firmware/mock/nucleof030r8/ir_sensor_mock/Drivers/STM32F0xx_HAL_Driver/Src/stm32f0xx_ll_tim.c:181:0: information: Skipping configuration 'TIM1;TIM14;TIM15;TIM16;TIM17;TIM2;TIM3;TIM6;TIM7;TIM7;USE_FULL_LL_DRIVER' since the value of 'TIM2' is unknown. Use -D if you want to check it. You can use -U to skip it explicitly. [ConfigurationNotChecked]
  else if (TIMx == TIM2)
^
Firmware/mock/nucleof030r8/ir_sensor_mock/Drivers/STM32F0xx_HAL_Driver/Src/stm32f0xx_ll_tim.c:188:0: information: Skipping configuration 'TIM1;TIM14;TIM15;TIM16;TIM17;TIM2;TIM3;TIM6;TIM7;TIM7;USE_FULL_LL_DRIVER' since the value of 'TIM3' is unknown. Use -D if you want to check it. You can use -U to skip it explicitly. [ConfigurationNotChecked]
  else if (TIMx == TIM3)
^
Firmware/mock/nucleof030r8/ir_sensor_mock/Drivers/STM32F0xx_HAL_Driver/Src/stm32f0xx_ll_tim.c:202:0: information: Skipping configuration 'TIM1;TIM14;TIM15;TIM16;TIM17;TIM2;TIM3;TIM6;TIM7;TIM7;USE_FULL_LL_DRIVER' since the value of 'TIM6' is unknown. Use -D if you want to check it. You can use -U to skip it explicitly. [ConfigurationNotChecked]
  else if (TIMx == TIM6)
^
Firmware/mock/nucleof030r8/ir_sensor_mock/Drivers/STM32F0xx_HAL_Driver/Src/stm32f0xx_ll_tim.c:209:0: information: Skipping configuration 'TIM1;TIM14;TIM15;TIM16;TIM17;TIM2;TIM3;TIM6;TIM7;TIM7;USE_FULL_LL_DRIVER' since the value of 'TIM7' is unknown. Use -D if you want to check it. You can use -U to skip it explicitly. [ConfigurationNotChecked]
  else if (TIMx == TIM7)
^
Firmware/mock/nucleof030r8/ir_sensor_mock/Drivers/STM32F0xx_HAL_Driver/Src/stm32f0xx_ll_tim.c:175:0: information: Skipping configuration 'TIM1;TIM14;TIM15;TIM16;TIM17;TIM2;TIM3;TIM6;TIM7;TIM8;USE_FULL_LL_DRIVER' since the value of 'TIM1' is unknown. Use -D if you want to check it. You can use -U to skip it explicitly. [ConfigurationNotChecked]
  if (TIMx == TIM1)
^
Firmware/mock/nucleof030r8/ir_sensor_mock/Drivers/STM32F0xx_HAL_Driver/Src/stm32f0xx_ll_tim.c:223:0: information: Skipping configuration 'TIM1;TIM14;TIM15;TIM16;TIM17;TIM2;TIM3;TIM6;TIM7;TIM8;USE_FULL_LL_DRIVER' since the value of 'TIM14' is unknown. Use -D if you want to check it. You can use -U to skip it explicitly. [ConfigurationNotChecked]
  else if (TIMx == TIM14)
^
Firmware/mock/nucleof030r8/ir_sensor_mock/Drivers/STM32F0xx_HAL_Driver/Src/stm32f0xx_ll_tim.c:230:0: information: Skipping configuration 'TIM1;TIM14;TIM15;TIM16;TIM17;TIM2;TIM3;TIM6;TIM7;TIM8;USE_FULL_LL_DRIVER' since the value of 'TIM15' is unknown. Use -D if you want to check it. You can use -U to skip it explicitly. [ConfigurationNotChecked]
  else if (TIMx == TIM15)
^
Firmware/mock/nucleof030r8/ir_sensor_mock/Drivers/STM32F0xx_HAL_Driver/Src/stm32f0xx_ll_tim.c:237:0: information: Skipping configuration 'TIM1;TIM14;TIM15;TIM16;TIM17;TIM2;TIM3;TIM6;TIM7;TIM8;USE_FULL_LL_DRIVER' since the value of 'TIM16' is unknown. Use -D if you want to check it. You can use -U to skip it explicitly. [ConfigurationNotChecked]
  else if (TIMx == TIM16)
^
Firmware/mock/nucleof030r8/ir_sensor_mock/Drivers/STM32F0xx_HAL_Driver/Src/stm32f0xx_ll_tim.c:244:0: information: Skipping configuration 'TIM1;TIM14;TIM15;TIM16;TIM17;TIM2;TIM3;TIM6;TIM7;TIM8;USE_FULL_LL_DRIVER' since the value of 'TIM17' is unknown. Use -D if you want to check it. You can use -U to skip it explicitly. [ConfigurationNotChecked]
  else if (TIMx == TIM17)
^
Firmware/mock/nucleof030r8/ir_sensor_mock/Drivers/STM32F0xx_HAL_Driver/Src/stm32f0xx_ll_tim.c:181:0: information: Skipping configuration 'TIM1;TIM14;TIM15;TIM16;TIM17;TIM2;TIM3;TIM6;TIM7;TIM8;USE_FULL_LL_DRIVER' since the value of 'TIM2' is unknown. Use -D if you want to check it. You can use -U to skip it explicitly. [ConfigurationNotChecked]
  else if (TIMx == TIM2)
^
Firmware/mock/nucleof030r8/ir_sensor_mock/Drivers/STM32F0xx_HAL_Driver/Src/stm32f0xx_ll_tim.c:188:0: information: Skipping configuration 'TIM1;TIM14;TIM15;TIM16;TIM17;TIM2;TIM3;TIM6;TIM7;TIM8;USE_FULL_LL_DRIVER' since the value of 'TIM3' is unknown. Use -D if you want to check it. You can use -U to skip it explicitly. [ConfigurationNotChecked]
  else if (TIMx == TIM3)
^
Firmware/mock/nucleof030r8/ir_sensor_mock/Drivers/STM32F0xx_HAL_Driver/Src/stm32f0xx_ll_tim.c:202:0: information: Skipping configuration 'TIM1;TIM14;TIM15;TIM16;TIM17;TIM2;TIM3;TIM6;TIM7;TIM8;USE_FULL_LL_DRIVER' since the value of 'TIM6' is unknown. Use -D if you want to check it. You can use -U to skip it explicitly. [ConfigurationNotChecked]
  else if (TIMx == TIM6)
^
Firmware/mock/nucleof030r8/ir_sensor_mock/Drivers/STM32F0xx_HAL_Driver/Src/stm32f0xx_ll_tim.c:209:0: information: Skipping configuration 'TIM1;TIM14;TIM15;TIM16;TIM17;TIM2;TIM3;TIM6;TIM7;TIM8;USE_FULL_LL_DRIVER' since the value of 'TIM7' is unknown. Use -D if you want to check it. You can use -U to skip it explicitly. [ConfigurationNotChecked]
  else if (TIMx == TIM7)
^
Firmware/mock/nucleof030r8/ir_sensor_mock/Drivers/STM32F0xx_HAL_Driver/Src/stm32f0xx_ll_tim.c:216:0: information: Skipping configuration 'TIM1;TIM14;TIM15;TIM16;TIM17;TIM2;TIM3;TIM6;TIM7;TIM8;USE_FULL_LL_DRIVER' since the value of 'TIM8' is unknown. Use -D if you want to check it. You can use -U to skip it explicitly. [ConfigurationNotChecked]
  else if (TIMx == TIM8)
^
Firmware/mock/nucleof030r8/ir_sensor_mock/Drivers/STM32F0xx_HAL_Driver/Src/stm32f0xx_ll_tim.c:175:0: information: Skipping configuration 'TIM1;TIM14;TIM15;TIM16;TIM17;TIM2;TIM3;TIM6;TIM7;USE_FULL_LL_DRIVER' since the value of 'TIM1' is unknown. Use -D if you want to check it. You can use -U to skip it explicitly. [ConfigurationNotChecked]
  if (TIMx == TIM1)
^
Firmware/mock/nucleof030r8/ir_sensor_mock/Drivers/STM32F0xx_HAL_Driver/Src/stm32f0xx_ll_tim.c:223:0: information: Skipping configuration 'TIM1;TIM14;TIM15;TIM16;TIM17;TIM2;TIM3;TIM6;TIM7;USE_FULL_LL_DRIVER' since the value of 'TIM14' is unknown. Use -D if you want to check it. You can use -U to skip it explicitly. [ConfigurationNotChecked]
  else if (TIMx == TIM14)
^
Firmware/mock/nucleof030r8/ir_sensor_mock/Drivers/STM32F0xx_HAL_Driver/Src/stm32f0xx_ll_tim.c:230:0: information: Skipping configuration 'TIM1;TIM14;TIM15;TIM16;TIM17;TIM2;TIM3;TIM6;TIM7;USE_FULL_LL_DRIVER' since the value of 'TIM15' is unknown. Use -D if you want to check it. You can use -U to skip it explicitly. [ConfigurationNotChecked]
  else if (TIMx == TIM15)
^
Firmware/mock/nucleof030r8/ir_sensor_mock/Drivers/STM32F0xx_HAL_Driver/Src/stm32f0xx_ll_tim.c:237:0: information: Skipping configuration 'TIM1;TIM14;TIM15;TIM16;TIM17;TIM2;TIM3;TIM6;TIM7;USE_FULL_LL_DRIVER' since the value of 'TIM16' is unknown. Use -D if you want to check it. You can use -U to skip it explicitly. [ConfigurationNotChecked]
  else if (TIMx == TIM16)
^
Firmware/mock/nucleof030r8/ir_sensor_mock/Drivers/STM32F0xx_HAL_Driver/Src/stm32f0xx_ll_tim.c:244:0: information: Skipping configuration 'TIM1;TIM14;TIM15;TIM16;TIM17;TIM2;TIM3;TIM6;TIM7;USE_FULL_LL_DRIVER' since the value of 'TIM17' is unknown. Use -D if you want to check it. You can use -U to skip it explicitly. [ConfigurationNotChecked]
  else if (TIMx == TIM17)
^
Firmware/mock/nucleof030r8/ir_sensor_mock/Drivers/STM32F0xx_HAL_Driver/Src/stm32f0xx_ll_tim.c:181:0: information: Skipping configuration 'TIM1;TIM14;TIM15;TIM16;TIM17;TIM2;TIM3;TIM6;TIM7;USE_FULL_LL_DRIVER' since the value of 'TIM2' is unknown. Use -D if you want to check it. You can use -U to skip it explicitly. [ConfigurationNotChecked]
  else if (TIMx == TIM2)
^
Firmware/mock/nucleof030r8/ir_sensor_mock/Drivers/STM32F0xx_HAL_Driver/Src/stm32f0xx_ll_tim.c:188:0: information: Skipping configuration 'TIM1;TIM14;TIM15;TIM16;TIM17;TIM2;TIM3;TIM6;TIM7;USE_FULL_LL_DRIVER' since the value of 'TIM3' is unknown. Use -D if you want to check it. You can use -U to skip it explicitly. [ConfigurationNotChecked]
  else if (TIMx == TIM3)
^
Firmware/mock/nucleof030r8/ir_sensor_mock/Drivers/STM32F0xx_HAL_Driver/Src/stm32f0xx_ll_tim.c:202:0: information: Skipping configuration 'TIM1;TIM14;TIM15;TIM16;TIM17;TIM2;TIM3;TIM6;TIM7;USE_FULL_LL_DRIVER' since the value of 'TIM6' is unknown. Use -D if you want to check it. You can use -U to skip it explicitly. [ConfigurationNotChecked]
  else if (TIMx == TIM6)
^
Firmware/mock/nucleof030r8/ir_sensor_mock/Drivers/STM32F0xx_HAL_Driver/Src/stm32f0xx_ll_tim.c:209:0: information: Skipping configuration 'TIM1;TIM14;TIM15;TIM16;TIM17;TIM2;TIM3;TIM6;TIM7;USE_FULL_LL_DRIVER' since the value of 'TIM7' is unknown. Use -D if you want to check it. You can use -U to skip it explicitly. [ConfigurationNotChecked]
  else if (TIMx == TIM7)
^
Firmware/mock/nucleof030r8/ir_sensor_mock/Drivers/STM32F0xx_HAL_Driver/Src/stm32f0xx_ll_usart.c:0:0: information: Too many #ifdef configurations - cppcheck only checks 12 of 16 configurations. Use --force to check all configurations. [toomanyconfigs]

^
Firmware/mock/nucleof030r8/ir_sensor_mock/Drivers/STM32F0xx_HAL_Driver/Src/stm32f0xx_ll_usart.c:144:0: information: Skipping configuration 'RCC_CFGR3_USART2SW;UART4;UART5;USART1;USART2;USART3;USART6;USART7;USART8;USART2;USE_FULL_LL_DRIVER' since the value of 'USART1' is unknown. Use -D if you want to check it. You can use -U to skip it explicitly. [ConfigurationNotChecked]
  if (USARTx == USART1)
^
Firmware/mock/nucleof030r8/ir_sensor_mock/Drivers/STM32F0xx_HAL_Driver/Src/stm32f0xx_ll_usart.c:296:0: information: Skipping configuration 'RCC_CFGR3_USART2SW;UART4;UART5;USART1;USART2;USART3;USART6;USART7;USART8;USART2;USE_FULL_LL_DRIVER' since the value of 'USART1' is unknown. Use -D if you want to check it. You can use -U to skip it explicitly. [ConfigurationNotChecked]
    if (USARTx == USART1)
^
Firmware/mock/nucleof030r8/ir_sensor_mock/Drivers/STM32F0xx_HAL_Driver/Src/stm32f0xx_ll_usart.c:153:0: information: Skipping configuration 'RCC_CFGR3_USART2SW;UART4;UART5;USART1;USART2;USART3;USART6;USART7;USART8;USART2;USE_FULL_LL_DRIVER' since the value of 'USART2' is unknown. Use -D if you want to check it. You can use -U to skip it explicitly. [ConfigurationNotChecked]
  else if (USARTx == USART2)
^
Firmware/mock/nucleof030r8/ir_sensor_mock/Drivers/STM32F0xx_HAL_Driver/Src/stm32f0xx_ll_usart.c:301:0: information: Skipping configuration 'RCC_CFGR3_USART2SW;UART4;UART5;USART1;USART2;USART3;USART6;USART7;USART8;USART2;USE_FULL_LL_DRIVER' since the value of 'USART2' is unknown. Use -D if you want to check it. You can use -U to skip it explicitly. [ConfigurationNotChecked]
    else if (USARTx == USART2)
^
Firmware/mock/nucleof030r8/ir_sensor_mock/Drivers/STM32F0xx_HAL_Driver/Src/stm32f0xx_ll_usart.c:163:0: information: Skipping configuration 'RCC_CFGR3_USART2SW;UART4;UART5;USART1;USART2;USART3;USART6;USART7;USART8;USART2;USE_FULL_LL_DRIVER' since the value of 'USART3' is unknown. Use -D if you want to check it. You can use -U to skip it explicitly. [ConfigurationNotChecked]
  else if (USARTx == USART3)
^
Firmware/mock/nucleof030r8/ir_sensor_mock/Drivers/STM32F0xx_HAL_Driver/Src/stm32f0xx_ll_usart.c:313:0: information: Skipping configuration 'RCC_CFGR3_USART2SW;UART4;UART5;USART1;USART2;USART3;USART6;USART7;USART8;USART2;USE_FULL_LL_DRIVER' since the value of 'USART3' is unknown. Use -D if you want to check it. You can use -U to skip it explicitly. [ConfigurationNotChecked]
    else if (USARTx == USART3)
^
Firmware/mock/nucleof030r8/ir_sensor_mock/Drivers/STM32F0xx_HAL_Driver/Src/stm32f0xx_ll_usart.c:193:0: information: Skipping configuration 'RCC_CFGR3_USART2SW;UART4;UART5;USART1;USART2;USART3;USART6;USART7;USART8;USART2;USE_FULL_LL_DRIVER' since the value of 'USART6' is unknown. Use -D if you want to check it. You can use -U to skip it explicitly. [ConfigurationNotChecked]
  else if (USARTx == USART6)
^
Firmware/mock/nucleof030r8/ir_sensor_mock/Drivers/STM32F0xx_HAL_Driver/Src/stm32f0xx_ll_usart.c:341:0: information: Skipping configuration 'RCC_CFGR3_USART2SW;UART4;UART5;USART1;USART2;USART3;USART6;USART7;USART8;USART2;USE_FULL_LL_DRIVER' since the value of 'USART6' is unknown. Use -D if you want to check it. You can use -U to skip it explicitly. [ConfigurationNotChecked]
    else if (USARTx == USART6)
^
Firmware/mock/nucleof030r8/ir_sensor_mock/Drivers/STM32F0xx_HAL_Driver/Src/stm32f0xx_ll_usart.c:203:0: information: Skipping configuration 'RCC_CFGR3_USART2SW;UART4;UART5;USART1;USART2;USART3;USART6;USART7;USART8;USART2;USE_FULL_LL_DRIVER' since the value of 'USART7' is unknown. Use -D if you want to check it. You can use -U to skip it explicitly. [ConfigurationNotChecked]
  else if (USARTx == USART7)
^
Firmware/mock/nucleof030r8/ir_sensor_mock/Drivers/STM32F0xx_HAL_Driver/Src/stm32f0xx_ll_usart.c:349:0: information: Skipping configuration 'RCC_CFGR3_USART2SW;UART4;UART5;USART1;USART2;USART3;USART6;USART7;USART8;USART2;USE_FULL_LL_DRIVER' since the value of 'USART7' is unknown. Use -D if you want to check it. You can use -U to skip it explicitly. [ConfigurationNotChecked]
    else if (USARTx == USART7)
^
Firmware/mock/nucleof030r8/ir_sensor_mock/Drivers/STM32F0xx_HAL_Driver/Src/stm32f0xx_ll_usart.c:213:0: information: Skipping configuration 'RCC_CFGR3_USART2SW;UART4;UART5;USART1;USART2;USART3;USART6;USART7;USART8;USART2;USE_FULL_LL_DRIVER' since the value of 'USART8' is unknown. Use -D if you want to check it. You can use -U to skip it explicitly. [ConfigurationNotChecked]
  else if (USARTx == USART8)
^
Firmware/mock/nucleof030r8/ir_sensor_mock/Drivers/STM32F0xx_HAL_Driver/Src/stm32f0xx_ll_usart.c:357:0: information: Skipping configuration 'RCC_CFGR3_USART2SW;UART4;UART5;USART1;USART2;USART3;USART6;USART7;USART8;USART2;USE_FULL_LL_DRIVER' since the value of 'USART8' is unknown. Use -D if you want to check it. You can use -U to skip it explicitly. [ConfigurationNotChecked]
    else if (USARTx == USART8)
^
Firmware/mock/nucleof030r8/ir_sensor_mock/Drivers/STM32F0xx_HAL_Driver/Src/stm32f0xx_ll_usart.c:144:0: information: Skipping configuration 'RCC_CFGR3_USART3SW;UART4;UART5;USART1;USART2;USART3;USART6;USART7;USART8;USART3;USE_FULL_LL_DRIVER' since the value of 'USART1' is unknown. Use -D if you want to check it. You can use -U to skip it explicitly. [ConfigurationNotChecked]
  if (USARTx == USART1)
^
Firmware/mock/nucleof030r8/ir_sensor_mock/Drivers/STM32F0xx_HAL_Driver/Src/stm32f0xx_ll_usart.c:296:0: information: Skipping configuration 'RCC_CFGR3_USART3SW;UART4;UART5;USART1;USART2;USART3;USART6;USART7;USART8;USART3;USE_FULL_LL_DRIVER' since the value of 'USART1' is unknown. Use -D if you want to check it. You can use -U to skip it explicitly. [ConfigurationNotChecked]
    if (USARTx == USART1)
^
Firmware/mock/nucleof030r8/ir_sensor_mock/Drivers/STM32F0xx_HAL_Driver/Src/stm32f0xx_ll_usart.c:153:0: information: Skipping configuration 'RCC_CFGR3_USART3SW;UART4;UART5;USART1;USART2;USART3;USART6;USART7;USART8;USART3;USE_FULL_LL_DRIVER' since the value of 'USART2' is unknown. Use -D if you want to check it. You can use -U to skip it explicitly. [ConfigurationNotChecked]
  else if (USARTx == USART2)
^
Firmware/mock/nucleof030r8/ir_sensor_mock/Drivers/STM32F0xx_HAL_Driver/Src/stm32f0xx_ll_usart.c:301:0: information: Skipping configuration 'RCC_CFGR3_USART3SW;UART4;UART5;USART1;USART2;USART3;USART6;USART7;USART8;USART3;USE_FULL_LL_DRIVER' since the value of 'USART2' is unknown. Use -D if you want to check it. You can use -U to skip it explicitly. [ConfigurationNotChecked]
    else if (USARTx == USART2)
^
Firmware/mock/nucleof030r8/ir_sensor_mock/Drivers/STM32F0xx_HAL_Driver/Src/stm32f0xx_ll_usart.c:163:0: information: Skipping configuration 'RCC_CFGR3_USART3SW;UART4;UART5;USART1;USART2;USART3;USART6;USART7;USART8;USART3;USE_FULL_LL_DRIVER' since the value of 'USART3' is unknown. Use -D if you want to check it. You can use -U to skip it explicitly. [ConfigurationNotChecked]
  else if (USARTx == USART3)
^
Firmware/mock/nucleof030r8/ir_sensor_mock/Drivers/STM32F0xx_HAL_Driver/Src/stm32f0xx_ll_usart.c:313:0: information: Skipping configuration 'RCC_CFGR3_USART3SW;UART4;UART5;USART1;USART2;USART3;USART6;USART7;USART8;USART3;USE_FULL_LL_DRIVER' since the value of 'USART3' is unknown. Use -D if you want to check it. You can use -U to skip it explicitly. [ConfigurationNotChecked]
    else if (USARTx == USART3)
^
Firmware/mock/nucleof030r8/ir_sensor_mock/Drivers/STM32F0xx_HAL_Driver/Src/stm32f0xx_ll_usart.c:193:0: information: Skipping configuration 'RCC_CFGR3_USART3SW;UART4;UART5;USART1;USART2;USART3;USART6;USART7;USART8;USART3;USE_FULL_LL_DRIVER' since the value of 'USART6' is unknown. Use -D if you want to check it. You can use -U to skip it explicitly. [ConfigurationNotChecked]
  else if (USARTx == USART6)
^
Firmware/mock/nucleof030r8/ir_sensor_mock/Drivers/STM32F0xx_HAL_Driver/Src/stm32f0xx_ll_usart.c:341:0: information: Skipping configuration 'RCC_CFGR3_USART3SW;UART4;UART5;USART1;USART2;USART3;USART6;USART7;USART8;USART3;USE_FULL_LL_DRIVER' since the value of 'USART6' is unknown. Use -D if you want to check it. You can use -U to skip it explicitly. [ConfigurationNotChecked]
    else if (USARTx == USART6)
^
Firmware/mock/nucleof030r8/ir_sensor_mock/Drivers/STM32F0xx_HAL_Driver/Src/stm32f0xx_ll_usart.c:203:0: information: Skipping configuration 'RCC_CFGR3_USART3SW;UART4;UART5;USART1;USART2;USART3;USART6;USART7;USART8;USART3;USE_FULL_LL_DRIVER' since the value of 'USART7' is unknown. Use -D if you want to check it. You can use -U to skip it explicitly. [ConfigurationNotChecked]
  else if (USARTx == USART7)
^
Firmware/mock/nucleof030r8/ir_sensor_mock/Drivers/STM32F0xx_HAL_Driver/Src/stm32f0xx_ll_usart.c:349:0: information: Skipping configuration 'RCC_CFGR3_USART3SW;UART4;UART5;USART1;USART2;USART3;USART6;USART7;USART8;USART3;USE_FULL_LL_DRIVER' since the value of 'USART7' is unknown. Use -D if you want to check it. You can use -U to skip it explicitly. [ConfigurationNotChecked]
    else if (USARTx == USART7)
^
Firmware/mock/nucleof030r8/ir_sensor_mock/Drivers/STM32F0xx_HAL_Driver/Src/stm32f0xx_ll_usart.c:213:0: information: Skipping configuration 'RCC_CFGR3_USART3SW;UART4;UART5;USART1;USART2;USART3;USART6;USART7;USART8;USART3;USE_FULL_LL_DRIVER' since the value of 'USART8' is unknown. Use -D if you want to check it. You can use -U to skip it explicitly. [ConfigurationNotChecked]
  else if (USARTx == USART8)
^
Firmware/mock/nucleof030r8/ir_sensor_mock/Drivers/STM32F0xx_HAL_Driver/Src/stm32f0xx_ll_usart.c:357:0: information: Skipping configuration 'RCC_CFGR3_USART3SW;UART4;UART5;USART1;USART2;USART3;USART6;USART7;USART8;USART3;USE_FULL_LL_DRIVER' since the value of 'USART8' is unknown. Use -D if you want to check it. You can use -U to skip it explicitly. [ConfigurationNotChecked]
    else if (USARTx == USART8)
^
Firmware/mock/nucleof030r8/ir_sensor_mock/Drivers/STM32F0xx_HAL_Driver/Src/stm32f0xx_ll_usart.c:144:0: information: Skipping configuration 'UART4;UART5;USART1;USART2;USART3;USART6;USART7;USART8;USART2;USART3;USART4;USE_FULL_LL_DRIVER' since the value of 'USART1' is unknown. Use -D if you want to check it. You can use -U to skip it explicitly. [ConfigurationNotChecked]
  if (USARTx == USART1)
^
Firmware/mock/nucleof030r8/ir_sensor_mock/Drivers/STM32F0xx_HAL_Driver/Src/stm32f0xx_ll_usart.c:296:0: information: Skipping configuration 'UART4;UART5;USART1;USART2;USART3;USART6;USART7;USART8;USART2;USART3;USART4;USE_FULL_LL_DRIVER' since the value of 'USART1' is unknown. Use -D if you want to check it. You can use -U to skip it explicitly. [ConfigurationNotChecked]
    if (USARTx == USART1)
^
Firmware/mock/nucleof030r8/ir_sensor_mock/Drivers/STM32F0xx_HAL_Driver/Src/stm32f0xx_ll_usart.c:153:0: information: Skipping configuration 'UART4;UART5;USART1;USART2;USART3;USART6;USART7;USART8;USART2;USART3;USART4;USE_FULL_LL_DRIVER' since the value of 'USART2' is unknown. Use -D if you want to check it. You can use -U to skip it explicitly. [ConfigurationNotChecked]
  else if (USARTx == USART2)
^
Firmware/mock/nucleof030r8/ir_sensor_mock/Drivers/STM32F0xx_HAL_Driver/Src/stm32f0xx_ll_usart.c:301:0: information: Skipping configuration 'UART4;UART5;USART1;USART2;USART3;USART6;USART7;USART8;USART2;USART3;USART4;USE_FULL_LL_DRIVER' since the value of 'USART2' is unknown. Use -D if you want to check it. You can use -U to skip it explicitly. [ConfigurationNotChecked]
    else if (USARTx == USART2)
^
Firmware/mock/nucleof030r8/ir_sensor_mock/Drivers/STM32F0xx_HAL_Driver/Src/stm32f0xx_ll_usart.c:163:0: information: Skipping configuration 'UART4;UART5;USART1;USART2;USART3;USART6;USART7;USART8;USART2;USART3;USART4;USE_FULL_LL_DRIVER' since the value of 'USART3' is unknown. Use -D if you want to check it. You can use -U to skip it explicitly. [ConfigurationNotChecked]
  else if (USARTx == USART3)
^
Firmware/mock/nucleof030r8/ir_sensor_mock/Drivers/STM32F0xx_HAL_Driver/Src/stm32f0xx_ll_usart.c:313:0: information: Skipping configuration 'UART4;UART5;USART1;USART2;USART3;USART6;USART7;USART8;USART2;USART3;USART4;USE_FULL_LL_DRIVER' since the value of 'USART3' is unknown. Use -D if you want to check it. You can use -U to skip it explicitly. [ConfigurationNotChecked]
    else if (USARTx == USART3)
^
Firmware/mock/nucleof030r8/ir_sensor_mock/Drivers/STM32F0xx_HAL_Driver/Src/stm32f0xx_ll_usart.c:193:0: information: Skipping configuration 'UART4;UART5;USART1;USART2;USART3;USART6;USART7;USART8;USART2;USART3;USART4;USE_FULL_LL_DRIVER' since the value of 'USART6' is unknown. Use -D if you want to check it. You can use -U to skip it explicitly. [ConfigurationNotChecked]
  else if (USARTx == USART6)
^
Firmware/mock/nucleof030r8/ir_sensor_mock/Drivers/STM32F0xx_HAL_Driver/Src/stm32f0xx_ll_usart.c:341:0: information: Skipping configuration 'UART4;UART5;USART1;USART2;USART3;USART6;USART7;USART8;USART2;USART3;USART4;USE_FULL_LL_DRIVER' since the value of 'USART6' is unknown. Use -D if you want to check it. You can use -U to skip it explicitly. [ConfigurationNotChecked]
    else if (USARTx == USART6)
^
Firmware/mock/nucleof030r8/ir_sensor_mock/Drivers/STM32F0xx_HAL_Driver/Src/stm32f0xx_ll_usart.c:203:0: information: Skipping configuration 'UART4;UART5;USART1;USART2;USART3;USART6;USART7;USART8;USART2;USART3;USART4;USE_FULL_LL_DRIVER' since the value of 'USART7' is unknown. Use -D if you want to check it. You can use -U to skip it explicitly. [ConfigurationNotChecked]
  else if (USARTx == USART7)
^
Firmware/mock/nucleof030r8/ir_sensor_mock/Drivers/STM32F0xx_HAL_Driver/Src/stm32f0xx_ll_usart.c:349:0: information: Skipping configuration 'UART4;UART5;USART1;USART2;USART3;USART6;USART7;USART8;USART2;USART3;USART4;USE_FULL_LL_DRIVER' since the value of 'USART7' is unknown. Use -D if you want to check it. You can use -U to skip it explicitly. [ConfigurationNotChecked]
    else if (USARTx == USART7)
^
Firmware/mock/nucleof030r8/ir_sensor_mock/Drivers/STM32F0xx_HAL_Driver/Src/stm32f0xx_ll_usart.c:213:0: information: Skipping configuration 'UART4;UART5;USART1;USART2;USART3;USART6;USART7;USART8;USART2;USART3;USART4;USE_FULL_LL_DRIVER' since the value of 'USART8' is unknown. Use -D if you want to check it. You can use -U to skip it explicitly. [ConfigurationNotChecked]
  else if (USARTx == USART8)
^
Firmware/mock/nucleof030r8/ir_sensor_mock/Drivers/STM32F0xx_HAL_Driver/Src/stm32f0xx_ll_usart.c:357:0: information: Skipping configuration 'UART4;UART5;USART1;USART2;USART3;USART6;USART7;USART8;USART2;USART3;USART4;USE_FULL_LL_DRIVER' since the value of 'USART8' is unknown. Use -D if you want to check it. You can use -U to skip it explicitly. [ConfigurationNotChecked]
    else if (USARTx == USART8)
^
Firmware/mock/nucleof030r8/ir_sensor_mock/Drivers/STM32F0xx_HAL_Driver/Src/stm32f0xx_ll_usart.c:173:0: information: Skipping configuration 'UART4;UART5;USART1;USART2;USART3;USART6;USART7;USART8;USART2;USART3;USART4;USE_FULL_LL_DRIVER' since the value of 'USART4' is unknown. Use -D if you want to check it. You can use -U to skip it explicitly. [ConfigurationNotChecked]
  else if (USARTx == USART4)
^
Firmware/mock/nucleof030r8/ir_sensor_mock/Drivers/STM32F0xx_HAL_Driver/Src/stm32f0xx_ll_usart.c:325:0: information: Skipping configuration 'UART4;UART5;USART1;USART2;USART3;USART6;USART7;USART8;USART2;USART3;USART4;USE_FULL_LL_DRIVER' since the value of 'USART4' is unknown. Use -D if you want to check it. You can use -U to skip it explicitly. [ConfigurationNotChecked]
    else if (USARTx == USART4)
^
Firmware/mock/nucleof030r8/ir_sensor_mock/Drivers/STM32F0xx_HAL_Driver/Src/stm32f0xx_ll_usart.c:144:0: information: Skipping configuration 'UART4;UART5;USART1;USART2;USART3;USART6;USART7;USART8;USART2;USE_FULL_LL_DRIVER' since the value of 'USART1' is unknown. Use -D if you want to check it. You can use -U to skip it explicitly. [ConfigurationNotChecked]
  if (USARTx == USART1)
^
Firmware/mock/nucleof030r8/ir_sensor_mock/Drivers/STM32F0xx_HAL_Driver/Src/stm32f0xx_ll_usart.c:296:0: information: Skipping configuration 'UART4;UART5;USART1;USART2;USART3;USART6;USART7;USART8;USART2;USE_FULL_LL_DRIVER' since the value of 'USART1' is unknown. Use -D if you want to check it. You can use -U to skip it explicitly. [ConfigurationNotChecked]
    if (USARTx == USART1)
^
Firmware/mock/nucleof030r8/ir_sensor_mock/Drivers/STM32F0xx_HAL_Driver/Src/stm32f0xx_ll_usart.c:153:0: information: Skipping configuration 'UART4;UART5;USART1;USART2;USART3;USART6;USART7;USART8;USART2;USE_FULL_LL_DRIVER' since the value of 'USART2' is unknown. Use -D if you want to check it. You can use -U to skip it explicitly. [ConfigurationNotChecked]
  else if (USARTx == USART2)
^
Firmware/mock/nucleof030r8/ir_sensor_mock/Drivers/STM32F0xx_HAL_Driver/Src/stm32f0xx_ll_usart.c:301:0: information: Skipping configuration 'UART4;UART5;USART1;USART2;USART3;USART6;USART7;USART8;USART2;USE_FULL_LL_DRIVER' since the value of 'USART2' is unknown. Use -D if you want to check it. You can use -U to skip it explicitly. [ConfigurationNotChecked]
    else if (USARTx == USART2)
^
Firmware/mock/nucleof030r8/ir_sensor_mock/Drivers/STM32F0xx_HAL_Driver/Src/stm32f0xx_ll_usart.c:163:0: information: Skipping configuration 'UART4;UART5;USART1;USART2;USART3;USART6;USART7;USART8;USART2;USE_FULL_LL_DRIVER' since the value of 'USART3' is unknown. Use -D if you want to check it. You can use -U to skip it explicitly. [ConfigurationNotChecked]
  else if (USARTx == USART3)
^
Firmware/mock/nucleof030r8/ir_sensor_mock/Drivers/STM32F0xx_HAL_Driver/Src/stm32f0xx_ll_usart.c:313:0: information: Skipping configuration 'UART4;UART5;USART1;USART2;USART3;USART6;USART7;USART8;USART2;USE_FULL_LL_DRIVER' since the value of 'USART3' is unknown. Use -D if you want to check it. You can use -U to skip it explicitly. [ConfigurationNotChecked]
    else if (USARTx == USART3)
^
Firmware/mock/nucleof030r8/ir_sensor_mock/Drivers/STM32F0xx_HAL_Driver/Src/stm32f0xx_ll_usart.c:193:0: information: Skipping configuration 'UART4;UART5;USART1;USART2;USART3;USART6;USART7;USART8;USART2;USE_FULL_LL_DRIVER' since the value of 'USART6' is unknown. Use -D if you want to check it. You can use -U to skip it explicitly. [ConfigurationNotChecked]
  else if (USARTx == USART6)
^
Firmware/mock/nucleof030r8/ir_sensor_mock/Drivers/STM32F0xx_HAL_Driver/Src/stm32f0xx_ll_usart.c:341:0: information: Skipping configuration 'UART4;UART5;USART1;USART2;USART3;USART6;USART7;USART8;USART2;USE_FULL_LL_DRIVER' since the value of 'USART6' is unknown. Use -D if you want to check it. You can use -U to skip it explicitly. [ConfigurationNotChecked]
    else if (USARTx == USART6)
^
Firmware/mock/nucleof030r8/ir_sensor_mock/Drivers/STM32F0xx_HAL_Driver/Src/stm32f0xx_ll_usart.c:203:0: information: Skipping configuration 'UART4;UART5;USART1;USART2;USART3;USART6;USART7;USART8;USART2;USE_FULL_LL_DRIVER' since the value of 'USART7' is unknown. Use -D if you want to check it. You can use -U to skip it explicitly. [ConfigurationNotChecked]
  else if (USARTx == USART7)
^
Firmware/mock/nucleof030r8/ir_sensor_mock/Drivers/STM32F0xx_HAL_Driver/Src/stm32f0xx_ll_usart.c:349:0: information: Skipping configuration 'UART4;UART5;USART1;USART2;USART3;USART6;USART7;USART8;USART2;USE_FULL_LL_DRIVER' since the value of 'USART7' is unknown. Use -D if you want to check it. You can use -U to skip it explicitly. [ConfigurationNotChecked]
    else if (USARTx == USART7)
^
Firmware/mock/nucleof030r8/ir_sensor_mock/Drivers/STM32F0xx_HAL_Driver/Src/stm32f0xx_ll_usart.c:213:0: information: Skipping configuration 'UART4;UART5;USART1;USART2;USART3;USART6;USART7;USART8;USART2;USE_FULL_LL_DRIVER' since the value of 'USART8' is unknown. Use -D if you want to check it. You can use -U to skip it explicitly. [ConfigurationNotChecked]
  else if (USARTx == USART8)
^
Firmware/mock/nucleof030r8/ir_sensor_mock/Drivers/STM32F0xx_HAL_Driver/Src/stm32f0xx_ll_usart.c:357:0: information: Skipping configuration 'UART4;UART5;USART1;USART2;USART3;USART6;USART7;USART8;USART2;USE_FULL_LL_DRIVER' since the value of 'USART8' is unknown. Use -D if you want to check it. You can use -U to skip it explicitly. [ConfigurationNotChecked]
    else if (USARTx == USART8)
^
Firmware/mock/nucleof030r8/ir_sensor_mock/Drivers/STM32F0xx_HAL_Driver/Src/stm32f0xx_ll_usart.c:144:0: information: Skipping configuration 'UART4;UART5;USART1;USART2;USART3;USART6;USART7;USART8;USART3;USE_FULL_LL_DRIVER' since the value of 'USART1' is unknown. Use -D if you want to check it. You can use -U to skip it explicitly. [ConfigurationNotChecked]
  if (USARTx == USART1)
^
Firmware/mock/nucleof030r8/ir_sensor_mock/Drivers/STM32F0xx_HAL_Driver/Src/stm32f0xx_ll_usart.c:296:0: information: Skipping configuration 'UART4;UART5;USART1;USART2;USART3;USART6;USART7;USART8;USART3;USE_FULL_LL_DRIVER' since the value of 'USART1' is unknown. Use -D if you want to check it. You can use -U to skip it explicitly. [ConfigurationNotChecked]
    if (USARTx == USART1)
^
Firmware/mock/nucleof030r8/ir_sensor_mock/Drivers/STM32F0xx_HAL_Driver/Src/stm32f0xx_ll_usart.c:153:0: information: Skipping configuration 'UART4;UART5;USART1;USART2;USART3;USART6;USART7;USART8;USART3;USE_FULL_LL_DRIVER' since the value of 'USART2' is unknown. Use -D if you want to check it. You can use -U to skip it explicitly. [ConfigurationNotChecked]
  else if (USARTx == USART2)
^
Firmware/mock/nucleof030r8/ir_sensor_mock/Drivers/STM32F0xx_HAL_Driver/Src/stm32f0xx_ll_usart.c:301:0: information: Skipping configuration 'UART4;UART5;USART1;USART2;USART3;USART6;USART7;USART8;USART3;USE_FULL_LL_DRIVER' since the value of 'USART2' is unknown. Use -D if you want to check it. You can use -U to skip it explicitly. [ConfigurationNotChecked]
    else if (USARTx == USART2)
^
Firmware/mock/nucleof030r8/ir_sensor_mock/Drivers/STM32F0xx_HAL_Driver/Src/stm32f0xx_ll_usart.c:163:0: information: Skipping configuration 'UART4;UART5;USART1;USART2;USART3;USART6;USART7;USART8;USART3;USE_FULL_LL_DRIVER' since the value of 'USART3' is unknown. Use -D if you want to check it. You can use -U to skip it explicitly. [ConfigurationNotChecked]
  else if (USARTx == USART3)
^
Firmware/mock/nucleof030r8/ir_sensor_mock/Drivers/STM32F0xx_HAL_Driver/Src/stm32f0xx_ll_usart.c:313:0: information: Skipping configuration 'UART4;UART5;USART1;USART2;USART3;USART6;USART7;USART8;USART3;USE_FULL_LL_DRIVER' since the value of 'USART3' is unknown. Use -D if you want to check it. You can use -U to skip it explicitly. [ConfigurationNotChecked]
    else if (USARTx == USART3)
^
Firmware/mock/nucleof030r8/ir_sensor_mock/Drivers/STM32F0xx_HAL_Driver/Src/stm32f0xx_ll_usart.c:193:0: information: Skipping configuration 'UART4;UART5;USART1;USART2;USART3;USART6;USART7;USART8;USART3;USE_FULL_LL_DRIVER' since the value of 'USART6' is unknown. Use -D if you want to check it. You can use -U to skip it explicitly. [ConfigurationNotChecked]
  else if (USARTx == USART6)
^
Firmware/mock/nucleof030r8/ir_sensor_mock/Drivers/STM32F0xx_HAL_Driver/Src/stm32f0xx_ll_usart.c:341:0: information: Skipping configuration 'UART4;UART5;USART1;USART2;USART3;USART6;USART7;USART8;USART3;USE_FULL_LL_DRIVER' since the value of 'USART6' is unknown. Use -D if you want to check it. You can use -U to skip it explicitly. [ConfigurationNotChecked]
    else if (USARTx == USART6)
^
Firmware/mock/nucleof030r8/ir_sensor_mock/Drivers/STM32F0xx_HAL_Driver/Src/stm32f0xx_ll_usart.c:203:0: information: Skipping configuration 'UART4;UART5;USART1;USART2;USART3;USART6;USART7;USART8;USART3;USE_FULL_LL_DRIVER' since the value of 'USART7' is unknown. Use -D if you want to check it. You can use -U to skip it explicitly. [ConfigurationNotChecked]
  else if (USARTx == USART7)
^
Firmware/mock/nucleof030r8/ir_sensor_mock/Drivers/STM32F0xx_HAL_Driver/Src/stm32f0xx_ll_usart.c:349:0: information: Skipping configuration 'UART4;UART5;USART1;USART2;USART3;USART6;USART7;USART8;USART3;USE_FULL_LL_DRIVER' since the value of 'USART7' is unknown. Use -D if you want to check it. You can use -U to skip it explicitly. [ConfigurationNotChecked]
    else if (USARTx == USART7)
^
Firmware/mock/nucleof030r8/ir_sensor_mock/Drivers/STM32F0xx_HAL_Driver/Src/stm32f0xx_ll_usart.c:213:0: information: Skipping configuration 'UART4;UART5;USART1;USART2;USART3;USART6;USART7;USART8;USART3;USE_FULL_LL_DRIVER' since the value of 'USART8' is unknown. Use -D if you want to check it. You can use -U to skip it explicitly. [ConfigurationNotChecked]
  else if (USARTx == USART8)
^
Firmware/mock/nucleof030r8/ir_sensor_mock/Drivers/STM32F0xx_HAL_Driver/Src/stm32f0xx_ll_usart.c:357:0: information: Skipping configuration 'UART4;UART5;USART1;USART2;USART3;USART6;USART7;USART8;USART3;USE_FULL_LL_DRIVER' since the value of 'USART8' is unknown. Use -D if you want to check it. You can use -U to skip it explicitly. [ConfigurationNotChecked]
    else if (USARTx == USART8)
^
Firmware/mock/nucleof030r8/ir_sensor_mock/Drivers/STM32F0xx_HAL_Driver/Src/stm32f0xx_ll_usart.c:144:0: information: Skipping configuration 'UART4;UART5;USART1;USART2;USART3;USART6;USART7;USART8;USART4;USE_FULL_LL_DRIVER' since the value of 'USART1' is unknown. Use -D if you want to check it. You can use -U to skip it explicitly. [ConfigurationNotChecked]
  if (USARTx == USART1)
^
Firmware/mock/nucleof030r8/ir_sensor_mock/Drivers/STM32F0xx_HAL_Driver/Src/stm32f0xx_ll_usart.c:296:0: information: Skipping configuration 'UART4;UART5;USART1;USART2;USART3;USART6;USART7;USART8;USART4;USE_FULL_LL_DRIVER' since the value of 'USART1' is unknown. Use -D if you want to check it. You can use -U to skip it explicitly. [ConfigurationNotChecked]
    if (USARTx == USART1)
^
Firmware/mock/nucleof030r8/ir_sensor_mock/Drivers/STM32F0xx_HAL_Driver/Src/stm32f0xx_ll_usart.c:153:0: information: Skipping configuration 'UART4;UART5;USART1;USART2;USART3;USART6;USART7;USART8;USART4;USE_FULL_LL_DRIVER' since the value of 'USART2' is unknown. Use -D if you want to check it. You can use -U to skip it explicitly. [ConfigurationNotChecked]
  else if (USARTx == USART2)
^
Firmware/mock/nucleof030r8/ir_sensor_mock/Drivers/STM32F0xx_HAL_Driver/Src/stm32f0xx_ll_usart.c:301:0: information: Skipping configuration 'UART4;UART5;USART1;USART2;USART3;USART6;USART7;USART8;USART4;USE_FULL_LL_DRIVER' since the value of 'USART2' is unknown. Use -D if you want to check it. You can use -U to skip it explicitly. [ConfigurationNotChecked]
    else if (USARTx == USART2)
^
Firmware/mock/nucleof030r8/ir_sensor_mock/Drivers/STM32F0xx_HAL_Driver/Src/stm32f0xx_ll_usart.c:163:0: information: Skipping configuration 'UART4;UART5;USART1;USART2;USART3;USART6;USART7;USART8;USART4;USE_FULL_LL_DRIVER' since the value of 'USART3' is unknown. Use -D if you want to check it. You can use -U to skip it explicitly. [ConfigurationNotChecked]
  else if (USARTx == USART3)
^
Firmware/mock/nucleof030r8/ir_sensor_mock/Drivers/STM32F0xx_HAL_Driver/Src/stm32f0xx_ll_usart.c:313:0: information: Skipping configuration 'UART4;UART5;USART1;USART2;USART3;USART6;USART7;USART8;USART4;USE_FULL_LL_DRIVER' since the value of 'USART3' is unknown. Use -D if you want to check it. You can use -U to skip it explicitly. [ConfigurationNotChecked]
    else if (USARTx == USART3)
^
Firmware/mock/nucleof030r8/ir_sensor_mock/Drivers/STM32F0xx_HAL_Driver/Src/stm32f0xx_ll_usart.c:193:0: information: Skipping configuration 'UART4;UART5;USART1;USART2;USART3;USART6;USART7;USART8;USART4;USE_FULL_LL_DRIVER' since the value of 'USART6' is unknown. Use -D if you want to check it. You can use -U to skip it explicitly. [ConfigurationNotChecked]
  else if (USARTx == USART6)
^
Firmware/mock/nucleof030r8/ir_sensor_mock/Drivers/STM32F0xx_HAL_Driver/Src/stm32f0xx_ll_usart.c:341:0: information: Skipping configuration 'UART4;UART5;USART1;USART2;USART3;USART6;USART7;USART8;USART4;USE_FULL_LL_DRIVER' since the value of 'USART6' is unknown. Use -D if you want to check it. You can use -U to skip it explicitly. [ConfigurationNotChecked]
    else if (USARTx == USART6)
^
Firmware/mock/nucleof030r8/ir_sensor_mock/Drivers/STM32F0xx_HAL_Driver/Src/stm32f0xx_ll_usart.c:203:0: information: Skipping configuration 'UART4;UART5;USART1;USART2;USART3;USART6;USART7;USART8;USART4;USE_FULL_LL_DRIVER' since the value of 'USART7' is unknown. Use -D if you want to check it. You can use -U to skip it explicitly. [ConfigurationNotChecked]
  else if (USARTx == USART7)
^
Firmware/mock/nucleof030r8/ir_sensor_mock/Drivers/STM32F0xx_HAL_Driver/Src/stm32f0xx_ll_usart.c:349:0: information: Skipping configuration 'UART4;UART5;USART1;USART2;USART3;USART6;USART7;USART8;USART4;USE_FULL_LL_DRIVER' since the value of 'USART7' is unknown. Use -D if you want to check it. You can use -U to skip it explicitly. [ConfigurationNotChecked]
    else if (USARTx == USART7)
^
Firmware/mock/nucleof030r8/ir_sensor_mock/Drivers/STM32F0xx_HAL_Driver/Src/stm32f0xx_ll_usart.c:213:0: information: Skipping configuration 'UART4;UART5;USART1;USART2;USART3;USART6;USART7;USART8;USART4;USE_FULL_LL_DRIVER' since the value of 'USART8' is unknown. Use -D if you want to check it. You can use -U to skip it explicitly. [ConfigurationNotChecked]
  else if (USARTx == USART8)
^
Firmware/mock/nucleof030r8/ir_sensor_mock/Drivers/STM32F0xx_HAL_Driver/Src/stm32f0xx_ll_usart.c:357:0: information: Skipping configuration 'UART4;UART5;USART1;USART2;USART3;USART6;USART7;USART8;USART4;USE_FULL_LL_DRIVER' since the value of 'USART8' is unknown. Use -D if you want to check it. You can use -U to skip it explicitly. [ConfigurationNotChecked]
    else if (USARTx == USART8)
^
Firmware/mock/nucleof030r8/ir_sensor_mock/Drivers/STM32F0xx_HAL_Driver/Src/stm32f0xx_ll_usart.c:173:0: information: Skipping configuration 'UART4;UART5;USART1;USART2;USART3;USART6;USART7;USART8;USART4;USE_FULL_LL_DRIVER' since the value of 'USART4' is unknown. Use -D if you want to check it. You can use -U to skip it explicitly. [ConfigurationNotChecked]
  else if (USARTx == USART4)
^
Firmware/mock/nucleof030r8/ir_sensor_mock/Drivers/STM32F0xx_HAL_Driver/Src/stm32f0xx_ll_usart.c:325:0: information: Skipping configuration 'UART4;UART5;USART1;USART2;USART3;USART6;USART7;USART8;USART4;USE_FULL_LL_DRIVER' since the value of 'USART4' is unknown. Use -D if you want to check it. You can use -U to skip it explicitly. [ConfigurationNotChecked]
    else if (USARTx == USART4)
^
Firmware/mock/nucleof030r8/ir_sensor_mock/Drivers/STM32F0xx_HAL_Driver/Src/stm32f0xx_ll_usart.c:144:0: information: Skipping configuration 'UART4;UART5;USART1;USART2;USART3;USART6;USART7;USART8;USART5;USE_FULL_LL_DRIVER' since the value of 'USART1' is unknown. Use -D if you want to check it. You can use -U to skip it explicitly. [ConfigurationNotChecked]
  if (USARTx == USART1)
^
Firmware/mock/nucleof030r8/ir_sensor_mock/Drivers/STM32F0xx_HAL_Driver/Src/stm32f0xx_ll_usart.c:296:0: information: Skipping configuration 'UART4;UART5;USART1;USART2;USART3;USART6;USART7;USART8;USART5;USE_FULL_LL_DRIVER' since the value of 'USART1' is unknown. Use -D if you want to check it. You can use -U to skip it explicitly. [ConfigurationNotChecked]
    if (USARTx == USART1)
^
Firmware/mock/nucleof030r8/ir_sensor_mock/Drivers/STM32F0xx_HAL_Driver/Src/stm32f0xx_ll_usart.c:153:0: information: Skipping configuration 'UART4;UART5;USART1;USART2;USART3;USART6;USART7;USART8;USART5;USE_FULL_LL_DRIVER' since the value of 'USART2' is unknown. Use -D if you want to check it. You can use -U to skip it explicitly. [ConfigurationNotChecked]
  else if (USARTx == USART2)
^
Firmware/mock/nucleof030r8/ir_sensor_mock/Drivers/STM32F0xx_HAL_Driver/Src/stm32f0xx_ll_usart.c:301:0: information: Skipping configuration 'UART4;UART5;USART1;USART2;USART3;USART6;USART7;USART8;USART5;USE_FULL_LL_DRIVER' since the value of 'USART2' is unknown. Use -D if you want to check it. You can use -U to skip it explicitly. [ConfigurationNotChecked]
    else if (USARTx == USART2)
^
Firmware/mock/nucleof030r8/ir_sensor_mock/Drivers/STM32F0xx_HAL_Driver/Src/stm32f0xx_ll_usart.c:163:0: information: Skipping configuration 'UART4;UART5;USART1;USART2;USART3;USART6;USART7;USART8;USART5;USE_FULL_LL_DRIVER' since the value of 'USART3' is unknown. Use -D if you want to check it. You can use -U to skip it explicitly. [ConfigurationNotChecked]
  else if (USARTx == USART3)
^
Firmware/mock/nucleof030r8/ir_sensor_mock/Drivers/STM32F0xx_HAL_Driver/Src/stm32f0xx_ll_usart.c:313:0: information: Skipping configuration 'UART4;UART5;USART1;USART2;USART3;USART6;USART7;USART8;USART5;USE_FULL_LL_DRIVER' since the value of 'USART3' is unknown. Use -D if you want to check it. You can use -U to skip it explicitly. [ConfigurationNotChecked]
    else if (USARTx == USART3)
^
Firmware/mock/nucleof030r8/ir_sensor_mock/Drivers/STM32F0xx_HAL_Driver/Src/stm32f0xx_ll_usart.c:193:0: information: Skipping configuration 'UART4;UART5;USART1;USART2;USART3;USART6;USART7;USART8;USART5;USE_FULL_LL_DRIVER' since the value of 'USART6' is unknown. Use -D if you want to check it. You can use -U to skip it explicitly. [ConfigurationNotChecked]
  else if (USARTx == USART6)
^
Firmware/mock/nucleof030r8/ir_sensor_mock/Drivers/STM32F0xx_HAL_Driver/Src/stm32f0xx_ll_usart.c:341:0: information: Skipping configuration 'UART4;UART5;USART1;USART2;USART3;USART6;USART7;USART8;USART5;USE_FULL_LL_DRIVER' since the value of 'USART6' is unknown. Use -D if you want to check it. You can use -U to skip it explicitly. [ConfigurationNotChecked]
    else if (USARTx == USART6)
^
Firmware/mock/nucleof030r8/ir_sensor_mock/Drivers/STM32F0xx_HAL_Driver/Src/stm32f0xx_ll_usart.c:203:0: information: Skipping configuration 'UART4;UART5;USART1;USART2;USART3;USART6;USART7;USART8;USART5;USE_FULL_LL_DRIVER' since the value of 'USART7' is unknown. Use -D if you want to check it. You can use -U to skip it explicitly. [ConfigurationNotChecked]
  else if (USARTx == USART7)
^
Firmware/mock/nucleof030r8/ir_sensor_mock/Drivers/STM32F0xx_HAL_Driver/Src/stm32f0xx_ll_usart.c:349:0: information: Skipping configuration 'UART4;UART5;USART1;USART2;USART3;USART6;USART7;USART8;USART5;USE_FULL_LL_DRIVER' since the value of 'USART7' is unknown. Use -D if you want to check it. You can use -U to skip it explicitly. [ConfigurationNotChecked]
    else if (USARTx == USART7)
^
Firmware/mock/nucleof030r8/ir_sensor_mock/Drivers/STM32F0xx_HAL_Driver/Src/stm32f0xx_ll_usart.c:213:0: information: Skipping configuration 'UART4;UART5;USART1;USART2;USART3;USART6;USART7;USART8;USART5;USE_FULL_LL_DRIVER' since the value of 'USART8' is unknown. Use -D if you want to check it. You can use -U to skip it explicitly. [ConfigurationNotChecked]
  else if (USARTx == USART8)
^
Firmware/mock/nucleof030r8/ir_sensor_mock/Drivers/STM32F0xx_HAL_Driver/Src/stm32f0xx_ll_usart.c:357:0: information: Skipping configuration 'UART4;UART5;USART1;USART2;USART3;USART6;USART7;USART8;USART5;USE_FULL_LL_DRIVER' since the value of 'USART8' is unknown. Use -D if you want to check it. You can use -U to skip it explicitly. [ConfigurationNotChecked]
    else if (USARTx == USART8)
^
Firmware/mock/nucleof030r8/ir_sensor_mock/Drivers/STM32F0xx_HAL_Driver/Src/stm32f0xx_ll_usart.c:183:0: information: Skipping configuration 'UART4;UART5;USART1;USART2;USART3;USART6;USART7;USART8;USART5;USE_FULL_LL_DRIVER' since the value of 'USART5' is unknown. Use -D if you want to check it. You can use -U to skip it explicitly. [ConfigurationNotChecked]
  else if (USARTx == USART5)
^
Firmware/mock/nucleof030r8/ir_sensor_mock/Drivers/STM32F0xx_HAL_Driver/Src/stm32f0xx_ll_usart.c:333:0: information: Skipping configuration 'UART4;UART5;USART1;USART2;USART3;USART6;USART7;USART8;USART5;USE_FULL_LL_DRIVER' since the value of 'USART5' is unknown. Use -D if you want to check it. You can use -U to skip it explicitly. [ConfigurationNotChecked]
    else if (USARTx == USART5)
^
Firmware/mock/nucleof030r8/ir_sensor_mock/Drivers/STM32F0xx_HAL_Driver/Src/stm32f0xx_ll_usart.c:144:0: information: Skipping configuration 'UART4;UART5;USART1;USART2;USART3;USART6;USART7;USART8;USART6;USE_FULL_LL_DRIVER' since the value of 'USART1' is unknown. Use -D if you want to check it. You can use -U to skip it explicitly. [ConfigurationNotChecked]
  if (USARTx == USART1)
^
Firmware/mock/nucleof030r8/ir_sensor_mock/Drivers/STM32F0xx_HAL_Driver/Src/stm32f0xx_ll_usart.c:296:0: information: Skipping configuration 'UART4;UART5;USART1;USART2;USART3;USART6;USART7;USART8;USART6;USE_FULL_LL_DRIVER' since the value of 'USART1' is unknown. Use -D if you want to check it. You can use -U to skip it explicitly. [ConfigurationNotChecked]
    if (USARTx == USART1)
^
Firmware/mock/nucleof030r8/ir_sensor_mock/Drivers/STM32F0xx_HAL_Driver/Src/stm32f0xx_ll_usart.c:153:0: information: Skipping configuration 'UART4;UART5;USART1;USART2;USART3;USART6;USART7;USART8;USART6;USE_FULL_LL_DRIVER' since the value of 'USART2' is unknown. Use -D if you want to check it. You can use -U to skip it explicitly. [ConfigurationNotChecked]
  else if (USARTx == USART2)
^
Firmware/mock/nucleof030r8/ir_sensor_mock/Drivers/STM32F0xx_HAL_Driver/Src/stm32f0xx_ll_usart.c:301:0: information: Skipping configuration 'UART4;UART5;USART1;USART2;USART3;USART6;USART7;USART8;USART6;USE_FULL_LL_DRIVER' since the value of 'USART2' is unknown. Use -D if you want to check it. You can use -U to skip it explicitly. [ConfigurationNotChecked]
    else if (USARTx == USART2)
^
Firmware/mock/nucleof030r8/ir_sensor_mock/Drivers/STM32F0xx_HAL_Driver/Src/stm32f0xx_ll_usart.c:163:0: information: Skipping configuration 'UART4;UART5;USART1;USART2;USART3;USART6;USART7;USART8;USART6;USE_FULL_LL_DRIVER' since the value of 'USART3' is unknown. Use -D if you want to check it. You can use -U to skip it explicitly. [ConfigurationNotChecked]
  else if (USARTx == USART3)
^
Firmware/mock/nucleof030r8/ir_sensor_mock/Drivers/STM32F0xx_HAL_Driver/Src/stm32f0xx_ll_usart.c:313:0: information: Skipping configuration 'UART4;UART5;USART1;USART2;USART3;USART6;USART7;USART8;USART6;USE_FULL_LL_DRIVER' since the value of 'USART3' is unknown. Use -D if you want to check it. You can use -U to skip it explicitly. [ConfigurationNotChecked]
    else if (USARTx == USART3)
^
Firmware/mock/nucleof030r8/ir_sensor_mock/Drivers/STM32F0xx_HAL_Driver/Src/stm32f0xx_ll_usart.c:193:0: information: Skipping configuration 'UART4;UART5;USART1;USART2;USART3;USART6;USART7;USART8;USART6;USE_FULL_LL_DRIVER' since the value of 'USART6' is unknown. Use -D if you want to check it. You can use -U to skip it explicitly. [ConfigurationNotChecked]
  else if (USARTx == USART6)
^
Firmware/mock/nucleof030r8/ir_sensor_mock/Drivers/STM32F0xx_HAL_Driver/Src/stm32f0xx_ll_usart.c:341:0: information: Skipping configuration 'UART4;UART5;USART1;USART2;USART3;USART6;USART7;USART8;USART6;USE_FULL_LL_DRIVER' since the value of 'USART6' is unknown. Use -D if you want to check it. You can use -U to skip it explicitly. [ConfigurationNotChecked]
    else if (USARTx == USART6)
^
Firmware/mock/nucleof030r8/ir_sensor_mock/Drivers/STM32F0xx_HAL_Driver/Src/stm32f0xx_ll_usart.c:203:0: information: Skipping configuration 'UART4;UART5;USART1;USART2;USART3;USART6;USART7;USART8;USART6;USE_FULL_LL_DRIVER' since the value of 'USART7' is unknown. Use -D if you want to check it. You can use -U to skip it explicitly. [ConfigurationNotChecked]
  else if (USARTx == USART7)
^
Firmware/mock/nucleof030r8/ir_sensor_mock/Drivers/STM32F0xx_HAL_Driver/Src/stm32f0xx_ll_usart.c:349:0: information: Skipping configuration 'UART4;UART5;USART1;USART2;USART3;USART6;USART7;USART8;USART6;USE_FULL_LL_DRIVER' since the value of 'USART7' is unknown. Use -D if you want to check it. You can use -U to skip it explicitly. [ConfigurationNotChecked]
    else if (USARTx == USART7)
^
Firmware/mock/nucleof030r8/ir_sensor_mock/Drivers/STM32F0xx_HAL_Driver/Src/stm32f0xx_ll_usart.c:213:0: information: Skipping configuration 'UART4;UART5;USART1;USART2;USART3;USART6;USART7;USART8;USART6;USE_FULL_LL_DRIVER' since the value of 'USART8' is unknown. Use -D if you want to check it. You can use -U to skip it explicitly. [ConfigurationNotChecked]
  else if (USARTx == USART8)
^
Firmware/mock/nucleof030r8/ir_sensor_mock/Drivers/STM32F0xx_HAL_Driver/Src/stm32f0xx_ll_usart.c:357:0: information: Skipping configuration 'UART4;UART5;USART1;USART2;USART3;USART6;USART7;USART8;USART6;USE_FULL_LL_DRIVER' since the value of 'USART8' is unknown. Use -D if you want to check it. You can use -U to skip it explicitly. [ConfigurationNotChecked]
    else if (USARTx == USART8)
^
Firmware/mock/nucleof030r8/ir_sensor_mock/Drivers/STM32F0xx_HAL_Driver/Src/stm32f0xx_ll_usart.c:144:0: information: Skipping configuration 'UART4;UART5;USART1;USART2;USART3;USART6;USART7;USART8;USART7;USE_FULL_LL_DRIVER' since the value of 'USART1' is unknown. Use -D if you want to check it. You can use -U to skip it explicitly. [ConfigurationNotChecked]
  if (USARTx == USART1)
^
Firmware/mock/nucleof030r8/ir_sensor_mock/Drivers/STM32F0xx_HAL_Driver/Src/stm32f0xx_ll_usart.c:296:0: information: Skipping configuration 'UART4;UART5;USART1;USART2;USART3;USART6;USART7;USART8;USART7;USE_FULL_LL_DRIVER' since the value of 'USART1' is unknown. Use -D if you want to check it. You can use -U to skip it explicitly. [ConfigurationNotChecked]
    if (USARTx == USART1)
^
Firmware/mock/nucleof030r8/ir_sensor_mock/Drivers/STM32F0xx_HAL_Driver/Src/stm32f0xx_ll_usart.c:153:0: information: Skipping configuration 'UART4;UART5;USART1;USART2;USART3;USART6;USART7;USART8;USART7;USE_FULL_LL_DRIVER' since the value of 'USART2' is unknown. Use -D if you want to check it. You can use -U to skip it explicitly. [ConfigurationNotChecked]
  else if (USARTx == USART2)
^
Firmware/mock/nucleof030r8/ir_sensor_mock/Drivers/STM32F0xx_HAL_Driver/Src/stm32f0xx_ll_usart.c:301:0: information: Skipping configuration 'UART4;UART5;USART1;USART2;USART3;USART6;USART7;USART8;USART7;USE_FULL_LL_DRIVER' since the value of 'USART2' is unknown. Use -D if you want to check it. You can use -U to skip it explicitly. [ConfigurationNotChecked]
    else if (USARTx == USART2)
^
Firmware/mock/nucleof030r8/ir_sensor_mock/Drivers/STM32F0xx_HAL_Driver/Src/stm32f0xx_ll_usart.c:163:0: information: Skipping configuration 'UART4;UART5;USART1;USART2;USART3;USART6;USART7;USART8;USART7;USE_FULL_LL_DRIVER' since the value of 'USART3' is unknown. Use -D if you want to check it. You can use -U to skip it explicitly. [ConfigurationNotChecked]
  else if (USARTx == USART3)
^
Firmware/mock/nucleof030r8/ir_sensor_mock/Drivers/STM32F0xx_HAL_Driver/Src/stm32f0xx_ll_usart.c:313:0: information: Skipping configuration 'UART4;UART5;USART1;USART2;USART3;USART6;USART7;USART8;USART7;USE_FULL_LL_DRIVER' since the value of 'USART3' is unknown. Use -D if you want to check it. You can use -U to skip it explicitly. [ConfigurationNotChecked]
    else if (USARTx == USART3)
^
Firmware/mock/nucleof030r8/ir_sensor_mock/Drivers/STM32F0xx_HAL_Driver/Src/stm32f0xx_ll_usart.c:193:0: information: Skipping configuration 'UART4;UART5;USART1;USART2;USART3;USART6;USART7;USART8;USART7;USE_FULL_LL_DRIVER' since the value of 'USART6' is unknown. Use -D if you want to check it. You can use -U to skip it explicitly. [ConfigurationNotChecked]
  else if (USARTx == USART6)
^
Firmware/mock/nucleof030r8/ir_sensor_mock/Drivers/STM32F0xx_HAL_Driver/Src/stm32f0xx_ll_usart.c:341:0: information: Skipping configuration 'UART4;UART5;USART1;USART2;USART3;USART6;USART7;USART8;USART7;USE_FULL_LL_DRIVER' since the value of 'USART6' is unknown. Use -D if you want to check it. You can use -U to skip it explicitly. [ConfigurationNotChecked]
    else if (USARTx == USART6)
^
Firmware/mock/nucleof030r8/ir_sensor_mock/Drivers/STM32F0xx_HAL_Driver/Src/stm32f0xx_ll_usart.c:203:0: information: Skipping configuration 'UART4;UART5;USART1;USART2;USART3;USART6;USART7;USART8;USART7;USE_FULL_LL_DRIVER' since the value of 'USART7' is unknown. Use -D if you want to check it. You can use -U to skip it explicitly. [ConfigurationNotChecked]
  else if (USARTx == USART7)
^
Firmware/mock/nucleof030r8/ir_sensor_mock/Drivers/STM32F0xx_HAL_Driver/Src/stm32f0xx_ll_usart.c:349:0: information: Skipping configuration 'UART4;UART5;USART1;USART2;USART3;USART6;USART7;USART8;USART7;USE_FULL_LL_DRIVER' since the value of 'USART7' is unknown. Use -D if you want to check it. You can use -U to skip it explicitly. [ConfigurationNotChecked]
    else if (USARTx == USART7)
^
Firmware/mock/nucleof030r8/ir_sensor_mock/Drivers/STM32F0xx_HAL_Driver/Src/stm32f0xx_ll_usart.c:213:0: information: Skipping configuration 'UART4;UART5;USART1;USART2;USART3;USART6;USART7;USART8;USART7;USE_FULL_LL_DRIVER' since the value of 'USART8' is unknown. Use -D if you want to check it. You can use -U to skip it explicitly. [ConfigurationNotChecked]
  else if (USARTx == USART8)
^
Firmware/mock/nucleof030r8/ir_sensor_mock/Drivers/STM32F0xx_HAL_Driver/Src/stm32f0xx_ll_usart.c:357:0: information: Skipping configuration 'UART4;UART5;USART1;USART2;USART3;USART6;USART7;USART8;USART7;USE_FULL_LL_DRIVER' since the value of 'USART8' is unknown. Use -D if you want to check it. You can use -U to skip it explicitly. [ConfigurationNotChecked]
    else if (USARTx == USART8)
^
Firmware/mock/nucleof030r8/ir_sensor_mock/Drivers/STM32F0xx_HAL_Driver/Src/stm32f0xx_ll_usart.c:144:0: information: Skipping configuration 'UART4;UART5;USART1;USART2;USART3;USART6;USART7;USART8;USART8;USE_FULL_LL_DRIVER' since the value of 'USART1' is unknown. Use -D if you want to check it. You can use -U to skip it explicitly. [ConfigurationNotChecked]
  if (USARTx == USART1)
^
Firmware/mock/nucleof030r8/ir_sensor_mock/Drivers/STM32F0xx_HAL_Driver/Src/stm32f0xx_ll_usart.c:296:0: information: Skipping configuration 'UART4;UART5;USART1;USART2;USART3;USART6;USART7;USART8;USART8;USE_FULL_LL_DRIVER' since the value of 'USART1' is unknown. Use -D if you want to check it. You can use -U to skip it explicitly. [ConfigurationNotChecked]
    if (USARTx == USART1)
^
Firmware/mock/nucleof030r8/ir_sensor_mock/Drivers/STM32F0xx_HAL_Driver/Src/stm32f0xx_ll_usart.c:153:0: information: Skipping configuration 'UART4;UART5;USART1;USART2;USART3;USART6;USART7;USART8;USART8;USE_FULL_LL_DRIVER' since the value of 'USART2' is unknown. Use -D if you want to check it. You can use -U to skip it explicitly. [ConfigurationNotChecked]
  else if (USARTx == USART2)
^
Firmware/mock/nucleof030r8/ir_sensor_mock/Drivers/STM32F0xx_HAL_Driver/Src/stm32f0xx_ll_usart.c:301:0: information: Skipping configuration 'UART4;UART5;USART1;USART2;USART3;USART6;USART7;USART8;USART8;USE_FULL_LL_DRIVER' since the value of 'USART2' is unknown. Use -D if you want to check it. You can use -U to skip it explicitly. [ConfigurationNotChecked]
    else if (USARTx == USART2)
^
Firmware/mock/nucleof030r8/ir_sensor_mock/Drivers/STM32F0xx_HAL_Driver/Src/stm32f0xx_ll_usart.c:163:0: information: Skipping configuration 'UART4;UART5;USART1;USART2;USART3;USART6;USART7;USART8;USART8;USE_FULL_LL_DRIVER' since the value of 'USART3' is unknown. Use -D if you want to check it. You can use -U to skip it explicitly. [ConfigurationNotChecked]
  else if (USARTx == USART3)
^
Firmware/mock/nucleof030r8/ir_sensor_mock/Drivers/STM32F0xx_HAL_Driver/Src/stm32f0xx_ll_usart.c:313:0: information: Skipping configuration 'UART4;UART5;USART1;USART2;USART3;USART6;USART7;USART8;USART8;USE_FULL_LL_DRIVER' since the value of 'USART3' is unknown. Use -D if you want to check it. You can use -U to skip it explicitly. [ConfigurationNotChecked]
    else if (USARTx == USART3)
^
Firmware/mock/nucleof030r8/ir_sensor_mock/Drivers/STM32F0xx_HAL_Driver/Src/stm32f0xx_ll_usart.c:193:0: information: Skipping configuration 'UART4;UART5;USART1;USART2;USART3;USART6;USART7;USART8;USART8;USE_FULL_LL_DRIVER' since the value of 'USART6' is unknown. Use -D if you want to check it. You can use -U to skip it explicitly. [ConfigurationNotChecked]
  else if (USARTx == USART6)
^
Firmware/mock/nucleof030r8/ir_sensor_mock/Drivers/STM32F0xx_HAL_Driver/Src/stm32f0xx_ll_usart.c:341:0: information: Skipping configuration 'UART4;UART5;USART1;USART2;USART3;USART6;USART7;USART8;USART8;USE_FULL_LL_DRIVER' since the value of 'USART6' is unknown. Use -D if you want to check it. You can use -U to skip it explicitly. [ConfigurationNotChecked]
    else if (USARTx == USART6)
^
Firmware/mock/nucleof030r8/ir_sensor_mock/Drivers/STM32F0xx_HAL_Driver/Src/stm32f0xx_ll_usart.c:203:0: information: Skipping configuration 'UART4;UART5;USART1;USART2;USART3;USART6;USART7;USART8;USART8;USE_FULL_LL_DRIVER' since the value of 'USART7' is unknown. Use -D if you want to check it. You can use -U to skip it explicitly. [ConfigurationNotChecked]
  else if (USARTx == USART7)
^
Firmware/mock/nucleof030r8/ir_sensor_mock/Drivers/STM32F0xx_HAL_Driver/Src/stm32f0xx_ll_usart.c:349:0: information: Skipping configuration 'UART4;UART5;USART1;USART2;USART3;USART6;USART7;USART8;USART8;USE_FULL_LL_DRIVER' since the value of 'USART7' is unknown. Use -D if you want to check it. You can use -U to skip it explicitly. [ConfigurationNotChecked]
    else if (USARTx == USART7)
^
Firmware/mock/nucleof030r8/ir_sensor_mock/Drivers/STM32F0xx_HAL_Driver/Src/stm32f0xx_ll_usart.c:213:0: information: Skipping configuration 'UART4;UART5;USART1;USART2;USART3;USART6;USART7;USART8;USART8;USE_FULL_LL_DRIVER' since the value of 'USART8' is unknown. Use -D if you want to check it. You can use -U to skip it explicitly. [ConfigurationNotChecked]
  else if (USARTx == USART8)
^
Firmware/mock/nucleof030r8/ir_sensor_mock/Drivers/STM32F0xx_HAL_Driver/Src/stm32f0xx_ll_usart.c:357:0: information: Skipping configuration 'UART4;UART5;USART1;USART2;USART3;USART6;USART7;USART8;USART8;USE_FULL_LL_DRIVER' since the value of 'USART8' is unknown. Use -D if you want to check it. You can use -U to skip it explicitly. [ConfigurationNotChecked]
    else if (USARTx == USART8)
^
Firmware/mock/nucleof030r8/ir_sensor_mock/Drivers/STM32F0xx_HAL_Driver/Src/stm32f0xx_ll_usart.c:144:0: information: Skipping configuration 'UART4;UART5;USART1;USART2;USART3;USART6;USART7;USART8;USART_7BITS_SUPPORT;USE_FULL_LL_DRIVER' since the value of 'USART1' is unknown. Use -D if you want to check it. You can use -U to skip it explicitly. [ConfigurationNotChecked]
  if (USARTx == USART1)
^
Firmware/mock/nucleof030r8/ir_sensor_mock/Drivers/STM32F0xx_HAL_Driver/Src/stm32f0xx_ll_usart.c:296:0: information: Skipping configuration 'UART4;UART5;USART1;USART2;USART3;USART6;USART7;USART8;USART_7BITS_SUPPORT;USE_FULL_LL_DRIVER' since the value of 'USART1' is unknown. Use -D if you want to check it. You can use -U to skip it explicitly. [ConfigurationNotChecked]
    if (USARTx == USART1)
^
Firmware/mock/nucleof030r8/ir_sensor_mock/Drivers/STM32F0xx_HAL_Driver/Src/stm32f0xx_ll_usart.c:153:0: information: Skipping configuration 'UART4;UART5;USART1;USART2;USART3;USART6;USART7;USART8;USART_7BITS_SUPPORT;USE_FULL_LL_DRIVER' since the value of 'USART2' is unknown. Use -D if you want to check it. You can use -U to skip it explicitly. [ConfigurationNotChecked]
  else if (USARTx == USART2)
^
Firmware/mock/nucleof030r8/ir_sensor_mock/Drivers/STM32F0xx_HAL_Driver/Src/stm32f0xx_ll_usart.c:301:0: information: Skipping configuration 'UART4;UART5;USART1;USART2;USART3;USART6;USART7;USART8;USART_7BITS_SUPPORT;USE_FULL_LL_DRIVER' since the value of 'USART2' is unknown. Use -D if you want to check it. You can use -U to skip it explicitly. [ConfigurationNotChecked]
    else if (USARTx == USART2)
^
Firmware/mock/nucleof030r8/ir_sensor_mock/Drivers/STM32F0xx_HAL_Driver/Src/stm32f0xx_ll_usart.c:163:0: information: Skipping configuration 'UART4;UART5;USART1;USART2;USART3;USART6;USART7;USART8;USART_7BITS_SUPPORT;USE_FULL_LL_DRIVER' since the value of 'USART3' is unknown. Use -D if you want to check it. You can use -U to skip it explicitly. [ConfigurationNotChecked]
  else if (USARTx == USART3)
^
Firmware/mock/nucleof030r8/ir_sensor_mock/Drivers/STM32F0xx_HAL_Driver/Src/stm32f0xx_ll_usart.c:313:0: information: Skipping configuration 'UART4;UART5;USART1;USART2;USART3;USART6;USART7;USART8;USART_7BITS_SUPPORT;USE_FULL_LL_DRIVER' since the value of 'USART3' is unknown. Use -D if you want to check it. You can use -U to skip it explicitly. [ConfigurationNotChecked]
    else if (USARTx == USART3)
^
Firmware/mock/nucleof030r8/ir_sensor_mock/Drivers/STM32F0xx_HAL_Driver/Src/stm32f0xx_ll_usart.c:193:0: information: Skipping configuration 'UART4;UART5;USART1;USART2;USART3;USART6;USART7;USART8;USART_7BITS_SUPPORT;USE_FULL_LL_DRIVER' since the value of 'USART6' is unknown. Use -D if you want to check it. You can use -U to skip it explicitly. [ConfigurationNotChecked]
  else if (USARTx == USART6)
^
Firmware/mock/nucleof030r8/ir_sensor_mock/Drivers/STM32F0xx_HAL_Driver/Src/stm32f0xx_ll_usart.c:341:0: information: Skipping configuration 'UART4;UART5;USART1;USART2;USART3;USART6;USART7;USART8;USART_7BITS_SUPPORT;USE_FULL_LL_DRIVER' since the value of 'USART6' is unknown. Use -D if you want to check it. You can use -U to skip it explicitly. [ConfigurationNotChecked]
    else if (USARTx == USART6)
^
Firmware/mock/nucleof030r8/ir_sensor_mock/Drivers/STM32F0xx_HAL_Driver/Src/stm32f0xx_ll_usart.c:203:0: information: Skipping configuration 'UART4;UART5;USART1;USART2;USART3;USART6;USART7;USART8;USART_7BITS_SUPPORT;USE_FULL_LL_DRIVER' since the value of 'USART7' is unknown. Use -D if you want to check it. You can use -U to skip it explicitly. [ConfigurationNotChecked]
  else if (USARTx == USART7)
^
Firmware/mock/nucleof030r8/ir_sensor_mock/Drivers/STM32F0xx_HAL_Driver/Src/stm32f0xx_ll_usart.c:349:0: information: Skipping configuration 'UART4;UART5;USART1;USART2;USART3;USART6;USART7;USART8;USART_7BITS_SUPPORT;USE_FULL_LL_DRIVER' since the value of 'USART7' is unknown. Use -D if you want to check it. You can use -U to skip it explicitly. [ConfigurationNotChecked]
    else if (USARTx == USART7)
^
Firmware/mock/nucleof030r8/ir_sensor_mock/Drivers/STM32F0xx_HAL_Driver/Src/stm32f0xx_ll_usart.c:213:0: information: Skipping configuration 'UART4;UART5;USART1;USART2;USART3;USART6;USART7;USART8;USART_7BITS_SUPPORT;USE_FULL_LL_DRIVER' since the value of 'USART8' is unknown. Use -D if you want to check it. You can use -U to skip it explicitly. [ConfigurationNotChecked]
  else if (USARTx == USART8)
^
Firmware/mock/nucleof030r8/ir_sensor_mock/Drivers/STM32F0xx_HAL_Driver/Src/stm32f0xx_ll_usart.c:357:0: information: Skipping configuration 'UART4;UART5;USART1;USART2;USART3;USART6;USART7;USART8;USART_7BITS_SUPPORT;USE_FULL_LL_DRIVER' since the value of 'USART8' is unknown. Use -D if you want to check it. You can use -U to skip it explicitly. [ConfigurationNotChecked]
    else if (USARTx == USART8)
^
Firmware/mock/nucleof030r8/ir_sensor_mock/Drivers/STM32F0xx_HAL_Driver/Src/stm32f0xx_ll_usb.c:164:14: style: Variable 'USBx->CNTR' is reassigned a value before the old one has been used. [redundantAssignment]
  USBx->CNTR = 0U;
             ^
Firmware/mock/nucleof030r8/ir_sensor_mock/Drivers/STM32F0xx_HAL_Driver/Src/stm32f0xx_ll_usb.c:161:14: note: USBx->CNTR is assigned
  USBx->CNTR = (uint16_t)USB_CNTR_FRES;
             ^
Firmware/mock/nucleof030r8/ir_sensor_mock/Drivers/STM32F0xx_HAL_Driver/Src/stm32f0xx_ll_usb.c:164:14: note: USBx->CNTR is overwritten
  USBx->CNTR = 0U;
             ^
Firmware/mock/nucleof030r8/ir_sensor_mock/Drivers/STM32F0xx_HAL_Driver/Src/stm32f0xx_ll_usb.c:741:14: style: Variable 'USBx->CNTR' is reassigned a value before the old one has been used. [redundantAssignment]
  USBx->CNTR = (uint16_t)(USB_CNTR_FRES | USB_CNTR_PDWN);
             ^
Firmware/mock/nucleof030r8/ir_sensor_mock/Drivers/STM32F0xx_HAL_Driver/Src/stm32f0xx_ll_usb.c:735:14: note: USBx->CNTR is assigned
  USBx->CNTR = (uint16_t)USB_CNTR_FRES;
             ^
Firmware/mock/nucleof030r8/ir_sensor_mock/Drivers/STM32F0xx_HAL_Driver/Src/stm32f0xx_ll_usb.c:741:14: note: USBx->CNTR is overwritten
  USBx->CNTR = (uint16_t)(USB_CNTR_FRES | USB_CNTR_PDWN);
             ^
Firmware/mock/nucleof030r8/ir_sensor_mock/Drivers/STM32F0xx_HAL_Driver/Src/stm32f0xx_ll_utils.c:299:20: style: Variable 'pllfreq' is assigned a value that is never used. [unreadVariable]
  uint32_t pllfreq = 0U;
                   ^
Firmware/mock/nucleof030r8/ir_sensor_mock/Drivers/STM32F0xx_HAL_Driver/Src/stm32f0xx_ll_utils.c:424:20: style: Variable 'pllfreq' is assigned a value that is never used. [unreadVariable]
  uint32_t pllfreq = 0U;
                   ^
Firmware/mock/nucleof030r8/ir_sensor_mock/Drivers/STM32F0xx_HAL_Driver/Src/stm32f0xx_ll_utils.c:230:12: style: The scope of the variable 'timeout' can be reduced. [variableScope]
  uint32_t timeout;
           ^
Firmware/mock/nucleof030r8/ir_sensor_mock/Drivers/STM32F0xx_HAL_Driver/Src/stm32f0xx_ll_utils.c:231:12: style: The scope of the variable 'getlatency' can be reduced. [variableScope]
  uint32_t getlatency;
           ^
Firmware/mock/nucleof030r8/ir_sensor_mock/Drivers/STM32F0xx_HAL_Driver/Src/stm32f0xx_ll_utils.c:232:12: style: The scope of the variable 'latency' can be reduced. [variableScope]
  uint32_t latency;
           ^
Firmware/mock/nucleof030r8/ir_sensor_mock/Drivers/STM32F0xx_HAL_Driver/Src/stm32f0xx_ll_utils.c:363:12: style: The scope of the variable 'pllfreq' can be reduced. [variableScope]
  uint32_t pllfreq = 0U;
           ^
Firmware/mock/nucleof030r8/ir_sensor_mock/Drivers/STM32F0xx_HAL_Driver/Src/stm32f0xx_ll_utils.c:363:20: style: Variable 'pllfreq' is assigned a value that is never used. [unreadVariable]
  uint32_t pllfreq = 0U;
                   ^
Firmware/mock/nucleof030r8/ir_sensor_mock/Core/Src/stm32f0xx_it.c:152:0: style: The function 'DMA1_Channel1_IRQHandler' is never used. [unusedFunction]

^
Firmware/mock/nucleof030r8/ir_sensor_mock/Core/Src/stm32f0xx_it.c:166:0: style: The function 'DMA1_Channel2_3_IRQHandler' is never used. [unusedFunction]

^
Firmware/mock/nucleof030r8/ir_sensor_mock/Core/Src/stm32f0xx_it.c:180:0: style: The function 'DMA1_Channel4_5_IRQHandler' is never used. [unusedFunction]

^
Firmware/mock/nucleof030r8/ir_sensor_mock/Drivers/STM32F0xx_HAL_Driver/Src/stm32f0xx_hal_adc_ex.c:95:0: style: The function 'HAL_ADCEx_Calibration_Start' is never used. [unusedFunction]

^
Firmware/mock/nucleof030r8/ir_sensor_mock/Drivers/STM32F0xx_HAL_Driver/Src/stm32f0xx_hal_adc.c:2027:0: style: The function 'HAL_ADC_AnalogWDGConfig' is never used. [unusedFunction]

^
Firmware/mock/nucleof030r8/ir_sensor_mock/Drivers/STM32F0xx_HAL_Driver/Src/stm32f0xx_hal_adc.c:639:0: style: The function 'HAL_ADC_DeInit' is never used. [unusedFunction]

^
Firmware/mock/nucleof030r8/ir_sensor_mock/Drivers/STM32F0xx_HAL_Driver/Src/stm32f0xx_hal_adc.c:2163:0: style: The function 'HAL_ADC_GetError' is never used. [unusedFunction]

^
Firmware/mock/nucleof030r8/ir_sensor_mock/Drivers/STM32F0xx_HAL_Driver/Src/stm32f0xx_hal_adc.c:2149:0: style: The function 'HAL_ADC_GetState' is never used. [unusedFunction]

^
Firmware/mock/nucleof030r8/ir_sensor_mock/Drivers/STM32F0xx_HAL_Driver/Src/stm32f0xx_hal_adc.c:1649:0: style: The function 'HAL_ADC_GetValue' is never used. [unusedFunction]

^
Firmware/mock/nucleof030r8/ir_sensor_mock/Drivers/STM32F0xx_HAL_Driver/Src/stm32f0xx_hal_adc.c:1666:0: style: The function 'HAL_ADC_IRQHandler' is never used. [unusedFunction]

^
Firmware/mock/nucleof030r8/ir_sensor_mock/Drivers/STM32F0xx_HAL_Driver/Src/stm32f0xx_hal_adc.c:1137:0: style: The function 'HAL_ADC_PollForConversion' is never used. [unusedFunction]

^
Firmware/mock/nucleof030r8/ir_sensor_mock/Drivers/STM32F0xx_HAL_Driver/Src/stm32f0xx_hal_adc.c:1261:0: style: The function 'HAL_ADC_PollForEvent' is never used. [unusedFunction]

^
Firmware/mock/nucleof030r8/ir_sensor_mock/Drivers/STM32F0xx_HAL_Driver/Src/stm32f0xx_hal_adc.c:1018:0: style: The function 'HAL_ADC_Start' is never used. [unusedFunction]

^
Firmware/mock/nucleof030r8/ir_sensor_mock/Drivers/STM32F0xx_HAL_Driver/Src/stm32f0xx_hal_adc.c:1341:0: style: The function 'HAL_ADC_Start_IT' is never used. [unusedFunction]

^
Firmware/mock/nucleof030r8/ir_sensor_mock/Drivers/STM32F0xx_HAL_Driver/Src/stm32f0xx_hal_adc.c:1083:0: style: The function 'HAL_ADC_Stop' is never used. [unusedFunction]

^
Firmware/mock/nucleof030r8/ir_sensor_mock/Drivers/STM32F0xx_HAL_Driver/Src/stm32f0xx_hal_adc.c:1564:0: style: The function 'HAL_ADC_Stop_DMA' is never used. [unusedFunction]

^
Firmware/mock/nucleof030r8/ir_sensor_mock/Drivers/STM32F0xx_HAL_Driver/Src/stm32f0xx_hal_adc.c:1422:0: style: The function 'HAL_ADC_Stop_IT' is never used. [unusedFunction]

^
Firmware/mock/nucleof030r8/ir_sensor_mock/Drivers/STM32F0xx_HAL_Driver/Src/stm32f0xx_hal_can.c:1306:0: style: The function 'HAL_CAN_AbortTxRequest' is never used. [unusedFunction]

^
Firmware/mock/nucleof030r8/ir_sensor_mock/Drivers/STM32F0xx_HAL_Driver/Src/stm32f0xx_hal_can.c:1629:0: style: The function 'HAL_CAN_ActivateNotification' is never used. [unusedFunction]

^
Firmware/mock/nucleof030r8/ir_sensor_mock/Drivers/STM32F0xx_HAL_Driver/Src/stm32f0xx_hal_can.c:1206:0: style: The function 'HAL_CAN_AddTxMessage' is never used. [unusedFunction]

^
Firmware/mock/nucleof030r8/ir_sensor_mock/Drivers/STM32F0xx_HAL_Driver/Src/stm32f0xx_hal_can.c:840:0: style: The function 'HAL_CAN_ConfigFilter' is never used. [unusedFunction]

^
Firmware/mock/nucleof030r8/ir_sensor_mock/Drivers/STM32F0xx_HAL_Driver/Src/stm32f0xx_hal_can.c:460:0: style: The function 'HAL_CAN_DeInit' is never used. [unusedFunction]

^
Firmware/mock/nucleof030r8/ir_sensor_mock/Drivers/STM32F0xx_HAL_Driver/Src/stm32f0xx_hal_can.c:1662:0: style: The function 'HAL_CAN_DeactivateNotification' is never used. [unusedFunction]

^
Firmware/mock/nucleof030r8/ir_sensor_mock/Drivers/STM32F0xx_HAL_Driver/Src/stm32f0xx_hal_can.c:2379:0: style: The function 'HAL_CAN_GetError' is never used. [unusedFunction]

^
Firmware/mock/nucleof030r8/ir_sensor_mock/Drivers/STM32F0xx_HAL_Driver/Src/stm32f0xx_hal_can.c:1576:0: style: The function 'HAL_CAN_GetRxFifoFillLevel' is never used. [unusedFunction]

^
Firmware/mock/nucleof030r8/ir_sensor_mock/Drivers/STM32F0xx_HAL_Driver/Src/stm32f0xx_hal_can.c:1476:0: style: The function 'HAL_CAN_GetRxMessage' is never used. [unusedFunction]

^
Firmware/mock/nucleof030r8/ir_sensor_mock/Drivers/STM32F0xx_HAL_Driver/Src/stm32f0xx_hal_can.c:2344:0: style: The function 'HAL_CAN_GetState' is never used. [unusedFunction]

^
Firmware/mock/nucleof030r8/ir_sensor_mock/Drivers/STM32F0xx_HAL_Driver/Src/stm32f0xx_hal_can.c:1355:0: style: The function 'HAL_CAN_GetTxMailboxesFreeLevel' is never used. [unusedFunction]

^
Firmware/mock/nucleof030r8/ir_sensor_mock/Drivers/STM32F0xx_HAL_Driver/Src/stm32f0xx_hal_can.c:1430:0: style: The function 'HAL_CAN_GetTxTimestamp' is never used. [unusedFunction]

^
Firmware/mock/nucleof030r8/ir_sensor_mock/Drivers/STM32F0xx_HAL_Driver/Src/stm32f0xx_hal_can.c:1693:0: style: The function 'HAL_CAN_IRQHandler' is never used. [unusedFunction]

^
Firmware/mock/nucleof030r8/ir_sensor_mock/Drivers/STM32F0xx_HAL_Driver/Src/stm32f0xx_hal_can.c:275:0: style: The function 'HAL_CAN_Init' is never used. [unusedFunction]

^
Firmware/mock/nucleof030r8/ir_sensor_mock/Drivers/STM32F0xx_HAL_Driver/Src/stm32f0xx_hal_can.c:1175:0: style: The function 'HAL_CAN_IsSleepActive' is never used. [unusedFunction]

^
Firmware/mock/nucleof030r8/ir_sensor_mock/Drivers/STM32F0xx_HAL_Driver/Src/stm32f0xx_hal_can.c:1398:0: style: The function 'HAL_CAN_IsTxMessagePending' is never used. [unusedFunction]

^
Firmware/mock/nucleof030r8/ir_sensor_mock/Drivers/STM32F0xx_HAL_Driver/Src/stm32f0xx_hal_can.c:559:0: style: The function 'HAL_CAN_RegisterCallback' is never used. [unusedFunction]

^
Firmware/mock/nucleof030r8/ir_sensor_mock/Drivers/STM32F0xx_HAL_Driver/Src/stm32f0xx_hal_can.c:1097:0: style: The function 'HAL_CAN_RequestSleep' is never used. [unusedFunction]

^
Firmware/mock/nucleof030r8/ir_sensor_mock/Drivers/STM32F0xx_HAL_Driver/Src/stm32f0xx_hal_can.c:2391:0: style: The function 'HAL_CAN_ResetError' is never used. [unusedFunction]

^
Firmware/mock/nucleof030r8/ir_sensor_mock/Drivers/STM32F0xx_HAL_Driver/Src/stm32f0xx_hal_can.c:990:0: style: The function 'HAL_CAN_Start' is never used. [unusedFunction]

^
Firmware/mock/nucleof030r8/ir_sensor_mock/Drivers/STM32F0xx_HAL_Driver/Src/stm32f0xx_hal_can.c:702:0: style: The function 'HAL_CAN_UnRegisterCallback' is never used. [unusedFunction]

^
Firmware/mock/nucleof030r8/ir_sensor_mock/Drivers/STM32F0xx_HAL_Driver/Src/stm32f0xx_hal_can.c:1128:0: style: The function 'HAL_CAN_WakeUp' is never used. [unusedFunction]

^
Firmware/mock/nucleof030r8/ir_sensor_mock/Drivers/STM32F0xx_HAL_Driver/Src/stm32f0xx_hal_cec.c:765:0: style: The function 'HAL_CEC_ChangeRxBuffer' is never used. [unusedFunction]

^
Firmware/mock/nucleof030r8/ir_sensor_mock/Drivers/STM32F0xx_HAL_Driver/Src/stm32f0xx_hal_cec.c:274:0: style: The function 'HAL_CEC_DeInit' is never used. [unusedFunction]

^
Firmware/mock/nucleof030r8/ir_sensor_mock/Drivers/STM32F0xx_HAL_Driver/Src/stm32f0xx_hal_cec.c:977:0: style: The function 'HAL_CEC_GetError' is never used. [unusedFunction]

^
Firmware/mock/nucleof030r8/ir_sensor_mock/Drivers/STM32F0xx_HAL_Driver/Src/stm32f0xx_hal_cec.c:753:0: style: The function 'HAL_CEC_GetLastReceivedFrameSize' is never used. [unusedFunction]

^
Firmware/mock/nucleof030r8/ir_sensor_mock/Drivers/STM32F0xx_HAL_Driver/Src/stm32f0xx_hal_cec.c:961:0: style: The function 'HAL_CEC_GetState' is never used. [unusedFunction]

^
Firmware/mock/nucleof030r8/ir_sensor_mock/Drivers/STM32F0xx_HAL_Driver/Src/stm32f0xx_hal_cec.c:775:0: style: The function 'HAL_CEC_IRQHandler' is never used. [unusedFunction]

^
Firmware/mock/nucleof030r8/ir_sensor_mock/Drivers/STM32F0xx_HAL_Driver/Src/stm32f0xx_hal_cec.c:181:0: style: The function 'HAL_CEC_Init' is never used. [unusedFunction]

^
Firmware/mock/nucleof030r8/ir_sensor_mock/Drivers/STM32F0xx_HAL_Driver/Src/stm32f0xx_hal_cec.c:341:0: style: The function 'HAL_CEC_SetDeviceAddress' is never used. [unusedFunction]

^
Firmware/mock/nucleof030r8/ir_sensor_mock/Drivers/STM32F0xx_HAL_Driver/Src/stm32f0xx_hal_cec.c:697:0: style: The function 'HAL_CEC_Transmit_IT' is never used. [unusedFunction]

^
Firmware/mock/nucleof030r8/ir_sensor_mock/Drivers/STM32F0xx_HAL_Driver/Src/stm32f0xx_hal_crc_ex.c:170:0: style: The function 'HAL_CRCEx_Input_Data_Reverse' is never used. [unusedFunction]

^
Firmware/mock/nucleof030r8/ir_sensor_mock/Drivers/STM32F0xx_HAL_Driver/Src/stm32f0xx_hal_crc_ex.c:196:0: style: The function 'HAL_CRCEx_Output_Data_Reverse' is never used. [unusedFunction]

^
Firmware/mock/nucleof030r8/ir_sensor_mock/Drivers/STM32F0xx_HAL_Driver/Src/stm32f0xx_hal_crc.c:289:0: style: The function 'HAL_CRC_Accumulate' is never used. [unusedFunction]

^
Firmware/mock/nucleof030r8/ir_sensor_mock/Drivers/STM32F0xx_HAL_Driver/Src/stm32f0xx_hal_crc.c:341:0: style: The function 'HAL_CRC_Calculate' is never used. [unusedFunction]

^
Firmware/mock/nucleof030r8/ir_sensor_mock/Drivers/STM32F0xx_HAL_Driver/Src/stm32f0xx_hal_crc.c:181:0: style: The function 'HAL_CRC_DeInit' is never used. [unusedFunction]

^
Firmware/mock/nucleof030r8/ir_sensor_mock/Drivers/STM32F0xx_HAL_Driver/Src/stm32f0xx_hal_crc.c:408:0: style: The function 'HAL_CRC_GetState' is never used. [unusedFunction]

^
Firmware/mock/nucleof030r8/ir_sensor_mock/Drivers/STM32F0xx_HAL_Driver/Src/stm32f0xx_hal_crc.c:103:0: style: The function 'HAL_CRC_Init' is never used. [unusedFunction]

^
Firmware/mock/nucleof030r8/ir_sensor_mock/Drivers/STM32F0xx_HAL_Driver/Src/stm32f0xx_hal_dac_ex.c:895:0: style: The function 'HAL_DACEx_DualGetValue' is never used. [unusedFunction]

^
Firmware/mock/nucleof030r8/ir_sensor_mock/Drivers/STM32F0xx_HAL_Driver/Src/stm32f0xx_hal_dac_ex.c:1045:0: style: The function 'HAL_DACEx_DualSetValue' is never used. [unusedFunction]

^
Firmware/mock/nucleof030r8/ir_sensor_mock/Drivers/STM32F0xx_HAL_Driver/Src/stm32f0xx_hal_dac_ex.c:981:0: style: The function 'HAL_DACEx_NoiseWaveGenerate' is never used. [unusedFunction]

^
Firmware/mock/nucleof030r8/ir_sensor_mock/Drivers/STM32F0xx_HAL_Driver/Src/stm32f0xx_hal_dac_ex.c:933:0: style: The function 'HAL_DACEx_TriangleWaveGenerate' is never used. [unusedFunction]

^
Firmware/mock/nucleof030r8/ir_sensor_mock/Drivers/STM32F0xx_HAL_Driver/Src/stm32f0xx_hal_dac.c:771:0: style: The function 'HAL_DAC_ConfigChannel' is never used. [unusedFunction]

^
Firmware/mock/nucleof030r8/ir_sensor_mock/Drivers/STM32F0xx_HAL_Driver/Src/stm32f0xx_hal_dac.c:360:0: style: The function 'HAL_DAC_DeInit' is never used. [unusedFunction]

^
Firmware/mock/nucleof030r8/ir_sensor_mock/Drivers/STM32F0xx_HAL_Driver/Src/stm32f0xx_hal_dac.c:824:0: style: The function 'HAL_DAC_GetError' is never used. [unusedFunction]

^
Firmware/mock/nucleof030r8/ir_sensor_mock/Drivers/STM32F0xx_HAL_Driver/Src/stm32f0xx_hal_dac.c:811:0: style: The function 'HAL_DAC_GetState' is never used. [unusedFunction]

^
Firmware/mock/nucleof030r8/ir_sensor_mock/Drivers/STM32F0xx_HAL_Driver/Src/stm32f0xx_hal_dac.c:747:0: style: The function 'HAL_DAC_GetValue' is never used. [unusedFunction]

^
Firmware/mock/nucleof030r8/ir_sensor_mock/Drivers/STM32F0xx_HAL_Driver/Src/stm32f0xx_hal_dac.c:603:0: style: The function 'HAL_DAC_IRQHandler' is never used. [unusedFunction]

^
Firmware/mock/nucleof030r8/ir_sensor_mock/Drivers/STM32F0xx_HAL_Driver/Src/stm32f0xx_hal_dac.c:299:0: style: The function 'HAL_DAC_Init' is never used. [unusedFunction]

^
Firmware/mock/nucleof030r8/ir_sensor_mock/Drivers/STM32F0xx_HAL_Driver/Src/stm32f0xx_hal_dac.c:628:0: style: The function 'HAL_DAC_SetValue' is never used. [unusedFunction]

^
Firmware/mock/nucleof030r8/ir_sensor_mock/Drivers/STM32F0xx_HAL_Driver/Src/stm32f0xx_hal_dac.c:464:0: style: The function 'HAL_DAC_Start' is never used. [unusedFunction]

^
Firmware/mock/nucleof030r8/ir_sensor_mock/Drivers/STM32F0xx_HAL_Driver/Src/stm32f0xx_hal_dac.c:519:0: style: The function 'HAL_DAC_Start_DMA' is never used. [unusedFunction]

^
Firmware/mock/nucleof030r8/ir_sensor_mock/Drivers/STM32F0xx_HAL_Driver/Src/stm32f0xx_hal_dac.c:487:0: style: The function 'HAL_DAC_Stop' is never used. [unusedFunction]

^
Firmware/mock/nucleof030r8/ir_sensor_mock/Drivers/STM32F0xx_HAL_Driver/Src/stm32f0xx_hal_dac.c:545:0: style: The function 'HAL_DAC_Stop_DMA' is never used. [unusedFunction]

^
Firmware/mock/nucleof030r8/ir_sensor_mock/Drivers/STM32F0xx_HAL_Driver/Src/stm32f0xx_hal.c:493:0: style: The function 'HAL_DBGMCU_DisableDBGStandbyMode' is never used. [unusedFunction]

^
Firmware/mock/nucleof030r8/ir_sensor_mock/Drivers/STM32F0xx_HAL_Driver/Src/stm32f0xx_hal.c:475:0: style: The function 'HAL_DBGMCU_DisableDBGStopMode' is never used. [unusedFunction]

^
Firmware/mock/nucleof030r8/ir_sensor_mock/Drivers/STM32F0xx_HAL_Driver/Src/stm32f0xx_hal.c:484:0: style: The function 'HAL_DBGMCU_EnableDBGStandbyMode' is never used. [unusedFunction]

^
Firmware/mock/nucleof030r8/ir_sensor_mock/Drivers/STM32F0xx_HAL_Driver/Src/stm32f0xx_hal.c:466:0: style: The function 'HAL_DBGMCU_EnableDBGStopMode' is never used. [unusedFunction]

^
Firmware/mock/nucleof030r8/ir_sensor_mock/Drivers/STM32F0xx_HAL_Driver/Src/stm32f0xx_hal_dma.c:468:0: style: The function 'HAL_DMA_PollForTransfer' is never used. [unusedFunction]

^
Firmware/mock/nucleof030r8/ir_sensor_mock/Drivers/STM32F0xx_HAL_Driver/Src/stm32f0xx_hal_dma.c:661:0: style: The function 'HAL_DMA_RegisterCallback' is never used. [unusedFunction]

^
Firmware/mock/nucleof030r8/ir_sensor_mock/Drivers/STM32F0xx_HAL_Driver/Src/stm32f0xx_hal_dma.c:281:0: style: The function 'HAL_DMA_Start' is never used. [unusedFunction]

^
Firmware/mock/nucleof030r8/ir_sensor_mock/Drivers/STM32F0xx_HAL_Driver/Src/stm32f0xx_hal_dma.c:712:0: style: The function 'HAL_DMA_UnRegisterCallback' is never used. [unusedFunction]

^
Firmware/mock/nucleof030r8/ir_sensor_mock/Drivers/STM32F0xx_HAL_Driver/Src/stm32f0xx_hal.c:165:0: style: The function 'HAL_DeInit' is never used. [unusedFunction]

^
Firmware/mock/nucleof030r8/ir_sensor_mock/Drivers/STM32F0xx_HAL_Driver/Src/stm32f0xx_hal_exti.c:316:0: style: The function 'HAL_EXTI_ClearConfigLine' is never used. [unusedFunction]

^
Firmware/mock/nucleof030r8/ir_sensor_mock/Drivers/STM32F0xx_HAL_Driver/Src/stm32f0xx_hal_exti.c:495:0: style: The function 'HAL_EXTI_ClearPending' is never used. [unusedFunction]

^
Firmware/mock/nucleof030r8/ir_sensor_mock/Drivers/STM32F0xx_HAL_Driver/Src/stm32f0xx_hal_exti.c:516:0: style: The function 'HAL_EXTI_GenerateSWI' is never used. [unusedFunction]

^
Firmware/mock/nucleof030r8/ir_sensor_mock/Drivers/STM32F0xx_HAL_Driver/Src/stm32f0xx_hal_exti.c:237:0: style: The function 'HAL_EXTI_GetConfigLine' is never used. [unusedFunction]

^
Firmware/mock/nucleof030r8/ir_sensor_mock/Drivers/STM32F0xx_HAL_Driver/Src/stm32f0xx_hal_exti.c:394:0: style: The function 'HAL_EXTI_GetHandle' is never used. [unusedFunction]

^
Firmware/mock/nucleof030r8/ir_sensor_mock/Drivers/STM32F0xx_HAL_Driver/Src/stm32f0xx_hal_exti.c:466:0: style: The function 'HAL_EXTI_GetPending' is never used. [unusedFunction]

^
Firmware/mock/nucleof030r8/ir_sensor_mock/Drivers/STM32F0xx_HAL_Driver/Src/stm32f0xx_hal_exti.c:434:0: style: The function 'HAL_EXTI_IRQHandler' is never used. [unusedFunction]

^
Firmware/mock/nucleof030r8/ir_sensor_mock/Drivers/STM32F0xx_HAL_Driver/Src/stm32f0xx_hal_exti.c:369:0: style: The function 'HAL_EXTI_RegisterCallback' is never used. [unusedFunction]

^
Firmware/mock/nucleof030r8/ir_sensor_mock/Drivers/STM32F0xx_HAL_Driver/Src/stm32f0xx_hal_exti.c:142:0: style: The function 'HAL_EXTI_SetConfigLine' is never used. [unusedFunction]

^
Firmware/mock/nucleof030r8/ir_sensor_mock/Drivers/STM32F0xx_HAL_Driver/Src/stm32f0xx_hal_flash_ex.c:157:0: style: The function 'HAL_FLASHEx_Erase' is never used. [unusedFunction]

^
Firmware/mock/nucleof030r8/ir_sensor_mock/Drivers/STM32F0xx_HAL_Driver/Src/stm32f0xx_hal_flash_ex.c:238:0: style: The function 'HAL_FLASHEx_Erase_IT' is never used. [unusedFunction]

^
Firmware/mock/nucleof030r8/ir_sensor_mock/Drivers/STM32F0xx_HAL_Driver/Src/stm32f0xx_hal_flash_ex.c:441:0: style: The function 'HAL_FLASHEx_OBGetConfig' is never used. [unusedFunction]

^
Firmware/mock/nucleof030r8/ir_sensor_mock/Drivers/STM32F0xx_HAL_Driver/Src/stm32f0xx_hal_flash_ex.c:463:0: style: The function 'HAL_FLASHEx_OBGetUserData' is never used. [unusedFunction]

^
Firmware/mock/nucleof030r8/ir_sensor_mock/Drivers/STM32F0xx_HAL_Driver/Src/stm32f0xx_hal_flash_ex.c:360:0: style: The function 'HAL_FLASHEx_OBProgram' is never used. [unusedFunction]

^
Firmware/mock/nucleof030r8/ir_sensor_mock/Drivers/STM32F0xx_HAL_Driver/Src/stm32f0xx_hal_flash.c:578:0: style: The function 'HAL_FLASH_GetError' is never used. [unusedFunction]

^
Firmware/mock/nucleof030r8/ir_sensor_mock/Drivers/STM32F0xx_HAL_Driver/Src/stm32f0xx_hal_flash.c:283:0: style: The function 'HAL_FLASH_IRQHandler' is never used. [unusedFunction]

^
Firmware/mock/nucleof030r8/ir_sensor_mock/Drivers/STM32F0xx_HAL_Driver/Src/stm32f0xx_hal_flash.c:501:0: style: The function 'HAL_FLASH_Lock' is never used. [unusedFunction]

^
Firmware/mock/nucleof030r8/ir_sensor_mock/Drivers/STM32F0xx_HAL_Driver/Src/stm32f0xx_hal_flash.c:546:0: style: The function 'HAL_FLASH_OB_Launch' is never used. [unusedFunction]

^
Firmware/mock/nucleof030r8/ir_sensor_mock/Drivers/STM32F0xx_HAL_Driver/Src/stm32f0xx_hal_flash.c:533:0: style: The function 'HAL_FLASH_OB_Lock' is never used. [unusedFunction]

^
Firmware/mock/nucleof030r8/ir_sensor_mock/Drivers/STM32F0xx_HAL_Driver/Src/stm32f0xx_hal_flash.c:513:0: style: The function 'HAL_FLASH_OB_Unlock' is never used. [unusedFunction]

^
Firmware/mock/nucleof030r8/ir_sensor_mock/Drivers/STM32F0xx_HAL_Driver/Src/stm32f0xx_hal_flash.c:165:0: style: The function 'HAL_FLASH_Program' is never used. [unusedFunction]

^
Firmware/mock/nucleof030r8/ir_sensor_mock/Drivers/STM32F0xx_HAL_Driver/Src/stm32f0xx_hal_flash.c:237:0: style: The function 'HAL_FLASH_Program_IT' is never used. [unusedFunction]

^
Firmware/mock/nucleof030r8/ir_sensor_mock/Drivers/STM32F0xx_HAL_Driver/Src/stm32f0xx_hal_flash.c:477:0: style: The function 'HAL_FLASH_Unlock' is never used. [unusedFunction]

^
Firmware/mock/nucleof030r8/ir_sensor_mock/Drivers/STM32F0xx_HAL_Driver/Src/stm32f0xx_hal_gpio.c:497:0: style: The function 'HAL_GPIO_EXTI_IRQHandler' is never used. [unusedFunction]

^
Firmware/mock/nucleof030r8/ir_sensor_mock/Drivers/STM32F0xx_HAL_Driver/Src/stm32f0xx_hal_gpio.c:462:0: style: The function 'HAL_GPIO_LockPin' is never used. [unusedFunction]

^
Firmware/mock/nucleof030r8/ir_sensor_mock/Drivers/STM32F0xx_HAL_Driver/Src/stm32f0xx_hal_gpio.c:382:0: style: The function 'HAL_GPIO_ReadPin' is never used. [unusedFunction]

^
Firmware/mock/nucleof030r8/ir_sensor_mock/Drivers/STM32F0xx_HAL_Driver/Src/stm32f0xx_hal_gpio.c:437:0: style: The function 'HAL_GPIO_TogglePin' is never used. [unusedFunction]

^
Firmware/mock/nucleof030r8/ir_sensor_mock/Drivers/STM32F0xx_HAL_Driver/Src/stm32f0xx_hal.c:430:0: style: The function 'HAL_GetDEVID' is never used. [unusedFunction]

^
Firmware/mock/nucleof030r8/ir_sensor_mock/Drivers/STM32F0xx_HAL_Driver/Src/stm32f0xx_hal.c:412:0: style: The function 'HAL_GetHalVersion' is never used. [unusedFunction]

^
Firmware/mock/nucleof030r8/ir_sensor_mock/Drivers/STM32F0xx_HAL_Driver/Src/stm32f0xx_hal.c:421:0: style: The function 'HAL_GetREVID' is never used. [unusedFunction]

^
Firmware/mock/nucleof030r8/ir_sensor_mock/Drivers/STM32F0xx_HAL_Driver/Src/stm32f0xx_hal.c:343:0: style: The function 'HAL_GetTickFreq' is never used. [unusedFunction]

^
Firmware/mock/nucleof030r8/ir_sensor_mock/Drivers/STM32F0xx_HAL_Driver/Src/stm32f0xx_hal.c:301:0: style: The function 'HAL_GetTickPrio' is never used. [unusedFunction]

^
Firmware/mock/nucleof030r8/ir_sensor_mock/Drivers/STM32F0xx_HAL_Driver/Src/stm32f0xx_hal.c:439:0: style: The function 'HAL_GetUIDw0' is never used. [unusedFunction]

^
Firmware/mock/nucleof030r8/ir_sensor_mock/Drivers/STM32F0xx_HAL_Driver/Src/stm32f0xx_hal.c:448:0: style: The function 'HAL_GetUIDw1' is never used. [unusedFunction]

^
Firmware/mock/nucleof030r8/ir_sensor_mock/Drivers/STM32F0xx_HAL_Driver/Src/stm32f0xx_hal.c:457:0: style: The function 'HAL_GetUIDw2' is never used. [unusedFunction]

^
Firmware/mock/nucleof030r8/ir_sensor_mock/Drivers/STM32F0xx_HAL_Driver/Src/stm32f0xx_hal_uart.c:2902:0: style: The function 'HAL_HalfDuplex_EnableReceiver' is never used. [unusedFunction]

^
Firmware/mock/nucleof030r8/ir_sensor_mock/Drivers/STM32F0xx_HAL_Driver/Src/stm32f0xx_hal_uart.c:2879:0: style: The function 'HAL_HalfDuplex_EnableTransmitter' is never used. [unusedFunction]

^
Firmware/mock/nucleof030r8/ir_sensor_mock/Drivers/STM32F0xx_HAL_Driver/Src/stm32f0xx_hal_uart.c:380:0: style: The function 'HAL_HalfDuplex_Init' is never used. [unusedFunction]

^
Firmware/mock/nucleof030r8/ir_sensor_mock/Drivers/STM32F0xx_HAL_Driver/Src/stm32f0xx_hal_i2c_ex.c:96:0: style: The function 'HAL_I2CEx_ConfigAnalogFilter' is never used. [unusedFunction]

^
Firmware/mock/nucleof030r8/ir_sensor_mock/Drivers/STM32F0xx_HAL_Driver/Src/stm32f0xx_hal_i2c_ex.c:140:0: style: The function 'HAL_I2CEx_ConfigDigitalFilter' is never used. [unusedFunction]

^
Firmware/mock/nucleof030r8/ir_sensor_mock/Drivers/STM32F0xx_HAL_Driver/Src/stm32f0xx_hal_i2c_ex.c:337:0: style: The function 'HAL_I2CEx_DisableFastModePlus' is never used. [unusedFunction]

^
Firmware/mock/nucleof030r8/ir_sensor_mock/Drivers/STM32F0xx_HAL_Driver/Src/stm32f0xx_hal_i2c_ex.c:312:0: style: The function 'HAL_I2CEx_EnableFastModePlus' is never used. [unusedFunction]

^
Firmware/mock/nucleof030r8/ir_sensor_mock/Drivers/STM32F0xx_HAL_Driver/Src/stm32f0xx_hal_i2c.c:650:0: style: The function 'HAL_I2C_DeInit' is never used. [unusedFunction]

^
Firmware/mock/nucleof030r8/ir_sensor_mock/Drivers/STM32F0xx_HAL_Driver/Src/stm32f0xx_hal_i2c.c:4541:0: style: The function 'HAL_I2C_DisableListen_IT' is never used. [unusedFunction]

^
Firmware/mock/nucleof030r8/ir_sensor_mock/Drivers/STM32F0xx_HAL_Driver/Src/stm32f0xx_hal_i2c.c:4657:0: style: The function 'HAL_I2C_ER_IRQHandler' is never used. [unusedFunction]

^
Firmware/mock/nucleof030r8/ir_sensor_mock/Drivers/STM32F0xx_HAL_Driver/Src/stm32f0xx_hal_i2c.c:4638:0: style: The function 'HAL_I2C_EV_IRQHandler' is never used. [unusedFunction]

^
Firmware/mock/nucleof030r8/ir_sensor_mock/Drivers/STM32F0xx_HAL_Driver/Src/stm32f0xx_hal_i2c.c:4517:0: style: The function 'HAL_I2C_EnableListen_IT' is never used. [unusedFunction]

^
Firmware/mock/nucleof030r8/ir_sensor_mock/Drivers/STM32F0xx_HAL_Driver/Src/stm32f0xx_hal_i2c.c:4914:0: style: The function 'HAL_I2C_GetError' is never used. [unusedFunction]

^
Firmware/mock/nucleof030r8/ir_sensor_mock/Drivers/STM32F0xx_HAL_Driver/Src/stm32f0xx_hal_i2c.c:4903:0: style: The function 'HAL_I2C_GetMode' is never used. [unusedFunction]

^
Firmware/mock/nucleof030r8/ir_sensor_mock/Drivers/STM32F0xx_HAL_Driver/Src/stm32f0xx_hal_i2c.c:4891:0: style: The function 'HAL_I2C_GetState' is never used. [unusedFunction]

^
Firmware/mock/nucleof030r8/ir_sensor_mock/Drivers/STM32F0xx_HAL_Driver/Src/stm32f0xx_hal_i2c.c:535:0: style: The function 'HAL_I2C_Init' is never used. [unusedFunction]

^
Firmware/mock/nucleof030r8/ir_sensor_mock/Drivers/STM32F0xx_HAL_Driver/Src/stm32f0xx_hal_i2c.c:3263:0: style: The function 'HAL_I2C_IsDeviceReady' is never used. [unusedFunction]

^
Firmware/mock/nucleof030r8/ir_sensor_mock/Drivers/STM32F0xx_HAL_Driver/Src/stm32f0xx_hal_i2c.c:4574:0: style: The function 'HAL_I2C_Master_Abort_IT' is never used. [unusedFunction]

^
Firmware/mock/nucleof030r8/ir_sensor_mock/Drivers/STM32F0xx_HAL_Driver/Src/stm32f0xx_hal_i2c.c:1260:0: style: The function 'HAL_I2C_Master_Receive' is never used. [unusedFunction]

^
Firmware/mock/nucleof030r8/ir_sensor_mock/Drivers/STM32F0xx_HAL_Driver/Src/stm32f0xx_hal_i2c.c:2133:0: style: The function 'HAL_I2C_Master_Receive_DMA' is never used. [unusedFunction]

^
Firmware/mock/nucleof030r8/ir_sensor_mock/Drivers/STM32F0xx_HAL_Driver/Src/stm32f0xx_hal_i2c.c:1785:0: style: The function 'HAL_I2C_Master_Receive_IT' is never used. [unusedFunction]

^
Firmware/mock/nucleof030r8/ir_sensor_mock/Drivers/STM32F0xx_HAL_Driver/Src/stm32f0xx_hal_i2c.c:3787:0: style: The function 'HAL_I2C_Master_Seq_Receive_DMA' is never used. [unusedFunction]

^
Firmware/mock/nucleof030r8/ir_sensor_mock/Drivers/STM32F0xx_HAL_Driver/Src/stm32f0xx_hal_i2c.c:3700:0: style: The function 'HAL_I2C_Master_Seq_Receive_IT' is never used. [unusedFunction]

^
Firmware/mock/nucleof030r8/ir_sensor_mock/Drivers/STM32F0xx_HAL_Driver/Src/stm32f0xx_hal_i2c.c:3503:0: style: The function 'HAL_I2C_Master_Seq_Transmit_DMA' is never used. [unusedFunction]

^
Firmware/mock/nucleof030r8/ir_sensor_mock/Drivers/STM32F0xx_HAL_Driver/Src/stm32f0xx_hal_i2c.c:3389:0: style: The function 'HAL_I2C_Master_Seq_Transmit_IT' is never used. [unusedFunction]

^
Firmware/mock/nucleof030r8/ir_sensor_mock/Drivers/STM32F0xx_HAL_Driver/Src/stm32f0xx_hal_i2c.c:1119:0: style: The function 'HAL_I2C_Master_Transmit' is never used. [unusedFunction]

^
Firmware/mock/nucleof030r8/ir_sensor_mock/Drivers/STM32F0xx_HAL_Driver/Src/stm32f0xx_hal_i2c.c:1970:0: style: The function 'HAL_I2C_Master_Transmit_DMA' is never used. [unusedFunction]

^
Firmware/mock/nucleof030r8/ir_sensor_mock/Drivers/STM32F0xx_HAL_Driver/Src/stm32f0xx_hal_i2c.c:1695:0: style: The function 'HAL_I2C_Master_Transmit_IT' is never used. [unusedFunction]

^
Firmware/mock/nucleof030r8/ir_sensor_mock/Drivers/STM32F0xx_HAL_Driver/Src/stm32f0xx_hal_i2c.c:2660:0: style: The function 'HAL_I2C_Mem_Read' is never used. [unusedFunction]

^
Firmware/mock/nucleof030r8/ir_sensor_mock/Drivers/STM32F0xx_HAL_Driver/Src/stm32f0xx_hal_i2c.c:3118:0: style: The function 'HAL_I2C_Mem_Read_DMA' is never used. [unusedFunction]

^
Firmware/mock/nucleof030r8/ir_sensor_mock/Drivers/STM32F0xx_HAL_Driver/Src/stm32f0xx_hal_i2c.c:2885:0: style: The function 'HAL_I2C_Mem_Read_IT' is never used. [unusedFunction]

^
Firmware/mock/nucleof030r8/ir_sensor_mock/Drivers/STM32F0xx_HAL_Driver/Src/stm32f0xx_hal_i2c.c:2523:0: style: The function 'HAL_I2C_Mem_Write' is never used. [unusedFunction]

^
Firmware/mock/nucleof030r8/ir_sensor_mock/Drivers/STM32F0xx_HAL_Driver/Src/stm32f0xx_hal_i2c.c:2972:0: style: The function 'HAL_I2C_Mem_Write_DMA' is never used. [unusedFunction]

^
Firmware/mock/nucleof030r8/ir_sensor_mock/Drivers/STM32F0xx_HAL_Driver/Src/stm32f0xx_hal_i2c.c:2797:0: style: The function 'HAL_I2C_Mem_Write_IT' is never used. [unusedFunction]

^
Firmware/mock/nucleof030r8/ir_sensor_mock/Drivers/STM32F0xx_HAL_Driver/Src/stm32f0xx_hal_i2c.c:1565:0: style: The function 'HAL_I2C_Slave_Receive' is never used. [unusedFunction]

^
Firmware/mock/nucleof030r8/ir_sensor_mock/Drivers/STM32F0xx_HAL_Driver/Src/stm32f0xx_hal_i2c.c:2414:0: style: The function 'HAL_I2C_Slave_Receive_DMA' is never used. [unusedFunction]

^
Firmware/mock/nucleof030r8/ir_sensor_mock/Drivers/STM32F0xx_HAL_Driver/Src/stm32f0xx_hal_i2c.c:1918:0: style: The function 'HAL_I2C_Slave_Receive_IT' is never used. [unusedFunction]

^
Firmware/mock/nucleof030r8/ir_sensor_mock/Drivers/STM32F0xx_HAL_Driver/Src/stm32f0xx_hal_i2c.c:4337:0: style: The function 'HAL_I2C_Slave_Seq_Receive_DMA' is never used. [unusedFunction]

^
Firmware/mock/nucleof030r8/ir_sensor_mock/Drivers/STM32F0xx_HAL_Driver/Src/stm32f0xx_hal_i2c.c:4237:0: style: The function 'HAL_I2C_Slave_Seq_Receive_IT' is never used. [unusedFunction]

^
Firmware/mock/nucleof030r8/ir_sensor_mock/Drivers/STM32F0xx_HAL_Driver/Src/stm32f0xx_hal_i2c.c:4053:0: style: The function 'HAL_I2C_Slave_Seq_Transmit_DMA' is never used. [unusedFunction]

^
Firmware/mock/nucleof030r8/ir_sensor_mock/Drivers/STM32F0xx_HAL_Driver/Src/stm32f0xx_hal_i2c.c:3953:0: style: The function 'HAL_I2C_Slave_Seq_Transmit_IT' is never used. [unusedFunction]

^
Firmware/mock/nucleof030r8/ir_sensor_mock/Drivers/STM32F0xx_HAL_Driver/Src/stm32f0xx_hal_i2c.c:1378:0: style: The function 'HAL_I2C_Slave_Transmit' is never used. [unusedFunction]

^
Firmware/mock/nucleof030r8/ir_sensor_mock/Drivers/STM32F0xx_HAL_Driver/Src/stm32f0xx_hal_i2c.c:2278:0: style: The function 'HAL_I2C_Slave_Transmit_DMA' is never used. [unusedFunction]

^
Firmware/mock/nucleof030r8/ir_sensor_mock/Drivers/STM32F0xx_HAL_Driver/Src/stm32f0xx_hal_i2c.c:1854:0: style: The function 'HAL_I2C_Slave_Transmit_IT' is never used. [unusedFunction]

^
Firmware/mock/nucleof030r8/ir_sensor_mock/Drivers/STM32F0xx_HAL_Driver/Src/stm32f0xx_hal_i2s.c:1274:0: style: The function 'HAL_I2S_DMAPause' is never used. [unusedFunction]

^
Firmware/mock/nucleof030r8/ir_sensor_mock/Drivers/STM32F0xx_HAL_Driver/Src/stm32f0xx_hal_i2s.c:1306:0: style: The function 'HAL_I2S_DMAResume' is never used. [unusedFunction]

^
Firmware/mock/nucleof030r8/ir_sensor_mock/Drivers/STM32F0xx_HAL_Driver/Src/stm32f0xx_hal_i2s.c:1345:0: style: The function 'HAL_I2S_DMAStop' is never used. [unusedFunction]

^
Firmware/mock/nucleof030r8/ir_sensor_mock/Drivers/STM32F0xx_HAL_Driver/Src/stm32f0xx_hal_i2s.c:426:0: style: The function 'HAL_I2S_DeInit' is never used. [unusedFunction]

^
Firmware/mock/nucleof030r8/ir_sensor_mock/Drivers/STM32F0xx_HAL_Driver/Src/stm32f0xx_hal_i2s.c:1616:0: style: The function 'HAL_I2S_GetError' is never used. [unusedFunction]

^
Firmware/mock/nucleof030r8/ir_sensor_mock/Drivers/STM32F0xx_HAL_Driver/Src/stm32f0xx_hal_i2s.c:1605:0: style: The function 'HAL_I2S_GetState' is never used. [unusedFunction]

^
Firmware/mock/nucleof030r8/ir_sensor_mock/Drivers/STM32F0xx_HAL_Driver/Src/stm32f0xx_hal_i2s.c:1445:0: style: The function 'HAL_I2S_IRQHandler' is never used. [unusedFunction]

^
Firmware/mock/nucleof030r8/ir_sensor_mock/Drivers/STM32F0xx_HAL_Driver/Src/stm32f0xx_hal_i2s.c:261:0: style: The function 'HAL_I2S_Init' is never used. [unusedFunction]

^
Firmware/mock/nucleof030r8/ir_sensor_mock/Drivers/STM32F0xx_HAL_Driver/Src/stm32f0xx_hal_i2s.c:867:0: style: The function 'HAL_I2S_Receive' is never used. [unusedFunction]

^
Firmware/mock/nucleof030r8/ir_sensor_mock/Drivers/STM32F0xx_HAL_Driver/Src/stm32f0xx_hal_i2s.c:1185:0: style: The function 'HAL_I2S_Receive_DMA' is never used. [unusedFunction]

^
Firmware/mock/nucleof030r8/ir_sensor_mock/Drivers/STM32F0xx_HAL_Driver/Src/stm32f0xx_hal_i2s.c:1030:0: style: The function 'HAL_I2S_Receive_IT' is never used. [unusedFunction]

^
Firmware/mock/nucleof030r8/ir_sensor_mock/Drivers/STM32F0xx_HAL_Driver/Src/stm32f0xx_hal_i2s.c:749:0: style: The function 'HAL_I2S_Transmit' is never used. [unusedFunction]

^
Firmware/mock/nucleof030r8/ir_sensor_mock/Drivers/STM32F0xx_HAL_Driver/Src/stm32f0xx_hal_i2s.c:1094:0: style: The function 'HAL_I2S_Transmit_DMA' is never used. [unusedFunction]

^
Firmware/mock/nucleof030r8/ir_sensor_mock/Drivers/STM32F0xx_HAL_Driver/Src/stm32f0xx_hal_i2s.c:964:0: style: The function 'HAL_I2S_Transmit_IT' is never used. [unusedFunction]

^
Firmware/mock/nucleof030r8/ir_sensor_mock/Drivers/STM32F0xx_HAL_Driver/Src/stm32f0xx_hal_irda.c:1510:0: style: The function 'HAL_IRDA_Abort' is never used. [unusedFunction]

^
Firmware/mock/nucleof030r8/ir_sensor_mock/Drivers/STM32F0xx_HAL_Driver/Src/stm32f0xx_hal_irda.c:1648:0: style: The function 'HAL_IRDA_AbortReceive' is never used. [unusedFunction]

^
Firmware/mock/nucleof030r8/ir_sensor_mock/Drivers/STM32F0xx_HAL_Driver/Src/stm32f0xx_hal_irda.c:1916:0: style: The function 'HAL_IRDA_AbortReceive_IT' is never used. [unusedFunction]

^
Firmware/mock/nucleof030r8/ir_sensor_mock/Drivers/STM32F0xx_HAL_Driver/Src/stm32f0xx_hal_irda.c:1596:0: style: The function 'HAL_IRDA_AbortTransmit' is never used. [unusedFunction]

^
Firmware/mock/nucleof030r8/ir_sensor_mock/Drivers/STM32F0xx_HAL_Driver/Src/stm32f0xx_hal_irda.c:1838:0: style: The function 'HAL_IRDA_AbortTransmit_IT' is never used. [unusedFunction]
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
