AndyMWK/OpticalSensingSystem/Electrical/analog spice simulations/tia_sensor.asc

C1: cap; 10p
C2: cap; 0.1µ
C3: cap; 0.1µ
C4: cap; 0.1µ
C5: cap; 10p
I1: current; PULSE(40n 12u 0 10n 10n 0.05m 0.1m); AC 1
R1: res; 10k
R2: res; 47k
R3: res; 1k
R4: res; 3.3k
R5: res; 100k
R6: res; 10k
R7: res; 100k
U1: UniversalOpAmp2
U2: UniversalOpAmp2
U3: UniversalOpAmp2
V1: voltage; 3.3; AC 0
V2: voltage; 1.65
V3: voltage; 0.1
Named nets: 0
.tran 30m
.ac dec 100 10 1meg
