AndyMWK/OpticalSensingSystem/Firmware/device/target_platform/Core/Inc/main.h

#define LED_EN_Pin GPIO_PIN_2
#define LED_EN_GPIO_Port GPIOB
#define LED_PWM_Pin GPIO_PIN_8
#define LED_PWM_GPIO_Port GPIOA
#define Status_LED_Pin GPIO_PIN_6
#define Status_LED_GPIO_Port GPIOC
