AndyMWK/OpticalSensingSystem/Firmware/device/target_platform/BSP/Port/Src/stm32g0/bsp_i2c.c

#include "bsp_i2c.h"

hal_signal_t bsp_i2c_transmit_blocking(const bsp_i2c_ch ch, const uint16_t* tx_data,
                                       const size_t size)
{
}

hal_signal_t bsp_i2c_receive_blocking(const bsp_i2c_ch ch, uint16_t* rx_data, const size_t size)
{
}
